Avinash1286/pendent/docs/a04/software-contract.md

# AURA A04 software and hardware contract

Status: **active engineering specification with a host-tested Opus/NAND journal/recovery path, C archive → desktop transcription → local portal path, and emulator-tested Android source storage, playback and scripted foreground recovery**. Updated 2026-09-09. The current A03 firmware and its published binaries are unchanged. This document does not establish a working A04 device, a deployed consumer mobile service, qualified battery behavior, or launch readiness.

The target remains a premium circular pendant that reliably captures, preserves, understands, retrieves and uses the context its owner chooses to record. Offline use, optional continuous sessions, real-time assistance, memory, tasks, speech, and broad AI interoperability remain in scope. They are not removed because the initial source is incomplete. “Best in the category” needs measured comparative evidence; it cannot be established by a feature list or source review.

## Evidence and implementation boundary

AURA baseline inspected: `e9e968c425c558565dc555ccd9f39d2e4c6c0769`. Omi source inspected: [`f42089f53c8010dd971b3702ece05a231c9c0c66`](https://github.com/BasedHardware/omi/tree/f42089f53c8010dd971b3702ece05a231c9c0c66). The prior [firmware/hardware review](../research/omi-review.md) and [product review](../research/omi-product-review.md) contain the specific upstream code paths and known limitations.

Three terms distinguish evidence throughout this contract:

- **Implemented** means code exists in this repository. It does not imply physical or deployed validation.
- **Host-tested** means an identified local test exercised a bounded software behavior.
- **Required** means work remains and the feature cannot be advertised as shipped.

Current implementation: [protocol_v2.py](../../companion/src/aura_companion/protocol_v2.py) now implements experimental wire revision 3, a bounded streaming archive reader, strict manifests/packets/terminal metadata, stable capture identity, replay, durable receiving and finalization. It is called by the new desktop `import-capture` CLI. It does not change A03 Bluetooth/v1 firmware. Actual C-encoded Opus fixtures pass the local archive/receipt/decode/transcription path and real local portal ingestion. Structural Opus profile validation is separate from actual decoder validation. No Omi implementation was copied into the receiver; the cited source informed the reliability contracts.

Firmware progress: [firmware/a04](../../firmware/a04/README.md) now connects a monitored PDM driver and bounded reader FIFO to one recorder/storage owner, unmodified libopus 1.6.1, the shared revision-3 archive, packed NAND journal and W25N01GV SPI adapter. [The audio contract](../../firmware/a04/AUDIO.md) defines driver-health faults, exact block/final-watermark checks, warmup, privacy ordering and DMA quarantine. Real 16 kHz mono, 32 kbps, 10/20 ms fixtures pass host and independent FFmpeg decode with exact duration.

Three separate DK targets have different evidence. The [synthetic integration
probe's current ELF report](../../firmware/a04/verification/arm-resources.json)
binds its exact memory, symbols and configuration; its RAM NAND and inactive
peripheral reservations are not a physical capture or Bluetooth workload. The
[wired bench](../../firmware/a04/bench/README.md) connects actual peripheral
drivers and UART export with Bluetooth disabled, with its own
[ARM resource report](../../firmware/a04/bench/verification/arm-resources.json).
The new [radio DK application](../../firmware/a04/radio/README.md) implements
the GATT adapter, local pairing policy and [ASC1 owner proof](session-auth-v1.md).
Its source and verification scope are independent of both earlier targets.
None has been flashed or executed on physical hardware. Final A04 pin mapping,
physical scheduling/audio/NAND/radio qualification, signed OTA and populated-block
reclamation remain required; a DK build is not the complete product memory budget.

Storage verification: **25 command/integration groups and 19 journal groups pass**, alongside the existing Python archive tests. [The command transcript](../../firmware/a04/verification/w25n-command-tests.txt) covers the actual command core, including two combined driver/journal cases; [journal roundtrip evidence](../../firmware/a04/verification/journal-roundtrip.json) binds real Opus → modeled power cut/reopen → AUR3 → durable Python/SQLite import and restart → independent FFmpeg decode. A finalized recording preserves 120847 source samples; staged/torn tails preserve 116440, and a completed page with lost acknowledgement recovers 120600. Interrupted original duration remains unknown. These are host-model results, not electrical NAND or assembled-device qualification.

Ingress verification adds **10 recorder groups, 10 audio-adapter groups and 20 monitored-driver groups**. Five real recorder exports pass SQLite restart/replay and FFmpeg decode, including a source fault combined with failed terminal storage. Deterministic adapter interleavings cover cancellation during startup, publication at the privacy boundary, FIFO overflow, final-block loss and refusal to recycle live DMA storage. [Recorder evidence](../../firmware/a04/verification/recorder-roundtrip.json), [adapter evidence](../../firmware/a04/verification/audio-host.json) and [driver evidence](../../firmware/a04/drivers/tests/verification.json) describe their separate mocked boundaries. They do not establish physical concurrency, timing or electrical privacy behavior.

The current companion suite passes **131 tests**, including 36 release/outbox tests and the earlier 95 importer/receiver cases. Real C-generated archives and an actual local Whisper result passed through the Python uploader, Next.js and local Convex. [The companion verification](../../companion/VERIFICATION.md) and [portal report](../../portal/verification/a04-provenance-local.json) identify their separate checkpoints, commands, immutable fixtures and limits. Cases exercise corrupt/conflicting data, process exit before COMMIT, replay, temporary/read-only storage rejection, interrupted publication repair and source preservation. This establishes a local software path with synthetic audio, not a physical or mobile A04 capture path. The older [47-test v2 report](protocol-v2-verification.txt) is retained as historical evidence.

The [serialized storage owner](../../firmware/a04/STORAGE.md) now integrates
[RLS1 authentication](../../firmware/a04/RELEASE-AUTH.md) and the
[control-snapshot ledger](../../firmware/a04/CONTROL-LEDGER.md). It reserves
generation-derived capture identities and persists exact release grants before
invoking a privileged erase callback. Real C audio traverses the Python durable
receiver/outbox and returns to that controller in modeled-NAND tests. Consumer
enrollment, authenticated transport completion, the physical audio-erase
capability and electrical power-loss qualification remain outstanding. Ordinary
download never grants erasure or changes ownership.

The current phone foundation is a [native Android local library](../../mobile/android/README.md)
with exercised import, private storage, platform Opus playback and explicit
context sharing. A portable [transfer command owner and Kotlin wire codec](transfer-wire-v1.md)
now add exact-record resume, immutable replies, generation-bound capture
selection and stale callback rejection above the bounded journal cursor. Twelve
C groups and **30 combined Kotlin groups / 82,213 checks** pass, including actual
C-generated reply/fragment comparisons and **six incremental-validator groups /
49,471 checks**. The complete-file and incremental paths use one canonical
validator, with **19 complete C-generated archives**, exact Python ACK3/Ogg
comparisons and independent FFmpeg sample-count checks.

Android's [durable download store](../../mobile/android/DOWNLOADS.md) now commits
exact source records and resume metadata in one SQLite transaction, replays
saved prefixes after reopening, and preserves conflicting or corrupt evidence.
Its `CaptureStore.importDownload` bridge exports the original archive and exact
physical receipt through the existing platform-decoder and private-bundle
publication path. The [foreground recovery coordinator](../../mobile/android/RECOVERY.md)
(`CaptureRecovery`) now joins catalog selection, exact resume, bounded retries,
cancellation and decoded-library publication. `AndroidGattConnection` implements
the Android transport beneath it, including subscription readiness, bounded
fragment handling and stale-callback rejection.

The current development APK passed **29 Android runtime cases / 428 assertions**
on an API 34 emulator using the actual `c2.android.opus.decoder`. These cases
exercise real SQLite rollback/replay and library publication, plus the recovery
coordinator over scripted logical replies from fixed C fixtures. They do not
establish a physical pendant-to-phone link. Separate virtual GATT runs passed four cases / 33 assertions at each of MTU 23 and 517 using a Python Bumble fixture, not Zephyr firmware or authenticated enrollment. The
Activity still exposes file import. The separate
[Zephyr radio DK adapter](../../firmware/a04/radio/README.md) is now implemented;
Android still needs its ASC1 proof exchange, trusted owner-context custody,
secure consumer enrollment and UI integration before accessing that target.
Physical phone power-loss durability and real radio behavior need separate
qualification. [Android verification](../../mobile/android/VERIFICATION.md) records
the current execution scope.

## Complete feature and evidence backlog

| Product capability | Current evidence | A04 required behavior and owner | Evidence required before launch |
|---|---|---|---|
| Immediate deliberate capture | A04 monitored ingress, bounded FIFO and recorder lifecycle implemented and host-tested; DK integration cross-built; A03 gesture remains the prior baseline | Pendant captures without a phone; tactile start/stop, unmistakable recording/saved/error indication | Actual button-to-first-usable-audio latency, startup syllable retention, walking and under-clothing recordings |
| Controlled continuous capture | Required | User-enabled session mode with explicit physical start, continuous visible indicator, clear pause/stop, storage limits and consent guidance | Measured long session with no unexplained gaps; privacy switch stops capture independently of app/MCU state |
| Offline capture | A04 packed NAND journal and W25N01GV command driver implemented; modeled program/erase cuts, full-media retention and real Opus recovery tested; Cortex-M4 cross-built | Transfer only verified committed prefixes; preserve unacknowledged recordings; recover interrupted captures and expose unassociated material | Physical NAND power cuts at every journal state and during erase; decodable audio with explicit interrupted-tail metadata; qualify capacity/reclamation policy |
| Real-time transcription and assistance | Required | Phone streams only device-committed frames; live text marked provisional; durable archive later reconciles gaps | Phone termination, BLE backpressure and network loss preserve source; latency and consistency measured on supported phones |
| Opus compression | Real libopus 1.6.1 wrapper host-tested with decodable 10/20 ms fixtures; isolated nRF52840 probe cross-built | 16 kHz mono, 32 kbps initial experiment; compare low-delay and speech-optimized modes against PCM reference before profile freeze | CPU deadline, stack high-water, heap, power, frame error, quality and transcription comparison under concurrent storage/BLE load |
| Multi-microphone audio | A04 stereo driver/adapter, first/second/mean selection, peak/clipping counters and explicit fault propagation host-tested; no physical audio qualification | Two appropriately spaced microphones; calibrated mono mix/selection; retain original capture format metadata | Channel polarity, phase, clipping, wind/clothing noise and speech intelligibility in the actual sealed case |
| Bookmarks | Revision-3 C bookmarks survive verified local import, notes and real portal ingestion; A03 v1 still cannot export marks | Pendant gesture creates a sample-offset event; phone/portal jump to corresponding transcript/audio | Capture + bookmark + reconnect + export + playback round trip on real firmware |
| Device identity | v1 filenames lack authenticated device identity; revision-3 archives and portal retain independent device/capture keys, but these are sender declarations | Stable private device identity plus persistent random capture identity; owner binding and physical re-pair/reset flow | Two devices, resets, reboots and credential rotations never merge captures; unauthorized identity claims rejected |
| Reliable reconnection | A04 bounded cursor, ordered C command owner and Kotlin reply/fragment parsers host-tested; Android recovery/GATT client and separate Zephyr radio DK adapter implemented with distinct verification boundaries | Integrate Android ASC1 proof, trusted owner-context custody, secure enrollment and consumer lifecycle/UI; qualify actual device-to-phone recovery and background behavior | iOS and Android foreground/background/process-death matrices, permissions off/on, bonds, out-of-range return |
| Transfer retention and ACK | v1 explicit CRC-verified deletion; revision-3 journal receipts, C/Python agreement, durable desktop batch import and Android SQLite download rollback/replay tested; physical OPEN remains distinct from an exported interrupted seal | End-to-end application receipt after durable publication, separate from RAM acceptance/BLE completion; authenticated acknowledged/deleted-segment reclaim | Kill receiver before/after commit, lose ACK, replay and verify exactly one source; physical MCU reclamation power-cut tests |
| Searchable notes | Next.js/Convex owner-scoped notes/search and retained original source exercised locally; newly arrived unknown-time captures remain visible | Capture time confidence, editable title, transcript, summary, tags, filters and source playback | Deployed authenticated account flow; source remains accessible through edit/search/archive/delete |
| Transcription and languages | Real C archive → desktop Whisper → local portal tested with synthetic English speech | Local/offline option plus explicit cloud choice; language detection/selection and accessible corrections | Representative accents/languages/noise, measured quality/cost/latency; disclosure when speaker attribution is uncertain |
| Speaker attribution | Required | Phone/backend diarization with user-correctable labels; never infer a person's identity from a voice without an explicit enrollment feature | Overlap, short utterances, new speakers, corrections and source alignment tests |
| Summaries and provenance | Real local C archive → Whisper → portal import now retains immutable capture/source transcript, segments and method metadata | Every derived claim/action links to source capture, transcript revision and sample/time span; retain original and corrections | Regeneration/correction invalidates stale context while retaining inspectable lineage |
| Long-term memory | Chosen notes/profile currently supply context | Explicit review/promotion, edit/retract, provenance and supersession; canonical owner-scoped source truth | No unreviewed memory promotion; revoked/deleted/superseded evidence excluded on next retrieval |
| Tasks and reminders | Draft action strings only | Proposed actions with source evidence, accept/edit/dismiss lifecycle; opt-in reminders and integrations | Retry extraction cannot duplicate accepted tasks; no external side effect before a recorded user choice |
| AI chat interoperability | Reviewed Context Packs and read-only MCP implemented; local verification exists | Searchable owner-approved context for ChatGPT, Claude, Gemini, Grok and compatible clients; clipboard/file fallback remains usable | Actual supported-client connection matrix; current consent enforced; no claim every vendor accepts the same deep link/MCP method |
| Voice interaction/playback | Required | Phone/earbud microphone and speaker provide query/response/playback initially; pendant gesture may trigger the paired client | Clearly identify audio route; disconnected earbuds/phone cannot create an apparent pendant playback failure |
| Ecosystem/SDK | Python v1 companion and revision-3 archive importer implemented; real C/Python fixtures | Documented versioned device SDK, export formats and import contracts; adapters for integrations without a second source of truth | Contract fixtures across firmware/mobile/desktop; compatibility, migration and permission tests |
| Battery and storage UX | Raw voltage/free bytes available; charging/haptics disabled in release | Calibrated state, low-space/low-battery warnings, last successful save/sync, bounded maintenance and explicit fault handling | Full charge/discharge curves, worn/runtime profile, near-full capture and restart, charger/NTC faults |
| Secure update/recovery | Required; A03 is a single application slot | Signed boot, rollback-capable update, image compatibility, physical recovery and anti-rollback policy | Wrong board/key/image rejected; power cuts throughout update recover; key management documented |
| Privacy and account lifecycle | Hardware disconnect design, encrypted BLE, scoped portal tokens implemented | Hardware privacy proof, authenticated ownership, protected recordings, credential rotation/revocation, account recovery/export/deletion | Lost device/phone, stale cache, revoked token, deletion and restoration tests; no transcript/secret diagnostic leakage |
| Comfort and launch assets | A03 models/video exist; A04 redesign in progress | All PCB, case, firmware, website, video, specs and assembly guides refer to one verified A04 configuration | Render/model/part manifests match released PCB/BOM and physically measured first article; no A03 images labelled A04 |

Speech synthesis, LLM inference, semantic search and task execution belong on the phone/backend. Audio playback belongs on the paired phone/earbuds unless a separately reviewed speaker is added. The A04 hardware contract currently contains no speaker, display, camera, cellular or standalone Wi-Fi feature. None should be implied by a render, voice-over or generic comparison with Omi. Controlled continuous capture and near-real-time transfer remain pendant firmware requirements, not phone-only substitutes.

## Omi engineering practices to adopt

1. **One capture truth and one recovery owner.** Omi's [product principles](https://github.com/BasedHardware/omi/blob/f42089f53c8010dd971b3702ece05a231c9c0c66/PRODUCT.md) prioritize reliable capture/sync/retrieval. Its [transfer coordinator](https://github.com/BasedHardware/omi/blob/f42089f53c8010dd971b3702ece05a231c9c0c66/app/lib/services/wals/recording_transfer_coordinator.dart) is a useful reference for coalesced recovery. AURA's [foreground coordinator](../../mobile/android/RECOVERY.md) now serializes recovery and distinguishes received bytes, committed source, processing and a playable library item. Its Android GATT client and durable store still need the ASC1 exchange, trusted context/enrollment and consumer UI wiring to access the implemented radio DK service. Recording → preserved on pendant → preserved on phone → processing → note ready remains the full product lifecycle; connection alone proves none of these.
2. **Contracts plus real failure harnesses.** Preserve bounded regression cases: process exit before/after commit, full storage, dropped notifications, permissions, background restrictions, stale retrieval consent, and interrupted update. Generated checks must actually exercise the shared implementation and run locally/Vercel as applicable; no GitHub Actions.
3. **Compression selected by measurement.** Omi's [dev-kit codec](https://github.com/BasedHardware/omi/blob/f42089f53c8010dd971b3702ece05a231c9c0c66/omi/firmware/devkit/src/codec.c) reserves a 32,000-byte encoder stack and codec state. Its [configuration](https://github.com/BasedHardware/omi/blob/f42089f53c8010dd971b3702ece05a231c9c0c66/omi/firmware/devkit/src/config.h) selects 160-sample, 32 kbps frames. AURA should port the approach with resource accounting; do not copy a static codec-state size without confirming the selected build's `opus_encoder_get_size()`.
4. **Source-backed, revocable memory.** Omi's memory model and access gateway inspire provenance, revisions and fresh policy checks. AURA's canonical record is the owner-scoped capture/transcript and its reviewed derivatives. Search/vector indexes are derived candidates and must be rehydrated against current ownership/consent/revision/deletion.
5. **Repair known weak paths.** Omi's reviewed consumer transport can dequeue without storing in particular connected/unsubscribed or failed-send paths, and notification completion is weaker than durable phone storage. AURA must keep local-first capture and explicit host receipts. Do not adopt automatic loss of unsynced audio, credential-bearing diagnostic logs, or delete-before-rename file publication. See the [bounded source findings](../research/omi-review.md#firmware-findings-worth-learning-from).

These are designs derived from the reviewed source. Omi's documented “locked” contracts are not by themselves proof of deployed correctness, and its consumer nRF5340 firmware is not a compatible nRF52840 binary.

## Hardware decisions required before pin/placement freeze

| Interface/resource | A04 requirement | Reason and remaining verification |
|---|---|---|
| MCU/module | Retain Raytac MDBT50Q nRF52840 family unless root hardware review changes the exact part | A03 software baseline and Omi dev-kit codec experience are relevant; actual codec + security image fit remains required |
| PDM | Shared CLK and DIN for opposite-clock-edge stereo microphones; software rail enable; independent physical rail disconnect and sensed switch position | A03 uses two PDM edges on one DIN, not two independent DIN pins. Check new microphone startup, voltage, clock/rate and physical acoustic ports |
| Audio flash | W25N01GV packed journal and caller-configured Zephyr SPI adapter implemented and host-tested; physical bus/latency qualification required | Metadata-only mount avoids a full audio-volume scan; validate actual program/erase/read timing, serialized cache access and concurrent PDM/transfer scheduling. No populated reclamation exists yet |
| Update staging | Captured U10: **MX25R3235FM1IL0, 32 Mbit / 4 MiB serial NOR**, reserved for MCUboot secondary image/metadata | Current custom NAND driver is not assumed available in the bootloader. Confirm the selected NOR's driver, voltage, JEDEC/SFDP behavior and boot-time pins on the actual board |
| Flash map | MCUboot, primary image/trailer, persistent owner/identity/settings; secondary NOR/trailer; build-time slot limits | Choose MCUboot swap/update strategy and sector compatibility explicitly. Do not publish a partition map before building the real codec/security image |
| Shared I²C | Gauge, haptic and selected charger; distinct compatible addresses/levels and pull-up budget | Check exact chosen charger interface and reset defaults; no firmware-only reliance for battery thermal protection |
| Control GPIO | Capture, physical privacy position, microphone enable, default-inactive charging and haptic enable; optional charger fault/IRQ if selected | Boot, watchdog reset, transport command or crashed phone cannot enable capture against physical privacy or unsafe charging |
| Indication | Hardware-coupled recording/privacy indication plus firmware status; tactile haptic if qualified | Visible recording indication cannot depend solely on a responsive app; haptic meaning must not imply data committed before it is |
| Service/test | Accessible SWDIO/SWCLK/RESET/GND/VTref and testable rails/storage buses | Factory identity/provisioning, signed recovery, measured power, programming and first-article fault isolation |
| RF/clock | Antenna all-layer/case/metal keepout; selected clock accuracy and calibration | Phone compatibility, BLE interval/PHY choices, body/chain effects and idle power must be measured |

The [MCUboot design](https://docs.mcuboot.com/design.html) documents distinct bootloader/primary/secondary flash areas and strategy-dependent sector/trailer requirements. This requires a real A04 flash map and power-interruption test, not just adding “OTA” to firmware configuration. Inference for AURA: a known NOR driver is a lower-integration-risk staging path than introducing the custom NAND journal driver into the bootloader. It is still unqualified until built and tested.

No pin numbers are assigned here: the fresh KiCad MCP schematic is the authority. Export its mapping into the A04 devicetree, production test plan and wiring guide, then run a cross-check against that exact schematic/BOM revision. Do not reuse A03 GPIO assignments merely because they compile.

## Experimental archive revision 3 and the real local import path

The original experimental v2 format lacked immutable Opus profile/pre-skip and complete end-trim semantics. It has been superseded by **binary wire revision 3** (`AUR3` manifest, `AFR3` packets, `ASE3` terminal metadata, `ACK3` receipts). The Python module remains named `protocol_v2.py` for development continuity, but old v2 bytes are deliberately rejected rather than reinterpreted. A03 Bluetooth/v1 bytes and firmware remain unchanged. The portal's `capture.version: 2` describes its JSON metadata contract, not this binary revision.

The authoritative field layouts and C/Python behavior are documented in [the archive specification](../../firmware/a04/ARCHIVE.md). Immutable device/capture identities, the negotiated codec profile, packet sequence and sample offsets, CRC-protected records and a SHA-256 chain lead to terminal metadata that binds the true source duration, Opus pre-skip/end-trim and finalized/interrupted status. A terminal receipt includes that metadata in its digest. Hashes and sender-declared device IDs are not physical-device authentication.

The journal uses separately named staged codec/archive initializers: callback success means bounded RAM acceptance, and a staged writer cannot issue a receipt. It replays each accepted record independently of the producer callback, then advances its committed snapshot only after completed programming, full ECC-readable exact page readback and CRC validation. Records share 2048-byte pages and never cross a page boundary. Flushes occur on capacity, first audio, terminal seal, explicit request and the serviced 400 ms deadline; the scheduler must initialize and service that monotonic clock while recording and paused. A failed or uncertain page is never reprogrammed. Program-failure status cannot be hidden by matching bytes; unresolved pages are blocked from read-based promotion for that boot.

Mount reads bounded header/checkpoint metadata: an empty 1024-block host-model mount reads **524288 bytes in 2048 metadata reads, with zero payload reads**, excluding the adapter's separate factory-marker/LUT inventory. Old captures remain unverified until a full payload scan before receipt/export. Recovery inspects later pages, continuation declarations and checkpoints after a gap; contradictory later material is corruption. Identifiable damaged continuations invalidate the capture; unidentifiable material remains quarantined and counted. An exported interrupted seal does not become a physical local terminal receipt or deletion authority. A new boot uses a fresh capture ID/block rather than restarting an Opus encoder inside an old capture.

The bounded port supports **128 captures**, never erases populated or unidentifiable source blocks, and stops recording when full while retaining verified receipts/export for synchronization. Closing a minimal capture strands 58 unused data pages in its final block; across 128 such captures those tails total **14.5 MiB**, and the catalog fills after consuming 16 MiB of blocks even if other blocks remain. There is no populated reclamation, catalog eviction, authenticated persistent host-ACK reclamation, or persistent failed-page retirement ledger. Blank candidates require complete readable-FF checks and a successful fresh erase. Failure guards are volatile; cold recovery validates old bytes but never resumes a pre-boot used block. Physical qualification, sustainable reclamation/rotation and unassociated-material recovery remain full-product work, as quantified in [the journal specification](../../firmware/a04/NAND-JOURNAL.md).

Real C-generated Opus archives now enter `aura import-capture`: the companion takes a bounded local snapshot, verifies the full archive, commits packets/terminal metadata to SQLite, exports Ogg Opus and exact-duration PCM WAV, and publishes source metadata last. A terminal-revision digest names each bundle. Interrupted recovery requires the explicit `--allow-interrupted` flag; it retains only complete verified records, marks the original total duration unknown, and labels bookmarks whose corresponding audio was lost in the encoder tail. A later completed source is preserved as a separate revision instead of overwriting that recovered prefix.

Desktop batch file import validates and commits the complete capture in one SQLite transaction, returning its receipt only after commit. This avoids the old per-packet quadratic scans for this import path. The Python live per-packet receive API still revalidates the complete prefix and is not a production-throughput claim. Durability depends on the operating system, filesystem and storage honoring flushes; desktop transaction tests do not prove physical NAND persistence, phone power loss, BLE transport or background mobile service. The separate journal/command tests establish the bounded modeled storage behavior described above.

The separate [Android download path](../../mobile/android/DOWNLOADS.md) incrementally
validates chunks of at most 256 bytes, retaining only an incomplete record of at
most 1301 bytes. Exact complete records and their receipt/offset commit together;
partial bytes stay in RAM. A storage or validation failure faults the session,
and reopening revalidates the saved rows once before resuming. A seal alone does
not complete a download: all selected bytes must be committed and the exact
selected FINISH identity must match. The completed source can then enter the
existing playback library through actual Opus decoding. The foreground coordinator
now drives this path with exact source pinning across reconnects, an explicit EOF
READ before FINISH and bounded retry/cancellation. Android emulator tests exercise
these boundaries with scripted connections. The Android GATT client and separate
radio DK adapter are implemented; the Android ASC1 exchange, trusted owner-context
custody, secure enrollment, consumer UI integration, physical durability and
background lifecycle qualification remain separate work. See the
[recovery contract](../../mobile/android/RECOVERY.md).

A committed bundle is reused by checking its preserved archive, receipt, WAV hash/dimensions and source metadata; it is not decoded again just because a newer decoder is installed. New exports record PyAV and codec-library versions. Conflicting files are preserved and rejected. Missing final metadata after interrupted publication can be reconstructed by a verified reimport. A cooperative OS lock serializes imports into one output directory. Raw audio/archive/receipt files remain local unless the owner separately copies them.

Optional local transcription preserves exact source identity, capture-time confidence, retained sample duration, bookmarks, model/method/version, transcript segments and a hash of the transcript's exact UTF-8 bytes. A differing previous note JSON is archived before the current note view is replaced. Explicit portal upload preserves these fields. The portal authenticates ownership through the ingestion credential, deduplicates that owner's device/capture identity across token rotation, and rejects conflicting immutable source replay; it does not silently merge legacy token-prefixed captures or automatically promote a later final revision over an uploaded interrupted prefix.

**A receipt is not a DELETE command.** No radio command, device deletion, automatic upload, background retry or storage reclamation is performed by file import. Authenticated pairing, confidential storage, physical PDM input and NAND qualification, persistent ACK/reclamation, device BLE integration/credits and read-while-capture scheduling, qualified hardware-to-phone recovery, source-revision promotion and signed OTA remain required. The full objective is unchanged.

## Memory, tasks and interoperability contract

The existing Convex schema stores notes with owner, title, transcript, summary, actions, tags, recorded time and context consent. A04 needs stable `captureKey`, immutable source revision, time confidence, transcript segments, model/method/version, correction history and source spans on every derived suggestion. New capture ingestion separates authentication tokens from stable owner-scoped device/capture identity. Legacy v1 token-prefixed records remain unchanged and are not automatically merged because they lack sufficient source identity. Immutable original transcript and source metadata survive edits/retries; conflicting source revisions require an explicit future review/promotion path. See [portal provenance](portal-provenance.md) for validation, compatibility and tested limits.

A retrieval request must hydrate candidates from current authoritative records and enforce owner, consent, archive/deletion and revision state before returning text. Context search includes explicit pagination/truncation information and source links; “20 recent notes” must not masquerade as complete archive retrieval. A model reads captured text as data, never as authorization to call tools or change privacy. Accepted tasks have a user decision record and source span; extraction retries do not create another accepted task. Retraction prevents future retrieval, but cannot recall a context pack already pasted into a third-party chat.

External interfaces remain layered: clipboard/Markdown/JSON export for any chat, authenticated read-only MCP where the client supports it, and explicit user-authorized adapters for richer integrations. A “connect to ChatGPT/Claude/Gemini/Grok” button needs a tested supported method and honest fallback; an unverified vendor deep link is not interoperability. Credentials stay in secure client/transport configuration, not model-visible tool arguments or diagnostics. No upstream backend or production account is required to use AURA's independent Convex service.

## Release gates and execution order

1. **Hardware contract:** exact KiCad MCP schematic/BOM/net/pin mapping, charger/dock/NTC choices, module/antenna keepout, serial NOR staging and assembly tolerances agreed by actual artifacts. Root owns these files.
2. **A04 firmware bring-up:** new board target from the schematic, rails/storage/PDM/controls, truthful status, flash partitions, safe defaults and actual ARM build. A03 artifacts retain their identity. No charging or haptic qualification flag is enabled from a software test alone.
3. **Codec, archive and storage:** shared revision-3 C/Python source, real Opus fixtures, packed NAND journal, W25N01GV command/SPI adapter and modeled recovery tests now exist and cross-build together. Remaining work includes physical timing/stack and electrical power cuts, representative listening/transcription comparisons, sustainable reclamation/capture rotation, recovery of unassociated material and concurrent PDM/capture/transfer integration.
4. **Mobile loop:** durable Android source/receipt storage, exact prefix replay and decoded-library handoff are implemented and emulator-tested. The foreground recovery coordinator, Android GATT client and separate radio DK adapter have distinct source/test evidence. Integrate Android ASC1 proof, trusted owner-context custody, secure consumer enrollment and lifecycle/UI; verify the real microphone/NAND-to-phone path, then qualify actual OS background behavior and any acknowledged outbox. Timestamped transcript and bookmark navigation remain required. A timer is not proof of background execution. [Current recovery scope](../../mobile/android/RECOVERY.md), [execution evidence](../../mobile/android/VERIFICATION.md).
5. **Portal/AI:** deployed Convex auth/recovery/deletion, immutable provenance, stable ingestion identity across token rotation, searchable current-consent context, reviewed tasks and tested client adapters. Required account/terms steps cannot be replaced by a local mock.
6. **Security and updates:** authenticated ownership, protected storage, production signing/debug policy, rollback and update fault tests; export/delete/revoke/lost-device flows.
7. **Physical qualification:** assembled A04 plus exact printed case/dock, real battery/charge thermal faults, power/audio/RF/comfort/runtime testing and documented first wear. CAD topology and zero ERC/DRC do not prove these.
8. **Launch consistency:** all downloadable fabrication/print/firmware files, website/portal/video/readme, license notices, versions and documented claims match that qualified unit. Publish all work on GitHub and deploy website services with Vercel. No GitHub Actions.

The acceptance artifact is a requirement-to-evidence matrix with links to actual outputs, exact revision/hash, fixture or physical configuration, result and remaining limits. A green host test, generated manifest or product render must never stand in for an unperformed physical, mobile, cloud or security gate. The active goal remains unfinished until the full requested end state is true and verified.
