Avinash1286/pendent/firmware/a04/W25N-ADAPTER.md

# W25N01GV command driver and Zephyr adapter

Status: **experimental A04 implementation; command-model tested and Cortex-M4 cross-built; no physical flash, SPI, timing or power-fault qualification**. The real command core is separate from the journal's sparse NAND model. A03 firmware and released images are unchanged. The final resource and source-hash reports must match the exact code revision being inspected.

The portable [driver](src/aura_w25n01gv.c) uses an injected synchronous command transport and clock. [The Zephyr wrapper](src/aura_w25n01gv_zephyr.c) supplies actual `spi_transceive_dt`/`spi_write_dt`, a monotonic clock and sleeping. A mutex covers each complete NAND read/program/erase/bad-query operation, including cache load and readback. Serializing individual SPI transfers alone would allow another caller to replace the chip's shared page cache.

The caller supplies a reviewed `spi_dt_spec` to `aura_w25n01gv_zephyr_init`; no GPIO or devicetree node is selected implicitly. Accepted operation is standard full-duplex, 8-bit MSB-first, active-low CS, mode0 or3, up to32 MHz. Hold-CS, locked-CS, LSB, slave, half-duplex and extended line modes are rejected. Actual supported board speed remains a signal-integrity measurement, not a result of this argument check. The wrapper is for a storage thread, never an ISR. Its SPI transport must have a bounded hardware timeout; the ready polling bound cannot interrupt a driver stalled inside a synchronous transfer.

## Initialization and ownership

Initialize only at cold startup after power is stable and no live operation is running: initialization issues RESET. It must not be used as a retry while another task is recording. The driver checks JEDEC identity, buffer/ECC configuration and volatile protection readback. Unexpected OTP/protection-lock state is refused; the driver never issues OTP programming or the BBM mutation command.

Before permitting any array write, initialization reads the20-entry BBM LUT and reserves both addresses of each enabled valid or invalidated link. Malformed/unsupported entries fail initialization. It checks main byte0 and spare bytes2048/2049 on both reserved marker pages of each remaining block, with ECC disabled. Read failures leave the adapter unavailable. It then restores buffer mode/internal ECC and verifies volatile unprotection. This preserves the manufacturer markers and avoids aliasing an existing remapped address. The second marker page is an additional conservative reservation.

Command selection, status bits, dummy clocks, factory markers and sequential programming follow the [Winbond Rev.R manufacturer datasheet](https://www.mouser.com/datasheet/2/949/Winbond_Electronics_09072023_W25N01GV_Rev_R_070323-3313374.pdf), especially sections7.2–7.3,8.2 and10. The implementation deliberately supports less than the chip's permitted partial-program behavior.

## Irreversible-operation boundaries

- **Read:** wait for ready, load one page, inspect its ECC status, then read the requested main-area bytes. Corrected data has a distinct result and telemetry; uncorrectable data is refused. Array addresses and columns are bounded.
- **Program:** only pages2–63 of a block successfully erased by this adapter in the current boot are eligible. Pages must increase and each attempt consumes permission. All-FF input is rejected because A04 pages contain a header and pre-existing FF cannot prove that an uncertain program occurred. The driver checks an ECC-clean FF destination, WEL, load/execute completion, P-FAIL, cleared WEL and full-page ECC/readback. A lost execute response can resolve successfully only through those checks, without a second execute. An unresolved completion returns `AURA_NAND_UNCERTAIN`; a failed or uncertain page is also blocked from read-based promotion through this instance, while its prior pages remain readable. Matching bytes with P-FAIL set never count as a successful commit.
- **Ordinary erase:** only a factory/LUT-eligible block outside the reserved CONTROL pair whose entire main area is readable, ECC-clean and FF can be erased. Any populated, corrected, unreadable or hidden later page prevents the command. E-FAIL, cleared WEL and all 64 post-erase pages are checked before program permission is granted. A lost command acknowledgement remains uncertain: pre-existing FF alone cannot prove that a fresh erase actually happened. Erase faults retire write permission for the current instance. This interface has **no populated audio-block reclamation**; it cannot be used as an implicit delete or garbage collector.

No prior-boot write permission survives initialization. A failed operation disarms writing without mislabelling the block as factory bad, allowing the journal to preserve and investigate its existing source. The journal remains responsible for capture identity, page CRC/hash validation, its committed watermark and recovery semantics. The adapter cannot itself issue an application receipt.

The per-block failure guard is **volatile**. Persistent runtime bad-block retirement and verified migration have not been implemented. A later cold-recovery session may inspect a previously failed page through full source/ECC validation; that does not restore permission to append to an old capture or prove permanent reliability of that block. This limitation must be resolved before dependable daily wear.

## Explicit CONTROL pair

The command core now exposes a separate `aura_control_io` for exactly two explicitly reserved blocks. After successful cold initialization, call `aura_w25n01gv_configure_control(device, first, second)` before the first ordinary NAND callback, then obtain `aura_w25n01gv_control_io(device)`. The Zephyr equivalents are `aura_w25n01gv_zephyr_configure_control` and `aura_w25n01gv_zephyr_control_io`; configuration and all callbacks use the same complete-operation mutex as ordinary NAND access. Neither API selects blocks, discovers a layout, provisions a ledger, nor issues an erase during configuration.

The caller must supply a trusted, fixed layout and keep the device/configuration private to its serialized storage owner. Both blocks must be distinct, in range and factory-marker/LUT eligible. The ordered pair is immutable until the next deliberate cold initialization; repeating that exact pair is a no-op. Without a configured pair, the control view reports zero blocks and its callbacks deny access. Any valid ordinary callback locks an unconfigured layout against later reservation, including read and bad-block queries, so a mounted journal cannot have its inventory silently reclassified. Reapply the trusted pair before journal mount on every cold startup.

Ordinary `aura_nand_io` reports the reserved pair as excluded and refuses its read, program and erase requests, including through handles obtained before configuration. The dedicated control view reports every other block unavailable and independently rejects reads, programs and privileged erases outside the current pair. Its `nand.erase` pointer is null. The separate `erase_control` callback may erase a populated **CONTROL** slot; it does not authorize any populated audio-block erase. The ledger is responsible for selecting the inactive slot and verifying snapshot linkage. Possessing this callback is a software privilege: there is no defense against arbitrary mutation of the private driver object or direct raw-bus access.

Control erase uses the same ready polling, write-enable check, execute/status result, cleared WEL, E-FAIL handling and full 64-page ECC-clean FF readback as ordinary erase. It skips only the ordinary precondition that all source main bytes already be FF, and only after its own pair check. A reported failure or lost erase acknowledgement never becomes success merely because the block reads FF. No failed-page guard is cleared by this path; a retired block remains unwritable until separately initiated cold recovery. A successful fresh erase permits only increasing, once-attempted pages 2–63. Both interfaces retain the same full-page program readback, P-FAIL and uncertain-page protection. Neither writes factory-marker pages, spare data, OTP or the BBM LUT. Reserved factory-good marker bytes remain FF through control erase.

The command tests combine the actual control ledger and journal with this driver: provision and cycle control snapshots through generations 1–4, recover after cold initialization and explicit reconfiguration, and verify an ordinary capture's unchanged receipt. They also reject a missing/invalid/excluded pair, late or changed configuration, wrong-target callbacks, eight erase failure modes, and a P-FAIL header whose bytes match the requested data. These are source and command-model checks, with no physical commands or flash qualification.

Ready polling has a30 ms monotonic deadline and301-poll fallback. These are software bounds around a responding transport, not measured bus or startup latency. Initialization reads only marker locations; the journal separately reads its bounded metadata inventory. Neither should be described as a full128 MiB boot scan.

## Verification and limits

[The command-level host test](tests/host_w25n01gv.c) compiles the **production command core**, without an alternate implementation, against a chip command model. Its 25 groups check transaction boundaries, headers/dummy clocks, write-enable ordering, reserved-page and address rules, and reject unexpected opcodes. Cases cover factory markers, LUT aliases and invalid entries, wrong identity/lock/configuration, cache/readback, restart/no-resume, ECC statuses, lost completion, program/erase faults, silently ignored erase, non-FF tail pages, refused WEL, busy timeout and stalled clock. Two original groups combine the actual driver and journal to check staging/receipts/cold verification and prevent a P-FAIL page with matching bytes from advancing the committed snapshot; five additional groups cover the separate CONTROL pair described above. Those integration packets are protocol fixtures; the separate real-Opus journal roundtrip establishes decode behavior. The command model implements neither physical ECC encoding nor analogue corruption probabilities.

Run the integrated A04 host build:

```powershell
./firmware/a04/scripts/build.ps1 -Mode host
```

The integrated raw result is retained in [command-test evidence](verification/w25n-command-tests.txt). The empty-chip model startup performs 12306 command transactions, receives 12383 bytes and loads 2048 marker pages; it does not scan audio. The CONTROL pair adds two block indices and lifecycle flags within existing host padding: the standalone command test still reports a 4432-byte portable context. Exact target sizes and linked wrapper coverage require the corresponding current target build report. These are measured software/model counts, not physical startup timing. The probe must not initialize a physical chip until reviewed A04 pins and hardware exist.

Remaining qualification: actual CS/DMA and shared-bus behavior, measured ready/startup/service latency, power interruption during every irreversible phase, real ECC/bad-block behavior, thread scheduling under PDM/BLE load, energy usage, and full capture→durable NAND→verified receiver recovery. No GPIO execution, physical flash test or wearable approval follows from these host checks.
