Avinash1286/pendent/film/aura-launch/frame.md

---
name: AURA — Capture the context of your life.
version: 5
format: 1920x1080
colors:
  graphite: "#101112"
  surface: "#1D1E20"
  ivory: "#F4F1EB"
  secondary: "#B7B4AF"
  apricot: "#EEB891"
typography:
  display: "Manrope"
  body: "Manrope"
  displayWeight: 500
  bodyWeight: 400
---

The A03 capsule is the center of the story: glossy black full-face record paddle, satin silver frame, and fine necklace chain. Use actual Blender geometry, broad photographic lighting, and breathing room. Start with the low-angle profile before revealing the name. Warm ivory headline text stays crisp against graphite; apricot is reserved for a recording moment and a short line. Never use multicolor gradients, fake review stars, invented benchmarks, or crowded feature cards.

The emotional arc is life in motion → what matters → thoughts and moments → personal choice → new possibilities. The exact primary line is “Capture the context of your life.” Keep manual capture and physical privacy clear. Context comes from the moments a person chooses to keep.

At 1920×1080 use 77–158 px display type, 28–43 px supporting type, and 20–23 px labels. Keep type within a 120 px safe area. Product photographs can run past the image boundary intentionally while text remains entirely legible. The closing chain fades before reaching the tagline.

Motion is slow, deliberate, and finite: 2.5–5.5% photographic reframes with continuous movement. Entrance type resolves with cubic ease-out. The final lockup is fully resolved by 39.35 seconds and holds until 44 seconds. No endless ambient loops, bounce, or gratuitous transitions.

The inside view uses actual geometry, opaque materials, an angled camera, broad reflected light, and a graphite stage. Keep the board and cell distinct. Separate five groups along the object's thickness axis, pause, then return to exact assembled positions. Use one small headline and a development qualifier; no floating labels, ghosted shells, or invented parts.

The headline tracking reveal adapts the installed Hyperframes `tracking-in` primitive. The final wordmark settlement and line drawing adapt the installed `titlecard-lockup` primitive. Composition otherwise follows the project's own visual hierarchy.
