Avinash1286/pendent/film/aura-launch/STORYBOARD.md

# AURA — Capture the context of your life.

44 seconds · 1920 × 1080 · 30 fps · original stereo score · no narration

Life keeps moving; some thoughts and moments deserve a place to stay. The film introduces AURA as a way to keep what matters, then connects personal control with the possibilities of useful context. The existing A03 product photography, quiet score, measured motion, and long final beauty hold support the more personal story.

| Time | Picture and movement | Message |
| --- | --- | --- |
| 0–5.8 | The actual A03 profile emerges gradually with a 2.5% optical reframe. The first two seconds belong to the object. | “Life moves.” at 2.1 s. |
| 5.2–11.2 | Dissolve to the complete capsule and chain. A 5.5% constant-speed withdrawal gives the object breathing room. | “Introducing AURA.” Then “Keep what matters.” A small development-concept label establishes the stage. |
| 10.6–16.4 | A precise cut reveals the full glossy recording face, followed by a 4.5% push. A short finite waveform illustrates the intended feedback. | “The thought. The moment.” Supporting copy: “Press to capture · Intended interaction.” |
| 15.8–21.6 | Actual microphone-disconnect macro. A small lateral move describes the satin frame and physical control. | “On your terms.” “Physical mic disconnect.” “You decide when to capture.” |
| 21–29.6 | The real A03 GLB opens along its thickness axis into five opaque groups: face/controls, frame, board, battery, and back. A gentle camera orbit exposes the board and cell. The separated view holds before the layers return to their exact original positions. | “Considered. Inside and out.” Small label: “Exploded design study · Reference components shown.” |
| 29–35.4 | One ivory notes surface. A morning walk becomes an idea and a next step, in an explicitly illustrative interface. | “More context. New possibilities.” “Capture offline. Organize with your phone.” |
| 34.8–44 | Dissolve to the complete object and brand. The product settles by 38.4 s; all copy resolves by 39.35 s. The finished picture holds to the last frame. | “AURA. Capture the context of your life.” Supporting copy: “Capture starts with you.” The engineering-validation qualifier remains visible. |

The seven shots combine the final A03 Blender photographs with the actual exported GLB. Hero aliases have identical source pixels; separate filenames keep Hyperframes media discovery unambiguous. One paused GSAP timeline owns the edit. The Three.js layer responds to timeline updates and Hyperframes seek events, reconstructing camera and component positions directly from the requested time. It does not use wall-clock time, free-running loops, input, or remote assets.

Assembly poses: assembled at 21.7 s; open by 23.75 s; angled interior hold until 26.15 s; reassembled by 28.1 s; hold to the transition. The same part-name rules and separation factors as the website's assembly explorer are used. The animation is an exploded design study, not a manufacturing procedure or proof of production tolerances.

The original ambient score uses locally synthesized harmonics, sparse bells, and controlled delay. Its harmonic sequence was extended to 44 seconds for the new inside view; the opening and sonic character remain. Picture and music resolve together, without narration or licensed stock footage. The film makes no numerical thickness, capacity, battery-life, reliability, stock, or shipping claims.

The primary line refers to moments the user chooses to capture. Manual capture and the physical mic disconnect remain explicit; the film does not imply always-on recording, complete life capture, or perfect memory.

The complete original A01 film is preserved in `../archive/A01`. The unreleased A02 source draft is preserved in `../archive/A02-draft`; no A02 video was rendered.

The preceding A03 film and source are preserved in Git commit `1569645a292b8bd147bb208ccc96d9fe8081adc5`. This positioning revision creates no additional media archive.
