Avinash1286/pendent/docs/research/aura-first-wearable.md

# AURA: the route from Omi's lessons to a first wearable

**The next meaningful milestone is a real spoken note recorded on hardware, recovered after a disconnect, and played back from a durable local copy.** AURA's software foundation has progressed; its custom PCB and powered enclosure are not ready to fabricate and wear.

This plan reviews [Omi at `f42089f53c8010dd971b3702ece05a231c9c0c66`](https://github.com/BasedHardware/omi/tree/f42089f53c8010dd971b3702ece05a231c9c0c66), with AURA's published `0f22273` checkpoint and subsequent storage-controller work distinguished below. It is a source/design review, with no upstream application execution, physical board fabrication or wear trial. The detailed [code review](omi-review.md), [mobile/product review](omi-product-review.md) and [hardware review](omi-hardware-review.md) retain the underlying evidence.

## What to take from Omi

| Lesson from the pinned source | AURA decision and current state |
|---|---|
| Omi prioritizes capture, preservation and retrieval, with reliability ahead of visual novelty. [Product principles](https://github.com/BasedHardware/omi/blob/f42089f53c8010dd971b3702ece05a231c9c0c66/PRODUCT.md#L8-L24), [design guidance](https://github.com/BasedHardware/omi/blob/f42089f53c8010dd971b3702ece05a231c9c0c66/.impeccable.md) | Keep one deliberate capture gesture, visible microphone state and physical privacy control. A premium finish should support a dependable daily ritual. These are A04 requirements; actual control force, indication and comfort are unmeasured. |
| The phone distinguishes download, internet wait, upload and processing, and has a coordinator for recovery. [Sync model](https://github.com/BasedHardware/omi/blob/f42089f53c8010dd971b3702ece05a231c9c0c66/app/lib/models/sync_state.dart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), [coordinator](https://github.com/BasedHardware/omi/blob/f42089f53c8010dd971b3702ece05a231c9c0c66/app/lib/services/wals/recording_transfer_coordinator.dart) | AURA now implements one foreground recovery owner, durable phone storage and an Android GATT client. Received bytes, preserved source, processing and playable audio have distinct states. The matching radio DK adapter now exists; secure enrollment, the Android ASC1 proof exchange, consumer UI integration and a real hardware-to-phone recovery trial remain. |
| The dev kit uses Opus, while consumer firmware targets a different MCU. [Dev-kit configuration](https://github.com/BasedHardware/omi/blob/f42089f53c8010dd971b3702ece05a231c9c0c66/omi/firmware/devkit/src/config.h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), [consumer target](https://github.com/BasedHardware/omi/blob/f42089f53c8010dd971b3702ece05a231c9c0c66/omi/firmware/omi/README.md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) | Retain AURA's measured-memory Opus port and nRF52840 direction. Run the complete recording workload on hardware next. Omi's nRF5340 consumer binary and XIAO dev-kit wiring are not AURA firmware or pin maps. |
| Selected consumer paths dequeue audio without successful delivery/storage; storage advancement uses notification completion. [Pusher](https://github.com/BasedHardware/omi/blob/f42089f53c8010dd971b3702ece05a231c9c0c66/omi/firmware/omi/src/lib/core/transport.c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), [notification callback](https://github.com/BasedHardware/omi/blob/f42089f53c8010dd971b3702ece05a231c9c0c66/omi/firmware/omi/src/lib/core/storage.c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), [pointer advancement](https://github.com/BasedHardware/omi/blob/f42089f53c8010dd971b3702ece05a231c9c0c66/omi/firmware/omi/src/lib/core/storage.c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) | Preserve local audio until the receiver verifies and durably commits the exact capture, followed by authorized release. These static findings identify paths to improve, not observed Omi loss rates. AURA's new release controller/outbox is development work; production audio reclamation is still absent. |
| Source-linked memories and current access checks support trustworthy context. [Memory model](https://github.com/BasedHardware/omi/blob/f42089f53c8010dd971b3702ece05a231c9c0c66/app/lib/backend/schema/memory.dart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), [access gateway](https://github.com/BasedHardware/omi/blob/f42089f53c8010dd971b3702ece05a231c9c0c66/backend/models/memory_search_gateway.py) | Keep original audio/transcript, reviewed context and revocable future access. AURA already has local transcription, retained source metadata, Context Packs and read-only MCP. Correction history, complete account lifecycle and phone integration remain work. |

For this first unit, keep Wi-Fi, extra sensors, autonomous tasks and a large memory graph outside the critical path. Reuse Omi code only where it saves integration work and passes AURA's contracts, preserving applicable [license notices](https://github.com/BasedHardware/omi/blob/f42089f53c8010dd971b3702ece05a231c9c0c66/LICENSE).

## What exists today

- **Firmware:** monitored PDM ingress, recorder, real Opus, recoverable NAND journal, command adapter and durable C/Python archive are implemented and exercised by host tests and an ARM integration build. The owner-bound storage controller and companion release outbox have real C/Python release-and-reuse tests on modeled NAND. A separate [DK bench application and UART host](../../firmware/a04/bench/README.md) now connect the actual peripheral drivers, with reviewed wiring and an ARM build; no hardware has been flashed or exercised. The modeled erase path is not a production W25N audio-erase capability, secure enrollment or complete wearable application. [Firmware evidence](../../firmware/a04/README.md), [controller source](../../firmware/a04/src/aura_storage.c), [release outbox](../../companion/RELEASE.md).
- **Electronics:** the fresh A04 schematic has 72 candidate references. The circular PCB has **zero footprints, tracks and zones**. Three net mismatches, native ERC findings, duplicate labels, stackup/rule configuration and assembly details remain unresolved. There are no A04 manufacturing Gerbers. [Native status](../../hardware/a04/README.md).
- **Mechanics:** the primary M2 study is **43 mm diameter × 12.2 mm depth**, using the actual 1.6 mm draft PCB thickness. The thinner pack is unselected. The 17 models per variant include polymer parts, separate hardware forms and gauges; they are digitally checked development specimens, not a qualified printed assembly. Steel parts require real metal and insulation. [M2 package](../../enclosure/a04/mechanism-m2/README.md), [steel drawings](../../enclosure/a04/mechanism-m2-manufacturing/README.md).
- **Product:** the existing deployed showcase and film represent A03. They do not demonstrate a working circular A04. No A04 battery, charging dock, assembled radio, physical microphone path or wear trial has been qualified.

The [native Android app](../../mobile/android/README.md) now implements Gate 2's local archive-import, audio-validation, playback and manually written context foundation. Its [durable download owner](../../mobile/android/DOWNLOADS.md) commits exact source records and resume metadata together, replays retained prefixes through the shared Kotlin validator, and hands complete sources to the real Android decoder/library. The [foreground recovery coordinator](../../mobile/android/RECOVERY.md), `CaptureRecovery`, adds serial selection/resume, bounded retries and cancellation; `AndroidGattConnection` implements the Android GATT transport beneath it.

The current smoke run passed **29 native cases / 428 assertions** on API 34 with the actual `c2.android.opus.decoder`. It exercises SQLite rollback, finalized/physical-OPEN imports and recovery over scripted logical connections using fixed C fixtures. Separate real-Android-GATT tests passed four cases / 33 assertions at each of MTU 23 and 517 against a Python Bumble fixture. Neither suite establishes physical radio transfer or executes Zephyr firmware; [Android verification](../../mobile/android/VERIFICATION.md) records the current execution scope. The consumer UI still exposes file import. The separate [authenticated radio DK application](../../firmware/a04/radio/README.md) now implements the device GATT adapter and ASC1 proof provider with host-tested boundaries. Secure enrollment, matching Android proof integration, UI/lifecycle integration and a hardware-to-phone recovery trial remain. Preserving or importing a recording does not release it from the pendant.

## Build and acceptance route

These are proposed first-unit engineering gates, not completed tests or product certification.

| Gate | Concrete next artifact | Acceptance before advancing |
|---|---|---|
| **1. Actual audio/storage bench** | [Separate nRF52840 DK application, named fixture wiring, UART host and instructions](../../firmware/a04/bench/README.md) implemented and cross-built. Actual peripheral drivers are connected; the microphone stays off until explicit START plus physical permission. Host and C orchestration regressions pass. First physical assembly/flash/execution remains undone; the earlier synthetic ARM probe is a different target. | Capture 20 spoken notes into real NAND, export, independently decode and play back every accepted note. Power-interrupt a disposable test recording and recover the verified prefix with an honest interrupted status. Record encode deadlines, FIFO loss, NAND latency, runtime stack headroom and measured current. |
| **2. One phone recovery loop** | Android storage, playback, explicit context export, foreground coordinator and GATT client now exist. Connect secure enrollment and consumer lifecycle/UI to the matching device GATT adapter, then exercise the same source contract on hardware. Keep background operation an unclaimed capability until measured. | Disconnect and kill the app around transfer/commit, then resume without losing or duplicating verified captures. No network is needed to preserve/play local audio. Releasing one authorized finalized capture preserves all others. Reject a different owner and stale release command. |
| **3. Custom board release** | Correct the fresh MCP-native schematic, freeze exact parts/pack/dock and actual stackup, then place and route. Export the matching Gerber/drill/netlist, purchased BOM, placement, stencil and assembly drawings. | Independently reviewed pin/power/thermal/RF design; complete native ERC/DRC dispositions; maximum-body/tolerance and case checks; supplier CAM/assembly approval; a documented first-article test plan. An empty-board pass or A03 fabrication ZIP cannot satisfy this gate. |
| **4. Unpowered fit and controls** | Print the process coupon, gauges and M2 development specimens; fit measured hardware, insulating interfaces and a representative inert pack. Record the assembled mass and dimensions. | Verify the complete assembly sequence, microphone openings, antenna space, service access, switch endpoints/force, thread retention and attachment. Confirm the pack bears no switch or clamping load. Revise geometry from measurements before claiming a thin final size. |
| **5. Powered first article, then personal wear** | Assemble the reviewed PCB; inspect and bring up rails/SWD/audio/storage before the matched battery/NTC/dock. Complete the actual firmware's privacy, radio and recovery integration. | Measure charging limits and faults against the exact approved component limits, enclosure temperatures, RF with the actual chain/body, acoustic quality and workload runtime. After bench/attachment/insulation acceptance, progress through a short supervised wear trial, two hours, then an eight-hour target with a stated recording workload. Record discomfort, heat, snagging and missed captures; charging during engineering evaluation stays off body. |

The bench software and fixture guide now make **Gate 1's first hardware experiment executable**. The next evidence is an actual recording, decoded playback and measured timing/power from that fixture; then connect Gate 2 to the same recording contract. Further host tests are useful when they cover a newly identified defect; they cannot supply microphone timing, real flash behavior, usable phone recovery or comfort evidence. Prepare Gate 4 in parallel and let its measurements constrain the board and enclosure together.

Omi's [XIAO assembly guide](https://github.com/BasedHardware/omi/blob/f42089f53c8010dd971b3702ece05a231c9c0c66/docs/doc/assembly/Build_the_device.mdx) is an alternative learning build if a separate Omi-compatible trial is desired. It has its own firmware, case, power wiring and phone path. It does not validate AURA's independent microphone cutoff, local journal, battery or mechanics; introducing that second port is unnecessary for the primary A04 bench milestone.

For each physical trial, retain the board/firmware/part revisions, setup photograph, workload, measurements, source audio, interruption point and pass/fail disposition in a private first-unit log. Publish sanitized reports with the eventual release; keep personal recordings and enrollment keys private.

Required KiCad corrections remain blocked by recorded tool declines without a supplied reason. The rejected operations have not been retried through another mechanism or bypassed. This must be resolved before the custom PCB fabrication gate can close; the independent firmware and unpowered fit work can continue.
