Avinash1286/pendent/film/docs/README.md

# Hyperframes documentation snapshot

The skill/reference documents in this directory were retrieved from the [official Hyperframes repository](https://github.com/heygen-com/hyperframes) to author and validate the accompanying launch film. They remain upstream work, distributed under the repository's Apache License 2.0; see `LICENSE.hyperframes.txt`.

Use current upstream documentation for future tool updates. The film itself pins Hyperframes0.8.31 in its package file and records the actual validation results in `../aura-launch/qa`.
