Avinash1286/pendent/companion/RELEASE.md

# Explicit A04 release requests and durable outbox

`aura_companion.release` implements local, explicit release issuance for one exact **FINALIZED** capture already committed to a receiver database. It produces the same 182-byte RLS1 envelope as [the portable firmware primitive](../firmware/a04/RELEASE-AUTH.md), using standard-library HMAC-SHA256 with the domain `AURA-A04-OWNER-RELEASE-v1` plus exactly one NUL byte. It does not send messages, connect to a pendant, change the CLI, provision a device, or erase anything.

## API and explicit permission

`TrustedReleaseContext(device_id, storage_incarnation, owner_id, owner_generation, key)` must be supplied by trusted enrollment. IDs are nonzero 16-byte values, generation is a nonzero uint64, and the independently generated secret is exactly 32 bytes. There are no default keys, enrollment discovery or key-file writes. The key is excluded from the context's representation and is never persisted in the outbox; Python does not provide a whole-process secret-erasure guarantee. A nonzero check is an initialization guard, not proof of entropy or secure key storage.

`ReleaseOutbox.provision(path, context, initial_sequence_floor=trusted_floor)` creates a new local outbox exclusively at a previously absent path. The initial floor is mandatory and must be verified externally; it is never guessed as zero or discovered from an archive. Provisioning is local database setup, not ownership enrollment. Existing files are never overwritten, repaired or reset. A failed initial provision may leave a file requiring explicit inspection.

`ReleaseOutbox(path, context)` opens an existing outbox, checks authenticated authority/history, and refuses a missing database or a mismatched context/key. There is no rekey API. Changing ownership requires a future coordinated transition that preserves the sequence floor; opening a database under new ownership does not reset it.

```python
from aura_companion.release import ReleaseOutbox, RELEASE_PERMISSION
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
