Avinash1286/pendent/docs/a04/preview/sheet-01.png

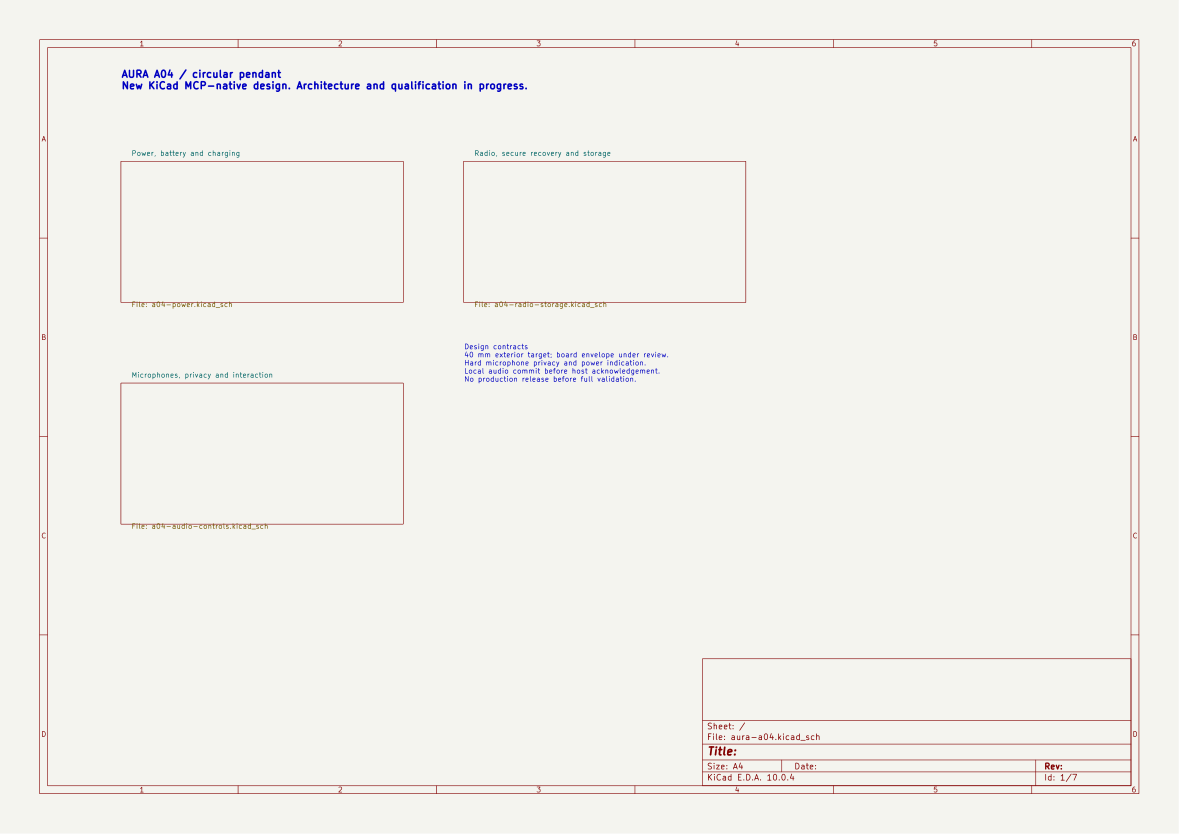
docs/a04/preview/sheet-01.png
