Avinash1286/pendent/docs/a04/preview/sheet-02.png

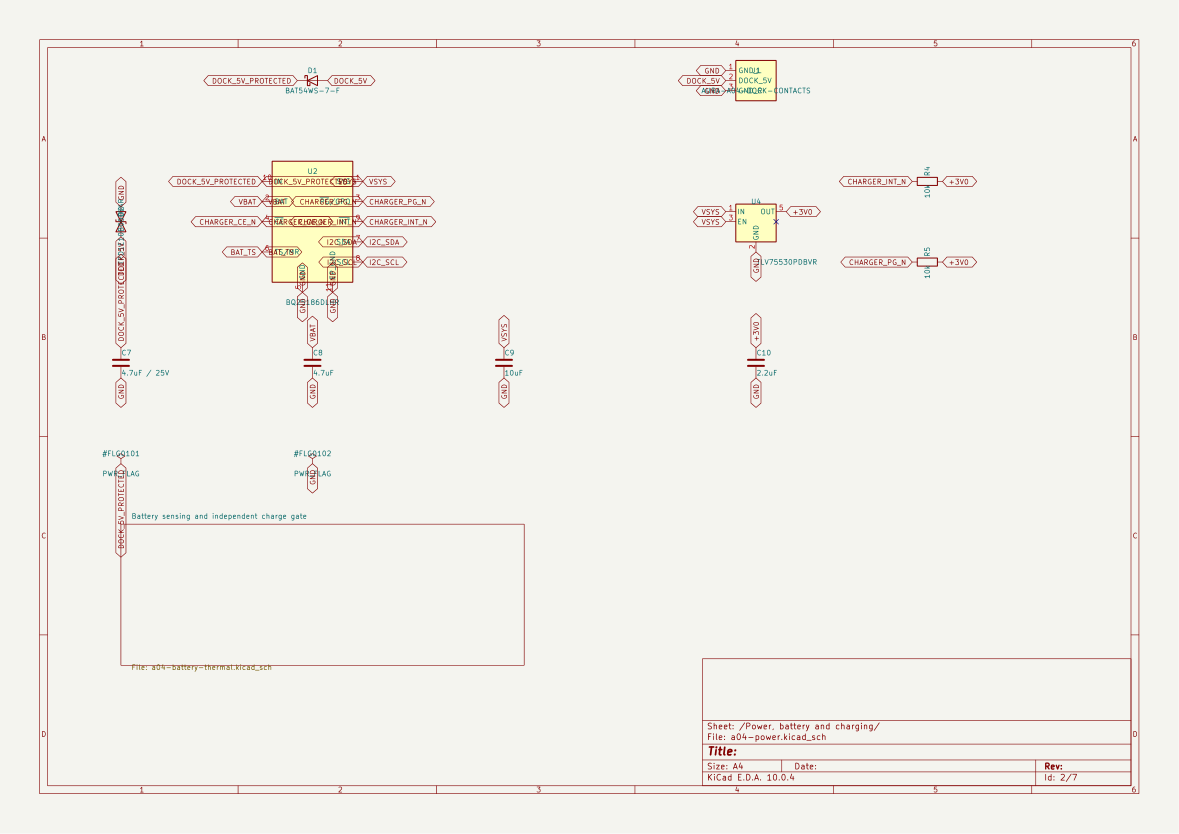
docs/a04/preview/sheet-02.png
