Avinash1286/pendent/docs/a04/preview/sheet-03.png

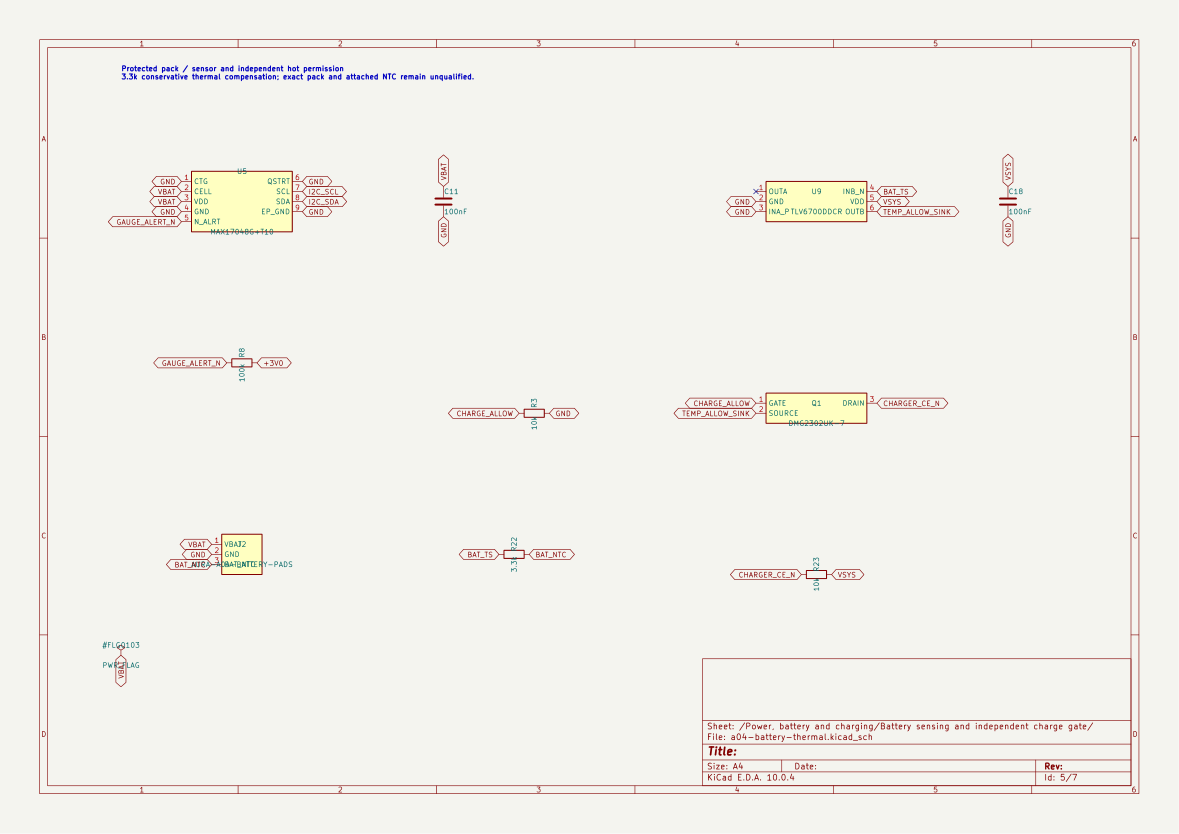
docs/a04/preview/sheet-03.png
