Avinash1286/pendent/docs/a04/preview/sheet-04.png

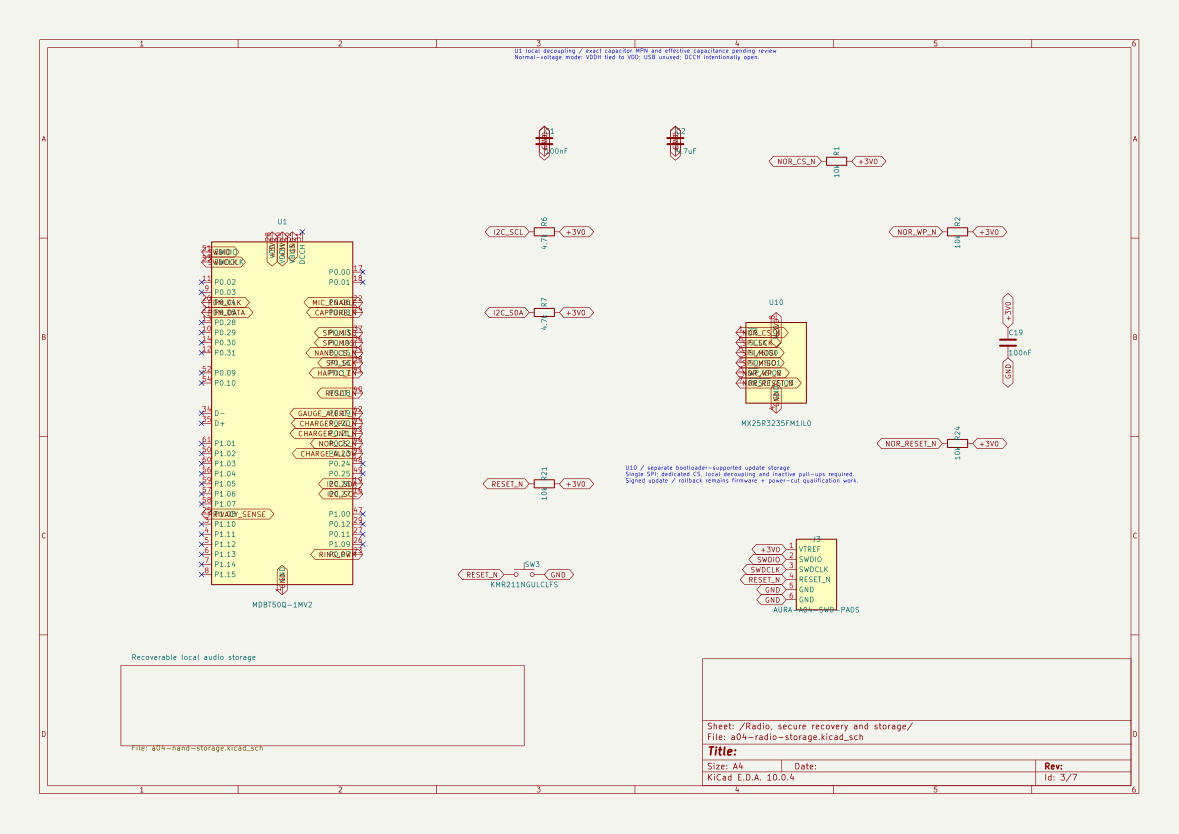
docs/a04/preview/sheet-04.png
