Avinash1286/pendent/docs/a04/preview/sheet-05.png

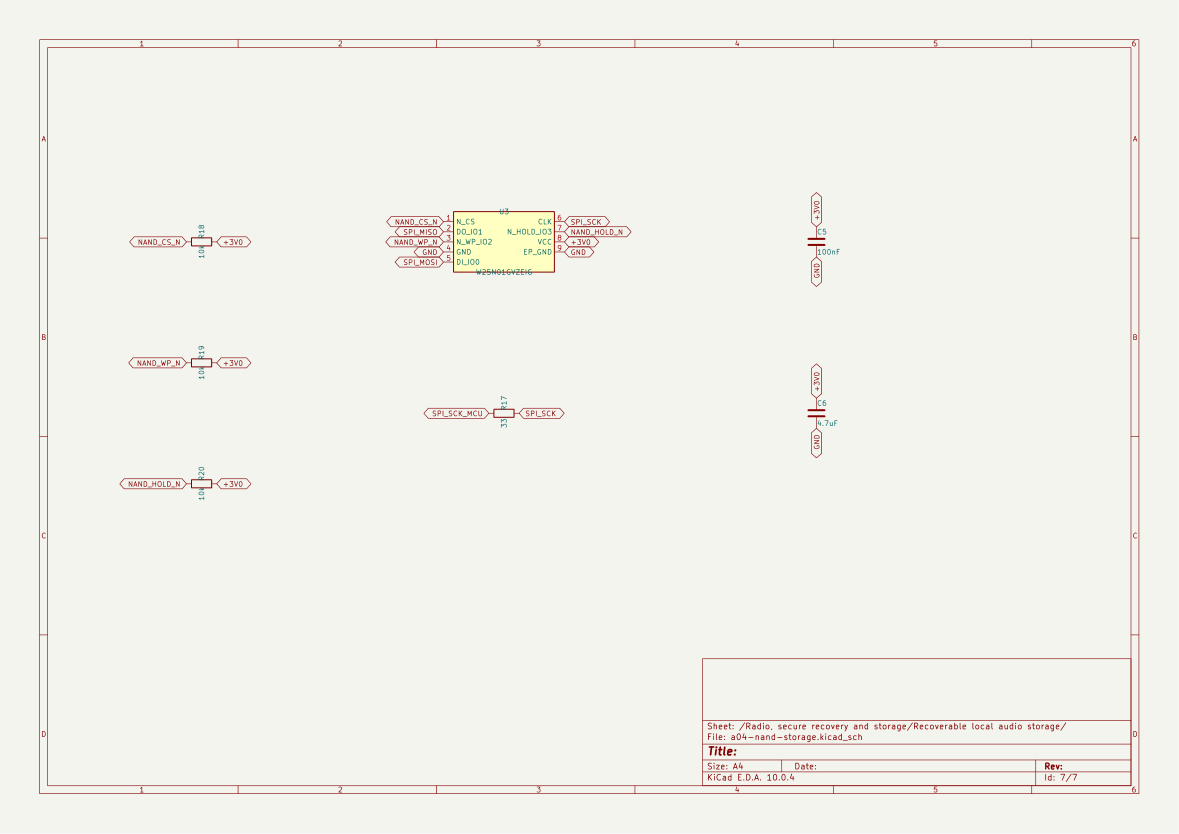
docs/a04/preview/sheet-05.png
