Avinash1286/pendent/docs/a04/preview/sheet-06.png

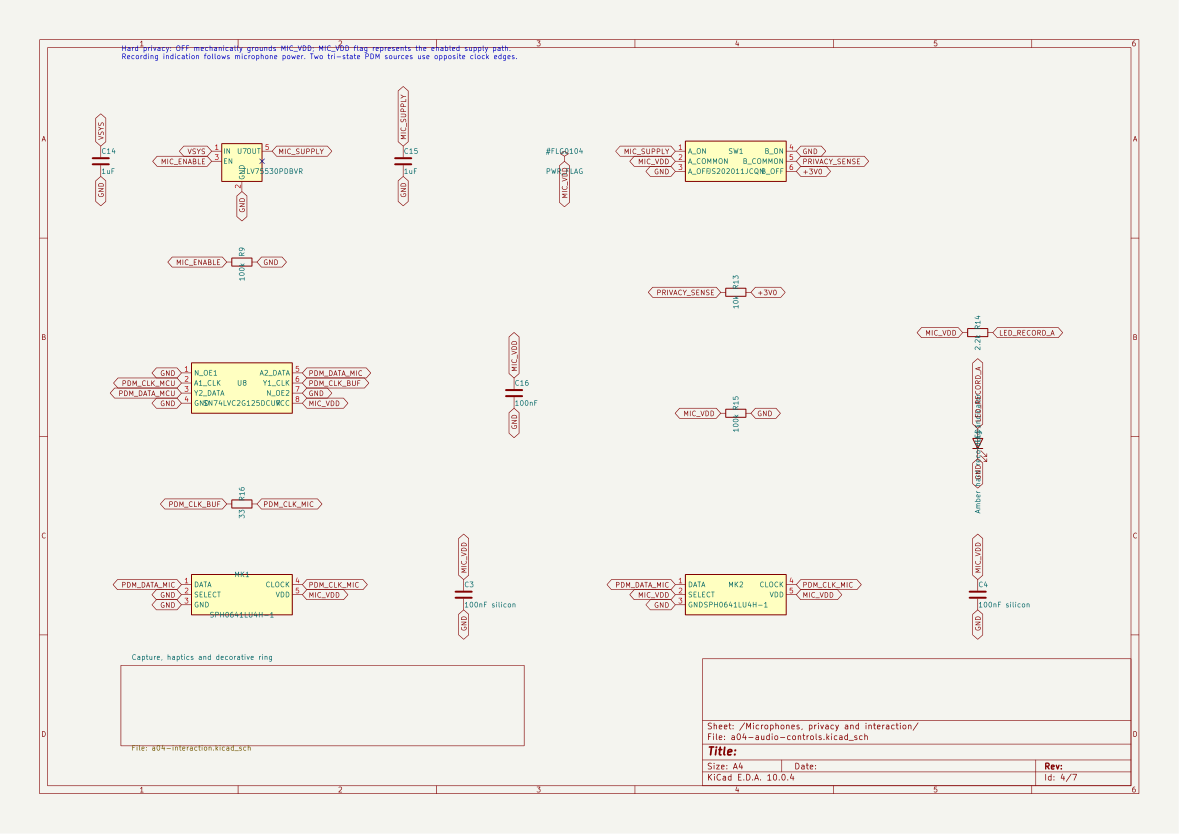
docs/a04/preview/sheet-06.png
