Avinash1286/pendent/docs/a04/preview/sheet-07.png

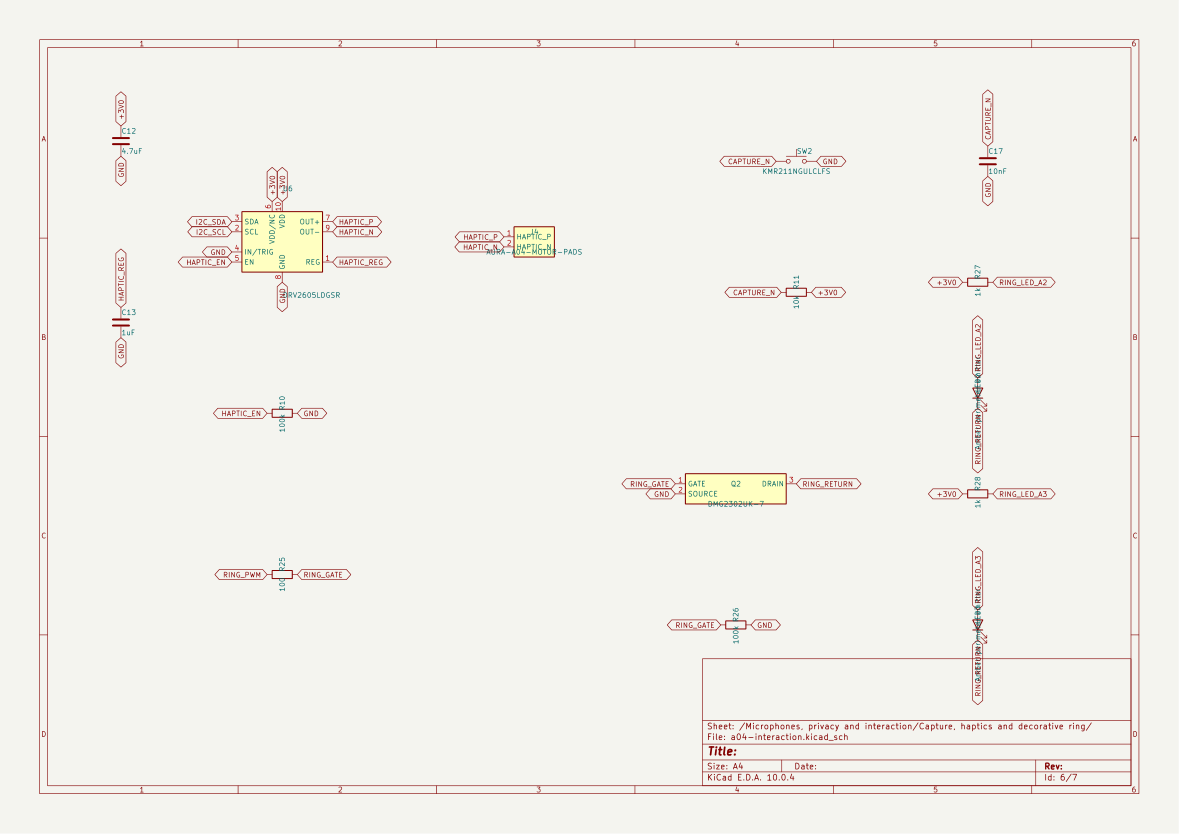
docs/a04/preview/sheet-07.png
