Avinash1286/pendent/enclosure/a04/coupon/coupon-overview.png

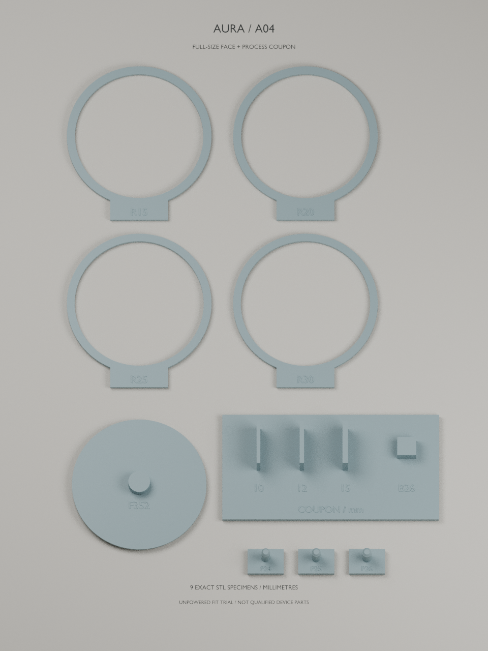
enclosure/a04/coupon/coupon-overview.png
