Avinash1286/pendent/enclosure/a04/mechanism/evidence/cus22-body-detail.png

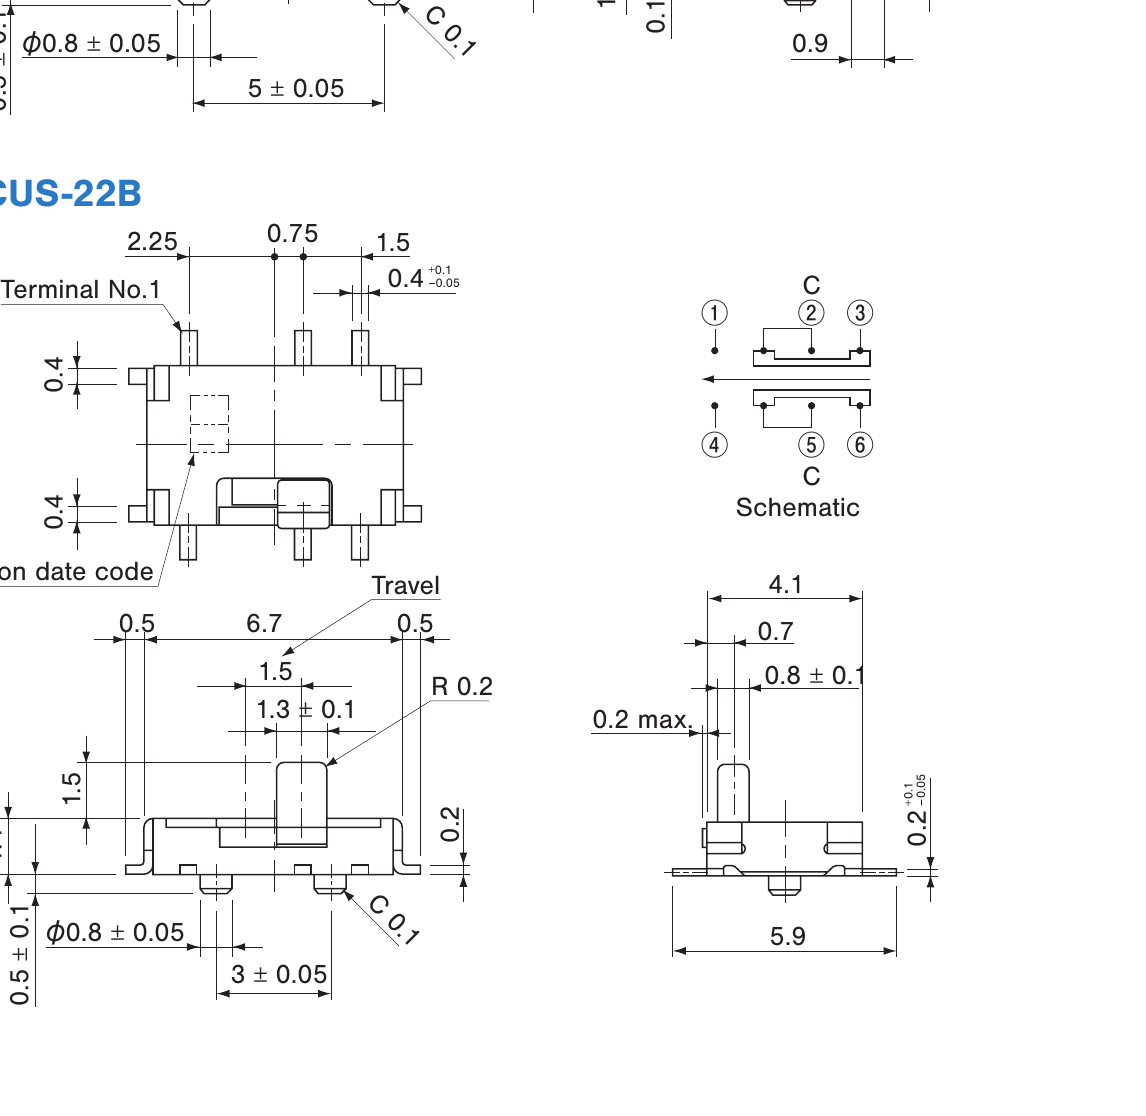
enclosure/a04/mechanism/evidence/cus22-body-detail.png
