Avinash1286/pendent/enclosure/a04/mechanism/evidence/cus22-pad-detail.png

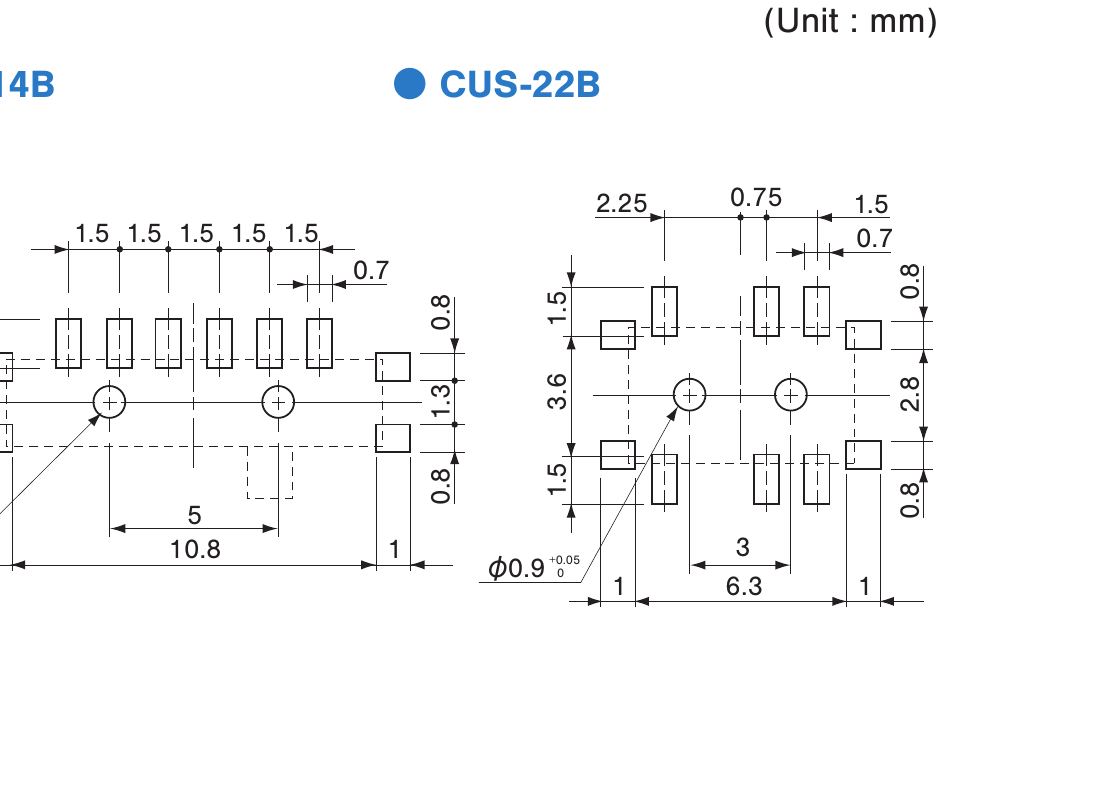
enclosure/a04/mechanism/evidence/cus22-pad-detail.png
