Avinash1286/pendent/enclosure/a04/study/aura-a04-study.png

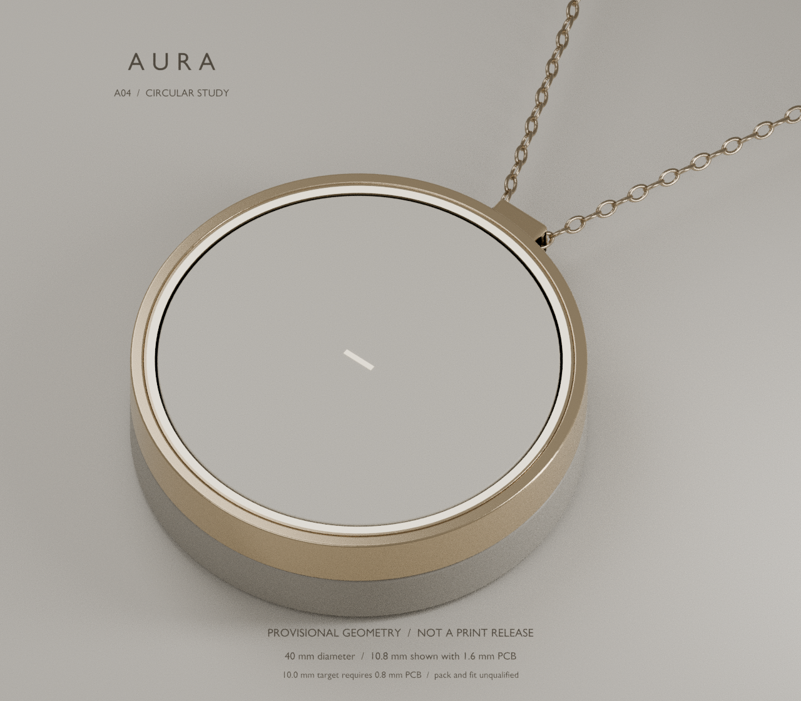
enclosure/a04/study/aura-a04-study.png
