Avinash1286/pendent/enclosure/renders/detail.png

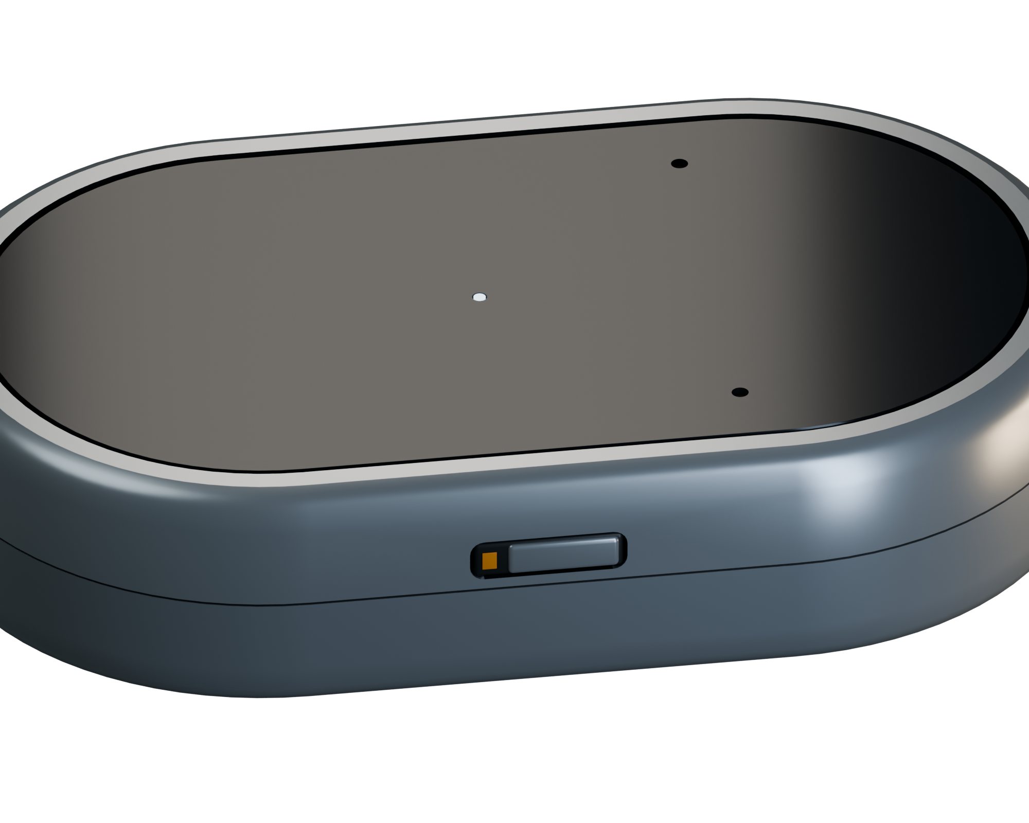
enclosure/renders/detail.png
