Avinash1286/pendent/enclosure/renders/exploded.png

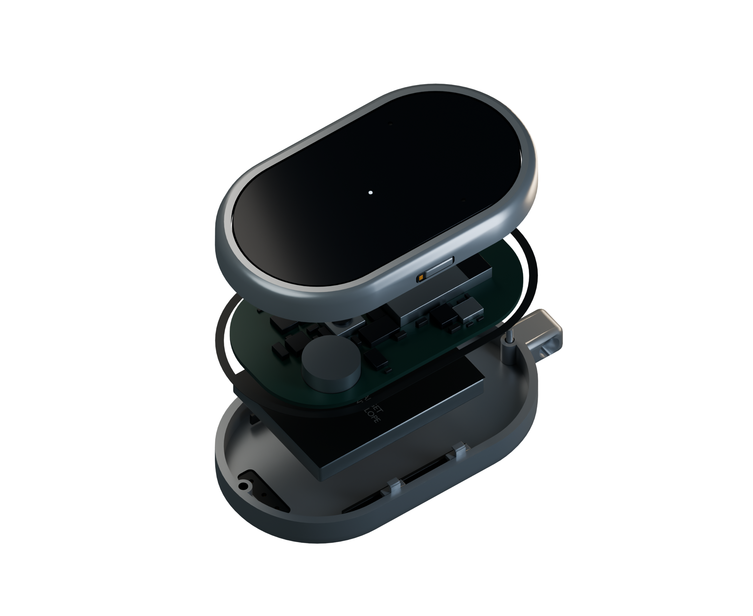
enclosure/renders/exploded.png
