Avinash1286/pendent/enclosure/renders/hero-transparent.png

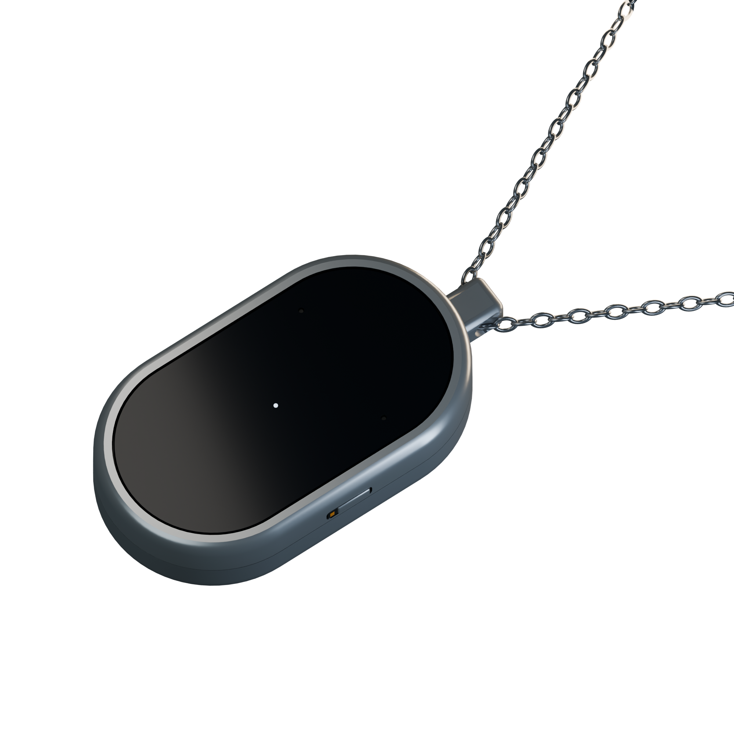
enclosure/renders/hero-transparent.png
