Avinash1286/pendent/enclosure/renders/profile-normal-preview.png

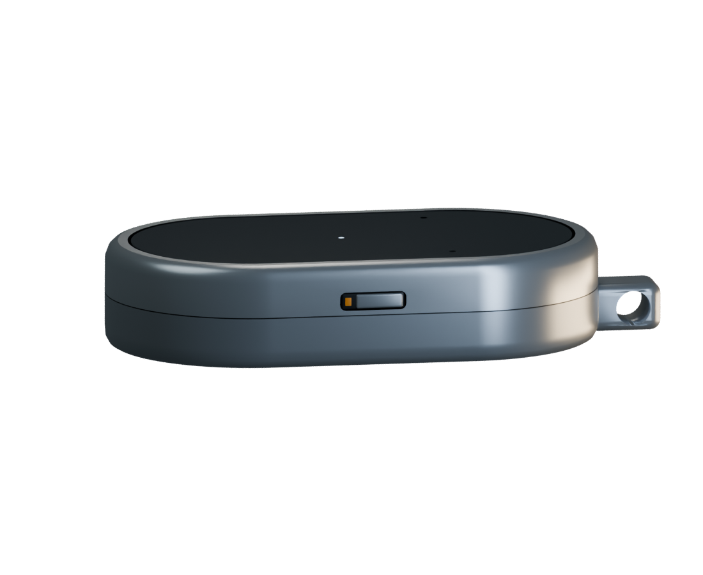
enclosure/renders/profile-normal-preview.png
