Avinash1286/pendent/enclosure/renders/rear.png

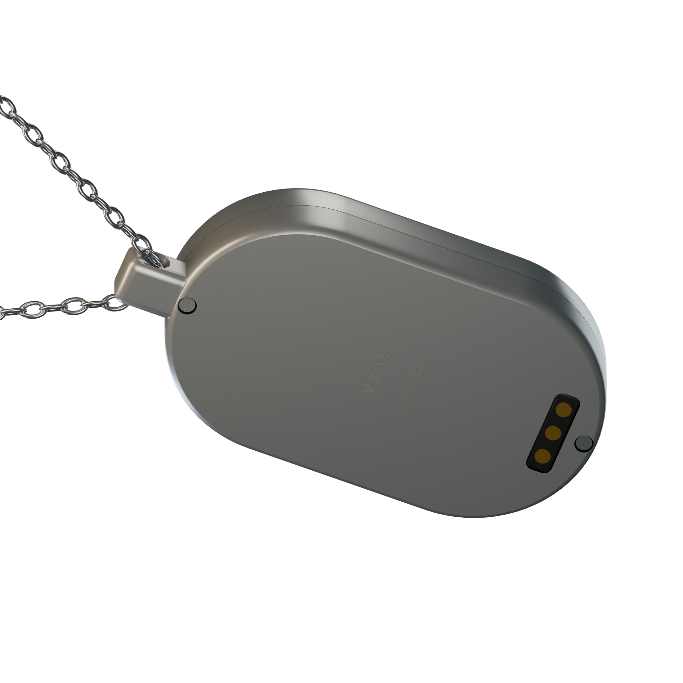
enclosure/renders/rear.png
