Avinash1286/pendent/film/aura-launch/.thumbnails/v4_v3_9c6d8b546462f6f0_44d4f0d17214cfa3_jpeg_preview_index.html_1920x1080_240x135_1788806804823_25.80.jpg

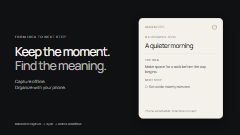
film/aura-launch/.thumbnails/v4_v3_9c6d8b546462f6f0_44d4f0d17214cfa3_jpeg_preview_index.html_1920x1080_240x135_1788806804823_25.80.jpg
