Avinash1286/pendent/film/aura-launch/renders/contact-sheet.jpg

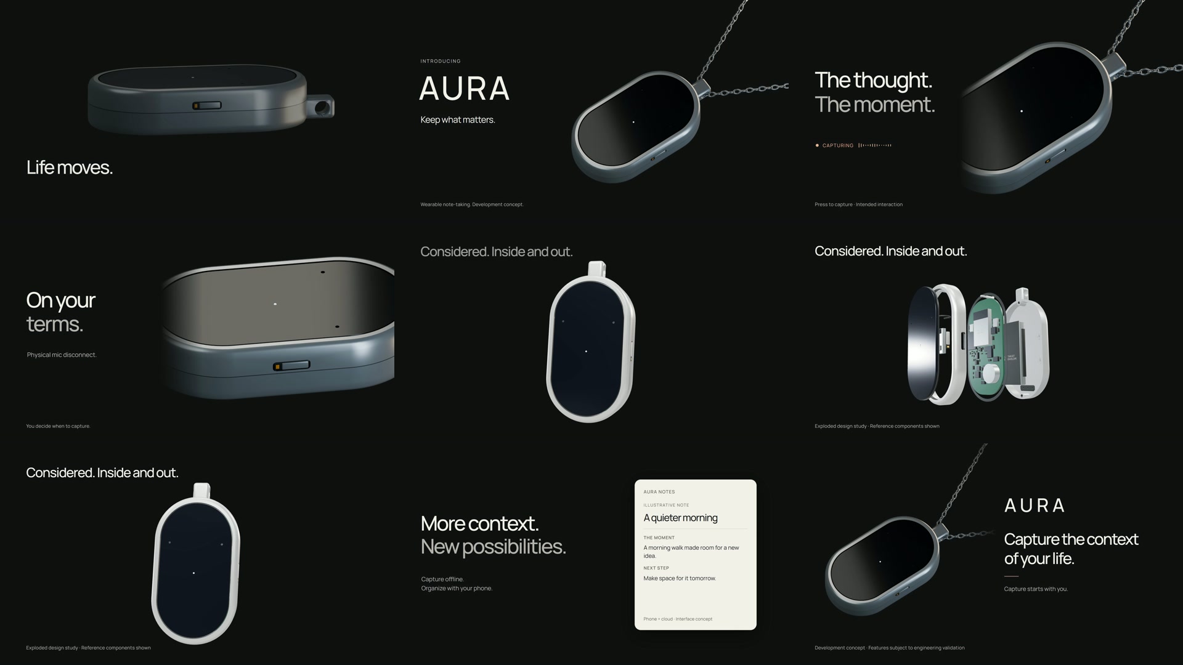
film/aura-launch/renders/contact-sheet.jpg
