Avinash1286/pendent/film/aura-launch/snapshots/frame-00-at-1.2s.png

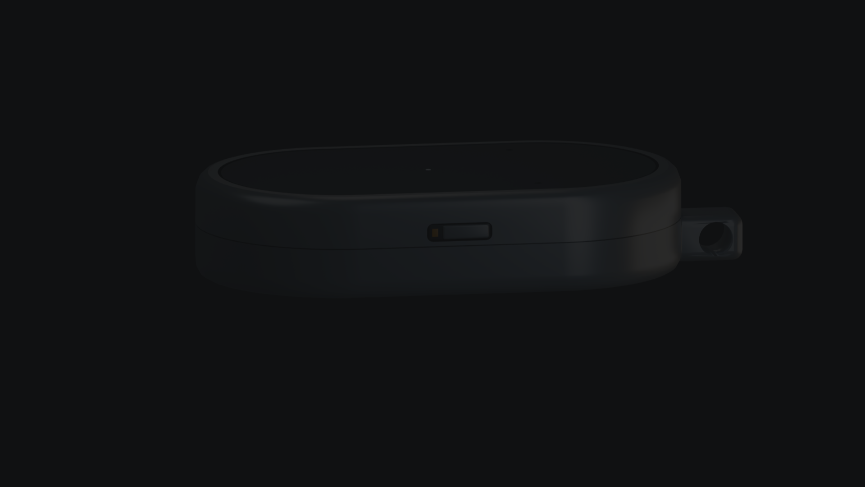
film/aura-launch/snapshots/frame-00-at-1.2s.png
