Avinash1286/pendent/film/aura-launch/snapshots/frame-01-at-11.0s.png

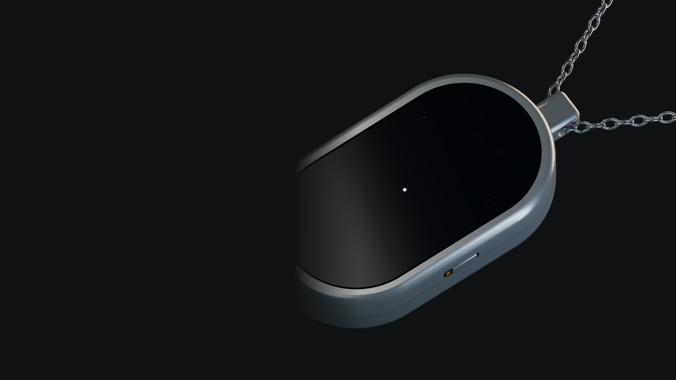
film/aura-launch/snapshots/frame-01-at-11.0s.png
