Avinash1286/pendent/film/aura-launch/snapshots/frame-02-at-20.8s.png

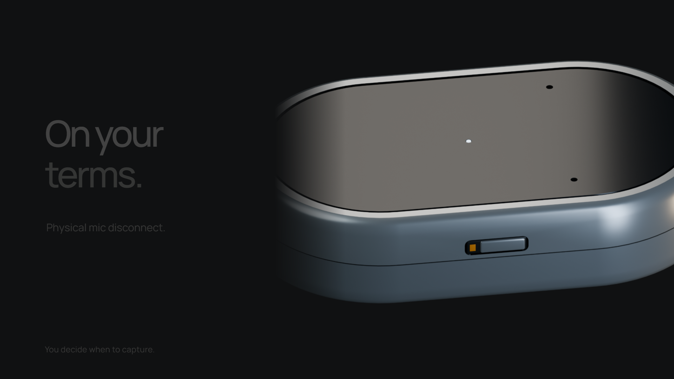
film/aura-launch/snapshots/frame-02-at-20.8s.png
