Avinash1286/pendent/film/aura-launch/snapshots/frame-03-at-30.6s.png

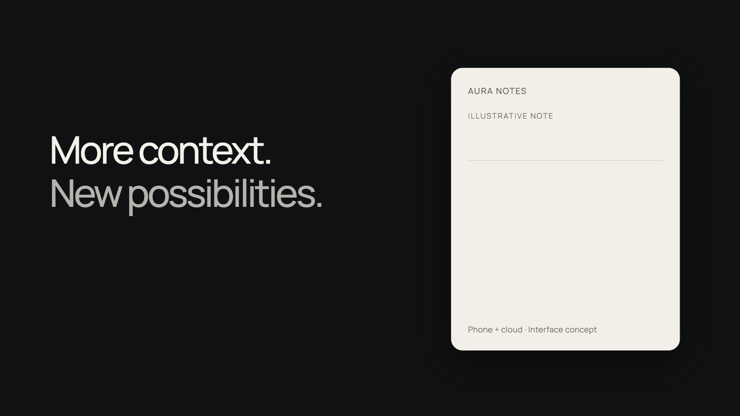
film/aura-launch/snapshots/frame-03-at-30.6s.png
