Avinash1286/pendent/hardware/a04/review/candidate-2/power/a04-power.png

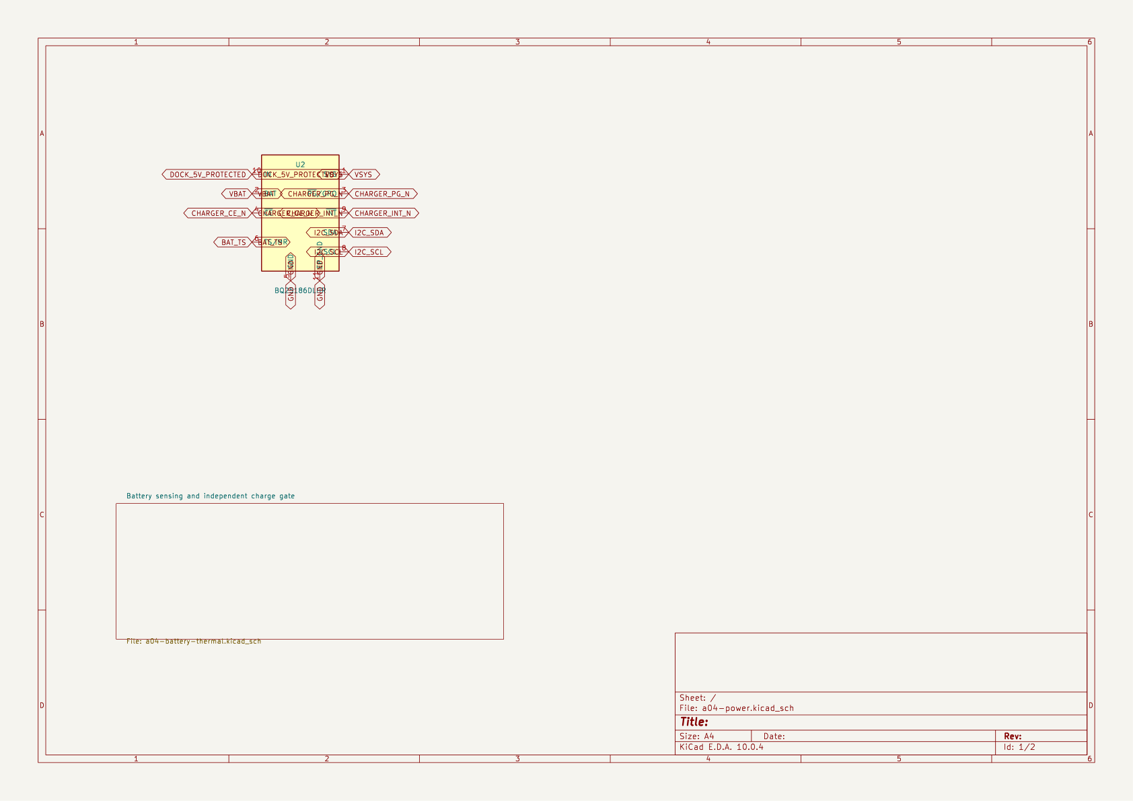
hardware/a04/review/candidate-2/power/a04-power.png
