Avinash1286/pendent/hardware/a04/review/power/a04-power.png

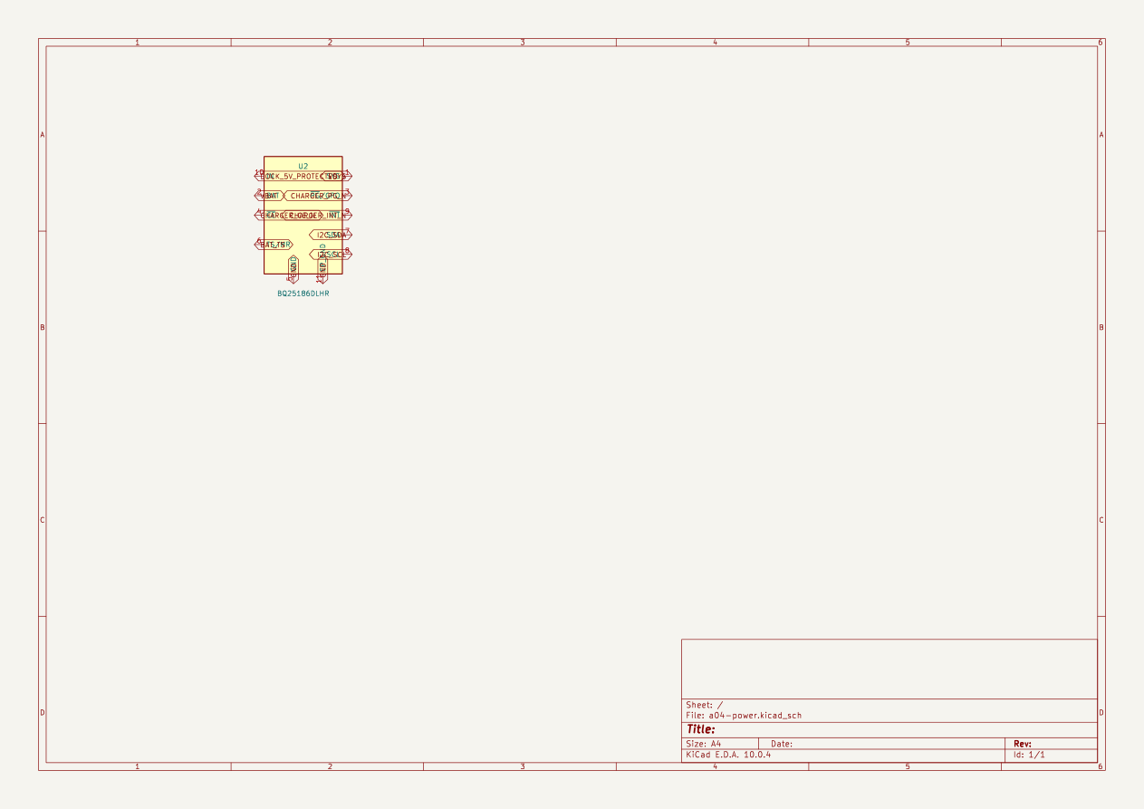
hardware/a04/review/power/a04-power.png
