Avinash1286/pendent/hardware/output/a03-audio.png

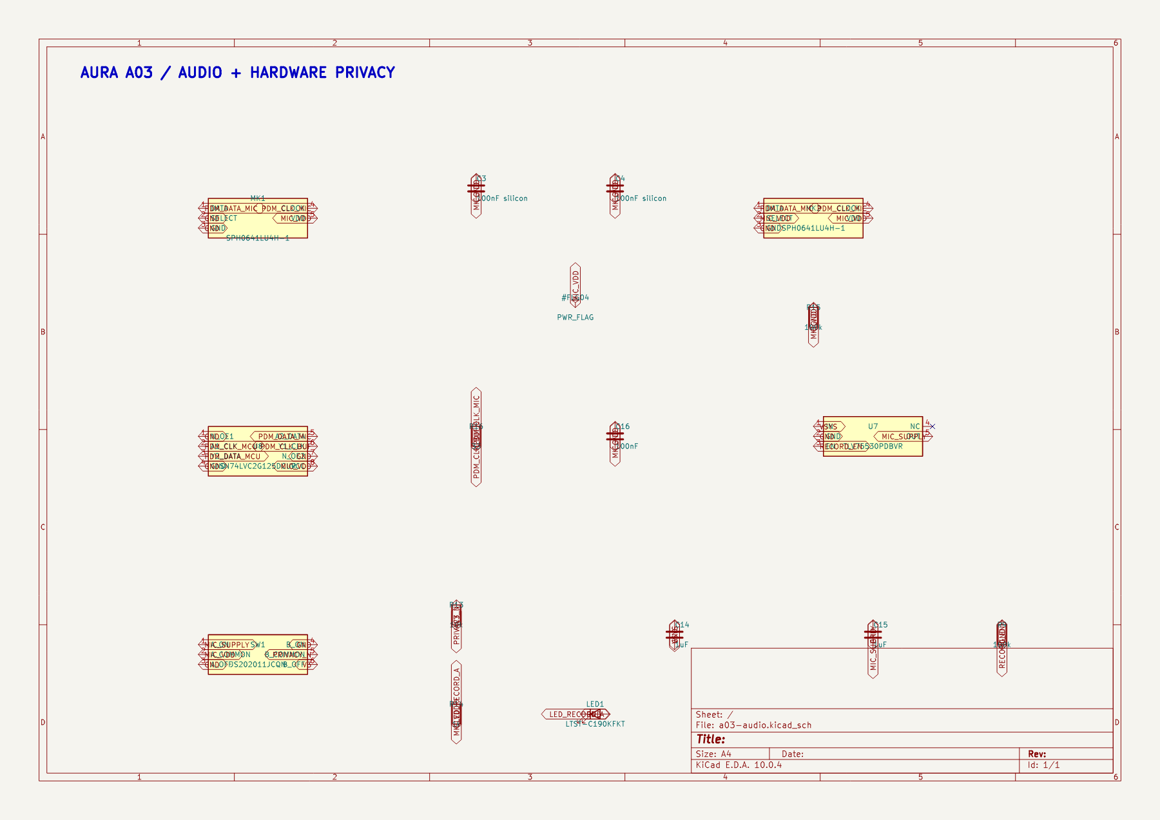
hardware/output/a03-audio.png
