Avinash1286/pendent/hardware/output/aura-a03-route-study.png

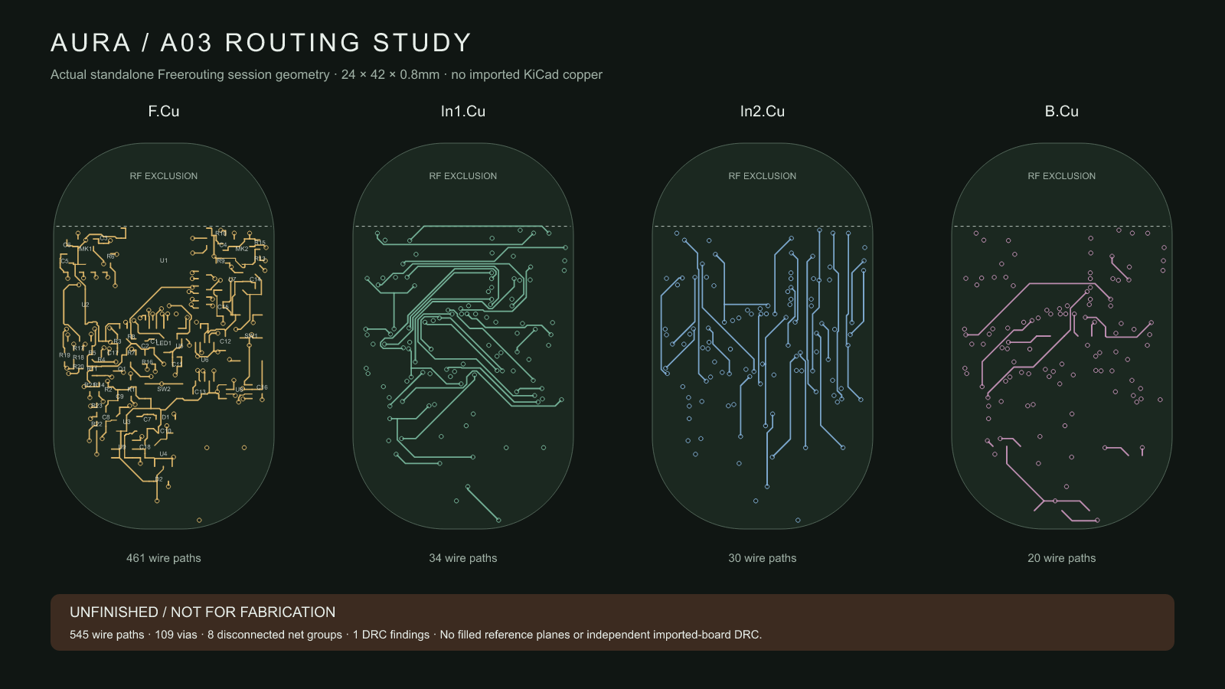
hardware/output/aura-a03-route-study.png
