Avinash1286/pendent/hardware/output/aura-placement.pcb.png

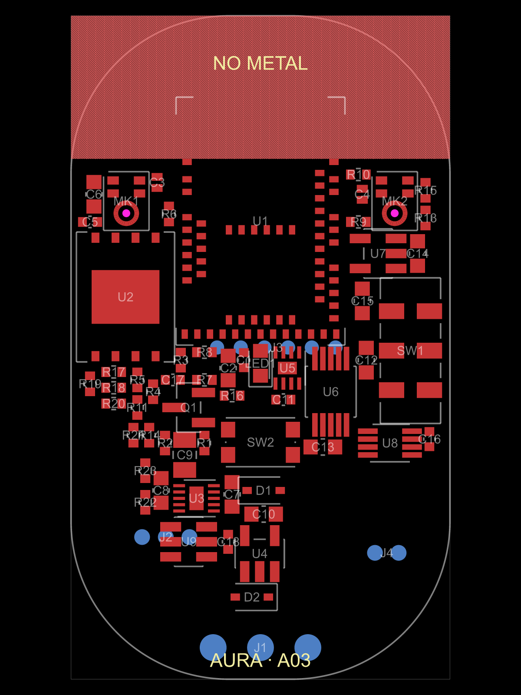
hardware/output/aura-placement.pcb.png
