Avinash1286/pendent/hardware/output/aura-schematic.png

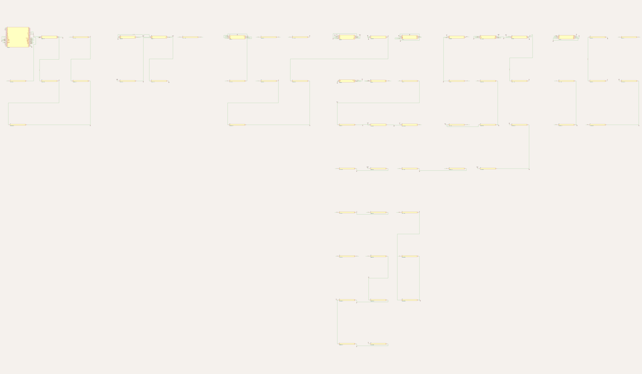
hardware/output/aura-schematic.png
