Avinash1286/pendent/hardware/output/native-sheets/aura-a03-electrical-Audio and privacy.png

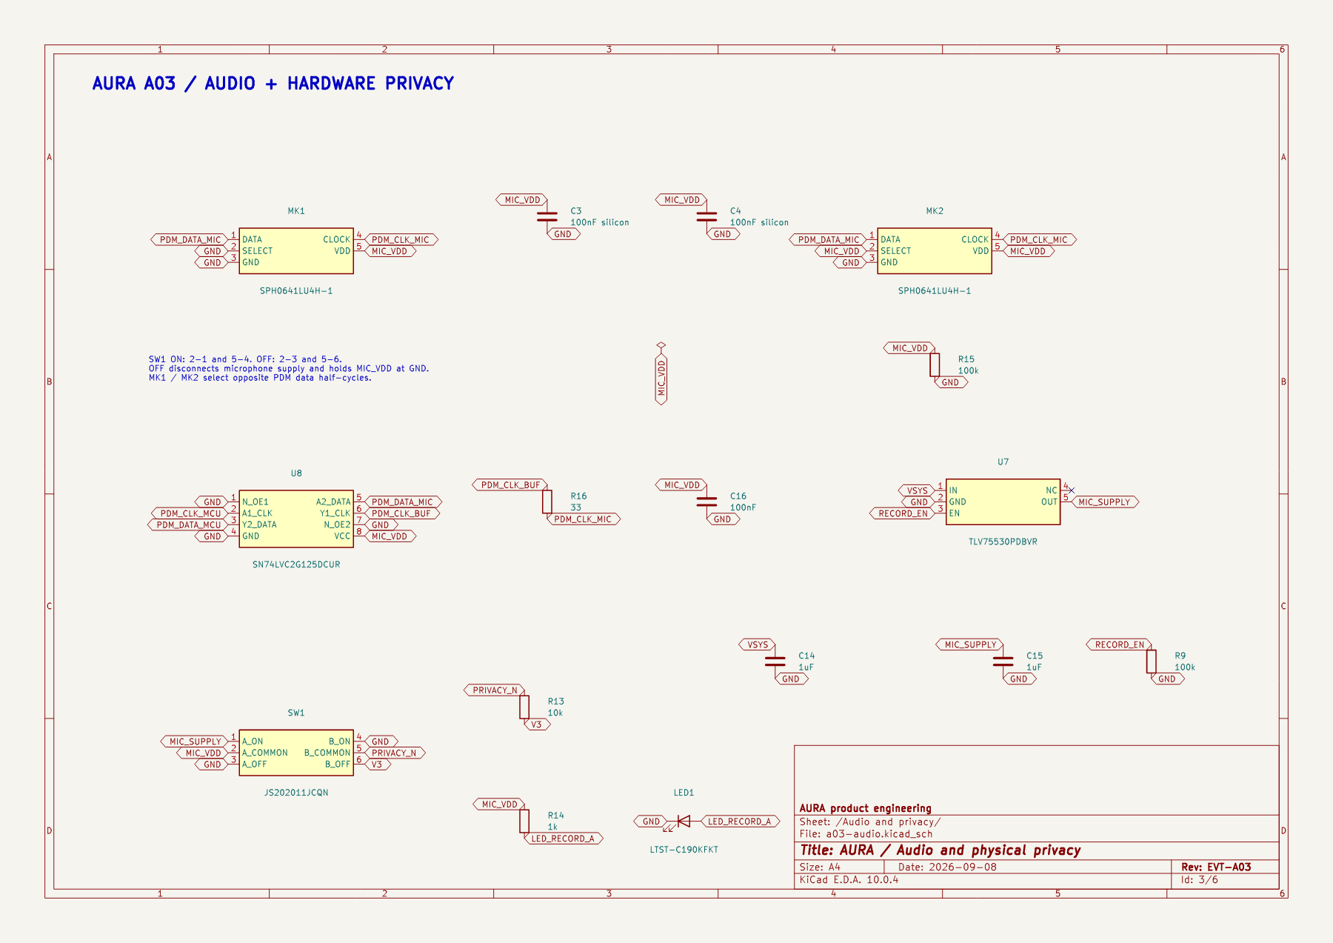
hardware/output/native-sheets/aura-a03-electrical-Audio and privacy.png
