Avinash1286/pendent/hardware/output/native-sheets/aura-a03-electrical-Charging and thermal limit.png

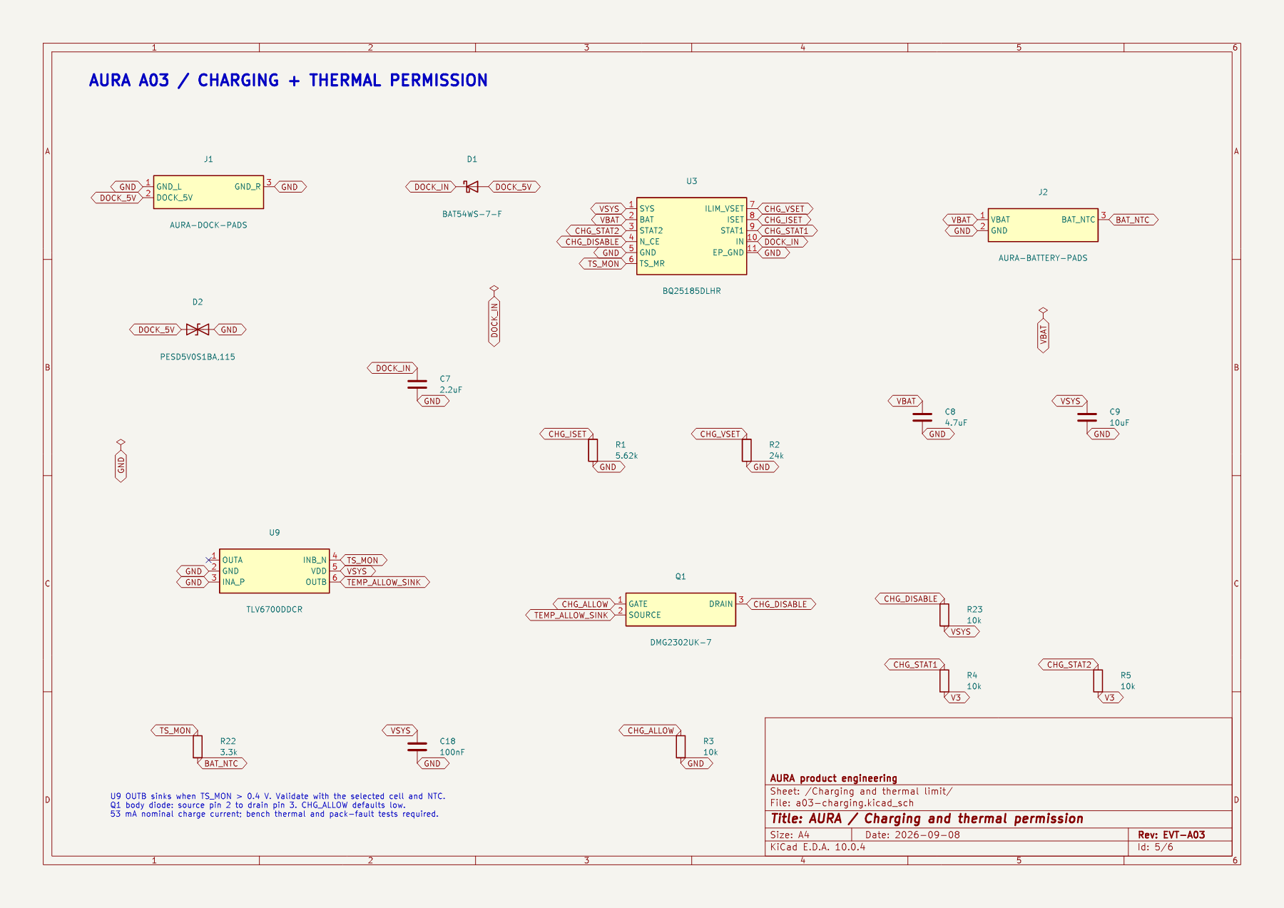
hardware/output/native-sheets/aura-a03-electrical-Charging and thermal limit.png
