Avinash1286/pendent/hardware/output/native-sheets/aura-a03-electrical-Offline storage.png

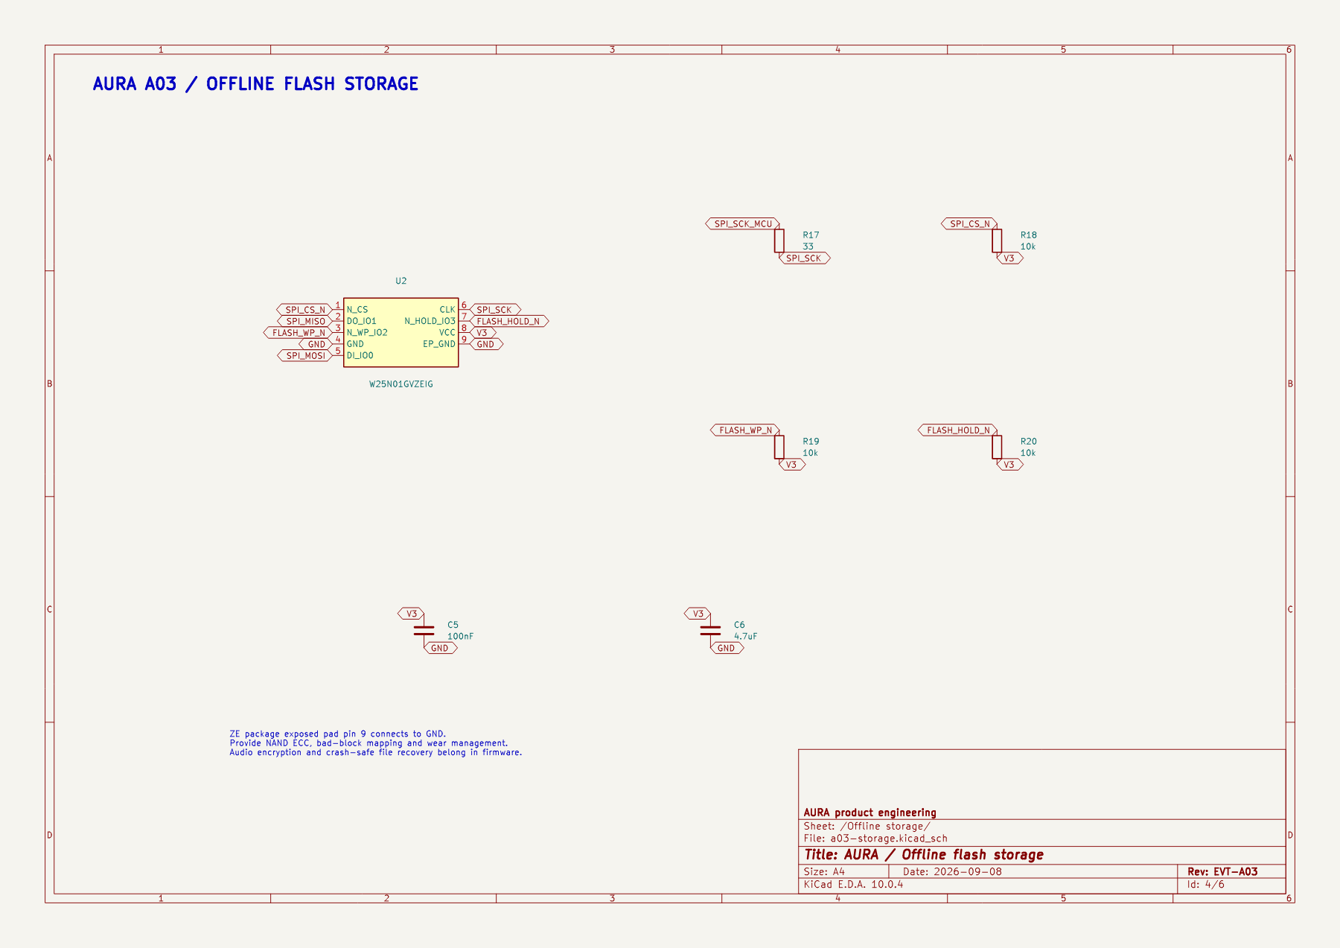
hardware/output/native-sheets/aura-a03-electrical-Offline storage.png
