Avinash1286/pendent/hardware/output/native-sheets/aura-a03-electrical-System power and controls.png

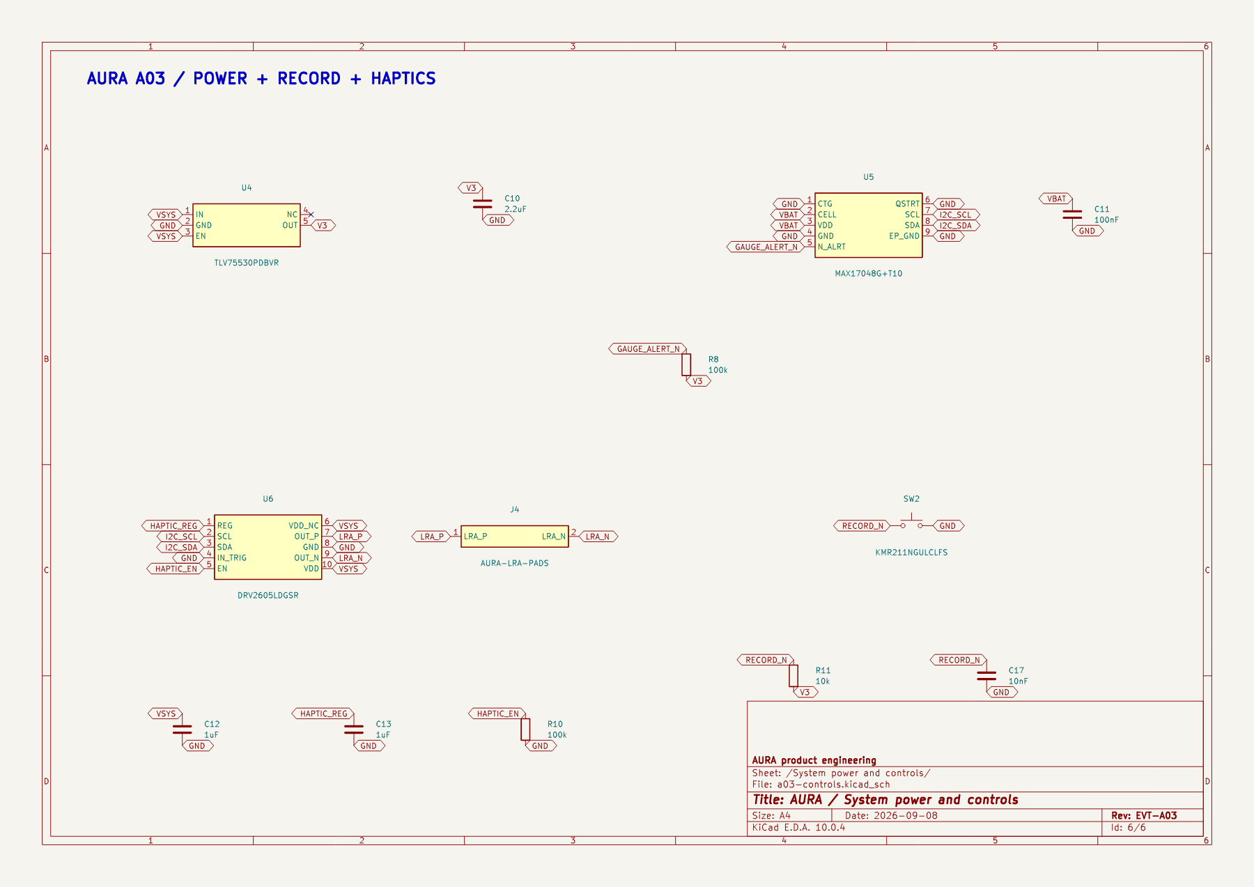
hardware/output/native-sheets/aura-a03-electrical-System power and controls.png
