Avinash1286/pendent/hardware/output/native-sheets/aura-a03-electrical.png

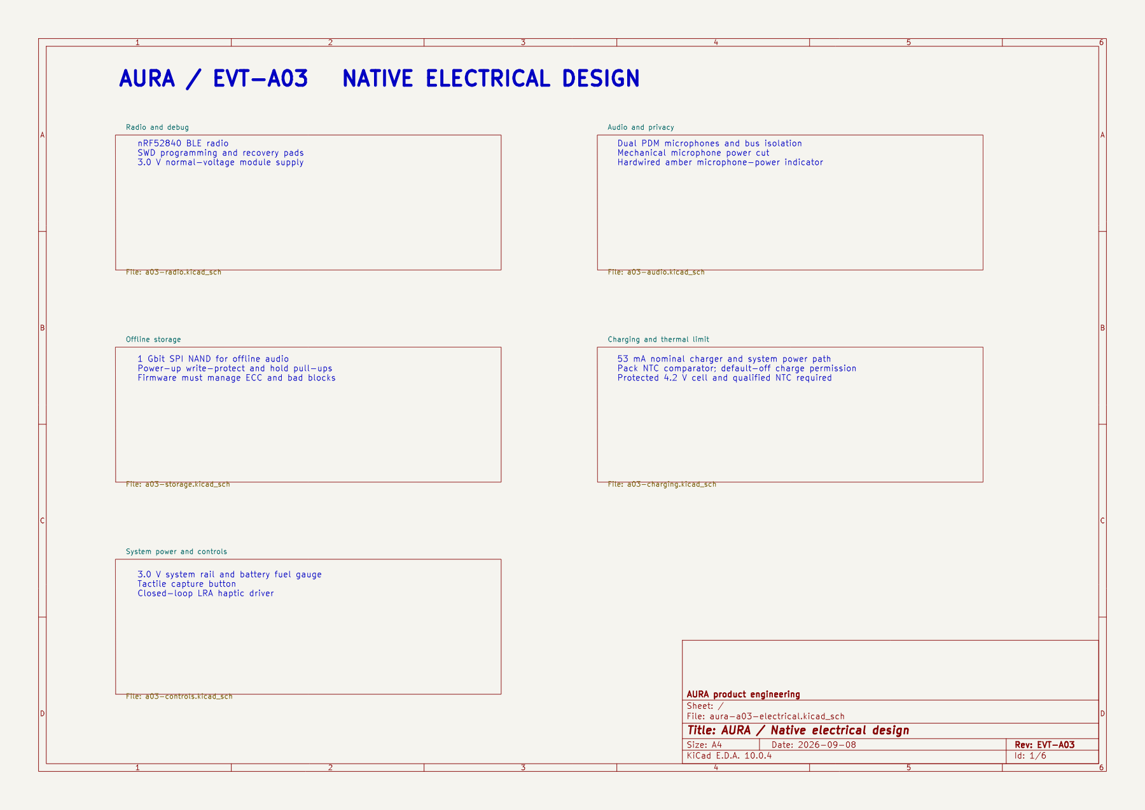
hardware/output/native-sheets/aura-a03-electrical.png
