Avinash1286/pendent/enclosure/a04/mechanism-m2/documented-pack/07_cartridge_keeper_left.stl

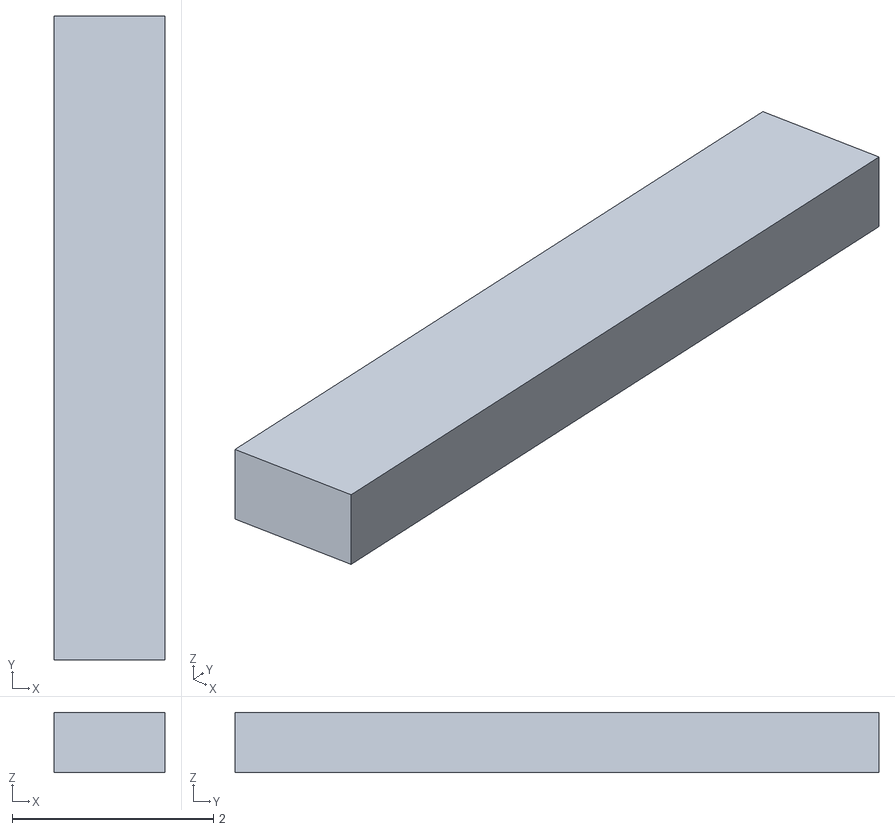
[picture p60: CAD file, 2026-09-09]
enclosure/a04/mechanism-m2/documented-pack/07_cartridge_keeper_left.stl
1.10 x 6.40 x 0.6
