Avinash1286/pendent/enclosure/a04/mechanism-m2/thin-cell/13_lower_steel_stiffener.stl

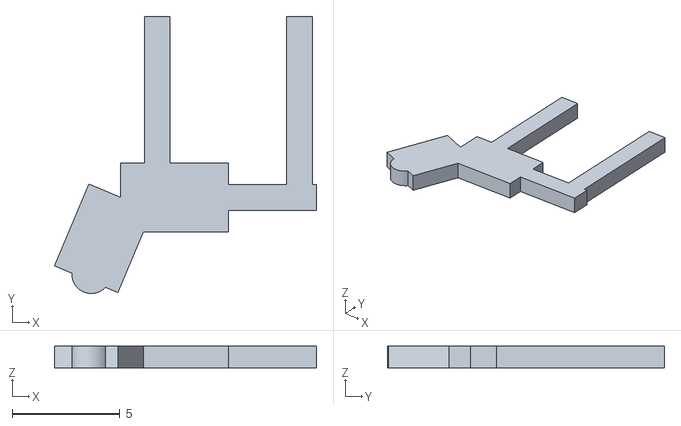
[picture p61: CAD file, 2026-09-09]
enclosure/a04/mechanism-m2/thin-cell/13_lower_steel_stiffener.stl
12.2 x 12.9 x 1.00
