Avinash1286/pendent/enclosure/a04/mechanism/documented-pack/11_right_lower_sensor_carrier.stl

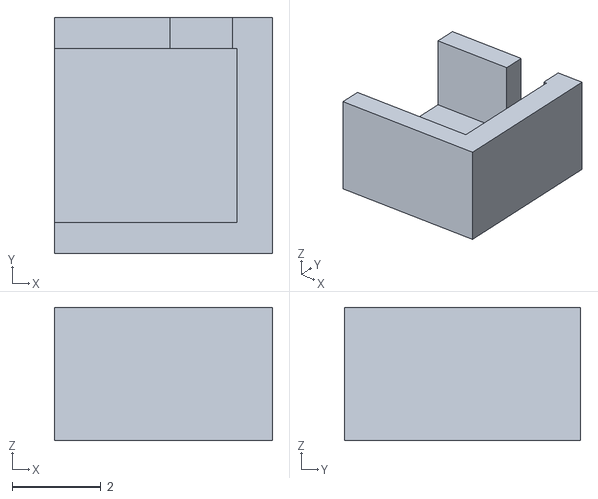
[picture p62: CAD file, 2026-09-08]
enclosure/a04/mechanism/documented-pack/11_right_lower_sensor_carrier.stl
4.90 x 5.30 x 3.00
