Avinash1286/pendent/enclosure/a04/mechanism/thin-cell/90_unpowered_notched_board_gauge.stl

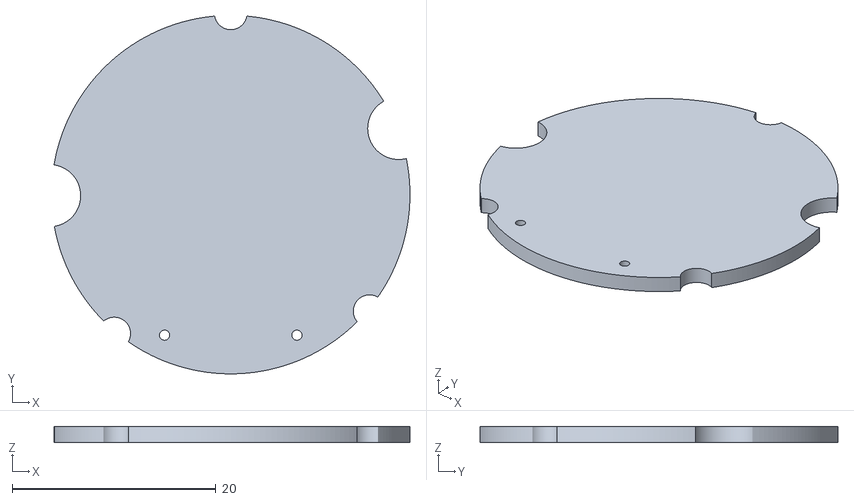
[picture p63: CAD file, 2026-09-08]
enclosure/a04/mechanism/thin-cell/90_unpowered_notched_board_gauge.stl
35.0 x 35.1 x 1.60
