Avinash1286/pendent/enclosure/aura-top-retainer.stl

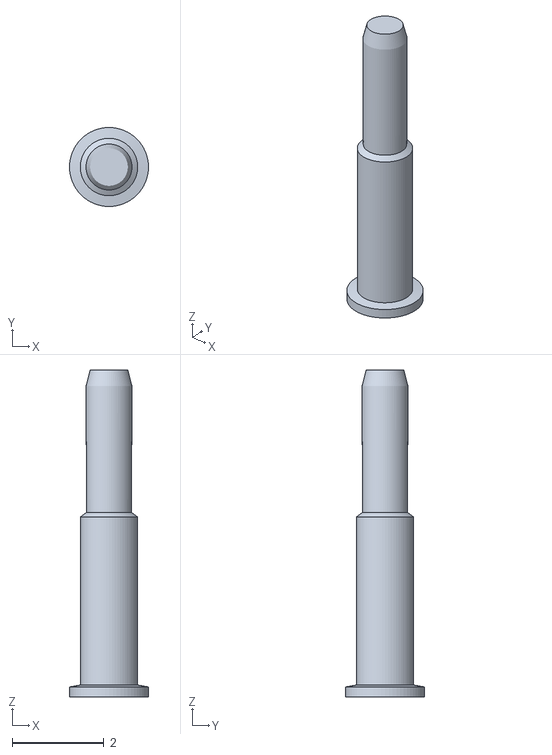
[picture p64: CAD file, 2026-09-07]
enclosure/aura-top-retainer.stl
1.72 x 1.72 x 7.12
