Avinash1286/pendent/enclosure/a04/mechanism/documented-pack/03_face_retainer.stl

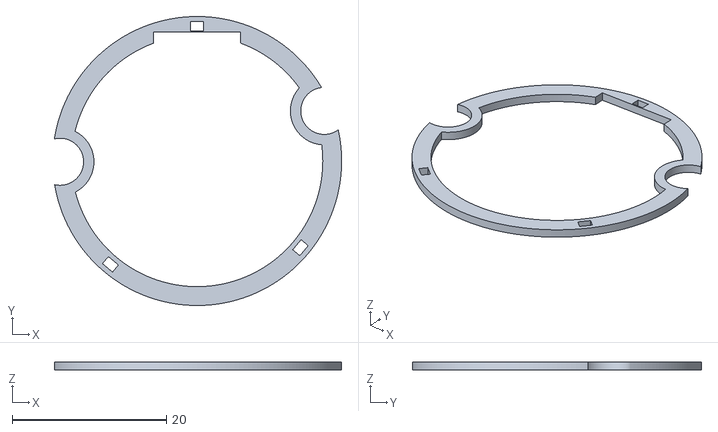
[picture p65: CAD file, 2026-09-08]
enclosure/a04/mechanism/documented-pack/03_face_retainer.stl
37.3 x 37.5 x 1.10
