Avinash1286/pendent/enclosure/aura-front-shell.stl

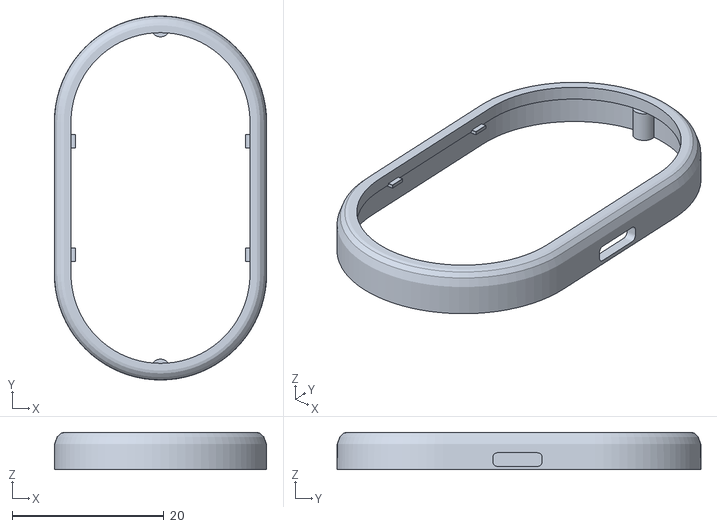
[picture p66: CAD file, 2026-09-07]
enclosure/aura-front-shell.stl
28.0 x 48.0 x 4.95
