Avinash1286/pendent/enclosure/a04/coupon/a04-wall-bail-card.stl

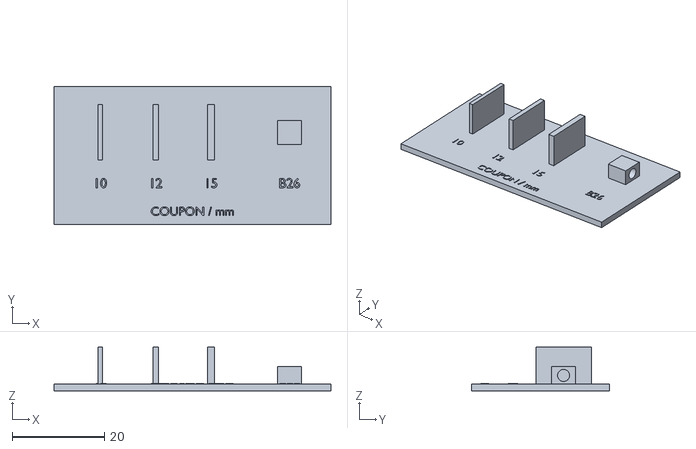
[picture p67: CAD file, 2026-09-08]
enclosure/a04/coupon/a04-wall-bail-card.stl
60.0 x 30.0 x 9.50
