Avinash1286/pendent/enclosure/a04/mechanism-m2/documented-pack/04_captive_face.stl

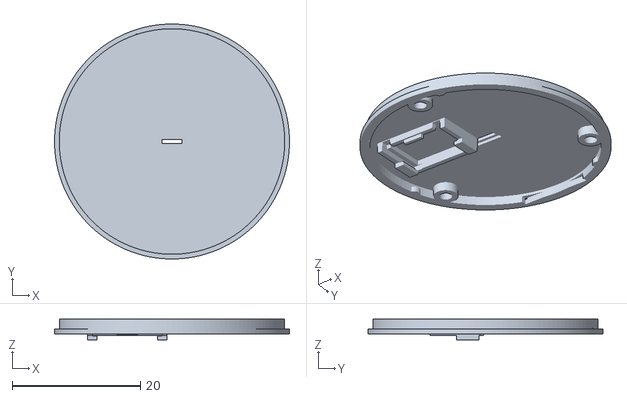
[picture p68: CAD file, 2026-09-09]
enclosure/a04/mechanism-m2/documented-pack/04_captive_face.stl
36.7 x 36.7 x 3.24
