Avinash1286/pendent/enclosure/a04/mechanism/thin-cell/91_unpowered_max_pack_gauge.stl

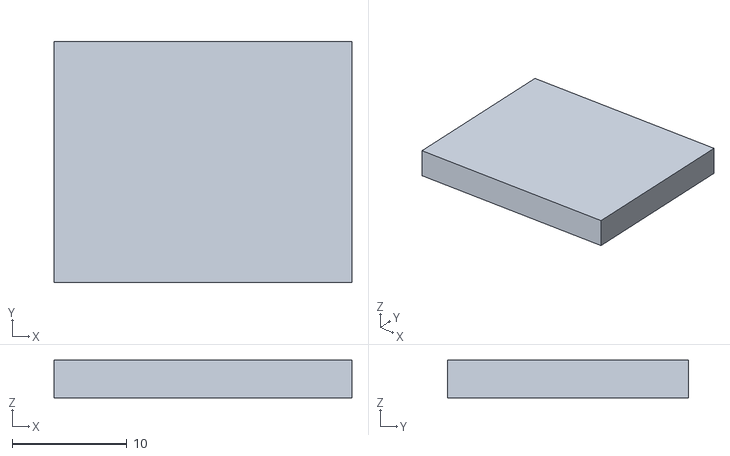
[picture p69: CAD file, 2026-09-08]
enclosure/a04/mechanism/thin-cell/91_unpowered_max_pack_gauge.stl
26.0 x 21.0 x 3.30
