Avinash1286/pendent/enclosure/aura-privacy-slider.stl

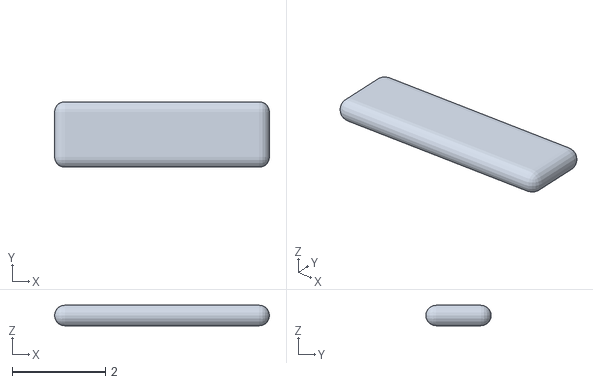
[picture p70: CAD file, 2026-09-07]
enclosure/aura-privacy-slider.stl
4.60 x 1.40 x 0.44
