Avinash1286/pendent/enclosure/a04/coupon/a04-face-gauge-35p2.stl

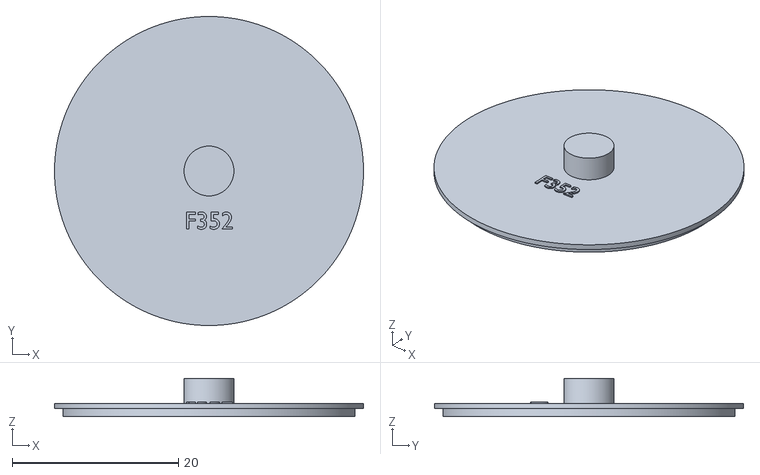
[picture p71: CAD file, 2026-09-08]
enclosure/a04/coupon/a04-face-gauge-35p2.stl
37.2 x 37.2 x 4.60
