Avinash1286/pendent/enclosure/a04/mechanism-m2/thin-cell/01_fixed_cup.stl

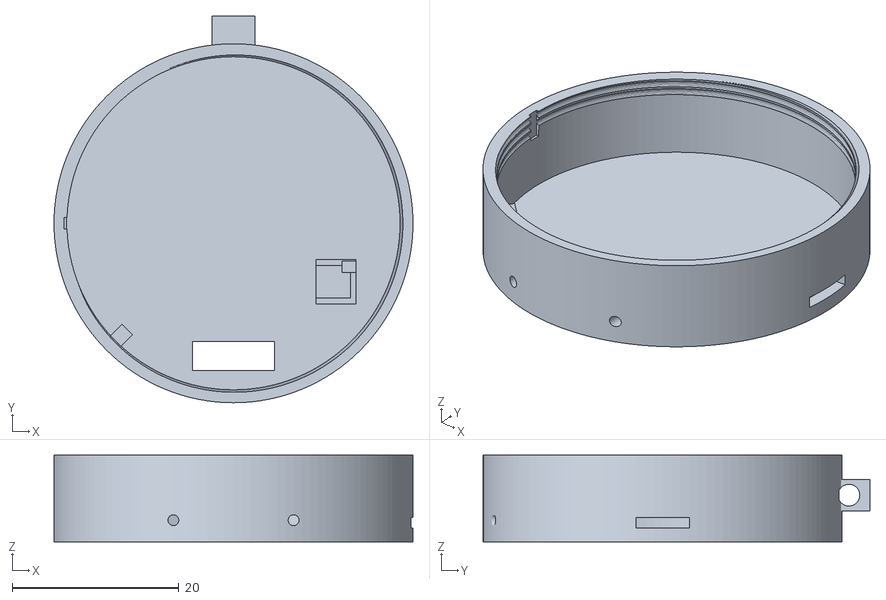
[picture p72: CAD file, 2026-09-09]
enclosure/a04/mechanism-m2/thin-cell/01_fixed_cup.stl
43.0 x 46.3 x 10.4
