Avinash1286/pendent/enclosure/a04/mechanism/documented-pack/08_cus22_privacy_fork.stl

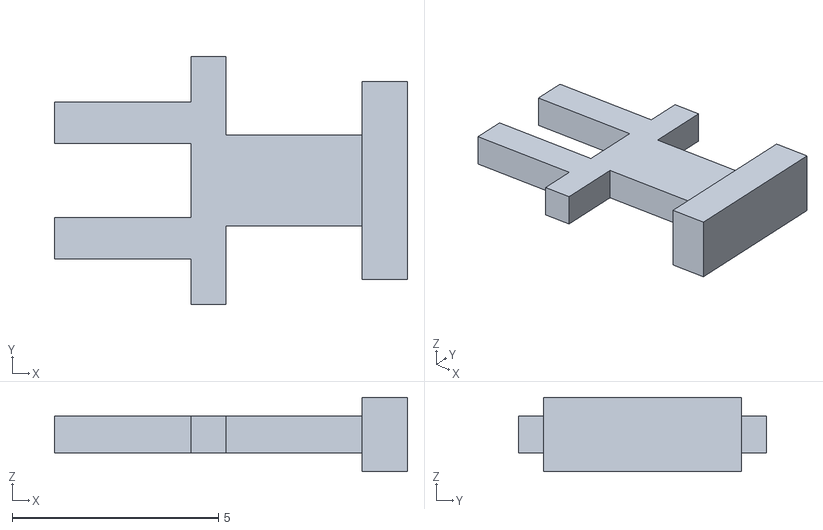
[picture p73: CAD file, 2026-09-08]
enclosure/a04/mechanism/documented-pack/08_cus22_privacy_fork.stl
8.55 x 6.00 x 1.80
