Avinash1286/pendent/enclosure/aura-record-face.stl

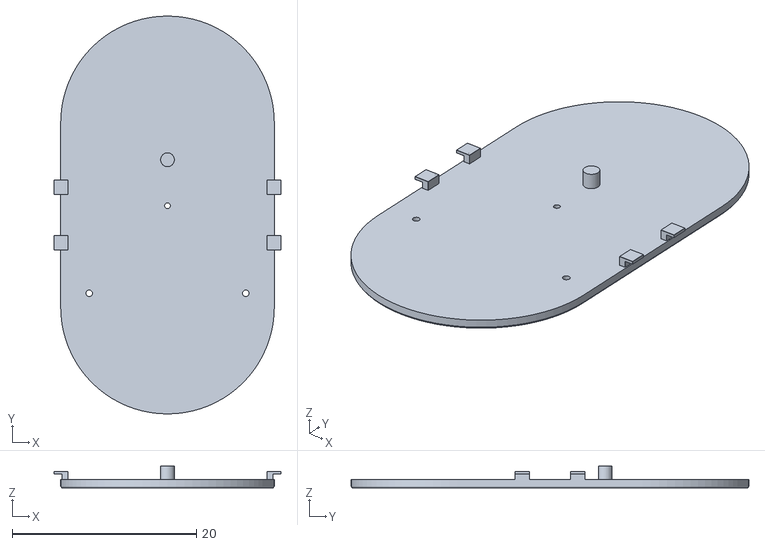
[picture p74: CAD file, 2026-09-07]
enclosure/aura-record-face.stl
24.6 x 43.2 x 2.38
