Avinash1286/pendent/enclosure/a04/coupon/a04-face-ring-r25.stl

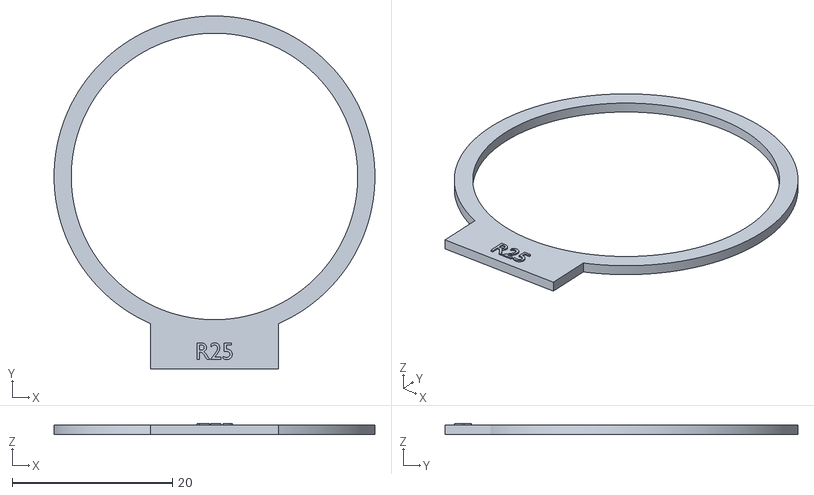
[picture p75: CAD file, 2026-09-08]
enclosure/a04/coupon/a04-face-ring-r25.stl
40.0 x 44.0 x 1.35
