Avinash1286/pendent/enclosure/a04/mechanism/documented-pack/10_dock_contact_access_carrier.stl

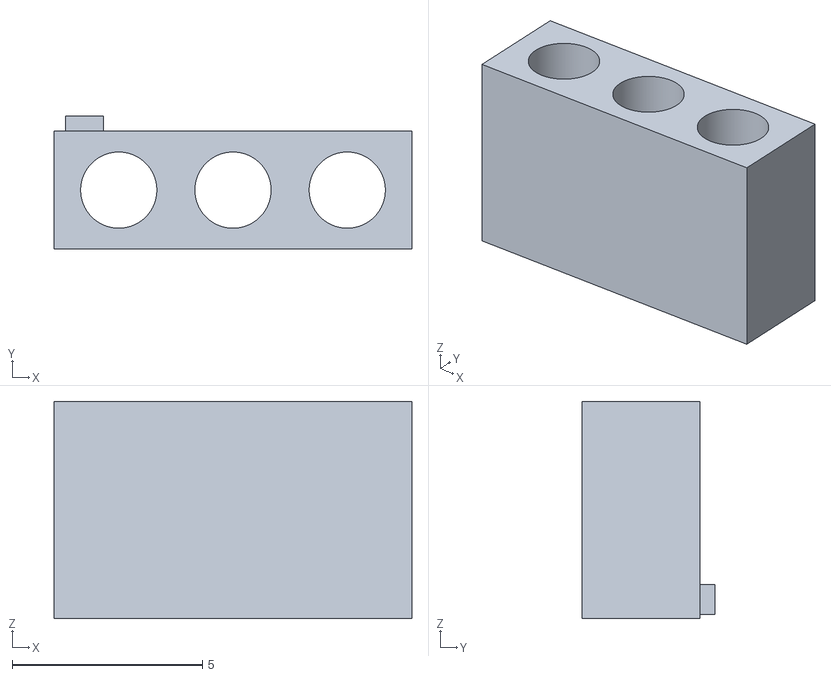
[picture p76: CAD file, 2026-09-08]
enclosure/a04/mechanism/documented-pack/10_dock_contact_access_carrier.stl
9.40 x 3.50 x 5.70
