Avinash1286/pendent/enclosure/a04/mechanism/thin-cell/09_acoustic_duct_right.stl

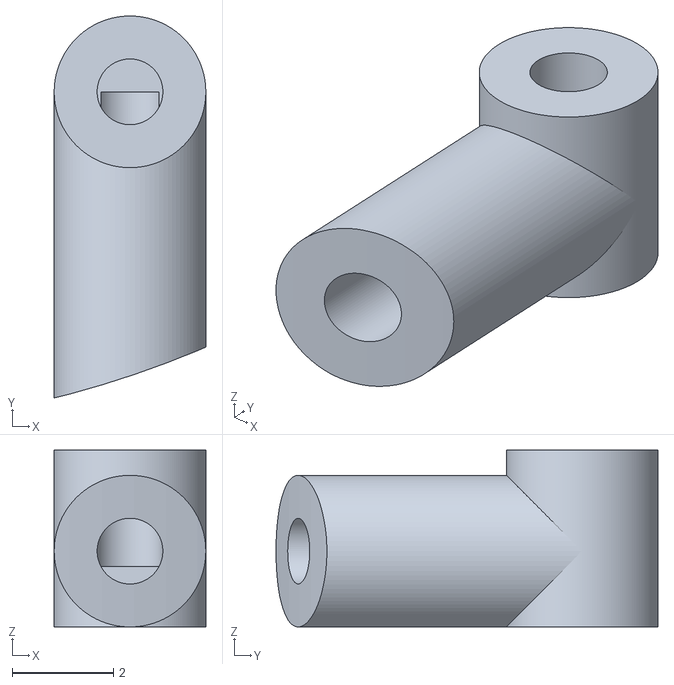
[picture p77: CAD file, 2026-09-08]
enclosure/a04/mechanism/thin-cell/09_acoustic_duct_right.stl
3.00 x 7.56 x 3.50
