Avinash1286/pendent/enclosure/aura-rear-shell.stl

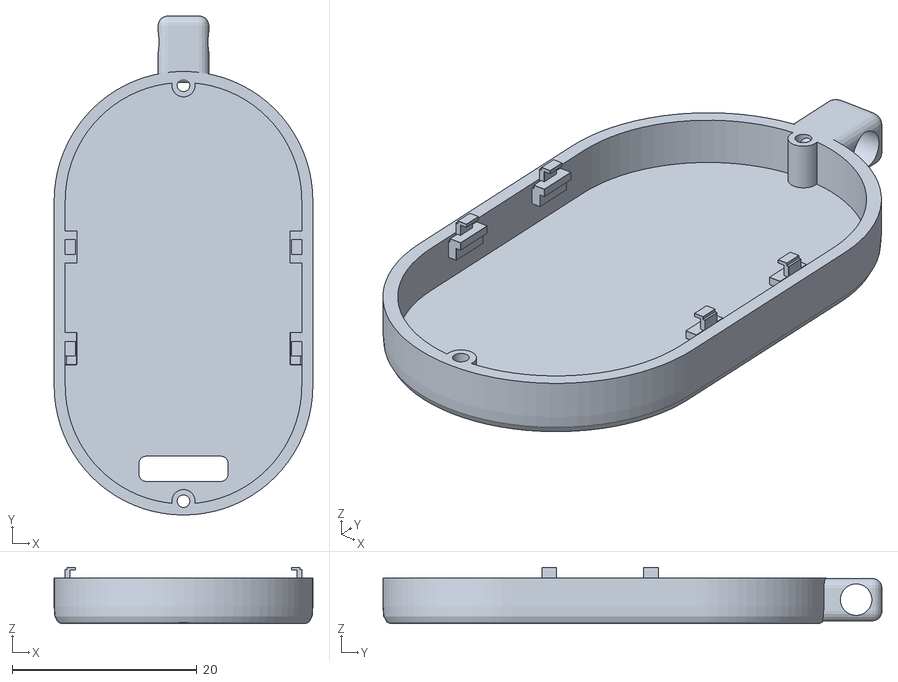
[picture p78: CAD file, 2026-09-07]
enclosure/aura-rear-shell.stl
28.0 x 54.0 x 6.10
