Avinash1286/pendent/enclosure/aura-fit-coupon.stl

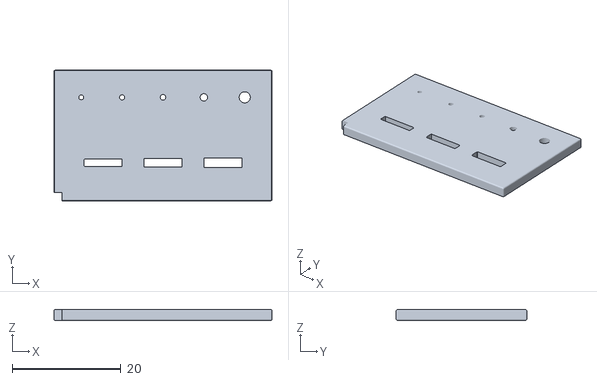
[picture p79: CAD file, 2026-09-07]
enclosure/aura-fit-coupon.stl
40.0 x 24.0 x 2.00
