Avinash1286/pendent/enclosure/a04/mechanism-m2/documented-pack/09_privacy_fork.stl

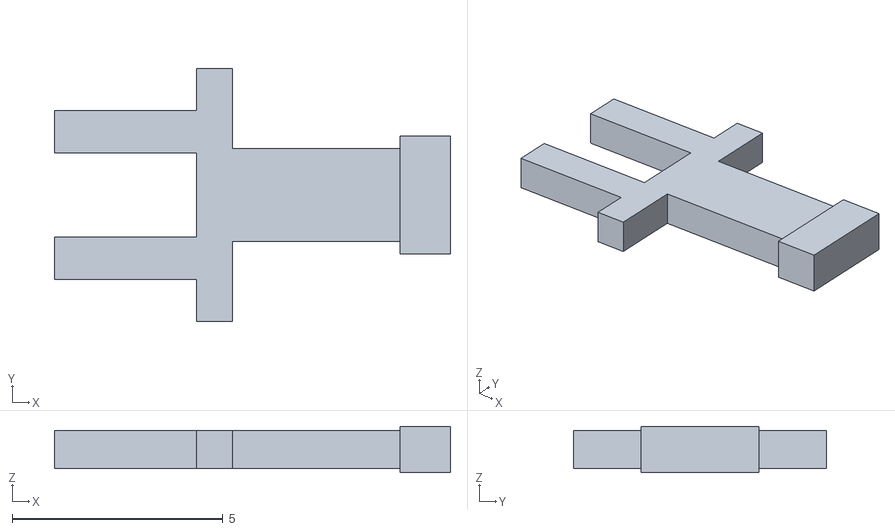
[picture p81: CAD file, 2026-09-09]
enclosure/a04/mechanism-m2/documented-pack/09_privacy_fork.stl
9.40 x 6.00 x 1.10
