Avinash1286/pendent/enclosure/a04/mechanism/documented-pack/04_fixed_diffuser_ring.stl

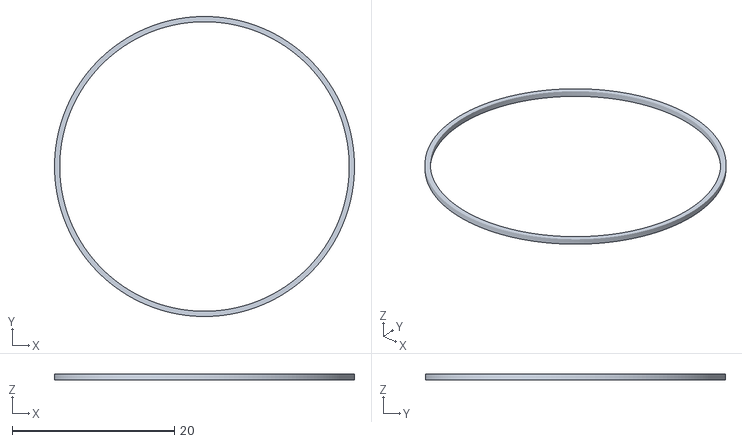
[picture p82: CAD file, 2026-09-08]
enclosure/a04/mechanism/documented-pack/04_fixed_diffuser_ring.stl
37.0 x 37.0 x 0.7
