Avinash1286/pendent/enclosure/a04/mechanism/thin-cell/02_captive_face_paddle.stl

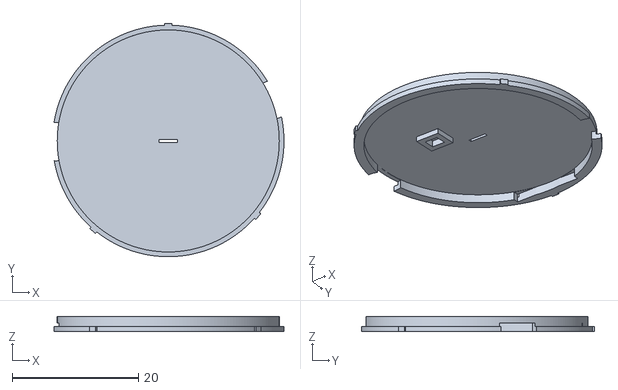
[picture p83: CAD file, 2026-09-08]
enclosure/a04/mechanism/thin-cell/02_captive_face_paddle.stl
36.5 x 37.0 x 2.35
