Avinash1286/pendent/enclosure/aura-record-button.stl

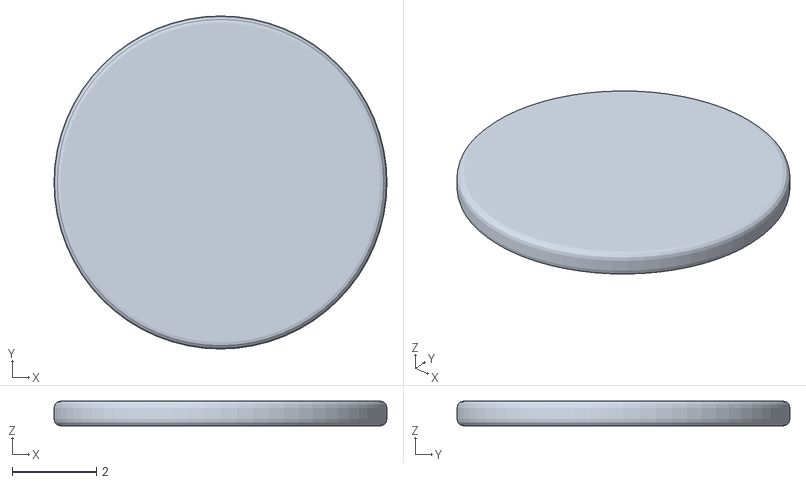
[picture p84: CAD file, 2026-09-07]
enclosure/aura-record-button.stl
7.92 x 7.92 x 0.59
