Avinash1286/pendent/enclosure/a04/mechanism-m2/thin-cell/10_privacy_keeper.stl

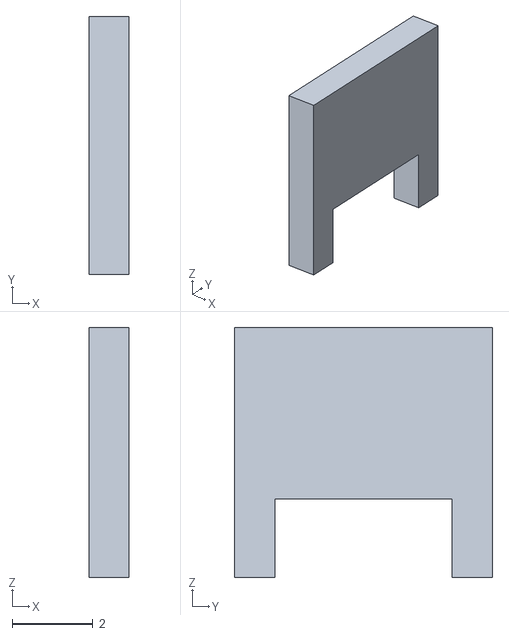
[picture p87: CAD file, 2026-09-09]
enclosure/a04/mechanism-m2/thin-cell/10_privacy_keeper.stl
1.00 x 6.40 x 6.20
