Avinash1286/pendent/enclosure/a04/mechanism/documented-pack/01_front_housing_with_bail.stl

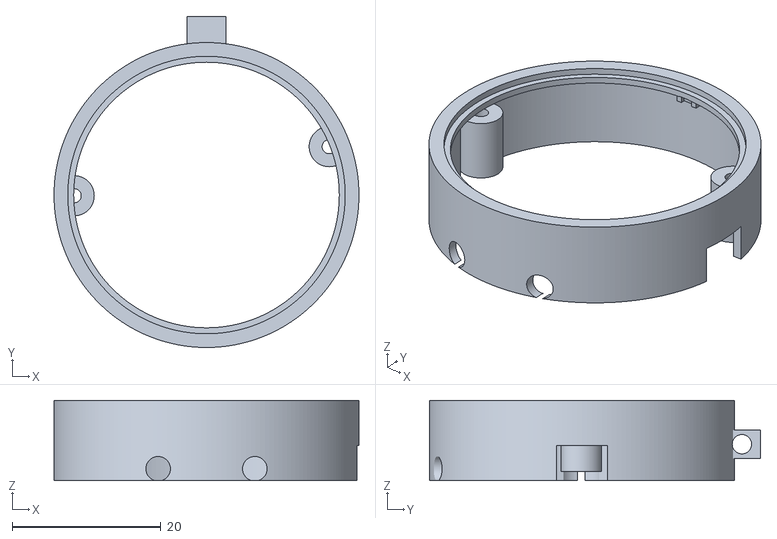
[picture p88: CAD file, 2026-09-08]
enclosure/a04/mechanism/documented-pack/01_front_housing_with_bail.stl
41.0 x 44.5 x 10.8
