Avinash1286/pendent/enclosure/a04/mechanism-m2/documented-pack/12_sensor_retainer.stl

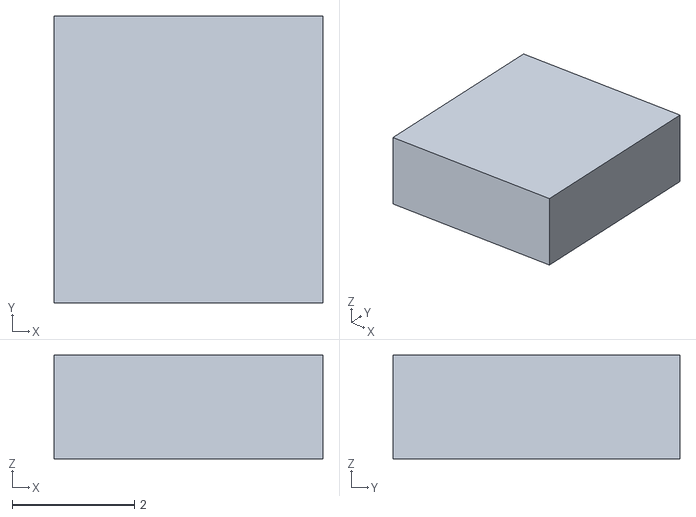
[picture p89: CAD file, 2026-09-09]
enclosure/a04/mechanism-m2/documented-pack/12_sensor_retainer.stl
4.40 x 4.70 x 1.70
