Avinash1286/pendent/enclosure/a04/mechanism/documented-pack/07_rear_cover_and_slider_keeper.stl

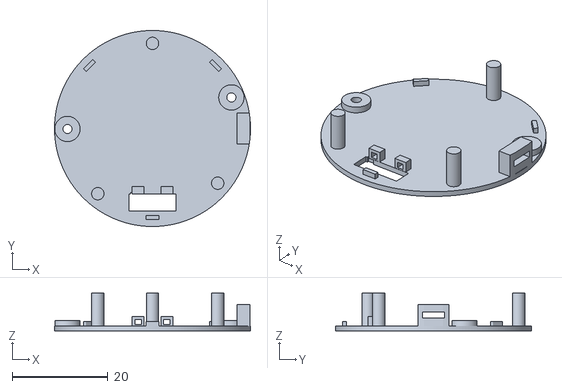
[picture p90: CAD file, 2026-09-08]
enclosure/a04/mechanism/documented-pack/07_rear_cover_and_slider_keeper.stl
41.0 x 41.0 x 7.90
