Avinash1286/pendent/enclosure/a04/mechanism-m2/documented-pack/91_unpowered_pack_gauge.stl

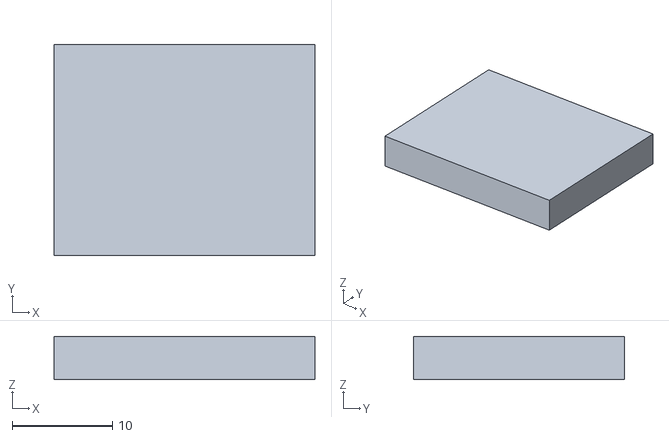
[picture p91: CAD file, 2026-09-09]
enclosure/a04/mechanism-m2/documented-pack/91_unpowered_pack_gauge.stl
26.0 x 21.0 x 4.30
