Avinash1286/pendent/enclosure/a04/mechanism-m2/thin-cell/02_threaded_bezel.stl

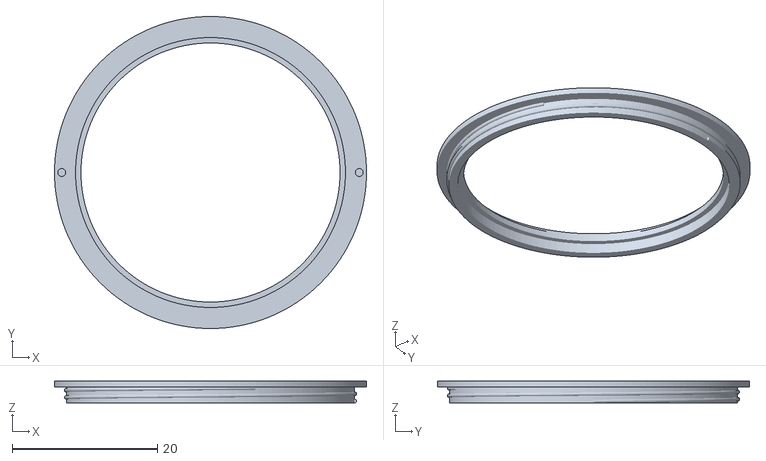
[picture p92: CAD file, 2026-09-09]
enclosure/a04/mechanism-m2/thin-cell/02_threaded_bezel.stl
43.0 x 43.0 x 3.00
