Avinash1286/pendent/enclosure/a04/mechanism/documented-pack/06_plunger_sizing_insert.stl

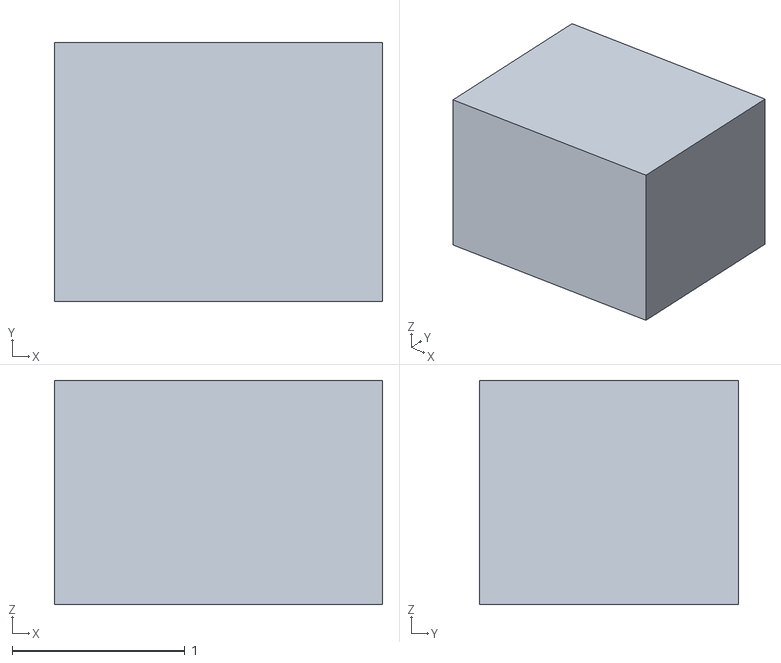
[picture p93: CAD file, 2026-09-08]
enclosure/a04/mechanism/documented-pack/06_plunger_sizing_insert.stl
1.90 x 1.50 x 1.30
