Avinash1286/pendent/enclosure/a04/mechanism-m2/documented-pack/05_flush_status_window.stl

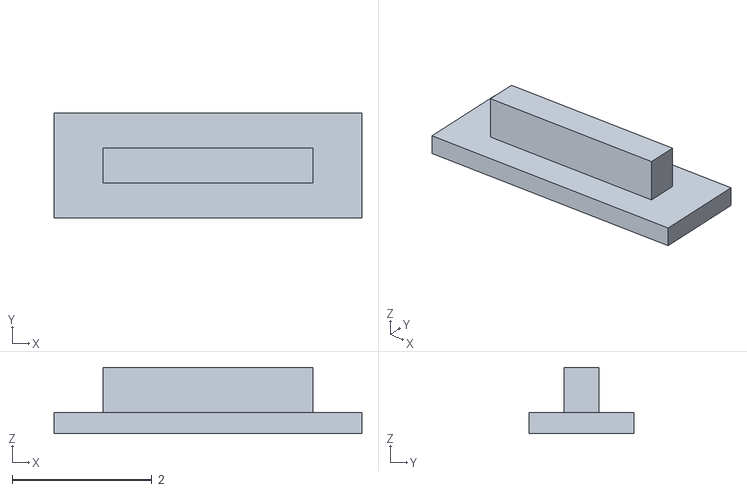
[picture p95: CAD file, 2026-09-09]
enclosure/a04/mechanism-m2/documented-pack/05_flush_status_window.stl
4.40 x 1.50 x 0.95
