Avinash1286/pendent/enclosure/a04/mechanism-m2/thin-cell/11_contact_access_carrier.stl

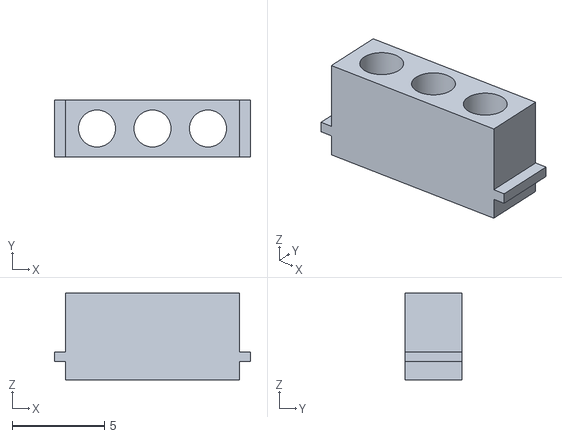
[picture p96: CAD file, 2026-09-09]
enclosure/a04/mechanism-m2/thin-cell/11_contact_access_carrier.stl
10.6 x 3.10 x 4.70
