Avinash1286/pendent/enclosure/a04/mechanism-m2/thin-cell/06_fixed_diffuser.stl

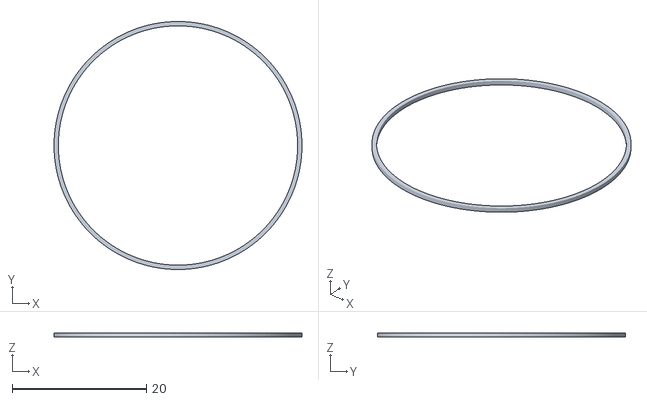
[picture p97: CAD file, 2026-09-09]
enclosure/a04/mechanism-m2/thin-cell/06_fixed_diffuser.stl
37.0 x 37.0 x 0.65
