Avinash1286/pendent/enclosure/a04/mechanism-m2/thin-cell/12_sensor_retainer.stl

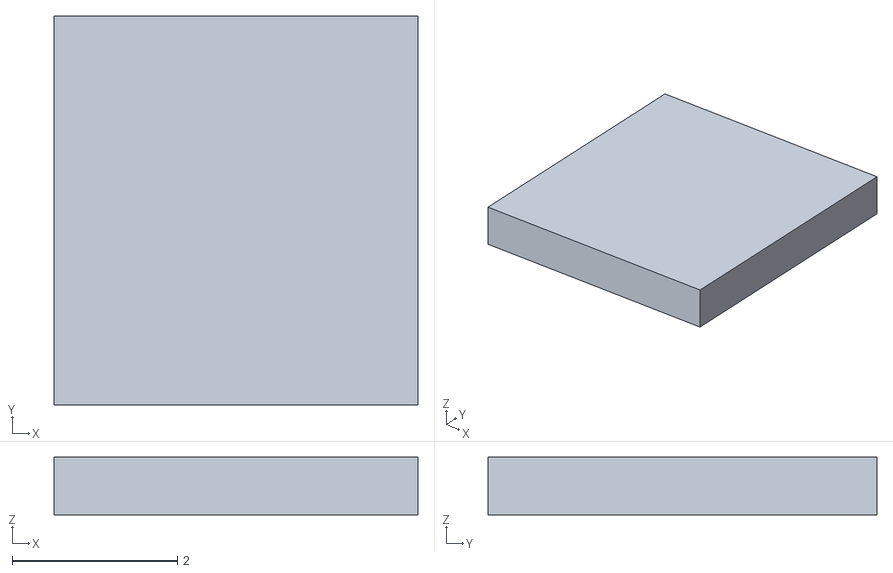
[picture p98: CAD file, 2026-09-09]
enclosure/a04/mechanism-m2/thin-cell/12_sensor_retainer.stl
4.40 x 4.70 x 0.7
