Avinash1286/pendent/firmware/a04/bench/verification/arm-build.txt

[1/7] Building C object CMakeFiles/app.dir/F_/circuit/firmware/a04/src/aura_journal.c.obj
F:/circuit/firmware/a04/src/aura_journal.c: In function 'allocation':
F:/circuit/firmware/a04/src/aura_journal.c:43:5: warning: this 'if' clause does not guard... [-Wmisleading-indentation]
   43 |     if(out)*out=id;return true;
      |     ^~
F:/circuit/firmware/a04/src/aura_journal.c:43:20: note: ...this statement, but the latter is misleadingly indented as if it were guarded by the 'if'
   43 |     if(out)*out=id;return true;
      |                    ^~~~~~
F:/circuit/firmware/a04/src/aura_journal.c: In function 'scan':
F:/circuit/firmware/a04/src/aura_journal.c:506:5: warning: this 'if' clause does not guard... [-Wmisleading-indentation]
  506 |     if(!r&&identity)*identity=walk.identity;return r;
      |     ^~
F:/circuit/firmware/a04/src/aura_journal.c:506:45: note: ...this statement, but the latter is misleadingly indented as if it were guarded by the 'if'
  506 |     if(!r&&identity)*identity=walk.identity;return r;
      |                                             ^~~~~~
[2/7] Linking C static library app\libapp.a
[3/7] Linking C executable zephyr\zephyr_pre0.elf
[4/7] Generating linker.cmd
[5/7] Generating isr_tables.c, isr_tables_vt.ld, isr_tables_swi.ld
[6/7] Building C object zephyr/CMakeFiles/zephyr_final.dir/isr_tables.c.obj
[7/7] Linking C executable zephyr\zephyr.elf
Memory region         Used Size  Region Size  %age Used
           FLASH:      257468 B         1 MB     24.55%
             RAM:      212104 B       256 KB     80.91%

        IDT_LIST:          0 GB        32 KB      0.00%

Generating files from F:/circuit/.tools/a04-bench/arm/zephyr/zephyr.elf for board: nrf52840dk
