Avinash1286/pendent/firmware/a04/radio/verification/attempts/attempt-02/arm-build.txt

[1/503] Building C object CMakeFiles/app.dir/src/aura_pairing_zephyr.c.obj
[2/503] Building C object CMakeFiles/app.dir/F_/circuit/firmware/a04/src/aura_session_auth.c.obj
[3/503] Building C object CMakeFiles/app.dir/src/main.c.obj
[4/503] Building C object CMakeFiles/app.dir/F_/circuit/firmware/a04/src/aura_opus.c.obj
[5/503] Building C object CMakeFiles/app.dir/F_/circuit/firmware/a04/src/aura_transfer.c.obj
[6/503] Building C object CMakeFiles/app.dir/F_/circuit/firmware/a04/src/aura_archive.c.obj
[7/503] Building C object CMakeFiles/app.dir/F_/circuit/firmware/a04/src/aura_recorder.c.obj
[8/503] Building C object CMakeFiles/app.dir/F_/circuit/firmware/a04/src/aura_journal.c.obj
F:/circuit/firmware/a04/src/aura_journal.c: In function 'allocation':
F:/circuit/firmware/a04/src/aura_journal.c:43:5: warning: this 'if' clause does not guard... [-Wmisleading-indentation]
   43 |     if(out)*out=id;return true;
      |     ^~
F:/circuit/firmware/a04/src/aura_journal.c:43:20: note: ...this statement, but the latter is misleadingly indented as if it were guarded by the 'if'
   43 |     if(out)*out=id;return true;
      |                    ^~~~~~
F:/circuit/firmware/a04/src/aura_journal.c: In function 'scan':
F:/circuit/firmware/a04/src/aura_journal.c:506:5: warning: this 'if' clause does not guard... [-Wmisleading-indentation]
  506 |     if(!r&&identity)*identity=walk.identity;return r;
      |     ^~
F:/circuit/firmware/a04/src/aura_journal.c:506:45: note: ...this statement, but the latter is misleadingly indented as if it were guarded by the 'if'
  506 |     if(!r&&identity)*identity=walk.identity;return r;
      |                                             ^~~~~~
[9/503] Building C object CMakeFiles/app.dir/F_/circuit/firmware/a04/src/aura_audio_zephyr.c.obj
F:/circuit/firmware/a04/src/aura_audio_zephyr.c: In function 'aura_audio_zephyr_init':
F:/circuit/firmware/a04/src/aura_audio_zephyr.c:53:13: warning: comparison is always false due to limited range of data type [-Wtype-limits]
   53 |         mix < AURA_AUDIO_FIRST || !device_is_ready(dmic) || !gpio_is_ready_dt(&mic))
      |             ^
[10/503] Building C object CMakeFiles/app.dir/F_/circuit/firmware/a04/src/aura_w25n01gv.c.obj
[11/503] Building C object CMakeFiles/app.dir/F_/circuit/firmware/a04/src/aura_w25n01gv_zephyr.c.obj
[12/503] Building C object CMakeFiles/app.dir/F_/circuit/firmware/a04/src/aura_control.c.obj
F:/circuit/firmware/a04/src/aura_control.c: In function 'scan':
F:/circuit/firmware/a04/src/aura_control.c:104:5: warning: this 'if' clause does not guard... [-Wmisleading-indentation]
  104 |     if(r)return r;if(bad)return AURA_NAND_BAD_BLOCK;
      |     ^~
F:/circuit/firmware/a04/src/aura_control.c:104:19: note: ...this statement, but the latter is misleadingly indented as if it were guarded by the 'if'
  104 |     if(r)return r;if(bad)return AURA_NAND_BAD_BLOCK;
      |                   ^~
F:/circuit/firmware/a04/src/aura_control.c: In function 'erase_inactive':
F:/circuit/firmware/a04/src/aura_control.c:209:5: warning: this 'if' clause does not guard... [-Wmisleading-indentation]
  209 |     if(r)return r;if(bad)return AURA_NAND_BAD_BLOCK;
      |     ^~
F:/circuit/firmware/a04/src/aura_control.c:209:19: note: ...this statement, but the latter is misleadingly indented as if it were guarded by the 'if'
  209 |     if(r)return r;if(bad)return AURA_NAND_BAD_BLOCK;
      |                   ^~
[13/503] Building C object CMakeFiles/app.dir/F_/circuit/firmware/a04/src/aura_release_auth.c.obj
[14/503] Building C object zephyr/CMakeFiles/zephyr.dir/lib/crc/crc32k_4_2_sw.c.obj
[15/503] Building C object zephyr/CMakeFiles/zephyr.dir/lib/crc/crc32c_sw.c.obj
[16/503] Building C object zephyr/CMakeFiles/zephyr.dir/lib/crc/crc32_sw.c.obj
[17/503] Building C object zephyr/CMakeFiles/zephyr.dir/lib/crc/crc24_sw.c.obj
[18/503] Building C object CMakeFiles/app.dir/F_/circuit/firmware/a04/src/aura_storage.c.obj
F:/circuit/firmware/a04/src/aura_storage.c: In function 'reload':
F:/circuit/firmware/a04/src/aura_storage.c:85:5: warning: this 'if' clause does not guard... [-Wmisleading-indentation]
   85 |     if(r)return fail(s,r);s->bytes=bytes;
      |     ^~
F:/circuit/firmware/a04/src/aura_storage.c:85:27: note: ...this statement, but the latter is misleadingly indented as if it were guarded by the 'if'
   85 |     if(r)return fail(s,r);s->bytes=bytes;
      |                           ^
[19/503] Building C object zephyr/CMakeFiles/zephyr.dir/lib/crc/crc16_sw.c.obj
[20/503] Building C object zephyr/CMakeFiles/zephyr.dir/lib/crc/crc8_sw.c.obj
[21/503] Building C object zephyr/CMakeFiles/zephyr.dir/lib/crc/crc7_sw.c.obj
[22/503] Building C object zephyr/CMakeFiles/zephyr.dir/lib/crc/crc4_sw.c.obj
[23/503] Building C object zephyr/CMakeFiles/zephyr.dir/lib/heap/heap.c.obj
[24/503] Building C object zephyr/CMakeFiles/zephyr.dir/lib/os/cbprintf_packaged.c.obj
[25/503] Building C object zephyr/CMakeFiles/zephyr.dir/lib/os/printk.c.obj
[26/503] Building C object zephyr/CMakeFiles/zephyr.dir/lib/os/clock.c.obj
[27/503] Building C object zephyr/CMakeFiles/zephyr.dir/lib/os/sem.c.obj
[28/503] Building C object zephyr/CMakeFiles/zephyr.dir/lib/os/thread_entry.c.obj
[29/503] Building C object zephyr/CMakeFiles/zephyr.dir/lib/os/assert.c.obj
[30/503] Building C object zephyr/CMakeFiles/zephyr.dir/lib/os/cbprintf_complete.c.obj
[31/503] Building C object zephyr/CMakeFiles/zephyr.dir/lib/utils/dec.c.obj
[32/503] Building C object zephyr/CMakeFiles/zephyr.dir/lib/utils/hex.c.obj
[33/503] Building C object zephyr/CMakeFiles/zephyr.dir/lib/utils/timeutil.c.obj
[34/503] Building C object zephyr/CMakeFiles/zephyr.dir/lib/utils/rb.c.obj
[35/503] Building C object zephyr/CMakeFiles/zephyr.dir/lib/utils/onoff.c.obj
[36/503] Building C object zephyr/CMakeFiles/zephyr.dir/lib/utils/bitarray.c.obj
[37/503] Building C object zephyr/CMakeFiles/zephyr.dir/lib/utils/ring_buffer.c.obj
[38/503] Building C object zephyr/CMakeFiles/zephyr.dir/lib/utils/notify.c.obj
[39/503] Building C object zephyr/CMakeFiles/zephyr.dir/lib/utils/last_section_id.c.obj
[40/503] Building C object zephyr/CMakeFiles/zephyr.dir/misc/generated/configs.c.obj
[41/503] Building C object zephyr/CMakeFiles/zephyr.dir/subsys/mem_mgmt/mem_attr.c.obj
[42/503] Building C object zephyr/CMakeFiles/zephyr.dir/subsys/fs/nvs/nvs.c.obj
[43/503] Building C object zephyr/CMakeFiles/zephyr.dir/subsys/storage/flash_map/flash_map.c.obj
[44/503] Building C object zephyr/CMakeFiles/zephyr.dir/subsys/storage/flash_map/flash_map_layout.c.obj
[45/503] Building C object zephyr/CMakeFiles/zephyr.dir/subsys/storage/flash_map/flash_map_default.c.obj
[46/503] Building C object zephyr/CMakeFiles/zephyr.dir/subsys/tracing/tracing_none.c.obj
[47/503] Building C object zephyr/CMakeFiles/zephyr.dir/subsys/settings/src/settings_store.c.obj
[48/503] Building C object zephyr/CMakeFiles/zephyr.dir/subsys/settings/src/settings.c.obj
[49/503] Building C object zephyr/CMakeFiles/zephyr.dir/subsys/settings/src/settings_init.c.obj
[50/503] Building C object zephyr/CMakeFiles/zephyr.dir/subsys/settings/src/settings_line.c.obj
[51/503] Building C object zephyr/CMakeFiles/zephyr.dir/subsys/settings/src/settings_nvs.c.obj
[52/503] Building C object zephyr/CMakeFiles/zephyr.dir/drivers/flash/flash_util.c.obj
[53/503] Generating linker_zephyr_pre0.cmd
[54/503] Building C object zephyr/CMakeFiles/zephyr_pre0.dir/misc/empty_file.c.obj
[55/503] Linking C static library zephyr\libzephyr.a
[56/503] Building C object zephyr/arch/common/CMakeFiles/arch__common.dir/sw_isr_common.c.obj
[57/503] Building C object zephyr/arch/common/CMakeFiles/isr_tables.dir/isr_tables.c.obj
[58/503] Linking C static library zephyr\arch\common\libisr_tables.a
[59/503] Linking C static library zephyr\arch\common\libarch__common.a
[60/503] Building C object zephyr/arch/arch/arm/core/CMakeFiles/arch__arm__core.dir/fatal.c.obj
[61/503] Building ASM object zephyr/arch/arch/arm/core/CMakeFiles/arch__arm__core.dir/nmi_on_reset.S.obj
[62/503] Building C object zephyr/arch/arch/arm/core/CMakeFiles/arch__arm__core.dir/nmi.c.obj
[63/503] Building C object zephyr/arch/arch/arm/core/CMakeFiles/arch__arm__core.dir/tls.c.obj
[64/503] Linking C static library zephyr\arch\arch\arm\core\libarch__arm__core.a
[65/503] Building C object zephyr/arch/arch/arm/core/cortex_m/CMakeFiles/arch__arm__core__cortex_m.dir/exc_exit.c.obj
[66/503] Building ASM object zephyr/arch/arch/arm/core/cortex_m/CMakeFiles/arch__arm__core__cortex_m.dir/fault_s.S.obj
[67/503] Building C object zephyr/arch/arch/arm/core/cortex_m/CMakeFiles/arch__arm__core__cortex_m.dir/fpu.c.obj
[68/503] Building C object zephyr/arch/arch/arm/core/cortex_m/CMakeFiles/arch__arm__core__cortex_m.dir/fault.c.obj
[69/503] Building ASM object zephyr/arch/arch/arm/core/cortex_m/CMakeFiles/arch__arm__core__cortex_m.dir/reset.S.obj
[70/503] Building C object zephyr/arch/arch/arm/core/cortex_m/CMakeFiles/arch__arm__core__cortex_m.dir/scb.c.obj
[71/503] Building ASM object zephyr/arch/arch/arm/core/cortex_m/CMakeFiles/arch__arm__core__cortex_m.dir/vector_table.S.obj
[72/503] Building C object zephyr/arch/arch/arm/core/cortex_m/CMakeFiles/arch__arm__core__cortex_m.dir/thread_abort.c.obj
[73/503] Building ASM object zephyr/arch/arch/arm/core/cortex_m/CMakeFiles/arch__arm__core__cortex_m.dir/swap_helper.S.obj
[74/503] Building C object zephyr/arch/arch/arm/core/cortex_m/CMakeFiles/arch__arm__core__cortex_m.dir/irq_manage.c.obj
[75/503] Building C object zephyr/arch/arch/arm/core/cortex_m/CMakeFiles/arch__arm__core__cortex_m.dir/prep_c.c.obj
[76/503] Building C object zephyr/arch/arch/arm/core/cortex_m/CMakeFiles/arch__arm__core__cortex_m.dir/thread.c.obj
[77/503] Building C object zephyr/arch/arch/arm/core/cortex_m/CMakeFiles/arch__arm__core__cortex_m.dir/cpu_idle.c.obj
[78/503] Building C object zephyr/arch/arch/arm/core/cortex_m/CMakeFiles/arch__arm__core__cortex_m.dir/irq_init.c.obj
[79/503] Building ASM object zephyr/arch/arch/arm/core/cortex_m/CMakeFiles/arch__arm__core__cortex_m.dir/__aeabi_read_tp.S.obj
[80/503] Building C object zephyr/arch/arch/arm/core/cortex_m/CMakeFiles/arch__arm__core__cortex_m.dir/isr_wrapper.c.obj
[81/503] Linking C static library zephyr\arch\arch\arm\core\cortex_m\libarch__arm__core__cortex_m.a
[82/503] Building C object zephyr/arch/arch/arm/core/mpu/CMakeFiles/arch__arm__core__mpu.dir/arm_core_mpu.c.obj
[83/503] Building C object zephyr/arch/arch/arm/core/mpu/CMakeFiles/arch__arm__core__mpu.dir/arm_mpu_regions.c.obj
[84/503] Building C object zephyr/arch/arch/arm/core/mpu/CMakeFiles/arch__arm__core__mpu.dir/arm_mpu.c.obj
[85/503] Linking C static library zephyr\arch\arch\arm\core\mpu\libarch__arm__core__mpu.a
[86/503] Building C object zephyr/lib/libc/picolibc/CMakeFiles/lib__libc__picolibc.dir/assert.c.obj
[87/503] Building C object zephyr/lib/libc/picolibc/CMakeFiles/lib__libc__picolibc.dir/cbprintf.c.obj
[88/503] Building C object zephyr/lib/libc/picolibc/CMakeFiles/lib__libc__picolibc.dir/chk_fail.c.obj
[89/503] Building C object zephyr/lib/libc/picolibc/CMakeFiles/lib__libc__picolibc.dir/errno_wrap.c.obj
[90/503] Building C object zephyr/lib/libc/picolibc/CMakeFiles/lib__libc__picolibc.dir/exit.c.obj
[91/503] Building C object zephyr/lib/libc/picolibc/CMakeFiles/lib__libc__picolibc.dir/locks.c.obj
[92/503] Building C object zephyr/lib/libc/picolibc/CMakeFiles/lib__libc__picolibc.dir/stdio.c.obj
[93/503] Building C object zephyr/lib/libc/common/CMakeFiles/lib__libc__common.dir/source/stdlib/abort.c.obj
[94/503] Linking C static library zephyr\lib\libc\picolibc\liblib__libc__picolibc.a
[95/503] Building C object zephyr/lib/libc/common/CMakeFiles/lib__libc__common.dir/source/time/time.c.obj
[96/503] Building C object zephyr/lib/libc/common/CMakeFiles/lib__libc__common.dir/source/stdlib/malloc.c.obj
[97/503] Linking C static library zephyr\lib\libc\common\liblib__libc__common.a
[98/503] Building C object zephyr/lib/net_buf/CMakeFiles/lib__net_buf.dir/buf.c.obj
[99/503] Building C object zephyr/lib/net_buf/CMakeFiles/lib__net_buf.dir/buf_simple.c.obj
[100/503] Building C object zephyr/soc/soc/nrf52840/CMakeFiles/soc__nordic.dir/validate_base_addresses.c.obj
[101/503] Linking C static library zephyr\lib\net_buf\liblib__net_buf.a
[102/503] Building C object zephyr/soc/soc/nrf52840/CMakeFiles/soc__nordic.dir/validate_binding_headers.c.obj
[103/503] Building C object zephyr/soc/soc/nrf52840/CMakeFiles/soc__nordic.dir/validate_enabled_instances.c.obj
[104/503] Building C object zephyr/soc/soc/nrf52840/CMakeFiles/soc__nordic.dir/nrf52/soc.c.obj
[105/503] Building C object zephyr/soc/soc/nrf52840/CMakeFiles/soc__nordic.dir/common/reboot.c.obj
[106/503] Linking C static library zephyr\soc\soc\nrf52840\libsoc__nordic.a
[107/503] Building C object zephyr/subsys/random/CMakeFiles/subsys__random.dir/random_entropy_device.c.obj
[108/503] Building C object zephyr/subsys/bluetooth/common/CMakeFiles/subsys__bluetooth__common.dir/addr.c.obj
[109/503] Linking C static library zephyr\subsys\random\libsubsys__random.a
[110/503] Building C object zephyr/subsys/bluetooth/common/CMakeFiles/subsys__bluetooth__common.dir/dummy.c.obj
[111/503] Building C object zephyr/subsys/bluetooth/common/CMakeFiles/subsys__bluetooth__common.dir/bt_str.c.obj
[112/503] Building C object zephyr/subsys/bluetooth/common/CMakeFiles/subsys__bluetooth__common.dir/rpa.c.obj
[113/503] Linking C static library zephyr\subsys\bluetooth\common\libsubsys__bluetooth__common.a
[114/503] Building C object zephyr/subsys/bluetooth/host/CMakeFiles/subsys__bluetooth__host.dir/settings.c.obj
[115/503] Building C object zephyr/subsys/bluetooth/host/CMakeFiles/subsys__bluetooth__host.dir/long_wq.c.obj
[116/503] Building C object zephyr/subsys/bluetooth/host/CMakeFiles/subsys__bluetooth__host.dir/uuid.c.obj
[117/503] Building C object zephyr/subsys/bluetooth/host/CMakeFiles/subsys__bluetooth__host.dir/addr.c.obj
[118/503] Building C object zephyr/subsys/bluetooth/host/CMakeFiles/subsys__bluetooth__host.dir/buf.c.obj
[119/503] Building C object zephyr/subsys/bluetooth/host/CMakeFiles/subsys__bluetooth__host.dir/data.c.obj
[120/503] Building C object zephyr/subsys/bluetooth/host/CMakeFiles/subsys__bluetooth__host.dir/hci_common.c.obj
[121/503] Building C object zephyr/subsys/bluetooth/host/CMakeFiles/subsys__bluetooth__host.dir/id.c.obj
[122/503] Building C object zephyr/subsys/bluetooth/host/CMakeFiles/subsys__bluetooth__host.dir/hci_core.c.obj
[123/503] Building C object zephyr/subsys/bluetooth/host/CMakeFiles/subsys__bluetooth__host.dir/adv.c.obj
[124/503] Building C object zephyr/subsys/bluetooth/host/CMakeFiles/subsys__bluetooth__host.dir/ecc.c.obj
[125/503] Building C object zephyr/subsys/bluetooth/host/CMakeFiles/subsys__bluetooth__host.dir/l2cap.c.obj
[126/503] Building C object zephyr/subsys/bluetooth/host/CMakeFiles/subsys__bluetooth__host.dir/conn.c.obj
[127/503] Building C object zephyr/subsys/bluetooth/host/CMakeFiles/subsys__bluetooth__host.dir/att.c.obj
[128/503] Building C object zephyr/subsys/bluetooth/host/CMakeFiles/subsys__bluetooth__host.dir/gatt.c.obj
[129/503] Building C object zephyr/subsys/bluetooth/host/CMakeFiles/subsys__bluetooth__host.dir/keys.c.obj
[130/503] Building C object zephyr/subsys/bluetooth/crypto/CMakeFiles/subsys__bluetooth__crypto.dir/bt_crypto.c.obj
[131/503] Building C object zephyr/subsys/bluetooth/host/CMakeFiles/subsys__bluetooth__host.dir/smp.c.obj
[132/503] Linking C static library zephyr\subsys\bluetooth\host\libsubsys__bluetooth__host.a
[133/503] Building C object zephyr/subsys/bluetooth/crypto/CMakeFiles/subsys__bluetooth__crypto.dir/bt_crypto_psa.c.obj
[134/503] Building C object zephyr/subsys/bluetooth/controller/CMakeFiles/subsys__bluetooth__controller.dir/util/mem.c.obj
[135/503] Linking C static library zephyr\subsys\bluetooth\crypto\libsubsys__bluetooth__crypto.a
[136/503] Building C object zephyr/subsys/bluetooth/controller/CMakeFiles/subsys__bluetooth__controller.dir/util/memq.c.obj
[137/503] Building C object zephyr/subsys/bluetooth/controller/CMakeFiles/subsys__bluetooth__controller.dir/util/mayfly.c.obj
[138/503] Building C object zephyr/subsys/bluetooth/controller/CMakeFiles/subsys__bluetooth__controller.dir/util/dbuf.c.obj
[139/503] Building C object zephyr/subsys/bluetooth/controller/CMakeFiles/subsys__bluetooth__controller.dir/util/util.c.obj
[140/503] Building C object zephyr/subsys/bluetooth/controller/CMakeFiles/subsys__bluetooth__controller.dir/ll_sw/ll_feat.c.obj
[141/503] Building C object zephyr/subsys/bluetooth/controller/CMakeFiles/subsys__bluetooth__controller.dir/ticker/ticker.c.obj
[142/503] Building C object zephyr/subsys/bluetooth/controller/CMakeFiles/subsys__bluetooth__controller.dir/ll_sw/ll_tx_pwr.c.obj
[143/503] Building C object zephyr/subsys/bluetooth/controller/CMakeFiles/subsys__bluetooth__controller.dir/ll_sw/ll_addr.c.obj
[144/503] Building C object zephyr/subsys/bluetooth/controller/CMakeFiles/subsys__bluetooth__controller.dir/ll_sw/lll_common.c.obj
[145/503] Building C object zephyr/subsys/bluetooth/controller/CMakeFiles/subsys__bluetooth__controller.dir/ll_sw/ull.c.obj
[146/503] Building C object zephyr/subsys/bluetooth/controller/CMakeFiles/subsys__bluetooth__controller.dir/hci/hci_driver.c.obj
[147/503] Building C object zephyr/subsys/bluetooth/controller/CMakeFiles/subsys__bluetooth__controller.dir/hci/hci.c.obj
[148/503] Building C object zephyr/subsys/bluetooth/controller/CMakeFiles/subsys__bluetooth__controller.dir/ll_sw/ull_adv.c.obj
[149/503] Building C object zephyr/subsys/bluetooth/controller/CMakeFiles/subsys__bluetooth__controller.dir/ll_sw/ull_llcp_enc.c.obj
[150/503] Building C object zephyr/subsys/bluetooth/controller/CMakeFiles/subsys__bluetooth__controller.dir/ll_sw/ull_conn.c.obj
[151/503] Building C object zephyr/subsys/bluetooth/controller/CMakeFiles/subsys__bluetooth__controller.dir/ll_sw/ull_llcp_phy.c.obj
[152/503] Building C object zephyr/subsys/bluetooth/controller/CMakeFiles/subsys__bluetooth__controller.dir/ll_sw/ull_tx_queue.c.obj
[153/503] Building C object zephyr/subsys/bluetooth/controller/CMakeFiles/subsys__bluetooth__controller.dir/ll_sw/ull_llcp_common.c.obj
[154/503] Building C object zephyr/subsys/bluetooth/controller/CMakeFiles/subsys__bluetooth__controller.dir/ll_sw/ull_llcp.c.obj
[155/503] Building C object zephyr/subsys/bluetooth/controller/CMakeFiles/subsys__bluetooth__controller.dir/ll_sw/ull_llcp_local.c.obj
[156/503] Building C object zephyr/subsys/bluetooth/controller/CMakeFiles/subsys__bluetooth__controller.dir/ll_sw/ull_llcp_pdu.c.obj
[157/503] Building C object zephyr/subsys/bluetooth/controller/CMakeFiles/subsys__bluetooth__controller.dir/ll_sw/ull_llcp_chmu.c.obj
[158/503] Building C object zephyr/subsys/bluetooth/controller/CMakeFiles/subsys__bluetooth__controller.dir/ll_sw/ull_llcp_conn_upd.c.obj
[159/503] Building C object zephyr/subsys/bluetooth/controller/CMakeFiles/subsys__bluetooth__controller.dir/ll_sw/ull_llcp_remote.c.obj
[160/503] Building C object zephyr/subsys/bluetooth/controller/CMakeFiles/subsys__bluetooth__controller.dir/ll_sw/ull_peripheral.c.obj
[161/503] Building C object zephyr/subsys/bluetooth/controller/CMakeFiles/subsys__bluetooth__controller.dir/ll_sw/ull_chan.c.obj
[162/503] Building C object zephyr/subsys/bluetooth/controller/CMakeFiles/subsys__bluetooth__controller.dir/ll_sw/lll_chan.c.obj
[163/503] Building C object zephyr/subsys/bluetooth/controller/CMakeFiles/subsys__bluetooth__controller.dir/crypto/crypto.c.obj
[164/503] Building C object zephyr/subsys/bluetooth/controller/CMakeFiles/subsys__bluetooth__controller.dir/ll_sw/ull_filter.c.obj
[165/503] Building C object zephyr/subsys/bluetooth/controller/CMakeFiles/subsys__bluetooth__controller.dir/flash/soc_flash_nrf_ticker.c.obj
[166/503] Linking C static library zephyr\subsys\bluetooth\controller\libsubsys__bluetooth__controller.a
[167/503] Building C object zephyr/subsys/bluetooth/controller/ll_sw/nordic/CMakeFiles/subsys__bluetooth__controller__ll_sw__nordic.dir/lll/lll.c.obj
[168/503] Building C object zephyr/subsys/bluetooth/controller/ll_sw/nordic/CMakeFiles/subsys__bluetooth__controller__ll_sw__nordic.dir/lll/lll_clock.c.obj
[169/503] Building C object zephyr/subsys/bluetooth/controller/ll_sw/nordic/CMakeFiles/subsys__bluetooth__controller__ll_sw__nordic.dir/lll/lll_adv.c.obj
[170/503] Building C object zephyr/subsys/bluetooth/controller/ll_sw/nordic/CMakeFiles/subsys__bluetooth__controller__ll_sw__nordic.dir/lll/lll_conn.c.obj
[171/503] Building C object zephyr/subsys/bluetooth/controller/ll_sw/nordic/CMakeFiles/subsys__bluetooth__controller__ll_sw__nordic.dir/lll/lll_peripheral.c.obj
[172/503] Building C object zephyr/subsys/bluetooth/controller/ll_sw/nordic/CMakeFiles/subsys__bluetooth__controller__ll_sw__nordic.dir/hci/hci_vendor.c.obj
[173/503] Building C object zephyr/subsys/bluetooth/controller/ll_sw/nordic/CMakeFiles/subsys__bluetooth__controller__ll_sw__nordic.dir/hal/nrf5/cntr.c.obj
[174/503] Building C object zephyr/subsys/bluetooth/controller/ll_sw/nordic/CMakeFiles/subsys__bluetooth__controller__ll_sw__nordic.dir/hal/nrf5/mayfly.c.obj
[175/503] Building C object zephyr/subsys/bluetooth/controller/ll_sw/nordic/CMakeFiles/subsys__bluetooth__controller__ll_sw__nordic.dir/hal/nrf5/ticker.c.obj
[176/503] Building C object zephyr/subsys/bluetooth/controller/ll_sw/nordic/CMakeFiles/subsys__bluetooth__controller__ll_sw__nordic.dir/hal/nrf5/radio/radio.c.obj
[177/503] Building C object zephyr/subsys/bluetooth/controller/ll_sw/nordic/CMakeFiles/subsys__bluetooth__controller__ll_sw__nordic.dir/hal/nrf5/ecb.c.obj
[178/503] Linking C static library zephyr\subsys\bluetooth\controller\ll_sw\nordic\libsubsys__bluetooth__controller__ll_sw__nordic.a
[179/503] Building C object zephyr/drivers/clock_control/CMakeFiles/drivers__clock_control.dir/clock_control_nrf.c.obj
[180/503] Building C object zephyr/drivers/console/CMakeFiles/drivers__console.dir/uart_console.c.obj
[181/503] Linking C static library zephyr\drivers\clock_control\libdrivers__clock_control.a
[182/503] Linking C static library zephyr\drivers\console\libdrivers__console.a
[183/503] Building C object zephyr/drivers/entropy/CMakeFiles/drivers__entropy.dir/entropy_nrf5.c.obj
[184/503] Building C object zephyr/drivers/flash/CMakeFiles/drivers__flash.dir/jesd216.c.obj
[185/503] Linking C static library zephyr\drivers\entropy\libdrivers__entropy.a
[186/503] Building C object zephyr/drivers/flash/CMakeFiles/drivers__flash.dir/flash_page_layout.c.obj
[187/503] Building C object zephyr/drivers/flash/CMakeFiles/drivers__flash.dir/soc_flash_nrf.c.obj
[188/503] Building C object zephyr/drivers/flash/CMakeFiles/drivers__flash.dir/nrf_qspi_nor.c.obj
[189/503] Linking C static library zephyr\drivers\flash\libdrivers__flash.a
[190/503] Building C object zephyr/drivers/hwinfo/CMakeFiles/drivers__hwinfo.dir/hwinfo_weak_impl.c.obj
[191/503] Building C object zephyr/drivers/gpio/CMakeFiles/drivers__gpio.dir/gpio_nrfx.c.obj
[192/503] Linking C static library zephyr\drivers\gpio\libdrivers__gpio.a
[193/503] Building C object zephyr/drivers/hwinfo/CMakeFiles/drivers__hwinfo.dir/hwinfo_nrf.c.obj
[194/503] Linking C static library zephyr\drivers\hwinfo\libdrivers__hwinfo.a
[195/503] Building C object zephyr/drivers/pinctrl/CMakeFiles/drivers__pinctrl.dir/common.c.obj
[196/503] Building C object zephyr/drivers/pinctrl/CMakeFiles/drivers__pinctrl.dir/pinctrl_nrf.c.obj
[197/503] Linking C static library zephyr\drivers\pinctrl\libdrivers__pinctrl.a
[198/503] Building C object zephyr/drivers/spi/CMakeFiles/drivers__spi.dir/spi_nrfx_spim.c.obj
[199/503] Building C object zephyr/drivers/serial/CMakeFiles/drivers__serial.dir/uart_nrfx_uarte.c.obj
[200/503] Linking C static library zephyr\drivers\serial\libdrivers__serial.a
[201/503] Building C object zephyr/drivers/timer/CMakeFiles/drivers__timer.dir/sys_clock_init.c.obj
[202/503] Building C object zephyr/drivers/spi/CMakeFiles/drivers__spi.dir/spi_nrfx_common.c.obj
[203/503] Linking C static library zephyr\drivers\spi\libdrivers__spi.a
[204/503] Building C object zephyr/drivers/timer/CMakeFiles/drivers__timer.dir/nrf_rtc_timer.c.obj
[205/503] Linking C static library zephyr\drivers\timer\libdrivers__timer.a
[206/503] Building C object modules/hal_nordic/nrfx/CMakeFiles/modules__hal_nordic__nrfx.dir/F_/circuit/.tools/zephyr/modules/hal/nordic/nrfx/mdk/system_nrf52840.c.obj
[207/503] Building C object modules/hal_nordic/nrfx/CMakeFiles/modules__hal_nordic__nrfx.dir/nrfx_glue.c.obj
[208/503] Building C object modules/hal_nordic/nrfx/CMakeFiles/modules__hal_nordic__nrfx.dir/F_/circuit/.tools/zephyr/modules/hal/nordic/nrfx/helpers/nrfx_flag32_allocator.c.obj
[209/503] Building C object modules/hal_nordic/nrfx/CMakeFiles/modules__hal_nordic__nrfx.dir/F_/circuit/.tools/zephyr/modules/hal/nordic/nrfx/helpers/nrfx_gppi_dppi.c.obj
[210/503] Building C object modules/hal_nordic/nrfx/CMakeFiles/modules__hal_nordic__nrfx.dir/F_/circuit/.tools/zephyr/modules/hal/nordic/nrfx/helpers/nrfx_ram_ctrl.c.obj
[211/503] Building C object modules/hal_nordic/nrfx/CMakeFiles/modules__hal_nordic__nrfx.dir/F_/circuit/.tools/zephyr/modules/hal/nordic/nrfx/helpers/nrfx_gppi_ppi.c.obj
[212/503] Building C object modules/hal_nordic/nrfx/CMakeFiles/modules__hal_nordic__nrfx.dir/F_/circuit/.tools/zephyr/modules/hal/nordic/nrfx/drivers/src/nrfx_clock.c.obj
[213/503] Building C object modules/hal_nordic/nrfx/CMakeFiles/modules__hal_nordic__nrfx.dir/F_/circuit/.tools/zephyr/modules/hal/nordic/nrfx/drivers/src/nrfx_nvmc.c.obj
[214/503] Building C object modules/hal_nordic/nrfx/CMakeFiles/modules__hal_nordic__nrfx.dir/F_/circuit/.tools/zephyr/modules/hal/nordic/nrfx/drivers/src/nrfx_pdm.c.obj
[215/503] Building C object modules/hal_nordic/nrfx/CMakeFiles/modules__hal_nordic__nrfx.dir/F_/circuit/.tools/zephyr/modules/hal/nordic/nrfx/drivers/src/nrfx_gpiote.c.obj
[216/503] Building C object modules/hal_nordic/nrfx/CMakeFiles/modules__hal_nordic__nrfx.dir/F_/circuit/.tools/zephyr/modules/hal/nordic/nrfx/drivers/src/nrfx_ppi.c.obj
[217/503] Building C object modules/hal_nordic/nrfx/CMakeFiles/modules__hal_nordic__nrfx.dir/F_/circuit/.tools/zephyr/modules/hal/nordic/nrfx/drivers/src/nrfx_qspi.c.obj
[218/503] Building C object modules/mbedtls/CMakeFiles/mbedTLSBase.dir/F_/circuit/.tools/zephyr/modules/crypto/mbedtls/library/aes.c.obj
[219/503] Building C object modules/mbedtls/CMakeFiles/mbedTLSBase.dir/F_/circuit/.tools/zephyr/modules/crypto/mbedtls/library/aesni.c.obj
[220/503] Building C object modules/mbedtls/CMakeFiles/mbedTLSBase.dir/F_/circuit/.tools/zephyr/modules/crypto/mbedtls/library/aria.c.obj
[221/503] Building C object modules/mbedtls/CMakeFiles/mbedTLSBase.dir/F_/circuit/.tools/zephyr/modules/crypto/mbedtls/library/asn1parse.c.obj
[222/503] Building C object modules/hal_nordic/nrfx/CMakeFiles/modules__hal_nordic__nrfx.dir/F_/circuit/.tools/zephyr/modules/hal/nordic/nrfx/drivers/src/nrfx_spim.c.obj
[223/503] Building C object modules/mbedtls/CMakeFiles/mbedTLSBase.dir/F_/circuit/.tools/zephyr/modules/crypto/mbedtls/library/asn1write.c.obj
[224/503] Linking C static library modules\hal_nordic\nrfx\libmodules__hal_nordic__nrfx.a
[225/503] Building C object modules/mbedtls/CMakeFiles/mbedTLSBase.dir/F_/circuit/.tools/zephyr/modules/crypto/mbedtls/library/base64.c.obj
[226/503] Building C object modules/mbedtls/CMakeFiles/mbedTLSBase.dir/F_/circuit/.tools/zephyr/modules/crypto/mbedtls/library/bignum_core.c.obj
[227/503] Building C object modules/mbedtls/CMakeFiles/mbedTLSBase.dir/F_/circuit/.tools/zephyr/modules/crypto/mbedtls/library/bignum_mod_raw.c.obj
[228/503] Building C object modules/mbedtls/CMakeFiles/mbedTLSBase.dir/F_/circuit/.tools/zephyr/modules/crypto/mbedtls/library/bignum_mod.c.obj
[229/503] Building C object modules/mbedtls/CMakeFiles/mbedTLSBase.dir/F_/circuit/.tools/zephyr/modules/crypto/mbedtls/library/bignum.c.obj
[230/503] Building C object modules/mbedtls/CMakeFiles/mbedTLSBase.dir/F_/circuit/.tools/zephyr/modules/crypto/mbedtls/library/camellia.c.obj
[231/503] Building C object modules/mbedtls/CMakeFiles/mbedTLSBase.dir/F_/circuit/.tools/zephyr/modules/crypto/mbedtls/library/block_cipher.c.obj
[232/503] Building C object modules/mbedtls/CMakeFiles/mbedTLSBase.dir/F_/circuit/.tools/zephyr/modules/crypto/mbedtls/library/ccm.c.obj
[233/503] Building C object modules/mbedtls/CMakeFiles/mbedTLSBase.dir/F_/circuit/.tools/zephyr/modules/crypto/mbedtls/library/chacha20.c.obj
[234/503] Building C object modules/mbedtls/CMakeFiles/mbedTLSBase.dir/F_/circuit/.tools/zephyr/modules/crypto/mbedtls/library/chachapoly.c.obj
[235/503] Building C object modules/mbedtls/CMakeFiles/mbedTLSBase.dir/F_/circuit/.tools/zephyr/modules/crypto/mbedtls/library/cipher_wrap.c.obj
[236/503] Building C object modules/mbedtls/CMakeFiles/mbedTLSBase.dir/F_/circuit/.tools/zephyr/modules/crypto/mbedtls/library/cmac.c.obj
[237/503] Building C object modules/mbedtls/CMakeFiles/mbedTLSBase.dir/F_/circuit/.tools/zephyr/modules/crypto/mbedtls/library/cipher.c.obj
[238/503] Building C object modules/mbedtls/CMakeFiles/mbedTLSBase.dir/F_/circuit/.tools/zephyr/modules/crypto/mbedtls/library/constant_time.c.obj
[239/503] Building C object modules/mbedtls/CMakeFiles/mbedTLSBase.dir/F_/circuit/.tools/zephyr/modules/crypto/mbedtls/library/debug.c.obj
[240/503] Building C object modules/mbedtls/CMakeFiles/mbedTLSBase.dir/F_/circuit/.tools/zephyr/modules/crypto/mbedtls/library/ctr_drbg.c.obj
[241/503] Building C object modules/mbedtls/CMakeFiles/mbedTLSBase.dir/F_/circuit/.tools/zephyr/modules/crypto/mbedtls/library/des.c.obj
[242/503] Building C object modules/mbedtls/CMakeFiles/mbedTLSBase.dir/F_/circuit/.tools/zephyr/modules/crypto/mbedtls/library/dhm.c.obj
[243/503] Building C object modules/mbedtls/CMakeFiles/mbedTLSBase.dir/F_/circuit/.tools/zephyr/modules/crypto/mbedtls/library/ecdh.c.obj
[244/503] Building C object modules/mbedtls/CMakeFiles/mbedTLSBase.dir/F_/circuit/.tools/zephyr/modules/crypto/mbedtls/library/ecdsa.c.obj
[245/503] Building C object modules/mbedtls/CMakeFiles/mbedTLSBase.dir/F_/circuit/.tools/zephyr/modules/crypto/mbedtls/library/ecjpake.c.obj
[246/503] Building C object modules/mbedtls/CMakeFiles/mbedTLSBase.dir/F_/circuit/.tools/zephyr/modules/crypto/mbedtls/library/ecp_curves_new.c.obj
[247/503] Building C object modules/mbedtls/CMakeFiles/mbedTLSBase.dir/F_/circuit/.tools/zephyr/modules/crypto/mbedtls/library/ecp_curves.c.obj
[248/503] Building C object modules/mbedtls/CMakeFiles/mbedTLSBase.dir/F_/circuit/.tools/zephyr/modules/crypto/mbedtls/library/ecp.c.obj
[249/503] Building C object modules/mbedtls/CMakeFiles/mbedTLSBase.dir/F_/circuit/.tools/zephyr/modules/crypto/mbedtls/library/entropy_poll.c.obj
[250/503] Building C object modules/mbedtls/CMakeFiles/mbedTLSBase.dir/F_/circuit/.tools/zephyr/modules/crypto/mbedtls/library/entropy.c.obj
[251/503] Building C object modules/mbedtls/CMakeFiles/mbedTLSBase.dir/F_/circuit/.tools/zephyr/modules/crypto/mbedtls/library/error.c.obj
[252/503] Building C object modules/mbedtls/CMakeFiles/mbedTLSBase.dir/F_/circuit/.tools/zephyr/modules/crypto/mbedtls/library/gcm.c.obj
[253/503] Building C object modules/mbedtls/CMakeFiles/mbedTLSBase.dir/F_/circuit/.tools/zephyr/modules/crypto/mbedtls/library/hkdf.c.obj
[254/503] Building C object modules/mbedtls/CMakeFiles/mbedTLSBase.dir/F_/circuit/.tools/zephyr/modules/crypto/mbedtls/library/hmac_drbg.c.obj
[255/503] Building C object modules/mbedtls/CMakeFiles/mbedTLSBase.dir/F_/circuit/.tools/zephyr/modules/crypto/mbedtls/library/lmots.c.obj
[256/503] Building C object modules/mbedtls/CMakeFiles/mbedTLSBase.dir/F_/circuit/.tools/zephyr/modules/crypto/mbedtls/library/lms.c.obj
[257/503] Building C object modules/mbedtls/CMakeFiles/mbedTLSBase.dir/F_/circuit/.tools/zephyr/modules/crypto/mbedtls/library/md.c.obj
[258/503] Building C object modules/mbedtls/CMakeFiles/mbedTLSBase.dir/F_/circuit/.tools/zephyr/modules/crypto/mbedtls/library/md5.c.obj
[259/503] Building C object modules/mbedtls/CMakeFiles/mbedTLSBase.dir/F_/circuit/.tools/zephyr/modules/crypto/mbedtls/library/mps_reader.c.obj
[260/503] Building C object modules/mbedtls/CMakeFiles/mbedTLSBase.dir/F_/circuit/.tools/zephyr/modules/crypto/mbedtls/library/memory_buffer_alloc.c.obj
[261/503] Building C object modules/mbedtls/CMakeFiles/mbedTLSBase.dir/F_/circuit/.tools/zephyr/modules/crypto/mbedtls/library/mps_trace.c.obj
[262/503] Building C object modules/mbedtls/CMakeFiles/mbedTLSBase.dir/F_/circuit/.tools/zephyr/modules/crypto/mbedtls/library/nist_kw.c.obj
[263/503] Building C object modules/mbedtls/CMakeFiles/mbedTLSBase.dir/F_/circuit/.tools/zephyr/modules/crypto/mbedtls/library/oid.c.obj
[264/503] Building C object modules/mbedtls/CMakeFiles/mbedTLSBase.dir/F_/circuit/.tools/zephyr/modules/crypto/mbedtls/library/padlock.c.obj
[265/503] Building C object modules/mbedtls/CMakeFiles/mbedTLSBase.dir/F_/circuit/.tools/zephyr/modules/crypto/mbedtls/library/platform.c.obj
[266/503] Building C object modules/mbedtls/CMakeFiles/mbedTLSBase.dir/F_/circuit/.tools/zephyr/modules/crypto/mbedtls/library/platform_util.c.obj
[267/503] Building C object modules/mbedtls/CMakeFiles/mbedTLSBase.dir/F_/circuit/.tools/zephyr/modules/crypto/mbedtls/library/poly1305.c.obj
[268/503] Building C object modules/mbedtls/CMakeFiles/mbedTLSBase.dir/F_/circuit/.tools/zephyr/modules/crypto/mbedtls/library/ripemd160.c.obj
[269/503] Building C object modules/mbedtls/CMakeFiles/mbedTLSBase.dir/F_/circuit/.tools/zephyr/modules/crypto/mbedtls/library/psa_util.c.obj
[270/503] Building C object modules/mbedtls/CMakeFiles/mbedTLSBase.dir/F_/circuit/.tools/zephyr/modules/crypto/mbedtls/library/rsa_alt_helpers.c.obj
[271/503] Building C object modules/mbedtls/CMakeFiles/mbedTLSBase.dir/F_/circuit/.tools/zephyr/modules/crypto/mbedtls/library/rsa.c.obj
[272/503] Building C object modules/mbedtls/CMakeFiles/mbedTLSBase.dir/F_/circuit/.tools/zephyr/modules/crypto/mbedtls/library/sha1.c.obj
[273/503] Building C object modules/mbedtls/CMakeFiles/mbedTLSBase.dir/F_/circuit/.tools/zephyr/modules/crypto/mbedtls/library/sha512.c.obj
[274/503] Building C object modules/mbedtls/CMakeFiles/mbedTLSBase.dir/F_/circuit/.tools/zephyr/modules/crypto/mbedtls/library/sha256.c.obj
[275/503] Building C object modules/mbedtls/CMakeFiles/mbedTLSBase.dir/F_/circuit/.tools/zephyr/modules/crypto/mbedtls/library/sha3.c.obj
[276/503] Building C object modules/mbedtls/CMakeFiles/mbedTLSBase.dir/F_/circuit/.tools/zephyr/modules/crypto/mbedtls/library/threading.c.obj
[277/503] Building C object modules/mbedtls/CMakeFiles/mbedTLSBase.dir/F_/circuit/.tools/zephyr/modules/crypto/mbedtls/library/timing.c.obj
[278/503] Building C object modules/mbedtls/CMakeFiles/mbedTLSBase.dir/F_/circuit/.tools/zephyr/modules/crypto/mbedtls/library/version_features.c.obj
[279/503] Building C object modules/mbedtls/CMakeFiles/mbedTLSBase.dir/F_/circuit/.tools/zephyr/modules/crypto/mbedtls/library/version.c.obj
[280/503] Building C object modules/mbedtls/CMakeFiles/mbedTLSBase.dir/zephyr_init.c.obj
[281/503] Building C object modules/mbedtls/CMakeFiles/mbedTLSBase.dir/zephyr_entropy.c.obj
[282/503] Building C object modules/mbedtls/CMakeFiles/mbedTLSCrypto.dir/F_/circuit/.tools/zephyr/modules/crypto/mbedtls/library/psa_crypto_aead.c.obj
[283/503] Linking C static library modules\mbedtls\libmbedTLSBase.a
[284/503] Building C object modules/mbedtls/CMakeFiles/mbedTLSCrypto.dir/F_/circuit/.tools/zephyr/modules/crypto/mbedtls/library/psa_crypto_cipher.c.obj
[285/503] Building C object modules/mbedtls/CMakeFiles/mbedTLSCrypto.dir/F_/circuit/.tools/zephyr/modules/crypto/mbedtls/library/psa_crypto_driver_wrappers_no_static.c.obj
[286/503] Building C object modules/mbedtls/CMakeFiles/mbedTLSCrypto.dir/F_/circuit/.tools/zephyr/modules/crypto/mbedtls/library/psa_crypto_ecp.c.obj
[287/503] Building C object modules/mbedtls/CMakeFiles/mbedTLSCrypto.dir/F_/circuit/.tools/zephyr/modules/crypto/mbedtls/library/psa_crypto_ffdh.c.obj
[288/503] Building C object modules/mbedtls/CMakeFiles/mbedTLSCrypto.dir/F_/circuit/.tools/zephyr/modules/crypto/mbedtls/library/psa_crypto_hash.c.obj
[289/503] Building C object modules/mbedtls/CMakeFiles/mbedTLSCrypto.dir/F_/circuit/.tools/zephyr/modules/crypto/mbedtls/library/psa_crypto_mac.c.obj
[290/503] Building C object modules/mbedtls/CMakeFiles/mbedTLSCrypto.dir/F_/circuit/.tools/zephyr/modules/crypto/mbedtls/library/psa_crypto_pake.c.obj
[291/503] Building C object modules/mbedtls/CMakeFiles/mbedTLSCrypto.dir/F_/circuit/.tools/zephyr/modules/crypto/mbedtls/library/psa_crypto_rsa.c.obj
[292/503] Building C object modules/mbedtls/CMakeFiles/mbedTLSCrypto.dir/F_/circuit/.tools/zephyr/modules/crypto/mbedtls/library/psa_crypto_se.c.obj
[293/503] Building C object modules/mbedtls/CMakeFiles/mbedTLSCrypto.dir/F_/circuit/.tools/zephyr/modules/crypto/mbedtls/library/psa_crypto_storage.c.obj
[294/503] Building C object modules/mbedtls/CMakeFiles/mbedTLSCrypto.dir/F_/circuit/.tools/zephyr/modules/crypto/mbedtls/library/psa_its_file.c.obj
[295/503] Building C object modules/mbedtls/CMakeFiles/mbedTLSCrypto.dir/F_/circuit/.tools/zephyr/modules/crypto/mbedtls/library/psa_crypto_client.c.obj
[296/503] Building C object modules/mbedtls/CMakeFiles/mbedTLSCrypto.dir/F_/circuit/.tools/zephyr/modules/crypto/mbedtls/library/psa_crypto_slot_management.c.obj
[297/503] Building C object modules/mbedtls/CMakeFiles/mbedTLSCrypto.dir/F_/circuit/.tools/zephyr/modules/crypto/mbedtls/3rdparty/p256-m/p256-m_driver_entrypoints.c.obj
[298/503] Building C object modules/mbedtls/CMakeFiles/mbedTLSCrypto.dir/F_/circuit/.tools/zephyr/modules/crypto/mbedtls/3rdparty/p256-m/p256-m/p256-m.c.obj
[299/503] Building C object modules/mbedtls/CMakeFiles/mbedTLSCrypto.dir/F_/circuit/.tools/zephyr/modules/crypto/mbedtls/library/pem.c.obj
[300/503] Building C object modules/mbedtls/CMakeFiles/mbedTLSCrypto.dir/F_/circuit/.tools/zephyr/modules/crypto/mbedtls/library/pkcs12.c.obj
[301/503] Building C object modules/mbedtls/CMakeFiles/mbedTLSCrypto.dir/F_/circuit/.tools/zephyr/modules/crypto/mbedtls/library/pkcs5.c.obj
[302/503] Building C object modules/mbedtls/CMakeFiles/mbedTLSCrypto.dir/F_/circuit/.tools/zephyr/modules/crypto/mbedtls/library/psa_crypto.c.obj
[303/503] Building C object modules/mbedtls/CMakeFiles/mbedTLSCrypto.dir/F_/circuit/.tools/zephyr/modules/crypto/mbedtls/library/pkparse.c.obj
[304/503] Building C object modules/mbedtls/CMakeFiles/mbedTLSCrypto.dir/F_/circuit/.tools/zephyr/modules/crypto/mbedtls/library/pkwrite.c.obj
[305/503] Building C object modules/mbedtls/CMakeFiles/mbedTLSCrypto.dir/F_/circuit/.tools/zephyr/modules/crypto/mbedtls/library/pk.c.obj
[306/503] Building C object modules/mbedtls/CMakeFiles/mbedTLSCrypto.dir/F_/circuit/.tools/zephyr/modules/crypto/mbedtls/library/pk_ecc.c.obj
[307/503] Building C object modules/mbedtls/CMakeFiles/mbedTLSCrypto.dir/F_/circuit/.tools/zephyr/modules/crypto/mbedtls/library/pk_wrap.c.obj
[308/503] Building C object modules/mbedtls/CMakeFiles/mbedTLSX509.dir/F_/circuit/.tools/zephyr/modules/crypto/mbedtls/library/x509.c.obj
[309/503] Linking C static library modules\mbedtls\libmbedTLSCrypto.a
[310/503] Building C object modules/mbedtls/CMakeFiles/mbedTLSX509.dir/F_/circuit/.tools/zephyr/modules/crypto/mbedtls/library/x509_create.c.obj
[311/503] Building C object modules/mbedtls/CMakeFiles/mbedTLSX509.dir/F_/circuit/.tools/zephyr/modules/crypto/mbedtls/library/x509_crl.c.obj
[312/503] Building C object modules/mbedtls/CMakeFiles/mbedTLSX509.dir/F_/circuit/.tools/zephyr/modules/crypto/mbedtls/library/x509_crt.c.obj
[313/503] Building C object modules/mbedtls/CMakeFiles/mbedTLSX509.dir/F_/circuit/.tools/zephyr/modules/crypto/mbedtls/library/x509_csr.c.obj
[314/503] Building C object modules/mbedtls/CMakeFiles/mbedTLSX509.dir/F_/circuit/.tools/zephyr/modules/crypto/mbedtls/library/x509write_crt.c.obj
[315/503] Building C object modules/mbedtls/CMakeFiles/mbedTLSX509.dir/F_/circuit/.tools/zephyr/modules/crypto/mbedtls/library/x509write_csr.c.obj
[316/503] Building C object modules/mbedtls/CMakeFiles/mbedTLSX509.dir/F_/circuit/.tools/zephyr/modules/crypto/mbedtls/library/x509write.c.obj
[317/503] Building C object modules/mbedtls/CMakeFiles/modules__mbedtls.dir/F_/circuit/.tools/zephyr/modules/crypto/mbedtls/library/net_sockets.c.obj
[318/503] Linking C static library modules\mbedtls\libmbedTLSX509.a
[319/503] Building C object modules/mbedtls/CMakeFiles/modules__mbedtls.dir/F_/circuit/.tools/zephyr/modules/crypto/mbedtls/library/ssl_cache.c.obj
[320/503] Building C object modules/mbedtls/CMakeFiles/modules__mbedtls.dir/F_/circuit/.tools/zephyr/modules/crypto/mbedtls/library/ssl_ciphersuites.c.obj
[321/503] Building C object modules/mbedtls/CMakeFiles/modules__mbedtls.dir/F_/circuit/.tools/zephyr/modules/crypto/mbedtls/library/ssl_client.c.obj
[322/503] Building C object modules/mbedtls/CMakeFiles/modules__mbedtls.dir/F_/circuit/.tools/zephyr/modules/crypto/mbedtls/library/ssl_cookie.c.obj
[323/503] Building C object modules/mbedtls/CMakeFiles/modules__mbedtls.dir/F_/circuit/.tools/zephyr/modules/crypto/mbedtls/library/ssl_msg.c.obj
[324/503] Building C object modules/mbedtls/CMakeFiles/modules__mbedtls.dir/F_/circuit/.tools/zephyr/modules/crypto/mbedtls/library/ssl_debug_helpers_generated.c.obj
[325/503] Building C object modules/mbedtls/CMakeFiles/modules__mbedtls.dir/F_/circuit/.tools/zephyr/modules/crypto/mbedtls/library/ssl_ticket.c.obj
[326/503] Building C object modules/mbedtls/CMakeFiles/modules__mbedtls.dir/F_/circuit/.tools/zephyr/modules/crypto/mbedtls/library/ssl_tls12_client.c.obj
[327/503] Building C object modules/mbedtls/CMakeFiles/modules__mbedtls.dir/F_/circuit/.tools/zephyr/modules/crypto/mbedtls/library/ssl_tls12_server.c.obj
[328/503] Building C object modules/mbedtls/CMakeFiles/modules__mbedtls.dir/F_/circuit/.tools/zephyr/modules/crypto/mbedtls/library/ssl_tls13_client.c.obj
[329/503] Building C object modules/mbedtls/CMakeFiles/modules__mbedtls.dir/F_/circuit/.tools/zephyr/modules/crypto/mbedtls/library/ssl_tls13_generic.c.obj
[330/503] Building C object modules/mbedtls/CMakeFiles/modules__mbedtls.dir/F_/circuit/.tools/zephyr/modules/crypto/mbedtls/library/ssl_tls13_keys.c.obj
[331/503] Building C object modules/mbedtls/CMakeFiles/modules__mbedtls.dir/F_/circuit/.tools/zephyr/modules/crypto/mbedtls/library/ssl_tls13_server.c.obj
[332/503] Building C object modules/mbedtls/CMakeFiles/modules__mbedtls.dir/F_/circuit/.tools/zephyr/modules/crypto/mbedtls/library/ssl_tls.c.obj
[333/503] Linking C static library modules\mbedtls\libmodules__mbedtls.a
[334/503] Building C object zephyr/kernel/CMakeFiles/kernel.dir/main_weak.c.obj
[335/503] Building C object zephyr/kernel/CMakeFiles/kernel.dir/banner.c.obj
[336/503] Building C object zephyr/kernel/CMakeFiles/kernel.dir/busy_wait.c.obj
[337/503] Building C object zephyr/kernel/CMakeFiles/kernel.dir/device.c.obj
[338/503] Building C object zephyr/kernel/CMakeFiles/kernel.dir/errno.c.obj
[339/503] Building C object zephyr/kernel/CMakeFiles/kernel.dir/fatal.c.obj
[340/503] Building C object zephyr/kernel/CMakeFiles/kernel.dir/init.c.obj
[341/503] Building C object zephyr/kernel/CMakeFiles/kernel.dir/kheap.c.obj
[342/503] Building C object zephyr/kernel/CMakeFiles/kernel.dir/mem_slab.c.obj
[343/503] Building C object zephyr/kernel/CMakeFiles/kernel.dir/float.c.obj
[344/503] Building C object zephyr/kernel/CMakeFiles/kernel.dir/version.c.obj
[345/503] Building C object zephyr/kernel/CMakeFiles/kernel.dir/idle.c.obj
[346/503] Building C object zephyr/kernel/CMakeFiles/kernel.dir/mailbox.c.obj
[347/503] Building C object zephyr/kernel/CMakeFiles/kernel.dir/msg_q.c.obj
[348/503] Building C object zephyr/kernel/CMakeFiles/kernel.dir/mutex.c.obj
[349/503] Building C object zephyr/kernel/CMakeFiles/kernel.dir/sem.c.obj
[350/503] Building C object zephyr/kernel/CMakeFiles/kernel.dir/queue.c.obj
[351/503] Building C object zephyr/kernel/CMakeFiles/kernel.dir/system_work_q.c.obj
[352/503] Building C object zephyr/kernel/CMakeFiles/kernel.dir/stack.c.obj
[353/503] Building C object zephyr/kernel/CMakeFiles/kernel.dir/condvar.c.obj
[354/503] Building C object zephyr/kernel/CMakeFiles/kernel.dir/work.c.obj
[355/503] Building C object zephyr/kernel/CMakeFiles/kernel.dir/thread.c.obj
[356/503] Building C object zephyr/kernel/CMakeFiles/kernel.dir/pipe.c.obj
[357/503] Building C object zephyr/kernel/CMakeFiles/kernel.dir/timeslicing.c.obj
[358/503] Building C object zephyr/kernel/CMakeFiles/kernel.dir/sched.c.obj
[359/503] Building C object zephyr/kernel/CMakeFiles/kernel.dir/spinlock_validate.c.obj
[360/503] Building C object zephyr/kernel/CMakeFiles/kernel.dir/xip.c.obj
[361/503] Building C object zephyr/kernel/CMakeFiles/kernel.dir/timeout.c.obj
[362/503] Building C object zephyr/kernel/CMakeFiles/kernel.dir/timer.c.obj
[363/503] Building C object zephyr/kernel/CMakeFiles/kernel.dir/mempool.c.obj
[364/503] Building C object zephyr/kernel/CMakeFiles/kernel.dir/poll.c.obj
[365/503] Building C object zephyr/kernel/CMakeFiles/kernel.dir/dynamic_disabled.c.obj
[366/503] Linking C static library zephyr\kernel\libkernel.a
[367/503] Building C object opus/CMakeFiles/opus.dir/src/extensions.c.obj
[368/503] Building C object opus/CMakeFiles/opus.dir/src/opus_multistream.c.obj
In file included from F:/circuit/firmware/a04/third_party/opus-1.6.1/src/opus_multistream.c:37:
F:/circuit/firmware/a04/third_party/opus-1.6.1/celt/float_cast.h:142:10: warning: #warning "Don't have the functions lrint() and lrintf ()." [-Wcpp]
  142 |         #warning "Don't have the functions lrint() and lrintf ()."
      |          ^~~~~~~
F:/circuit/firmware/a04/third_party/opus-1.6.1/celt/float_cast.h:143:10: warning: #warning "Replacing these functions with a standard C cast." [-Wcpp]
  143 |         #warning "Replacing these functions with a standard C cast."
      |          ^~~~~~~
[369/503] Building C object opus/CMakeFiles/opus.dir/src/opus_multistream_decoder.c.obj
In file included from F:/circuit/firmware/a04/third_party/opus-1.6.1/src/opus_multistream_decoder.c:37:
F:/circuit/firmware/a04/third_party/opus-1.6.1/celt/float_cast.h:142:10: warning: #warning "Don't have the functions lrint() and lrintf ()." [-Wcpp]
  142 |         #warning "Don't have the functions lrint() and lrintf ()."
      |          ^~~~~~~
F:/circuit/firmware/a04/third_party/opus-1.6.1/celt/float_cast.h:143:10: warning: #warning "Replacing these functions with a standard C cast." [-Wcpp]
  143 |         #warning "Replacing these functions with a standard C cast."
      |          ^~~~~~~
[370/503] Building C object opus/CMakeFiles/opus.dir/src/opus_multistream_encoder.c.obj
In file included from F:/circuit/firmware/a04/third_party/opus-1.6.1/src/opus_multistream_encoder.c:37:
F:/circuit/firmware/a04/third_party/opus-1.6.1/celt/float_cast.h:142:10: warning: #warning "Don't have the functions lrint() and lrintf ()." [-Wcpp]
  142 |         #warning "Don't have the functions lrint() and lrintf ()."
      |          ^~~~~~~
F:/circuit/firmware/a04/third_party/opus-1.6.1/celt/float_cast.h:143:10: warning: #warning "Replacing these functions with a standard C cast." [-Wcpp]
  143 |         #warning "Replacing these functions with a standard C cast."
      |          ^~~~~~~
In file included from F:/circuit/firmware/a04/third_party/opus-1.6.1/celt/arch.h:238,
                 from F:/circuit/firmware/a04/third_party/opus-1.6.1/src/opus_private.h:32,
                 from F:/circuit/firmware/a04/third_party/opus-1.6.1/src/opus_multistream_encoder.c:34:
F:/circuit/firmware/a04/third_party/opus-1.6.1/src/opus_multistream_encoder.c: In function 'logSum':
F:/circuit/firmware/a04/third_party/opus-1.6.1/celt/fixed_generic.h:98:40: warning: implicit conversion from 'float' to 'double' to match other operand of binary expression [-Wdouble-promotion]
   98 | #define GCONST2(x,bits) ((celt_glog)(.5+(x)*(((celt_glog)1)<<(bits))))
      |                                        ^
F:/circuit/firmware/a04/third_party/opus-1.6.1/celt/fixed_generic.h:101:19: note: in expansion of macro 'GCONST2'
  101 | #define GCONST(x) GCONST2((x),DB_SHIFT)
      |                   ^~~~~~~
F:/circuit/firmware/a04/third_party/opus-1.6.1/src/opus_multistream_encoder.c:199:10: note: in expansion of macro 'GCONST'
  199 |          GCONST(0.5000000f), GCONST(0.2924813f), GCONST(0.1609640f), GCONST(0.0849625f),
      |          ^~~~~~
F:/circuit/firmware/a04/third_party/opus-1.6.1/celt/fixed_generic.h:98:40: warning: implicit conversion from 'float' to 'double' to match other operand of binary expression [-Wdouble-promotion]
   98 | #define GCONST2(x,bits) ((celt_glog)(.5+(x)*(((celt_glog)1)<<(bits))))
      |                                        ^
F:/circuit/firmware/a04/third_party/opus-1.6.1/celt/fixed_generic.h:101:19: note: in expansion of macro 'GCONST2'
  101 | #define GCONST(x) GCONST2((x),DB_SHIFT)
      |                   ^~~~~~~
F:/circuit/firmware/a04/third_party/opus-1.6.1/src/opus_multistream_encoder.c:199:30: note: in expansion of macro 'GCONST'
  199 |          GCONST(0.5000000f), GCONST(0.2924813f), GCONST(0.1609640f), GCONST(0.0849625f),
      |                              ^~~~~~
F:/circuit/firmware/a04/third_party/opus-1.6.1/celt/fixed_generic.h:98:40: warning: implicit conversion from 'float' to 'double' to match other operand of binary expression [-Wdouble-promotion]
   98 | #define GCONST2(x,bits) ((celt_glog)(.5+(x)*(((celt_glog)1)<<(bits))))
      |                                        ^
F:/circuit/firmware/a04/third_party/opus-1.6.1/celt/fixed_generic.h:101:19: note: in expansion of macro 'GCONST2'
  101 | #define GCONST(x) GCONST2((x),DB_SHIFT)
      |                   ^~~~~~~
F:/circuit/firmware/a04/third_party/opus-1.6.1/src/opus_multistream_encoder.c:199:50: note: in expansion of macro 'GCONST'
  199 |          GCONST(0.5000000f), GCONST(0.2924813f), GCONST(0.1609640f), GCONST(0.0849625f),
      |                                                  ^~~~~~
F:/circuit/firmware/a04/third_party/opus-1.6.1/celt/fixed_generic.h:98:40: warning: implicit conversion from 'float' to 'double' to match other operand of binary expression [-Wdouble-promotion]
   98 | #define GCONST2(x,bits) ((celt_glog)(.5+(x)*(((celt_glog)1)<<(bits))))
      |                                        ^
F:/circuit/firmware/a04/third_party/opus-1.6.1/celt/fixed_generic.h:101:19: note: in expansion of macro 'GCONST2'
  101 | #define GCONST(x) GCONST2((x),DB_SHIFT)
      |                   ^~~~~~~
F:/circuit/firmware/a04/third_party/opus-1.6.1/src/opus_multistream_encoder.c:199:70: note: in expansion of macro 'GCONST'
  199 |          GCONST(0.5000000f), GCONST(0.2924813f), GCONST(0.1609640f), GCONST(0.0849625f),
      |                                                                      ^~~~~~
F:/circuit/firmware/a04/third_party/opus-1.6.1/celt/fixed_generic.h:98:40: warning: implicit conversion from 'float' to 'double' to match other operand of binary expression [-Wdouble-promotion]
   98 | #define GCONST2(x,bits) ((celt_glog)(.5+(x)*(((celt_glog)1)<<(bits))))
      |                                        ^
F:/circuit/firmware/a04/third_party/opus-1.6.1/celt/fixed_generic.h:101:19: note: in expansion of macro 'GCONST2'
  101 | #define GCONST(x) GCONST2((x),DB_SHIFT)
      |                   ^~~~~~~
F:/circuit/firmware/a04/third_party/opus-1.6.1/src/opus_multistream_encoder.c:200:10: note: in expansion of macro 'GCONST'
  200 |          GCONST(0.0437314f), GCONST(0.0221971f), GCONST(0.0111839f), GCONST(0.0056136f),
      |          ^~~~~~
F:/circuit/firmware/a04/third_party/opus-1.6.1/celt/fixed_generic.h:98:40: warning: implicit conversion from 'float' to 'double' to match other operand of binary expression [-Wdouble-promotion]
   98 | #define GCONST2(x,bits) ((celt_glog)(.5+(x)*(((celt_glog)1)<<(bits))))
      |                                        ^
F:/circuit/firmware/a04/third_party/opus-1.6.1/celt/fixed_generic.h:101:19: note: in expansion of macro 'GCONST2'
  101 | #define GCONST(x) GCONST2((x),DB_SHIFT)
      |                   ^~~~~~~
F:/circuit/firmware/a04/third_party/opus-1.6.1/src/opus_multistream_encoder.c:200:30: note: in expansion of macro 'GCONST'
  200 |          GCONST(0.0437314f), GCONST(0.0221971f), GCONST(0.0111839f), GCONST(0.0056136f),
      |                              ^~~~~~
F:/circuit/firmware/a04/third_party/opus-1.6.1/celt/fixed_generic.h:98:40: warning: implicit conversion from 'float' to 'double' to match other operand of binary expression [-Wdouble-promotion]
   98 | #define GCONST2(x,bits) ((celt_glog)(.5+(x)*(((celt_glog)1)<<(bits))))
      |                                        ^
F:/circuit/firmware/a04/third_party/opus-1.6.1/celt/fixed_generic.h:101:19: note: in expansion of macro 'GCONST2'
  101 | #define GCONST(x) GCONST2((x),DB_SHIFT)
      |                   ^~~~~~~
F:/circuit/firmware/a04/third_party/opus-1.6.1/src/opus_multistream_encoder.c:200:50: note: in expansion of macro 'GCONST'
  200 |          GCONST(0.0437314f), GCONST(0.0221971f), GCONST(0.0111839f), GCONST(0.0056136f),
      |                                                  ^~~~~~
F:/circuit/firmware/a04/third_party/opus-1.6.1/celt/fixed_generic.h:98:40: warning: implicit conversion from 'float' to 'double' to match other operand of binary expression [-Wdouble-promotion]
   98 | #define GCONST2(x,bits) ((celt_glog)(.5+(x)*(((celt_glog)1)<<(bits))))
      |                                        ^
F:/circuit/firmware/a04/third_party/opus-1.6.1/celt/fixed_generic.h:101:19: note: in expansion of macro 'GCONST2'
  101 | #define GCONST(x) GCONST2((x),DB_SHIFT)
      |                   ^~~~~~~
F:/circuit/firmware/a04/third_party/opus-1.6.1/src/opus_multistream_encoder.c:200:70: note: in expansion of macro 'GCONST'
  200 |          GCONST(0.0437314f), GCONST(0.0221971f), GCONST(0.0111839f), GCONST(0.0056136f),
      |                                                                      ^~~~~~
F:/circuit/firmware/a04/third_party/opus-1.6.1/celt/fixed_generic.h:98:40: warning: implicit conversion from 'float' to 'double' to match other operand of binary expression [-Wdouble-promotion]
   98 | #define GCONST2(x,bits) ((celt_glog)(.5+(x)*(((celt_glog)1)<<(bits))))
      |                                        ^
F:/circuit/firmware/a04/third_party/opus-1.6.1/celt/fixed_generic.h:101:19: note: in expansion of macro 'GCONST2'
  101 | #define GCONST(x) GCONST2((x),DB_SHIFT)
      |                   ^~~~~~~
F:/circuit/firmware/a04/third_party/opus-1.6.1/src/opus_multistream_encoder.c:201:10: note: in expansion of macro 'GCONST'
  201 |          GCONST(0.0028123f)
      |          ^~~~~~
F:/circuit/firmware/a04/third_party/opus-1.6.1/celt/fixed_generic.h:98:40: warning: implicit conversion from 'float' to 'double' to match other operand of binary expression [-Wdouble-promotion]
   98 | #define GCONST2(x,bits) ((celt_glog)(.5+(x)*(((celt_glog)1)<<(bits))))
      |                                        ^
F:/circuit/firmware/a04/third_party/opus-1.6.1/celt/fixed_generic.h:101:19: note: in expansion of macro 'GCONST2'
  101 | #define GCONST(x) GCONST2((x),DB_SHIFT)
      |                   ^~~~~~~
F:/circuit/firmware/a04/third_party/opus-1.6.1/src/opus_multistream_encoder.c:212:17: note: in expansion of macro 'GCONST'
  212 |    if (!(diff < GCONST(8.f)))  /* inverted to catch NaNs */
      |                 ^~~~~~
F:/circuit/firmware/a04/third_party/opus-1.6.1/src/opus_multistream_encoder.c: In function 'surround_analysis':
F:/circuit/firmware/a04/third_party/opus-1.6.1/celt/fixed_generic.h:98:40: warning: implicit conversion from 'float' to 'double' to match other operand of binary expression [-Wdouble-promotion]
   98 | #define GCONST2(x,bits) ((celt_glog)(.5+(x)*(((celt_glog)1)<<(bits))))
      |                                        ^
F:/circuit/firmware/a04/third_party/opus-1.6.1/celt/fixed_generic.h:101:19: note: in expansion of macro 'GCONST2'
  101 | #define GCONST(x) GCONST2((x),DB_SHIFT)
      |                   ^~~~~~~
F:/circuit/firmware/a04/third_party/opus-1.6.1/src/opus_multistream_encoder.c:267:28: note: in expansion of macro 'GCONST'
  267 |          maskLogE[c][i] = -GCONST(28.f);
      |                            ^~~~~~
F:/circuit/firmware/a04/third_party/opus-1.6.1/celt/fixed_generic.h:98:40: warning: implicit conversion from 'float' to 'double' to match other operand of binary expression [-Wdouble-promotion]
   98 | #define GCONST2(x,bits) ((celt_glog)(.5+(x)*(((celt_glog)1)<<(bits))))
      |                                        ^
F:/circuit/firmware/a04/third_party/opus-1.6.1/celt/arch.h:103:28: note: in definition of macro 'MAX32'
  103 | #define MAX32(a,b) ((a) > (b) ? (a) : (b))   /**< Maximum 32-bit value.   */
      |                            ^
F:/circuit/firmware/a04/third_party/opus-1.6.1/src/opus_multistream_encoder.c:313:29: note: in expansion of macro 'MAXG'
  313 |          bandLogE[21*c+i] = MAXG(bandLogE[21*c+i], bandLogE[21*c+i-1]-GCONST(1.f));
      |                             ^~~~
F:/circuit/firmware/a04/third_party/opus-1.6.1/celt/fixed_generic.h:101:19: note: in expansion of macro 'GCONST2'
  101 | #define GCONST(x) GCONST2((x),DB_SHIFT)
      |                   ^~~~~~~
F:/circuit/firmware/a04/third_party/opus-1.6.1/src/opus_multistream_encoder.c:313:71: note: in expansion of macro 'GCONST'
  313 |          bandLogE[21*c+i] = MAXG(bandLogE[21*c+i], bandLogE[21*c+i-1]-GCONST(1.f));
      |                                                                       ^~~~~~
F:/circuit/firmware/a04/third_party/opus-1.6.1/celt/fixed_generic.h:98:40: warning: implicit conversion from 'float' to 'double' to match other operand of binary expression [-Wdouble-promotion]
   98 | #define GCONST2(x,bits) ((celt_glog)(.5+(x)*(((celt_glog)1)<<(bits))))
      |                                        ^
F:/circuit/firmware/a04/third_party/opus-1.6.1/celt/arch.h:103:40: note: in definition of macro 'MAX32'
  103 | #define MAX32(a,b) ((a) > (b) ? (a) : (b))   /**< Maximum 32-bit value.   */
      |                                        ^
F:/circuit/firmware/a04/third_party/opus-1.6.1/src/opus_multistream_encoder.c:313:29: note: in expansion of macro 'MAXG'
  313 |          bandLogE[21*c+i] = MAXG(bandLogE[21*c+i], bandLogE[21*c+i-1]-GCONST(1.f));
      |                             ^~~~
F:/circuit/firmware/a04/third_party/opus-1.6.1/celt/fixed_generic.h:101:19: note: in expansion of macro 'GCONST2'
  101 | #define GCONST(x) GCONST2((x),DB_SHIFT)
      |                   ^~~~~~~
F:/circuit/firmware/a04/third_party/opus-1.6.1/src/opus_multistream_encoder.c:313:71: note: in expansion of macro 'GCONST'
  313 |          bandLogE[21*c+i] = MAXG(bandLogE[21*c+i], bandLogE[21*c+i-1]-GCONST(1.f));
      |                                                                       ^~~~~~
F:/circuit/firmware/a04/third_party/opus-1.6.1/celt/fixed_generic.h:98:40: warning: implicit conversion from 'float' to 'double' to match other operand of binary expression [-Wdouble-promotion]
   98 | #define GCONST2(x,bits) ((celt_glog)(.5+(x)*(((celt_glog)1)<<(bits))))
      |                                        ^
F:/circuit/firmware/a04/third_party/opus-1.6.1/celt/arch.h:103:28: note: in definition of macro 'MAX32'
  103 | #define MAX32(a,b) ((a) > (b) ? (a) : (b))   /**< Maximum 32-bit value.   */
      |                            ^
F:/circuit/firmware/a04/third_party/opus-1.6.1/src/opus_multistream_encoder.c:315:29: note: in expansion of macro 'MAXG'
  315 |          bandLogE[21*c+i] = MAXG(bandLogE[21*c+i], bandLogE[21*c+i+1]-GCONST(2.f));
      |                             ^~~~
F:/circuit/firmware/a04/third_party/opus-1.6.1/celt/fixed_generic.h:101:19: note: in expansion of macro 'GCONST2'
  101 | #define GCONST(x) GCONST2((x),DB_SHIFT)
      |                   ^~~~~~~
F:/circuit/firmware/a04/third_party/opus-1.6.1/src/opus_multistream_encoder.c:315:71: note: in expansion of macro 'GCONST'
  315 |          bandLogE[21*c+i] = MAXG(bandLogE[21*c+i], bandLogE[21*c+i+1]-GCONST(2.f));
      |                                                                       ^~~~~~
F:/circuit/firmware/a04/third_party/opus-1.6.1/celt/fixed_generic.h:98:40: warning: implicit conversion from 'float' to 'double' to match other operand of binary expression [-Wdouble-promotion]
   98 | #define GCONST2(x,bits) ((celt_glog)(.5+(x)*(((celt_glog)1)<<(bits))))
      |                                        ^
F:/circuit/firmware/a04/third_party/opus-1.6.1/celt/arch.h:103:40: note: in definition of macro 'MAX32'
  103 | #define MAX32(a,b) ((a) > (b) ? (a) : (b))   /**< Maximum 32-bit value.   */
      |                                        ^
F:/circuit/firmware/a04/third_party/opus-1.6.1/src/opus_multistream_encoder.c:315:29: note: in expansion of macro 'MAXG'
  315 |          bandLogE[21*c+i] = MAXG(bandLogE[21*c+i], bandLogE[21*c+i+1]-GCONST(2.f));
      |                             ^~~~
F:/circuit/firmware/a04/third_party/opus-1.6.1/celt/fixed_generic.h:101:19: note: in expansion of macro 'GCONST2'
  101 | #define GCONST(x) GCONST2((x),DB_SHIFT)
      |                   ^~~~~~~
F:/circuit/firmware/a04/third_party/opus-1.6.1/src/opus_multistream_encoder.c:315:71: note: in expansion of macro 'GCONST'
  315 |          bandLogE[21*c+i] = MAXG(bandLogE[21*c+i], bandLogE[21*c+i+1]-GCONST(2.f));
      |                                                                       ^~~~~~
F:/circuit/firmware/a04/third_party/opus-1.6.1/celt/fixed_generic.h:98:40: warning: implicit conversion from 'float' to 'double' to match other operand of binary expression [-Wdouble-promotion]
   98 | #define GCONST2(x,bits) ((celt_glog)(.5+(x)*(((celt_glog)1)<<(bits))))
      |                                        ^
F:/circuit/firmware/a04/third_party/opus-1.6.1/celt/fixed_generic.h:101:19: note: in expansion of macro 'GCONST2'
  101 | #define GCONST(x) GCONST2((x),DB_SHIFT)
      |                   ^~~~~~~
F:/circuit/firmware/a04/third_party/opus-1.6.1/src/opus_multistream_encoder.c:328:70: note: in expansion of macro 'GCONST'
  328 |             maskLogE[0][i] = logSum(maskLogE[0][i], bandLogE[21*c+i]-GCONST(.5f));
      |                                                                      ^~~~~~
F:/circuit/firmware/a04/third_party/opus-1.6.1/celt/fixed_generic.h:98:40: warning: implicit conversion from 'float' to 'double' to match other operand of binary expression [-Wdouble-promotion]
   98 | #define GCONST2(x,bits) ((celt_glog)(.5+(x)*(((celt_glog)1)<<(bits))))
      |                                        ^
F:/circuit/firmware/a04/third_party/opus-1.6.1/celt/fixed_generic.h:101:19: note: in expansion of macro 'GCONST2'
  101 | #define GCONST(x) GCONST2((x),DB_SHIFT)
      |                   ^~~~~~~
F:/circuit/firmware/a04/third_party/opus-1.6.1/src/opus_multistream_encoder.c:329:70: note: in expansion of macro 'GCONST'
  329 |             maskLogE[2][i] = logSum(maskLogE[2][i], bandLogE[21*c+i]-GCONST(.5f));
      |                                                                      ^~~~~~
F:/circuit/firmware/a04/third_party/opus-1.6.1/celt/fixed_generic.h:95:42: warning: implicit conversion from 'float' to 'double' to match other operand of binary expression [-Wdouble-promotion]
   95 | #define QCONST32(x,bits) ((opus_val32)(.5+(x)*(((opus_int64)1)<<(bits))))
      |                                          ^
F:/circuit/firmware/a04/third_party/opus-1.6.1/celt/fixed_generic.h:114:26: note: in definition of macro 'SHR16'
  114 | #define SHR16(a,shift) ((a) >> (shift))
      |                          ^
F:/circuit/firmware/a04/third_party/opus-1.6.1/src/opus_multistream_encoder.c:344:21: note: in expansion of macro 'HALF16'
  344 |    channel_offset = HALF16(celt_log2(QCONST32(2.f,14)/(channels-1)));
      |                     ^~~~~~
F:/circuit/firmware/a04/third_party/opus-1.6.1/src/opus_multistream_encoder.c:344:38: note: in expansion of macro 'QCONST32'
  344 |    channel_offset = HALF16(celt_log2(QCONST32(2.f,14)/(channels-1)));
      |                                      ^~~~~~~~
[371/503] Building C object opus/CMakeFiles/opus.dir/src/repacketizer.c.obj
[372/503] Building C object opus/CMakeFiles/opus.dir/src/opus_projection_decoder.c.obj
[373/503] Building C object opus/CMakeFiles/opus.dir/src/opus_projection_encoder.c.obj
[374/503] Building C object opus/CMakeFiles/opus.dir/src/analysis.c.obj
In file included from F:/circuit/firmware/a04/third_party/opus-1.6.1/src/analysis.c:47:
F:/circuit/firmware/a04/third_party/opus-1.6.1/celt/float_cast.h:142:10: warning: #warning "Don't have the functions lrint() and lrintf ()." [-Wcpp]
  142 |         #warning "Don't have the functions lrint() and lrintf ()."
      |          ^~~~~~~
F:/circuit/firmware/a04/third_party/opus-1.6.1/celt/float_cast.h:143:10: warning: #warning "Replacing these functions with a standard C cast." [-Wcpp]
  143 |         #warning "Replacing these functions with a standard C cast."
      |          ^~~~~~~
[375/503] Building C object opus/CMakeFiles/opus.dir/src/mapping_matrix.c.obj
In file included from F:/circuit/firmware/a04/third_party/opus-1.6.1/src/mapping_matrix.c:33:
F:/circuit/firmware/a04/third_party/opus-1.6.1/celt/float_cast.h:142:10: warning: #warning "Don't have the functions lrint() and lrintf ()." [-Wcpp]
  142 |         #warning "Don't have the functions lrint() and lrintf ()."
      |          ^~~~~~~
F:/circuit/firmware/a04/third_party/opus-1.6.1/celt/float_cast.h:143:10: warning: #warning "Replacing these functions with a standard C cast." [-Wcpp]
  143 |         #warning "Replacing these functions with a standard C cast."
      |          ^~~~~~~
[376/503] Building C object opus/CMakeFiles/opus.dir/src/mlp_data.c.obj
[377/503] Building C object opus/CMakeFiles/opus.dir/src/mlp.c.obj
[378/503] Building C object opus/CMakeFiles/opus.dir/silk/code_signs.c.obj
[379/503] Building C object opus/CMakeFiles/opus.dir/silk/CNG.c.obj
[380/503] Building C object opus/CMakeFiles/opus.dir/silk/init_decoder.c.obj
[381/503] Building C object opus/CMakeFiles/opus.dir/silk/decode_frame.c.obj
[382/503] Building C object opus/CMakeFiles/opus.dir/silk/decode_parameters.c.obj
[383/503] Building C object opus/CMakeFiles/opus.dir/silk/decode_core.c.obj
[384/503] Building C object opus/CMakeFiles/opus.dir/silk/decode_indices.c.obj
[385/503] Building C object opus/CMakeFiles/opus.dir/silk/decode_pulses.c.obj
[386/503] Building C object opus/CMakeFiles/opus.dir/silk/decoder_set_fs.c.obj
[387/503] Building C object opus/CMakeFiles/opus.dir/silk/dec_API.c.obj
[388/503] Building C object opus/CMakeFiles/opus.dir/silk/encode_indices.c.obj
[389/503] Building C object opus/CMakeFiles/opus.dir/silk/enc_API.c.obj
In file included from F:/circuit/firmware/a04/third_party/opus-1.6.1/silk/SigProc_FIX.h:39,
                 from F:/circuit/firmware/a04/third_party/opus-1.6.1/silk/structs.h:32,
                 from F:/circuit/firmware/a04/third_party/opus-1.6.1/silk/enc_API.c:36:
F:/circuit/firmware/a04/third_party/opus-1.6.1/silk/enc_API.c: In function 'silk_Encode':
F:/circuit/firmware/a04/third_party/opus-1.6.1/silk/SigProc_FIX.h:539:88: warning: implicit conversion from 'float' to 'double' to match other operand of binary expression [-Wdouble-promotion]
  539 | #define SILK_FIX_CONST( C, Q )              ((opus_int32)((C) * ((opus_int64)1 << (Q)) + 0.5))
      |                                                                                        ^
F:/circuit/firmware/a04/third_party/opus-1.6.1/silk/macros.h:52:44: note: in definition of macro 'silk_SMLAWB'
   52 | #define silk_SMLAWB(a32, b32, c32)       ((a32) + ((((b32) >> 16) * (opus_int32)((opus_int16)(c32))) + ((((b32) & 0x0000FFFF) * (opus_int32)((opus_int16)(c32))) >> 16)))
      |                                            ^~~
F:/circuit/firmware/a04/third_party/opus-1.6.1/silk/enc_API.c:560:61: note: in expansion of macro 'SILK_FIX_CONST'
  560 |                 speech_act_thr_for_switch_Q8 = silk_SMLAWB( SILK_FIX_CONST( SPEECH_ACTIVITY_DTX_THRES, 8 ),
      |                                                             ^~~~~~~~~~~~~~
F:/circuit/firmware/a04/third_party/opus-1.6.1/silk/SigProc_FIX.h:539:88: warning: implicit conversion from 'float' to 'double' to match other operand of binary expression [-Wdouble-promotion]
  539 | #define SILK_FIX_CONST( C, Q )              ((opus_int32)((C) * ((opus_int64)1 << (Q)) + 0.5))
      |                                                                                        ^
F:/circuit/firmware/a04/third_party/opus-1.6.1/silk/macros.h:52:55: note: in definition of macro 'silk_SMLAWB'
   52 | #define silk_SMLAWB(a32, b32, c32)       ((a32) + ((((b32) >> 16) * (opus_int32)((opus_int16)(c32))) + ((((b32) & 0x0000FFFF) * (opus_int32)((opus_int16)(c32))) >> 16)))
      |                                                       ^~~
F:/circuit/firmware/a04/third_party/opus-1.6.1/silk/enc_API.c:561:21: note: in expansion of macro 'SILK_FIX_CONST'
  561 |                     SILK_FIX_CONST( ( 1 - SPEECH_ACTIVITY_DTX_THRES ) / MAX_BANDWIDTH_SWITCH_DELAY_MS, 16 + 8 ), psEnc->timeSinceSwitchAllowed_ms );
      |                     ^~~~~~~~~~~~~~
F:/circuit/firmware/a04/third_party/opus-1.6.1/silk/SigProc_FIX.h:539:88: warning: implicit conversion from 'float' to 'double' to match other operand of binary expression [-Wdouble-promotion]
  539 | #define SILK_FIX_CONST( C, Q )              ((opus_int32)((C) * ((opus_int64)1 << (Q)) + 0.5))
      |                                                                                        ^
F:/circuit/firmware/a04/third_party/opus-1.6.1/silk/macros.h:52:108: note: in definition of macro 'silk_SMLAWB'
   52 | #define silk_SMLAWB(a32, b32, c32)       ((a32) + ((((b32) >> 16) * (opus_int32)((opus_int16)(c32))) + ((((b32) & 0x0000FFFF) * (opus_int32)((opus_int16)(c32))) >> 16)))
      |                                                                                                            ^~~
F:/circuit/firmware/a04/third_party/opus-1.6.1/silk/enc_API.c:561:21: note: in expansion of macro 'SILK_FIX_CONST'
  561 |                     SILK_FIX_CONST( ( 1 - SPEECH_ACTIVITY_DTX_THRES ) / MAX_BANDWIDTH_SWITCH_DELAY_MS, 16 + 8 ), psEnc->timeSinceSwitchAllowed_ms );
      |                     ^~~~~~~~~~~~~~
F:/circuit/firmware/a04/third_party/opus-1.6.1/silk/enc_API.c:409:13: warning: 'silk_HP_variable_cutoff' accessing 8728 bytes in a region of size 8 [-Wstringop-overflow=]
  409 |             silk_HP_variable_cutoff( psEnc->state_Fxx );
      |             ^~~~~~~~~~~~~~~~~~~~~~~~~~~~~~~~~~~~~~~~~~~
F:/circuit/firmware/a04/third_party/opus-1.6.1/silk/enc_API.c:409:13: note: referencing argument 1 of type 'silk_encoder_state_FIX[0]'
In file included from F:/circuit/firmware/a04/third_party/opus-1.6.1/silk/enc_API.c:39:
F:/circuit/firmware/a04/third_party/opus-1.6.1/silk/fixed/main_FIX.h:57:6: note: in a call to function 'silk_HP_variable_cutoff'
   57 | void silk_HP_variable_cutoff(
      |      ^~~~~~~~~~~~~~~~~~~~~~~
F:/circuit/firmware/a04/third_party/opus-1.6.1/silk/enc_API.c:409:13: warning: 'silk_HP_variable_cutoff' accessing 8728 bytes in a region of size 8 [-Wstringop-overflow=]
  409 |             silk_HP_variable_cutoff( psEnc->state_Fxx );
      |             ^~~~~~~~~~~~~~~~~~~~~~~~~~~~~~~~~~~~~~~~~~~
F:/circuit/firmware/a04/third_party/opus-1.6.1/silk/enc_API.c:409:13: note: referencing argument 1 of type 'silk_encoder_state_FIX[0]'
F:/circuit/firmware/a04/third_party/opus-1.6.1/silk/fixed/main_FIX.h:57:6: note: in a call to function 'silk_HP_variable_cutoff'
   57 | void silk_HP_variable_cutoff(
      |      ^~~~~~~~~~~~~~~~~~~~~~~
F:/circuit/firmware/a04/third_party/opus-1.6.1/silk/enc_API.c:409:13: warning: 'silk_HP_variable_cutoff' accessing 8728 bytes in a region of size 8 [-Wstringop-overflow=]
  409 |             silk_HP_variable_cutoff( psEnc->state_Fxx );
      |             ^~~~~~~~~~~~~~~~~~~~~~~~~~~~~~~~~~~~~~~~~~~
F:/circuit/firmware/a04/third_party/opus-1.6.1/silk/enc_API.c:409:13: note: referencing argument 1 of type 'silk_encoder_state_FIX[0]'
F:/circuit/firmware/a04/third_party/opus-1.6.1/silk/fixed/main_FIX.h:57:6: note: in a call to function 'silk_HP_variable_cutoff'
   57 | void silk_HP_variable_cutoff(
      |      ^~~~~~~~~~~~~~~~~~~~~~~
[390/503] Building C object opus/CMakeFiles/opus.dir/silk/encode_pulses.c.obj
[391/503] Building C object opus/CMakeFiles/opus.dir/silk/gain_quant.c.obj
[392/503] Building C object opus/CMakeFiles/opus.dir/silk/interpolate.c.obj
[393/503] Building C object opus/CMakeFiles/opus.dir/silk/LP_variable_cutoff.c.obj
[394/503] Building C object opus/CMakeFiles/opus.dir/silk/NLSF_decode.c.obj
[395/503] Building C object opus/CMakeFiles/opus.dir/silk/NSQ.c.obj
[396/503] Building C object opus/CMakeFiles/opus.dir/silk/NSQ_del_dec.c.obj
[397/503] Building C object opus/CMakeFiles/opus.dir/silk/PLC.c.obj
[398/503] Building C object opus/CMakeFiles/opus.dir/silk/shell_coder.c.obj
[399/503] Building C object opus/CMakeFiles/opus.dir/silk/tables_gain.c.obj
[400/503] Building C object opus/CMakeFiles/opus.dir/silk/tables_LTP.c.obj
[401/503] Building C object opus/CMakeFiles/opus.dir/silk/tables_NLSF_CB_NB_MB.c.obj
[402/503] Building C object opus/CMakeFiles/opus.dir/silk/tables_NLSF_CB_WB.c.obj
[403/503] Building C object opus/CMakeFiles/opus.dir/silk/tables_other.c.obj
[404/503] Building C object opus/CMakeFiles/opus.dir/silk/tables_pitch_lag.c.obj
[405/503] Building C object opus/CMakeFiles/opus.dir/silk/tables_pulses_per_block.c.obj
[406/503] Building C object opus/CMakeFiles/opus.dir/silk/control_audio_bandwidth.c.obj
[407/503] Building C object opus/CMakeFiles/opus.dir/silk/VAD.c.obj
[408/503] Building C object opus/CMakeFiles/opus.dir/silk/quant_LTP_gains.c.obj
In file included from F:/circuit/firmware/a04/third_party/opus-1.6.1/silk/main.h:31,
                 from F:/circuit/firmware/a04/third_party/opus-1.6.1/silk/quant_LTP_gains.c:32:
F:/circuit/firmware/a04/third_party/opus-1.6.1/silk/quant_LTP_gains.c: In function 'silk_quant_LTP_gains':
F:/circuit/firmware/a04/third_party/opus-1.6.1/silk/quant_LTP_gains.c:82:79: warning: implicit conversion from 'float' to 'double' to match other operand of binary expression [-Wdouble-promotion]
   82 |             max_gain_Q7 = silk_log2lin( ( SILK_FIX_CONST( MAX_SUM_LOG_GAIN_DB / 6.0, 7 ) - sum_log_gain_tmp_Q7 )
      |                                                                               ^
F:/circuit/firmware/a04/third_party/opus-1.6.1/silk/SigProc_FIX.h:539:60: note: in definition of macro 'SILK_FIX_CONST'
  539 | #define SILK_FIX_CONST( C, Q )              ((opus_int32)((C) * ((opus_int64)1 << (Q)) + 0.5))
      |                                                            ^
[409/503] Building C object opus/CMakeFiles/opus.dir/silk/VQ_WMat_EC.c.obj
[410/503] Building C object opus/CMakeFiles/opus.dir/silk/HP_variable_cutoff.c.obj
In file included from F:/circuit/firmware/a04/third_party/opus-1.6.1/silk/fixed/main_FIX.h:31,
                 from F:/circuit/firmware/a04/third_party/opus-1.6.1/silk/HP_variable_cutoff.c:32:
F:/circuit/firmware/a04/third_party/opus-1.6.1/silk/HP_variable_cutoff.c: In function 'silk_HP_variable_cutoff':
F:/circuit/firmware/a04/third_party/opus-1.6.1/silk/SigProc_FIX.h:539:88: warning: implicit conversion from 'float' to 'double' to match other operand of binary expression [-Wdouble-promotion]
  539 | #define SILK_FIX_CONST( C, Q )              ((opus_int32)((C) * ((opus_int64)1 << (Q)) + 0.5))
      |                                                                                        ^
F:/circuit/firmware/a04/third_party/opus-1.6.1/silk/SigProc_FIX.h:577:47: note: in definition of macro 'silk_LIMIT'
  577 | #define silk_LIMIT( a, limit1, limit2)      ((limit1) > (limit2) ? ((a) > (limit1) ? (limit1) : ((a) < (limit2) ? (limit2) : (a))) \
      |                                               ^~~~~~
F:/circuit/firmware/a04/third_party/opus-1.6.1/silk/HP_variable_cutoff.c:66:54: note: in expansion of macro 'SILK_FIX_CONST'
   66 |       delta_freq_Q7 = silk_LIMIT_32( delta_freq_Q7, -SILK_FIX_CONST( VARIABLE_HP_MAX_DELTA_FREQ, 7 ), SILK_FIX_CONST( VARIABLE_HP_MAX_DELTA_FREQ, 7 ) );
      |                                                      ^~~~~~~~~~~~~~
F:/circuit/firmware/a04/third_party/opus-1.6.1/silk/SigProc_FIX.h:539:88: warning: implicit conversion from 'float' to 'double' to match other operand of binary expression [-Wdouble-promotion]
  539 | #define SILK_FIX_CONST( C, Q )              ((opus_int32)((C) * ((opus_int64)1 << (Q)) + 0.5))
      |                                                                                        ^
F:/circuit/firmware/a04/third_party/opus-1.6.1/silk/SigProc_FIX.h:577:58: note: in definition of macro 'silk_LIMIT'
  577 | #define silk_LIMIT( a, limit1, limit2)      ((limit1) > (limit2) ? ((a) > (limit1) ? (limit1) : ((a) < (limit2) ? (limit2) : (a))) \
      |                                                          ^~~~~~
F:/circuit/firmware/a04/third_party/opus-1.6.1/silk/HP_variable_cutoff.c:66:103: note: in expansion of macro 'SILK_FIX_CONST'
   66 |       delta_freq_Q7 = silk_LIMIT_32( delta_freq_Q7, -SILK_FIX_CONST( VARIABLE_HP_MAX_DELTA_FREQ, 7 ), SILK_FIX_CONST( VARIABLE_HP_MAX_DELTA_FREQ, 7 ) );
      |                                                                                                       ^~~~~~~~~~~~~~
F:/circuit/firmware/a04/third_party/opus-1.6.1/silk/SigProc_FIX.h:539:88: warning: implicit conversion from 'float' to 'double' to match other operand of binary expression [-Wdouble-promotion]
  539 | #define SILK_FIX_CONST( C, Q )              ((opus_int32)((C) * ((opus_int64)1 << (Q)) + 0.5))
      |                                                                                        ^
F:/circuit/firmware/a04/third_party/opus-1.6.1/silk/SigProc_FIX.h:577:76: note: in definition of macro 'silk_LIMIT'
  577 | #define silk_LIMIT( a, limit1, limit2)      ((limit1) > (limit2) ? ((a) > (limit1) ? (limit1) : ((a) < (limit2) ? (limit2) : (a))) \
      |                                                                            ^~~~~~
F:/circuit/firmware/a04/third_party/opus-1.6.1/silk/HP_variable_cutoff.c:66:54: note: in expansion of macro 'SILK_FIX_CONST'
   66 |       delta_freq_Q7 = silk_LIMIT_32( delta_freq_Q7, -SILK_FIX_CONST( VARIABLE_HP_MAX_DELTA_FREQ, 7 ), SILK_FIX_CONST( VARIABLE_HP_MAX_DELTA_FREQ, 7 ) );
      |                                                      ^~~~~~~~~~~~~~
F:/circuit/firmware/a04/third_party/opus-1.6.1/silk/SigProc_FIX.h:539:88: warning: implicit conversion from 'float' to 'double' to match other operand of binary expression [-Wdouble-promotion]
  539 | #define SILK_FIX_CONST( C, Q )              ((opus_int32)((C) * ((opus_int64)1 << (Q)) + 0.5))
      |                                                                                        ^
F:/circuit/firmware/a04/third_party/opus-1.6.1/silk/SigProc_FIX.h:577:87: note: in definition of macro 'silk_LIMIT'
  577 | #define silk_LIMIT( a, limit1, limit2)      ((limit1) > (limit2) ? ((a) > (limit1) ? (limit1) : ((a) < (limit2) ? (limit2) : (a))) \
      |                                                                                       ^~~~~~
F:/circuit/firmware/a04/third_party/opus-1.6.1/silk/HP_variable_cutoff.c:66:54: note: in expansion of macro 'SILK_FIX_CONST'
   66 |       delta_freq_Q7 = silk_LIMIT_32( delta_freq_Q7, -SILK_FIX_CONST( VARIABLE_HP_MAX_DELTA_FREQ, 7 ), SILK_FIX_CONST( VARIABLE_HP_MAX_DELTA_FREQ, 7 ) );
      |                                                      ^~~~~~~~~~~~~~
F:/circuit/firmware/a04/third_party/opus-1.6.1/silk/SigProc_FIX.h:539:88: warning: implicit conversion from 'float' to 'double' to match other operand of binary expression [-Wdouble-promotion]
  539 | #define SILK_FIX_CONST( C, Q )              ((opus_int32)((C) * ((opus_int64)1 << (Q)) + 0.5))
      |                                                                                        ^
F:/circuit/firmware/a04/third_party/opus-1.6.1/silk/SigProc_FIX.h:577:105: note: in definition of macro 'silk_LIMIT'
  577 | #define silk_LIMIT( a, limit1, limit2)      ((limit1) > (limit2) ? ((a) > (limit1) ? (limit1) : ((a) < (limit2) ? (limit2) : (a))) \
      |                                                                                                         ^~~~~~
F:/circuit/firmware/a04/third_party/opus-1.6.1/silk/HP_variable_cutoff.c:66:103: note: in expansion of macro 'SILK_FIX_CONST'
   66 |       delta_freq_Q7 = silk_LIMIT_32( delta_freq_Q7, -SILK_FIX_CONST( VARIABLE_HP_MAX_DELTA_FREQ, 7 ), SILK_FIX_CONST( VARIABLE_HP_MAX_DELTA_FREQ, 7 ) );
      |                                                                                                       ^~~~~~~~~~~~~~
F:/circuit/firmware/a04/third_party/opus-1.6.1/silk/SigProc_FIX.h:539:88: warning: implicit conversion from 'float' to 'double' to match other operand of binary expression [-Wdouble-promotion]
  539 | #define SILK_FIX_CONST( C, Q )              ((opus_int32)((C) * ((opus_int64)1 << (Q)) + 0.5))
      |                                                                                        ^
F:/circuit/firmware/a04/third_party/opus-1.6.1/silk/SigProc_FIX.h:577:116: note: in definition of macro 'silk_LIMIT'
  577 | #define silk_LIMIT( a, limit1, limit2)      ((limit1) > (limit2) ? ((a) > (limit1) ? (limit1) : ((a) < (limit2) ? (limit2) : (a))) \
      |                                                                                                                    ^~~~~~
F:/circuit/firmware/a04/third_party/opus-1.6.1/silk/HP_variable_cutoff.c:66:103: note: in expansion of macro 'SILK_FIX_CONST'
   66 |       delta_freq_Q7 = silk_LIMIT_32( delta_freq_Q7, -SILK_FIX_CONST( VARIABLE_HP_MAX_DELTA_FREQ, 7 ), SILK_FIX_CONST( VARIABLE_HP_MAX_DELTA_FREQ, 7 ) );
      |                                                                                                       ^~~~~~~~~~~~~~
F:/circuit/firmware/a04/third_party/opus-1.6.1/silk/SigProc_FIX.h:539:88: warning: implicit conversion from 'float' to 'double' to match other operand of binary expression [-Wdouble-promotion]
  539 | #define SILK_FIX_CONST( C, Q )              ((opus_int32)((C) * ((opus_int64)1 << (Q)) + 0.5))
      |                                                                                        ^
F:/circuit/firmware/a04/third_party/opus-1.6.1/silk/SigProc_FIX.h:578:76: note: in definition of macro 'silk_LIMIT'
  578 |                                                                  : ((a) > (limit2) ? (limit2) : ((a) < (limit1) ? (limit1) : (a))))
      |                                                                            ^~~~~~
F:/circuit/firmware/a04/third_party/opus-1.6.1/silk/HP_variable_cutoff.c:66:103: note: in expansion of macro 'SILK_FIX_CONST'
   66 |       delta_freq_Q7 = silk_LIMIT_32( delta_freq_Q7, -SILK_FIX_CONST( VARIABLE_HP_MAX_DELTA_FREQ, 7 ), SILK_FIX_CONST( VARIABLE_HP_MAX_DELTA_FREQ, 7 ) );
      |                                                                                                       ^~~~~~~~~~~~~~
F:/circuit/firmware/a04/third_party/opus-1.6.1/silk/SigProc_FIX.h:539:88: warning: implicit conversion from 'float' to 'double' to match other operand of binary expression [-Wdouble-promotion]
  539 | #define SILK_FIX_CONST( C, Q )              ((opus_int32)((C) * ((opus_int64)1 << (Q)) + 0.5))
      |                                                                                        ^
F:/circuit/firmware/a04/third_party/opus-1.6.1/silk/SigProc_FIX.h:578:87: note: in definition of macro 'silk_LIMIT'
  578 |                                                                  : ((a) > (limit2) ? (limit2) : ((a) < (limit1) ? (limit1) : (a))))
      |                                                                                       ^~~~~~
F:/circuit/firmware/a04/third_party/opus-1.6.1/silk/HP_variable_cutoff.c:66:103: note: in expansion of macro 'SILK_FIX_CONST'
   66 |       delta_freq_Q7 = silk_LIMIT_32( delta_freq_Q7, -SILK_FIX_CONST( VARIABLE_HP_MAX_DELTA_FREQ, 7 ), SILK_FIX_CONST( VARIABLE_HP_MAX_DELTA_FREQ, 7 ) );
      |                                                                                                       ^~~~~~~~~~~~~~
F:/circuit/firmware/a04/third_party/opus-1.6.1/silk/SigProc_FIX.h:539:88: warning: implicit conversion from 'float' to 'double' to match other operand of binary expression [-Wdouble-promotion]
  539 | #define SILK_FIX_CONST( C, Q )              ((opus_int32)((C) * ((opus_int64)1 << (Q)) + 0.5))
      |                                                                                        ^
F:/circuit/firmware/a04/third_party/opus-1.6.1/silk/SigProc_FIX.h:578:105: note: in definition of macro 'silk_LIMIT'
  578 |                                                                  : ((a) > (limit2) ? (limit2) : ((a) < (limit1) ? (limit1) : (a))))
      |                                                                                                         ^~~~~~
F:/circuit/firmware/a04/third_party/opus-1.6.1/silk/HP_variable_cutoff.c:66:54: note: in expansion of macro 'SILK_FIX_CONST'
   66 |       delta_freq_Q7 = silk_LIMIT_32( delta_freq_Q7, -SILK_FIX_CONST( VARIABLE_HP_MAX_DELTA_FREQ, 7 ), SILK_FIX_CONST( VARIABLE_HP_MAX_DELTA_FREQ, 7 ) );
      |                                                      ^~~~~~~~~~~~~~
F:/circuit/firmware/a04/third_party/opus-1.6.1/silk/SigProc_FIX.h:539:88: warning: implicit conversion from 'float' to 'double' to match other operand of binary expression [-Wdouble-promotion]
  539 | #define SILK_FIX_CONST( C, Q )              ((opus_int32)((C) * ((opus_int64)1 << (Q)) + 0.5))
      |                                                                                        ^
F:/circuit/firmware/a04/third_party/opus-1.6.1/silk/SigProc_FIX.h:578:116: note: in definition of macro 'silk_LIMIT'
  578 |                                                                  : ((a) > (limit2) ? (limit2) : ((a) < (limit1) ? (limit1) : (a))))
      |                                                                                                                    ^~~~~~
F:/circuit/firmware/a04/third_party/opus-1.6.1/silk/HP_variable_cutoff.c:66:54: note: in expansion of macro 'SILK_FIX_CONST'
   66 |       delta_freq_Q7 = silk_LIMIT_32( delta_freq_Q7, -SILK_FIX_CONST( VARIABLE_HP_MAX_DELTA_FREQ, 7 ), SILK_FIX_CONST( VARIABLE_HP_MAX_DELTA_FREQ, 7 ) );
      |                                                      ^~~~~~~~~~~~~~
In file included from F:/circuit/firmware/a04/third_party/opus-1.6.1/silk/SigProc_FIX.h:39:
F:/circuit/firmware/a04/third_party/opus-1.6.1/silk/SigProc_FIX.h:539:88: warning: implicit conversion from 'float' to 'double' to match other operand of binary expression [-Wdouble-promotion]
  539 | #define SILK_FIX_CONST( C, Q )              ((opus_int32)((C) * ((opus_int64)1 << (Q)) + 0.5))
      |                                                                                        ^
F:/circuit/firmware/a04/third_party/opus-1.6.1/silk/macros.h:52:95: note: in definition of macro 'silk_SMLAWB'
   52 | #define silk_SMLAWB(a32, b32, c32)       ((a32) + ((((b32) >> 16) * (opus_int32)((opus_int16)(c32))) + ((((b32) & 0x0000FFFF) * (opus_int32)((opus_int16)(c32))) >> 16)))
      |                                                                                               ^~~
F:/circuit/firmware/a04/third_party/opus-1.6.1/silk/HP_variable_cutoff.c:70:72: note: in expansion of macro 'SILK_FIX_CONST'
   70 |             silk_SMULBB( psEncC1->speech_activity_Q8, delta_freq_Q7 ), SILK_FIX_CONST( VARIABLE_HP_SMTH_COEF1, 16 ) );
      |                                                                        ^~~~~~~~~~~~~~
F:/circuit/firmware/a04/third_party/opus-1.6.1/silk/SigProc_FIX.h:539:88: warning: implicit conversion from 'float' to 'double' to match other operand of binary expression [-Wdouble-promotion]
  539 | #define SILK_FIX_CONST( C, Q )              ((opus_int32)((C) * ((opus_int64)1 << (Q)) + 0.5))
      |                                                                                        ^
F:/circuit/firmware/a04/third_party/opus-1.6.1/silk/macros.h:52:155: note: in definition of macro 'silk_SMLAWB'
   52 | #define silk_SMLAWB(a32, b32, c32)       ((a32) + ((((b32) >> 16) * (opus_int32)((opus_int16)(c32))) + ((((b32) & 0x0000FFFF) * (opus_int32)((opus_int16)(c32))) >> 16)))
      |                                                                                                                                                           ^~~
F:/circuit/firmware/a04/third_party/opus-1.6.1/silk/HP_variable_cutoff.c:70:72: note: in expansion of macro 'SILK_FIX_CONST'
   70 |             silk_SMULBB( psEncC1->speech_activity_Q8, delta_freq_Q7 ), SILK_FIX_CONST( VARIABLE_HP_SMTH_COEF1, 16 ) );
      |                                                                        ^~~~~~~~~~~~~~
[411/503] Building C object opus/CMakeFiles/opus.dir/silk/NLSF_encode.c.obj
[412/503] Building C object opus/CMakeFiles/opus.dir/silk/NLSF_VQ.c.obj
[413/503] Building C object opus/CMakeFiles/opus.dir/silk/NLSF_unpack.c.obj
[414/503] Building C object opus/CMakeFiles/opus.dir/silk/process_NLSFs.c.obj
[415/503] Building C object opus/CMakeFiles/opus.dir/silk/NLSF_del_dec_quant.c.obj
[416/503] Building C object opus/CMakeFiles/opus.dir/silk/stereo_MS_to_LR.c.obj
[417/503] Building C object opus/CMakeFiles/opus.dir/silk/stereo_LR_to_MS.c.obj
[418/503] Building C object opus/CMakeFiles/opus.dir/silk/check_control_input.c.obj
[419/503] Building C object opus/CMakeFiles/opus.dir/silk/control_SNR.c.obj
[420/503] Building C object opus/CMakeFiles/opus.dir/silk/init_encoder.c.obj
[421/503] Building C object opus/CMakeFiles/opus.dir/silk/control_codec.c.obj
In file included from F:/circuit/firmware/a04/third_party/opus-1.6.1/silk/fixed/main_FIX.h:31,
                 from F:/circuit/firmware/a04/third_party/opus-1.6.1/silk/control_codec.c:32:
F:/circuit/firmware/a04/third_party/opus-1.6.1/silk/control_codec.c: In function 'silk_setup_complexity':
F:/circuit/firmware/a04/third_party/opus-1.6.1/silk/SigProc_FIX.h:539:88: warning: implicit conversion from 'float' to 'double' to match other operand of binary expression [-Wdouble-promotion]
  539 | #define SILK_FIX_CONST( C, Q )              ((opus_int32)((C) * ((opus_int64)1 << (Q)) + 0.5))
      |                                                                                        ^
F:/circuit/firmware/a04/third_party/opus-1.6.1/silk/control_codec.c:365:68: note: in expansion of macro 'SILK_FIX_CONST'
  365 |         psEncC->warping_Q16                     = psEncC->fs_kHz * SILK_FIX_CONST( WARPING_MULTIPLIER, 16 );
      |                                                                    ^~~~~~~~~~~~~~
F:/circuit/firmware/a04/third_party/opus-1.6.1/silk/SigProc_FIX.h:539:88: warning: implicit conversion from 'float' to 'double' to match other operand of binary expression [-Wdouble-promotion]
  539 | #define SILK_FIX_CONST( C, Q )              ((opus_int32)((C) * ((opus_int64)1 << (Q)) + 0.5))
      |                                                                                        ^
F:/circuit/firmware/a04/third_party/opus-1.6.1/silk/control_codec.c:375:68: note: in expansion of macro 'SILK_FIX_CONST'
  375 |         psEncC->warping_Q16                     = psEncC->fs_kHz * SILK_FIX_CONST( WARPING_MULTIPLIER, 16 );
      |                                                                    ^~~~~~~~~~~~~~
F:/circuit/firmware/a04/third_party/opus-1.6.1/silk/SigProc_FIX.h:539:88: warning: implicit conversion from 'float' to 'double' to match other operand of binary expression [-Wdouble-promotion]
  539 | #define SILK_FIX_CONST( C, Q )              ((opus_int32)((C) * ((opus_int64)1 << (Q)) + 0.5))
      |                                                                                        ^
F:/circuit/firmware/a04/third_party/opus-1.6.1/silk/control_codec.c:385:68: note: in expansion of macro 'SILK_FIX_CONST'
  385 |         psEncC->warping_Q16                     = psEncC->fs_kHz * SILK_FIX_CONST( WARPING_MULTIPLIER, 16 );
      |                                                                    ^~~~~~~~~~~~~~
[422/503] Building C object opus/CMakeFiles/opus.dir/silk/A2NLSF.c.obj
[423/503] Building C object opus/CMakeFiles/opus.dir/silk/ana_filt_bank_1.c.obj
[424/503] Building C object opus/CMakeFiles/opus.dir/silk/biquad_alt.c.obj
[425/503] Building C object opus/CMakeFiles/opus.dir/silk/bwexpander_32.c.obj
[426/503] Building C object opus/CMakeFiles/opus.dir/silk/debug.c.obj
[427/503] Building C object opus/CMakeFiles/opus.dir/silk/bwexpander.c.obj
[428/503] Building C object opus/CMakeFiles/opus.dir/silk/decode_pitch.c.obj
[429/503] Building C object opus/CMakeFiles/opus.dir/silk/inner_prod_aligned.c.obj
[430/503] Building C object opus/CMakeFiles/opus.dir/silk/lin2log.c.obj
[431/503] Building C object opus/CMakeFiles/opus.dir/silk/log2lin.c.obj
[432/503] Building C object opus/CMakeFiles/opus.dir/silk/LPC_analysis_filter.c.obj
[433/503] Building C object opus/CMakeFiles/opus.dir/silk/LPC_inv_pred_gain.c.obj
In file included from F:/circuit/firmware/a04/third_party/opus-1.6.1/silk/LPC_inv_pred_gain.c:32:
F:/circuit/firmware/a04/third_party/opus-1.6.1/silk/LPC_inv_pred_gain.c: In function 'LPC_inverse_pred_gain_QA_c':
F:/circuit/firmware/a04/third_party/opus-1.6.1/silk/SigProc_FIX.h:539:88: warning: implicit conversion from 'float' to 'double' to match other operand of binary expression [-Wdouble-promotion]
  539 | #define SILK_FIX_CONST( C, Q )              ((opus_int32)((C) * ((opus_int64)1 << (Q)) + 0.5))
      |                                                                                        ^
F:/circuit/firmware/a04/third_party/opus-1.6.1/silk/LPC_inv_pred_gain.c:70:27: note: in expansion of macro 'SILK_FIX_CONST'
   70 |         if( invGain_Q30 < SILK_FIX_CONST( 1.0f / MAX_PREDICTION_POWER_GAIN, 30 ) ) {
      |                           ^~~~~~~~~~~~~~
F:/circuit/firmware/a04/third_party/opus-1.6.1/silk/SigProc_FIX.h:539:88: warning: implicit conversion from 'float' to 'double' to match other operand of binary expression [-Wdouble-promotion]
  539 | #define SILK_FIX_CONST( C, Q )              ((opus_int32)((C) * ((opus_int64)1 << (Q)) + 0.5))
      |                                                                                        ^
F:/circuit/firmware/a04/third_party/opus-1.6.1/silk/LPC_inv_pred_gain.c:114:23: note: in expansion of macro 'SILK_FIX_CONST'
  114 |     if( invGain_Q30 < SILK_FIX_CONST( 1.0f / MAX_PREDICTION_POWER_GAIN, 30 ) ) {
      |                       ^~~~~~~~~~~~~~
[434/503] Building C object opus/CMakeFiles/opus.dir/silk/table_LSF_cos.c.obj
[435/503] Building C object opus/CMakeFiles/opus.dir/silk/NLSF2A.c.obj
[436/503] Building C object opus/CMakeFiles/opus.dir/silk/NLSF_stabilize.c.obj
[437/503] Building C object opus/CMakeFiles/opus.dir/silk/NLSF_VQ_weights_laroia.c.obj
[438/503] Building C object opus/CMakeFiles/opus.dir/silk/pitch_est_tables.c.obj
[439/503] Building C object opus/CMakeFiles/opus.dir/silk/resampler.c.obj
[440/503] Building C object opus/CMakeFiles/opus.dir/silk/resampler_down2_3.c.obj
[441/503] Building C object opus/CMakeFiles/opus.dir/silk/resampler_down2.c.obj
[442/503] Building C object opus/CMakeFiles/opus.dir/silk/resampler_private_AR2.c.obj
[443/503] Building C object opus/CMakeFiles/opus.dir/silk/resampler_private_IIR_FIR.c.obj
[444/503] Building C object opus/CMakeFiles/opus.dir/silk/resampler_private_down_FIR.c.obj
[445/503] Building C object opus/CMakeFiles/opus.dir/silk/resampler_private_up2_HQ.c.obj
[446/503] Building C object opus/CMakeFiles/opus.dir/silk/resampler_rom.c.obj
[447/503] Building C object opus/CMakeFiles/opus.dir/silk/sigm_Q15.c.obj
[448/503] Building C object opus/CMakeFiles/opus.dir/silk/sort.c.obj
[449/503] Building C object opus/CMakeFiles/opus.dir/silk/sum_sqr_shift.c.obj
[450/503] Building C object opus/CMakeFiles/opus.dir/silk/stereo_decode_pred.c.obj
[451/503] Building C object opus/CMakeFiles/opus.dir/silk/stereo_encode_pred.c.obj
[452/503] Building C object opus/CMakeFiles/opus.dir/silk/stereo_quant_pred.c.obj
[453/503] Building C object opus/CMakeFiles/opus.dir/silk/stereo_find_predictor.c.obj
[454/503] Building C object opus/CMakeFiles/opus.dir/silk/LPC_fit.c.obj
[455/503] Building C object opus/CMakeFiles/opus.dir/celt/celt.c.obj
In file included from F:/circuit/firmware/a04/third_party/opus-1.6.1/celt/celt.c:48:
F:/circuit/firmware/a04/third_party/opus-1.6.1/celt/float_cast.h:142:10: warning: #warning "Don't have the functions lrint() and lrintf ()." [-Wcpp]
  142 |         #warning "Don't have the functions lrint() and lrintf ()."
      |          ^~~~~~~
F:/circuit/firmware/a04/third_party/opus-1.6.1/celt/float_cast.h:143:10: warning: #warning "Replacing these functions with a standard C cast." [-Wcpp]
  143 |         #warning "Replacing these functions with a standard C cast."
      |          ^~~~~~~
In file included from F:/circuit/firmware/a04/third_party/opus-1.6.1/celt/arch.h:238,
                 from F:/circuit/firmware/a04/third_party/opus-1.6.1/celt/kiss_fft.h:34,
                 from F:/circuit/firmware/a04/third_party/opus-1.6.1/celt/mdct.h:46,
                 from F:/circuit/firmware/a04/third_party/opus-1.6.1/celt/celt.c:37:
F:/circuit/firmware/a04/third_party/opus-1.6.1/celt/celt.c: In function 'comb_filter':
F:/circuit/firmware/a04/third_party/opus-1.6.1/celt/fixed_generic.h:92:42: warning: implicit conversion from 'float' to 'double' to match other operand of binary expression [-Wdouble-promotion]
   92 | #define QCONST16(x,bits) ((opus_val16)(.5+(x)*(((opus_val32)1)<<(bits))))
      |                                          ^
F:/circuit/firmware/a04/third_party/opus-1.6.1/celt/celt.c:247:11: note: in expansion of macro 'QCONST16'
  247 |          {QCONST16(0.3066406250f, 15), QCONST16(0.2170410156f, 15), QCONST16(0.1296386719f, 15)},
      |           ^~~~~~~~
F:/circuit/firmware/a04/third_party/opus-1.6.1/celt/fixed_generic.h:92:42: warning: implicit conversion from 'float' to 'double' to match other operand of binary expression [-Wdouble-promotion]
   92 | #define QCONST16(x,bits) ((opus_val16)(.5+(x)*(((opus_val32)1)<<(bits))))
      |                                          ^
F:/circuit/firmware/a04/third_party/opus-1.6.1/celt/celt.c:247:40: note: in expansion of macro 'QCONST16'
  247 |          {QCONST16(0.3066406250f, 15), QCONST16(0.2170410156f, 15), QCONST16(0.1296386719f, 15)},
      |                                        ^~~~~~~~
F:/circuit/firmware/a04/third_party/opus-1.6.1/celt/fixed_generic.h:92:42: warning: implicit conversion from 'float' to 'double' to match other operand of binary expression [-Wdouble-promotion]
   92 | #define QCONST16(x,bits) ((opus_val16)(.5+(x)*(((opus_val32)1)<<(bits))))
      |                                          ^
F:/circuit/firmware/a04/third_party/opus-1.6.1/celt/celt.c:247:69: note: in expansion of macro 'QCONST16'
  247 |          {QCONST16(0.3066406250f, 15), QCONST16(0.2170410156f, 15), QCONST16(0.1296386719f, 15)},
      |                                                                     ^~~~~~~~
F:/circuit/firmware/a04/third_party/opus-1.6.1/celt/fixed_generic.h:92:42: warning: implicit conversion from 'float' to 'double' to match other operand of binary expression [-Wdouble-promotion]
   92 | #define QCONST16(x,bits) ((opus_val16)(.5+(x)*(((opus_val32)1)<<(bits))))
      |                                          ^
F:/circuit/firmware/a04/third_party/opus-1.6.1/celt/celt.c:248:11: note: in expansion of macro 'QCONST16'
  248 |          {QCONST16(0.4638671875f, 15), QCONST16(0.2680664062f, 15), QCONST16(0.f, 15)},
      |           ^~~~~~~~
F:/circuit/firmware/a04/third_party/opus-1.6.1/celt/fixed_generic.h:92:42: warning: implicit conversion from 'float' to 'double' to match other operand of binary expression [-Wdouble-promotion]
   92 | #define QCONST16(x,bits) ((opus_val16)(.5+(x)*(((opus_val32)1)<<(bits))))
      |                                          ^
F:/circuit/firmware/a04/third_party/opus-1.6.1/celt/celt.c:248:40: note: in expansion of macro 'QCONST16'
  248 |          {QCONST16(0.4638671875f, 15), QCONST16(0.2680664062f, 15), QCONST16(0.f, 15)},
      |                                        ^~~~~~~~
F:/circuit/firmware/a04/third_party/opus-1.6.1/celt/fixed_generic.h:92:42: warning: implicit conversion from 'float' to 'double' to match other operand of binary expression [-Wdouble-promotion]
   92 | #define QCONST16(x,bits) ((opus_val16)(.5+(x)*(((opus_val32)1)<<(bits))))
      |                                          ^
F:/circuit/firmware/a04/third_party/opus-1.6.1/celt/celt.c:248:69: note: in expansion of macro 'QCONST16'
  248 |          {QCONST16(0.4638671875f, 15), QCONST16(0.2680664062f, 15), QCONST16(0.f, 15)},
      |                                                                     ^~~~~~~~
F:/circuit/firmware/a04/third_party/opus-1.6.1/celt/fixed_generic.h:92:42: warning: implicit conversion from 'float' to 'double' to match other operand of binary expression [-Wdouble-promotion]
   92 | #define QCONST16(x,bits) ((opus_val16)(.5+(x)*(((opus_val32)1)<<(bits))))
      |                                          ^
F:/circuit/firmware/a04/third_party/opus-1.6.1/celt/celt.c:249:11: note: in expansion of macro 'QCONST16'
  249 |          {QCONST16(0.7998046875f, 15), QCONST16(0.1000976562f, 15), QCONST16(0.f, 15)}};
      |           ^~~~~~~~
F:/circuit/firmware/a04/third_party/opus-1.6.1/celt/fixed_generic.h:92:42: warning: implicit conversion from 'float' to 'double' to match other operand of binary expression [-Wdouble-promotion]
   92 | #define QCONST16(x,bits) ((opus_val16)(.5+(x)*(((opus_val32)1)<<(bits))))
      |                                          ^
F:/circuit/firmware/a04/third_party/opus-1.6.1/celt/celt.c:249:40: note: in expansion of macro 'QCONST16'
  249 |          {QCONST16(0.7998046875f, 15), QCONST16(0.1000976562f, 15), QCONST16(0.f, 15)}};
      |                                        ^~~~~~~~
F:/circuit/firmware/a04/third_party/opus-1.6.1/celt/fixed_generic.h:92:42: warning: implicit conversion from 'float' to 'double' to match other operand of binary expression [-Wdouble-promotion]
   92 | #define QCONST16(x,bits) ((opus_val16)(.5+(x)*(((opus_val32)1)<<(bits))))
      |                                          ^
F:/circuit/firmware/a04/third_party/opus-1.6.1/celt/celt.c:249:69: note: in expansion of macro 'QCONST16'
  249 |          {QCONST16(0.7998046875f, 15), QCONST16(0.1000976562f, 15), QCONST16(0.f, 15)}};
      |                                                                     ^~~~~~~~
[456/503] Building C object opus/CMakeFiles/opus.dir/celt/bands.c.obj
In file included from F:/circuit/firmware/a04/third_party/opus-1.6.1/celt/arch.h:238,
                 from F:/circuit/firmware/a04/third_party/opus-1.6.1/celt/bands.h:33,
                 from F:/circuit/firmware/a04/third_party/opus-1.6.1/celt/bands.c:35:
F:/circuit/firmware/a04/third_party/opus-1.6.1/celt/bands.c: In function 'anti_collapse':
F:/circuit/firmware/a04/third_party/opus-1.6.1/celt/fixed_generic.h:92:42: warning: implicit conversion from 'float' to 'double' to match other operand of binary expression [-Wdouble-promotion]
   92 | #define QCONST16(x,bits) ((opus_val16)(.5+(x)*(((opus_val32)1)<<(bits))))
      |                                          ^
F:/circuit/firmware/a04/third_party/opus-1.6.1/celt/fixed_generic.h:152:34: note: in definition of macro 'ADD32'
  152 | #define ADD32(a,b) ((opus_val32)(a)+(opus_val32)(b))
      |                                  ^
F:/circuit/firmware/a04/third_party/opus-1.6.1/celt/fixed_generic.h:132:22: note: in expansion of macro 'SHL32'
  132 | #define SHL(a,shift) SHL32(a,shift)
      |                      ^~~~~
F:/circuit/firmware/a04/third_party/opus-1.6.1/celt/fixed_generic.h:57:34: note: in expansion of macro 'SHL'
   57 | #define MULT16_32_Q15(a,b) ADD32(SHL(MULT16_16((a),SHR((b),16)),1), SHR(MULT16_16SU((a),((b)&0x0000ffff)),15))
      |                                  ^~~
F:/circuit/firmware/a04/third_party/opus-1.6.1/celt/fixed_generic.h:57:38: note: in expansion of macro 'MULT16_16'
   57 | #define MULT16_32_Q15(a,b) ADD32(SHL(MULT16_16((a),SHR((b),16)),1), SHR(MULT16_16SU((a),((b)&0x0000ffff)),15))
      |                                      ^~~~~~~~~
F:/circuit/firmware/a04/third_party/opus-1.6.1/celt/bands.c:281:16: note: in expansion of macro 'MULT16_32_Q15'
  281 |       thresh = MULT16_32_Q15(QCONST16(0.5f, 15), MIN32(32767,thresh32));
      |                ^~~~~~~~~~~~~
F:/circuit/firmware/a04/third_party/opus-1.6.1/celt/bands.c:281:30: note: in expansion of macro 'QCONST16'
  281 |       thresh = MULT16_32_Q15(QCONST16(0.5f, 15), MIN32(32767,thresh32));
      |                              ^~~~~~~~
F:/circuit/firmware/a04/third_party/opus-1.6.1/celt/fixed_generic.h:92:42: warning: implicit conversion from 'float' to 'double' to match other operand of binary expression [-Wdouble-promotion]
   92 | #define QCONST16(x,bits) ((opus_val16)(.5+(x)*(((opus_val32)1)<<(bits))))
      |                                          ^
F:/circuit/firmware/a04/third_party/opus-1.6.1/celt/fixed_generic.h:152:50: note: in definition of macro 'ADD32'
  152 | #define ADD32(a,b) ((opus_val32)(a)+(opus_val32)(b))
      |                                                  ^
F:/circuit/firmware/a04/third_party/opus-1.6.1/celt/fixed_generic.h:57:69: note: in expansion of macro 'SHR'
   57 | #define MULT16_32_Q15(a,b) ADD32(SHL(MULT16_16((a),SHR((b),16)),1), SHR(MULT16_16SU((a),((b)&0x0000ffff)),15))
      |                                                                     ^~~
F:/circuit/firmware/a04/third_party/opus-1.6.1/celt/fixed_generic.h:57:73: note: in expansion of macro 'MULT16_16SU'
   57 | #define MULT16_32_Q15(a,b) ADD32(SHL(MULT16_16((a),SHR((b),16)),1), SHR(MULT16_16SU((a),((b)&0x0000ffff)),15))
      |                                                                         ^~~~~~~~~~~
F:/circuit/firmware/a04/third_party/opus-1.6.1/celt/bands.c:281:16: note: in expansion of macro 'MULT16_32_Q15'
  281 |       thresh = MULT16_32_Q15(QCONST16(0.5f, 15), MIN32(32767,thresh32));
      |                ^~~~~~~~~~~~~
F:/circuit/firmware/a04/third_party/opus-1.6.1/celt/bands.c:281:30: note: in expansion of macro 'QCONST16'
  281 |       thresh = MULT16_32_Q15(QCONST16(0.5f, 15), MIN32(32767,thresh32));
      |                              ^~~~~~~~
F:/circuit/firmware/a04/third_party/opus-1.6.1/celt/fixed_generic.h:98:40: warning: implicit conversion from 'float' to 'double' to match other operand of binary expression [-Wdouble-promotion]
   98 | #define GCONST2(x,bits) ((celt_glog)(.5+(x)*(((celt_glog)1)<<(bits))))
      |                                        ^
F:/circuit/firmware/a04/third_party/opus-1.6.1/celt/fixed_generic.h:101:19: note: in expansion of macro 'GCONST2'
  101 | #define GCONST(x) GCONST2((x),DB_SHIFT)
      |                   ^~~~~~~
F:/circuit/firmware/a04/third_party/opus-1.6.1/celt/bands.c:313:22: note: in expansion of macro 'GCONST'
  313 |          if (Ediff < GCONST(16.f))
      |                      ^~~~~~
F:/circuit/firmware/a04/third_party/opus-1.6.1/celt/bands.c: In function 'stereo_split':
F:/circuit/firmware/a04/third_party/opus-1.6.1/celt/fixed_generic.h:95:42: warning: implicit conversion from 'float' to 'double' to match other operand of binary expression [-Wdouble-promotion]
   95 | #define QCONST32(x,bits) ((opus_val32)(.5+(x)*(((opus_int64)1)<<(bits))))
      |                                          ^
F:/circuit/firmware/a04/third_party/opus-1.6.1/celt/fixed_generic.h:152:34: note: in definition of macro 'ADD32'
  152 | #define ADD32(a,b) ((opus_val32)(a)+(opus_val32)(b))
      |                                  ^
F:/circuit/firmware/a04/third_party/opus-1.6.1/celt/fixed_generic.h:71:34: note: in expansion of macro 'ADD32'
   71 | #define MULT32_32_Q31(a,b) ADD32(ADD32(SHL(MULT16_16(SHR((a),16),SHR((b),16)),1), SHR(MULT16_16SU(SHR((a),16),((b)&0x0000ffff)),15)), SHR(MULT16_16SU(SHR((b),16),((a)&0x0000ffff)),15))
      |                                  ^~~~~
F:/circuit/firmware/a04/third_party/opus-1.6.1/celt/fixed_generic.h:132:22: note: in expansion of macro 'SHL32'
  132 | #define SHL(a,shift) SHL32(a,shift)
      |                      ^~~~~
F:/circuit/firmware/a04/third_party/opus-1.6.1/celt/fixed_generic.h:71:40: note: in expansion of macro 'SHL'
   71 | #define MULT32_32_Q31(a,b) ADD32(ADD32(SHL(MULT16_16(SHR((a),16),SHR((b),16)),1), SHR(MULT16_16SU(SHR((a),16),((b)&0x0000ffff)),15)), SHR(MULT16_16SU(SHR((b),16),((a)&0x0000ffff)),15))
      |                                        ^~~
F:/circuit/firmware/a04/third_party/opus-1.6.1/celt/fixed_generic.h:71:44: note: in expansion of macro 'MULT16_16'
   71 | #define MULT32_32_Q31(a,b) ADD32(ADD32(SHL(MULT16_16(SHR((a),16),SHR((b),16)),1), SHR(MULT16_16SU(SHR((a),16),((b)&0x0000ffff)),15)), SHR(MULT16_16SU(SHR((b),16),((a)&0x0000ffff)),15))
      |                                            ^~~~~~~~~
F:/circuit/firmware/a04/third_party/opus-1.6.1/celt/fixed_generic.h:71:54: note: in expansion of macro 'SHR'
   71 | #define MULT32_32_Q31(a,b) ADD32(ADD32(SHL(MULT16_16(SHR((a),16),SHR((b),16)),1), SHR(MULT16_16SU(SHR((a),16),((b)&0x0000ffff)),15)), SHR(MULT16_16SU(SHR((b),16),((a)&0x0000ffff)),15))
      |                                                      ^~~
F:/circuit/firmware/a04/third_party/opus-1.6.1/celt/bands.c:411:11: note: in expansion of macro 'MULT32_32_Q31'
  411 |       l = MULT32_32_Q31(QCONST32(.70710678f,31), X[j]);
      |           ^~~~~~~~~~~~~
F:/circuit/firmware/a04/third_party/opus-1.6.1/celt/bands.c:411:25: note: in expansion of macro 'QCONST32'
  411 |       l = MULT32_32_Q31(QCONST32(.70710678f,31), X[j]);
      |                         ^~~~~~~~
F:/circuit/firmware/a04/third_party/opus-1.6.1/celt/fixed_generic.h:95:42: warning: implicit conversion from 'float' to 'double' to match other operand of binary expression [-Wdouble-promotion]
   95 | #define QCONST32(x,bits) ((opus_val32)(.5+(x)*(((opus_int64)1)<<(bits))))
      |                                          ^
F:/circuit/firmware/a04/third_party/opus-1.6.1/celt/fixed_generic.h:152:34: note: in definition of macro 'ADD32'
  152 | #define ADD32(a,b) ((opus_val32)(a)+(opus_val32)(b))
      |                                  ^
F:/circuit/firmware/a04/third_party/opus-1.6.1/celt/fixed_generic.h:71:34: note: in expansion of macro 'ADD32'
   71 | #define MULT32_32_Q31(a,b) ADD32(ADD32(SHL(MULT16_16(SHR((a),16),SHR((b),16)),1), SHR(MULT16_16SU(SHR((a),16),((b)&0x0000ffff)),15)), SHR(MULT16_16SU(SHR((b),16),((a)&0x0000ffff)),15))
      |                                  ^~~~~
F:/circuit/firmware/a04/third_party/opus-1.6.1/celt/fixed_generic.h:71:83: note: in expansion of macro 'SHR'
   71 | #define MULT32_32_Q31(a,b) ADD32(ADD32(SHL(MULT16_16(SHR((a),16),SHR((b),16)),1), SHR(MULT16_16SU(SHR((a),16),((b)&0x0000ffff)),15)), SHR(MULT16_16SU(SHR((b),16),((a)&0x0000ffff)),15))
      |                                                                                   ^~~
F:/circuit/firmware/a04/third_party/opus-1.6.1/celt/fixed_generic.h:71:87: note: in expansion of macro 'MULT16_16SU'
   71 | #define MULT32_32_Q31(a,b) ADD32(ADD32(SHL(MULT16_16(SHR((a),16),SHR((b),16)),1), SHR(MULT16_16SU(SHR((a),16),((b)&0x0000ffff)),15)), SHR(MULT16_16SU(SHR((b),16),((a)&0x0000ffff)),15))
      |                                                                                       ^~~~~~~~~~~
F:/circuit/firmware/a04/third_party/opus-1.6.1/celt/fixed_generic.h:71:99: note: in expansion of macro 'SHR'
   71 | #define MULT32_32_Q31(a,b) ADD32(ADD32(SHL(MULT16_16(SHR((a),16),SHR((b),16)),1), SHR(MULT16_16SU(SHR((a),16),((b)&0x0000ffff)),15)), SHR(MULT16_16SU(SHR((b),16),((a)&0x0000ffff)),15))
      |                                                                                                   ^~~
F:/circuit/firmware/a04/third_party/opus-1.6.1/celt/bands.c:411:11: note: in expansion of macro 'MULT32_32_Q31'
  411 |       l = MULT32_32_Q31(QCONST32(.70710678f,31), X[j]);
      |           ^~~~~~~~~~~~~
F:/circuit/firmware/a04/third_party/opus-1.6.1/celt/bands.c:411:25: note: in expansion of macro 'QCONST32'
  411 |       l = MULT32_32_Q31(QCONST32(.70710678f,31), X[j]);
      |                         ^~~~~~~~
F:/circuit/firmware/a04/third_party/opus-1.6.1/celt/fixed_generic.h:95:42: warning: implicit conversion from 'float' to 'double' to match other operand of binary expression [-Wdouble-promotion]
   95 | #define QCONST32(x,bits) ((opus_val32)(.5+(x)*(((opus_int64)1)<<(bits))))
      |                                          ^
F:/circuit/firmware/a04/third_party/opus-1.6.1/celt/fixed_generic.h:152:50: note: in definition of macro 'ADD32'
  152 | #define ADD32(a,b) ((opus_val32)(a)+(opus_val32)(b))
      |                                                  ^
F:/circuit/firmware/a04/third_party/opus-1.6.1/celt/fixed_generic.h:71:135: note: in expansion of macro 'SHR'
   71 | #define MULT32_32_Q31(a,b) ADD32(ADD32(SHL(MULT16_16(SHR((a),16),SHR((b),16)),1), SHR(MULT16_16SU(SHR((a),16),((b)&0x0000ffff)),15)), SHR(MULT16_16SU(SHR((b),16),((a)&0x0000ffff)),15))
      |                                                                                                                                       ^~~
F:/circuit/firmware/a04/third_party/opus-1.6.1/celt/fixed_generic.h:71:139: note: in expansion of macro 'MULT16_16SU'
   71 | #define MULT32_32_Q31(a,b) ADD32(ADD32(SHL(MULT16_16(SHR((a),16),SHR((b),16)),1), SHR(MULT16_16SU(SHR((a),16),((b)&0x0000ffff)),15)), SHR(MULT16_16SU(SHR((b),16),((a)&0x0000ffff)),15))
      |                                                                                                                                           ^~~~~~~~~~~
F:/circuit/firmware/a04/third_party/opus-1.6.1/celt/bands.c:411:11: note: in expansion of macro 'MULT32_32_Q31'
  411 |       l = MULT32_32_Q31(QCONST32(.70710678f,31), X[j]);
      |           ^~~~~~~~~~~~~
F:/circuit/firmware/a04/third_party/opus-1.6.1/celt/bands.c:411:25: note: in expansion of macro 'QCONST32'
  411 |       l = MULT32_32_Q31(QCONST32(.70710678f,31), X[j]);
      |                         ^~~~~~~~
F:/circuit/firmware/a04/third_party/opus-1.6.1/celt/fixed_generic.h:95:42: warning: implicit conversion from 'float' to 'double' to match other operand of binary expression [-Wdouble-promotion]
   95 | #define QCONST32(x,bits) ((opus_val32)(.5+(x)*(((opus_int64)1)<<(bits))))
      |                                          ^
F:/circuit/firmware/a04/third_party/opus-1.6.1/celt/fixed_generic.h:152:34: note: in definition of macro 'ADD32'
  152 | #define ADD32(a,b) ((opus_val32)(a)+(opus_val32)(b))
      |                                  ^
F:/circuit/firmware/a04/third_party/opus-1.6.1/celt/fixed_generic.h:71:34: note: in expansion of macro 'ADD32'
   71 | #define MULT32_32_Q31(a,b) ADD32(ADD32(SHL(MULT16_16(SHR((a),16),SHR((b),16)),1), SHR(MULT16_16SU(SHR((a),16),((b)&0x0000ffff)),15)), SHR(MULT16_16SU(SHR((b),16),((a)&0x0000ffff)),15))
      |                                  ^~~~~
F:/circuit/firmware/a04/third_party/opus-1.6.1/celt/fixed_generic.h:132:22: note: in expansion of macro 'SHL32'
  132 | #define SHL(a,shift) SHL32(a,shift)
      |                      ^~~~~
F:/circuit/firmware/a04/third_party/opus-1.6.1/celt/fixed_generic.h:71:40: note: in expansion of macro 'SHL'
   71 | #define MULT32_32_Q31(a,b) ADD32(ADD32(SHL(MULT16_16(SHR((a),16),SHR((b),16)),1), SHR(MULT16_16SU(SHR((a),16),((b)&0x0000ffff)),15)), SHR(MULT16_16SU(SHR((b),16),((a)&0x0000ffff)),15))
      |                                        ^~~
F:/circuit/firmware/a04/third_party/opus-1.6.1/celt/fixed_generic.h:71:44: note: in expansion of macro 'MULT16_16'
   71 | #define MULT32_32_Q31(a,b) ADD32(ADD32(SHL(MULT16_16(SHR((a),16),SHR((b),16)),1), SHR(MULT16_16SU(SHR((a),16),((b)&0x0000ffff)),15)), SHR(MULT16_16SU(SHR((b),16),((a)&0x0000ffff)),15))
      |                                            ^~~~~~~~~
F:/circuit/firmware/a04/third_party/opus-1.6.1/celt/fixed_generic.h:71:54: note: in expansion of macro 'SHR'
   71 | #define MULT32_32_Q31(a,b) ADD32(ADD32(SHL(MULT16_16(SHR((a),16),SHR((b),16)),1), SHR(MULT16_16SU(SHR((a),16),((b)&0x0000ffff)),15)), SHR(MULT16_16SU(SHR((b),16),((a)&0x0000ffff)),15))
      |                                                      ^~~
F:/circuit/firmware/a04/third_party/opus-1.6.1/celt/bands.c:412:11: note: in expansion of macro 'MULT32_32_Q31'
  412 |       r = MULT32_32_Q31(QCONST32(.70710678f,31), Y[j]);
      |           ^~~~~~~~~~~~~
F:/circuit/firmware/a04/third_party/opus-1.6.1/celt/bands.c:412:25: note: in expansion of macro 'QCONST32'
  412 |       r = MULT32_32_Q31(QCONST32(.70710678f,31), Y[j]);
      |                         ^~~~~~~~
F:/circuit/firmware/a04/third_party/opus-1.6.1/celt/fixed_generic.h:95:42: warning: implicit conversion from 'float' to 'double' to match other operand of binary expression [-Wdouble-promotion]
   95 | #define QCONST32(x,bits) ((opus_val32)(.5+(x)*(((opus_int64)1)<<(bits))))
      |                                          ^
F:/circuit/firmware/a04/third_party/opus-1.6.1/celt/fixed_generic.h:152:34: note: in definition of macro 'ADD32'
  152 | #define ADD32(a,b) ((opus_val32)(a)+(opus_val32)(b))
      |                                  ^
F:/circuit/firmware/a04/third_party/opus-1.6.1/celt/fixed_generic.h:71:34: note: in expansion of macro 'ADD32'
   71 | #define MULT32_32_Q31(a,b) ADD32(ADD32(SHL(MULT16_16(SHR((a),16),SHR((b),16)),1), SHR(MULT16_16SU(SHR((a),16),((b)&0x0000ffff)),15)), SHR(MULT16_16SU(SHR((b),16),((a)&0x0000ffff)),15))
      |                                  ^~~~~
F:/circuit/firmware/a04/third_party/opus-1.6.1/celt/fixed_generic.h:71:83: note: in expansion of macro 'SHR'
   71 | #define MULT32_32_Q31(a,b) ADD32(ADD32(SHL(MULT16_16(SHR((a),16),SHR((b),16)),1), SHR(MULT16_16SU(SHR((a),16),((b)&0x0000ffff)),15)), SHR(MULT16_16SU(SHR((b),16),((a)&0x0000ffff)),15))
      |                                                                                   ^~~
F:/circuit/firmware/a04/third_party/opus-1.6.1/celt/fixed_generic.h:71:87: note: in expansion of macro 'MULT16_16SU'
   71 | #define MULT32_32_Q31(a,b) ADD32(ADD32(SHL(MULT16_16(SHR((a),16),SHR((b),16)),1), SHR(MULT16_16SU(SHR((a),16),((b)&0x0000ffff)),15)), SHR(MULT16_16SU(SHR((b),16),((a)&0x0000ffff)),15))
      |                                                                                       ^~~~~~~~~~~
F:/circuit/firmware/a04/third_party/opus-1.6.1/celt/fixed_generic.h:71:99: note: in expansion of macro 'SHR'
   71 | #define MULT32_32_Q31(a,b) ADD32(ADD32(SHL(MULT16_16(SHR((a),16),SHR((b),16)),1), SHR(MULT16_16SU(SHR((a),16),((b)&0x0000ffff)),15)), SHR(MULT16_16SU(SHR((b),16),((a)&0x0000ffff)),15))
      |                                                                                                   ^~~
F:/circuit/firmware/a04/third_party/opus-1.6.1/celt/bands.c:412:11: note: in expansion of macro 'MULT32_32_Q31'
  412 |       r = MULT32_32_Q31(QCONST32(.70710678f,31), Y[j]);
      |           ^~~~~~~~~~~~~
F:/circuit/firmware/a04/third_party/opus-1.6.1/celt/bands.c:412:25: note: in expansion of macro 'QCONST32'
  412 |       r = MULT32_32_Q31(QCONST32(.70710678f,31), Y[j]);
      |                         ^~~~~~~~
F:/circuit/firmware/a04/third_party/opus-1.6.1/celt/fixed_generic.h:95:42: warning: implicit conversion from 'float' to 'double' to match other operand of binary expression [-Wdouble-promotion]
   95 | #define QCONST32(x,bits) ((opus_val32)(.5+(x)*(((opus_int64)1)<<(bits))))
      |                                          ^
F:/circuit/firmware/a04/third_party/opus-1.6.1/celt/fixed_generic.h:152:50: note: in definition of macro 'ADD32'
  152 | #define ADD32(a,b) ((opus_val32)(a)+(opus_val32)(b))
      |                                                  ^
F:/circuit/firmware/a04/third_party/opus-1.6.1/celt/fixed_generic.h:71:135: note: in expansion of macro 'SHR'
   71 | #define MULT32_32_Q31(a,b) ADD32(ADD32(SHL(MULT16_16(SHR((a),16),SHR((b),16)),1), SHR(MULT16_16SU(SHR((a),16),((b)&0x0000ffff)),15)), SHR(MULT16_16SU(SHR((b),16),((a)&0x0000ffff)),15))
      |                                                                                                                                       ^~~
F:/circuit/firmware/a04/third_party/opus-1.6.1/celt/fixed_generic.h:71:139: note: in expansion of macro 'MULT16_16SU'
   71 | #define MULT32_32_Q31(a,b) ADD32(ADD32(SHL(MULT16_16(SHR((a),16),SHR((b),16)),1), SHR(MULT16_16SU(SHR((a),16),((b)&0x0000ffff)),15)), SHR(MULT16_16SU(SHR((b),16),((a)&0x0000ffff)),15))
      |                                                                                                                                           ^~~~~~~~~~~
F:/circuit/firmware/a04/third_party/opus-1.6.1/celt/bands.c:412:11: note: in expansion of macro 'MULT32_32_Q31'
  412 |       r = MULT32_32_Q31(QCONST32(.70710678f,31), Y[j]);
      |           ^~~~~~~~~~~~~
F:/circuit/firmware/a04/third_party/opus-1.6.1/celt/bands.c:412:25: note: in expansion of macro 'QCONST32'
  412 |       r = MULT32_32_Q31(QCONST32(.70710678f,31), Y[j]);
      |                         ^~~~~~~~
F:/circuit/firmware/a04/third_party/opus-1.6.1/celt/bands.c: In function 'stereo_merge':
F:/circuit/firmware/a04/third_party/opus-1.6.1/celt/fixed_generic.h:95:42: warning: implicit conversion from 'float' to 'double' to match other operand of binary expression [-Wdouble-promotion]
   95 | #define QCONST32(x,bits) ((opus_val32)(.5+(x)*(((opus_int64)1)<<(bits))))
      |                                          ^
F:/circuit/firmware/a04/third_party/opus-1.6.1/celt/bands.c:436:13: note: in expansion of macro 'QCONST32'
  436 |    if (Er < QCONST32(6e-4f, 28) || El < QCONST32(6e-4f, 28))
      |             ^~~~~~~~
F:/circuit/firmware/a04/third_party/opus-1.6.1/celt/fixed_generic.h:95:42: warning: implicit conversion from 'float' to 'double' to match other operand of binary expression [-Wdouble-promotion]
   95 | #define QCONST32(x,bits) ((opus_val32)(.5+(x)*(((opus_int64)1)<<(bits))))
      |                                          ^
F:/circuit/firmware/a04/third_party/opus-1.6.1/celt/bands.c:436:41: note: in expansion of macro 'QCONST32'
  436 |    if (Er < QCONST32(6e-4f, 28) || El < QCONST32(6e-4f, 28))
      |                                         ^~~~~~~~
F:/circuit/firmware/a04/third_party/opus-1.6.1/celt/bands.c: In function 'spreading_decision':
F:/circuit/firmware/a04/third_party/opus-1.6.1/celt/fixed_generic.h:92:42: warning: implicit conversion from 'float' to 'double' to match other operand of binary expression [-Wdouble-promotion]
   92 | #define QCONST16(x,bits) ((opus_val16)(.5+(x)*(((opus_val32)1)<<(bits))))
      |                                          ^
F:/circuit/firmware/a04/third_party/opus-1.6.1/celt/bands.c:501:23: note: in expansion of macro 'QCONST16'
  501 |             if (x2N < QCONST16(0.25f,13))
      |                       ^~~~~~~~
F:/circuit/firmware/a04/third_party/opus-1.6.1/celt/fixed_generic.h:92:42: warning: implicit conversion from 'float' to 'double' to match other operand of binary expression [-Wdouble-promotion]
   92 | #define QCONST16(x,bits) ((opus_val16)(.5+(x)*(((opus_val32)1)<<(bits))))
      |                                          ^
F:/circuit/firmware/a04/third_party/opus-1.6.1/celt/bands.c:503:23: note: in expansion of macro 'QCONST16'
  503 |             if (x2N < QCONST16(0.0625f,13))
      |                       ^~~~~~~~
F:/circuit/firmware/a04/third_party/opus-1.6.1/celt/fixed_generic.h:92:42: warning: implicit conversion from 'float' to 'double' to match other operand of binary expression [-Wdouble-promotion]
   92 | #define QCONST16(x,bits) ((opus_val16)(.5+(x)*(((opus_val32)1)<<(bits))))
      |                                          ^
F:/circuit/firmware/a04/third_party/opus-1.6.1/celt/bands.c:505:23: note: in expansion of macro 'QCONST16'
  505 |             if (x2N < QCONST16(0.015625f,13))
      |                       ^~~~~~~~
F:/circuit/firmware/a04/third_party/opus-1.6.1/celt/bands.c: In function 'haar1':
F:/circuit/firmware/a04/third_party/opus-1.6.1/celt/fixed_generic.h:95:42: warning: implicit conversion from 'float' to 'double' to match other operand of binary expression [-Wdouble-promotion]
   95 | #define QCONST32(x,bits) ((opus_val32)(.5+(x)*(((opus_int64)1)<<(bits))))
      |                                          ^
F:/circuit/firmware/a04/third_party/opus-1.6.1/celt/fixed_generic.h:152:34: note: in definition of macro 'ADD32'
  152 | #define ADD32(a,b) ((opus_val32)(a)+(opus_val32)(b))
      |                                  ^
F:/circuit/firmware/a04/third_party/opus-1.6.1/celt/fixed_generic.h:71:34: note: in expansion of macro 'ADD32'
   71 | #define MULT32_32_Q31(a,b) ADD32(ADD32(SHL(MULT16_16(SHR((a),16),SHR((b),16)),1), SHR(MULT16_16SU(SHR((a),16),((b)&0x0000ffff)),15)), SHR(MULT16_16SU(SHR((b),16),((a)&0x0000ffff)),15))
      |                                  ^~~~~
F:/circuit/firmware/a04/third_party/opus-1.6.1/celt/fixed_generic.h:132:22: note: in expansion of macro 'SHL32'
  132 | #define SHL(a,shift) SHL32(a,shift)
      |                      ^~~~~
F:/circuit/firmware/a04/third_party/opus-1.6.1/celt/fixed_generic.h:71:40: note: in expansion of macro 'SHL'
   71 | #define MULT32_32_Q31(a,b) ADD32(ADD32(SHL(MULT16_16(SHR((a),16),SHR((b),16)),1), SHR(MULT16_16SU(SHR((a),16),((b)&0x0000ffff)),15)), SHR(MULT16_16SU(SHR((b),16),((a)&0x0000ffff)),15))
      |                                        ^~~
F:/circuit/firmware/a04/third_party/opus-1.6.1/celt/fixed_generic.h:71:44: note: in expansion of macro 'MULT16_16'
   71 | #define MULT32_32_Q31(a,b) ADD32(ADD32(SHL(MULT16_16(SHR((a),16),SHR((b),16)),1), SHR(MULT16_16SU(SHR((a),16),((b)&0x0000ffff)),15)), SHR(MULT16_16SU(SHR((b),16),((a)&0x0000ffff)),15))
      |                                            ^~~~~~~~~
F:/circuit/firmware/a04/third_party/opus-1.6.1/celt/fixed_generic.h:71:54: note: in expansion of macro 'SHR'
   71 | #define MULT32_32_Q31(a,b) ADD32(ADD32(SHL(MULT16_16(SHR((a),16),SHR((b),16)),1), SHR(MULT16_16SU(SHR((a),16),((b)&0x0000ffff)),15)), SHR(MULT16_16SU(SHR((b),16),((a)&0x0000ffff)),15))
      |                                                      ^~~
F:/circuit/firmware/a04/third_party/opus-1.6.1/celt/bands.c:631:17: note: in expansion of macro 'MULT32_32_Q31'
  631 |          tmp1 = MULT32_32_Q31(QCONST32(.70710678f,31), X[stride*2*j+i]);
      |                 ^~~~~~~~~~~~~
F:/circuit/firmware/a04/third_party/opus-1.6.1/celt/bands.c:631:31: note: in expansion of macro 'QCONST32'
  631 |          tmp1 = MULT32_32_Q31(QCONST32(.70710678f,31), X[stride*2*j+i]);
      |                               ^~~~~~~~
F:/circuit/firmware/a04/third_party/opus-1.6.1/celt/fixed_generic.h:95:42: warning: implicit conversion from 'float' to 'double' to match other operand of binary expression [-Wdouble-promotion]
   95 | #define QCONST32(x,bits) ((opus_val32)(.5+(x)*(((opus_int64)1)<<(bits))))
      |                                          ^
F:/circuit/firmware/a04/third_party/opus-1.6.1/celt/fixed_generic.h:152:34: note: in definition of macro 'ADD32'
  152 | #define ADD32(a,b) ((opus_val32)(a)+(opus_val32)(b))
      |                                  ^
F:/circuit/firmware/a04/third_party/opus-1.6.1/celt/fixed_generic.h:71:34: note: in expansion of macro 'ADD32'
   71 | #define MULT32_32_Q31(a,b) ADD32(ADD32(SHL(MULT16_16(SHR((a),16),SHR((b),16)),1), SHR(MULT16_16SU(SHR((a),16),((b)&0x0000ffff)),15)), SHR(MULT16_16SU(SHR((b),16),((a)&0x0000ffff)),15))
      |                                  ^~~~~
F:/circuit/firmware/a04/third_party/opus-1.6.1/celt/fixed_generic.h:71:83: note: in expansion of macro 'SHR'
   71 | #define MULT32_32_Q31(a,b) ADD32(ADD32(SHL(MULT16_16(SHR((a),16),SHR((b),16)),1), SHR(MULT16_16SU(SHR((a),16),((b)&0x0000ffff)),15)), SHR(MULT16_16SU(SHR((b),16),((a)&0x0000ffff)),15))
      |                                                                                   ^~~
F:/circuit/firmware/a04/third_party/opus-1.6.1/celt/fixed_generic.h:71:87: note: in expansion of macro 'MULT16_16SU'
   71 | #define MULT32_32_Q31(a,b) ADD32(ADD32(SHL(MULT16_16(SHR((a),16),SHR((b),16)),1), SHR(MULT16_16SU(SHR((a),16),((b)&0x0000ffff)),15)), SHR(MULT16_16SU(SHR((b),16),((a)&0x0000ffff)),15))
      |                                                                                       ^~~~~~~~~~~
F:/circuit/firmware/a04/third_party/opus-1.6.1/celt/fixed_generic.h:71:99: note: in expansion of macro 'SHR'
   71 | #define MULT32_32_Q31(a,b) ADD32(ADD32(SHL(MULT16_16(SHR((a),16),SHR((b),16)),1), SHR(MULT16_16SU(SHR((a),16),((b)&0x0000ffff)),15)), SHR(MULT16_16SU(SHR((b),16),((a)&0x0000ffff)),15))
      |                                                                                                   ^~~
F:/circuit/firmware/a04/third_party/opus-1.6.1/celt/bands.c:631:17: note: in expansion of macro 'MULT32_32_Q31'
  631 |          tmp1 = MULT32_32_Q31(QCONST32(.70710678f,31), X[stride*2*j+i]);
      |                 ^~~~~~~~~~~~~
F:/circuit/firmware/a04/third_party/opus-1.6.1/celt/bands.c:631:31: note: in expansion of macro 'QCONST32'
  631 |          tmp1 = MULT32_32_Q31(QCONST32(.70710678f,31), X[stride*2*j+i]);
      |                               ^~~~~~~~
F:/circuit/firmware/a04/third_party/opus-1.6.1/celt/fixed_generic.h:95:42: warning: implicit conversion from 'float' to 'double' to match other operand of binary expression [-Wdouble-promotion]
   95 | #define QCONST32(x,bits) ((opus_val32)(.5+(x)*(((opus_int64)1)<<(bits))))
      |                                          ^
F:/circuit/firmware/a04/third_party/opus-1.6.1/celt/fixed_generic.h:152:50: note: in definition of macro 'ADD32'
  152 | #define ADD32(a,b) ((opus_val32)(a)+(opus_val32)(b))
      |                                                  ^
F:/circuit/firmware/a04/third_party/opus-1.6.1/celt/fixed_generic.h:71:135: note: in expansion of macro 'SHR'
   71 | #define MULT32_32_Q31(a,b) ADD32(ADD32(SHL(MULT16_16(SHR((a),16),SHR((b),16)),1), SHR(MULT16_16SU(SHR((a),16),((b)&0x0000ffff)),15)), SHR(MULT16_16SU(SHR((b),16),((a)&0x0000ffff)),15))
      |                                                                                                                                       ^~~
F:/circuit/firmware/a04/third_party/opus-1.6.1/celt/fixed_generic.h:71:139: note: in expansion of macro 'MULT16_16SU'
   71 | #define MULT32_32_Q31(a,b) ADD32(ADD32(SHL(MULT16_16(SHR((a),16),SHR((b),16)),1), SHR(MULT16_16SU(SHR((a),16),((b)&0x0000ffff)),15)), SHR(MULT16_16SU(SHR((b),16),((a)&0x0000ffff)),15))
      |                                                                                                                                           ^~~~~~~~~~~
F:/circuit/firmware/a04/third_party/opus-1.6.1/celt/bands.c:631:17: note: in expansion of macro 'MULT32_32_Q31'
  631 |          tmp1 = MULT32_32_Q31(QCONST32(.70710678f,31), X[stride*2*j+i]);
      |                 ^~~~~~~~~~~~~
F:/circuit/firmware/a04/third_party/opus-1.6.1/celt/bands.c:631:31: note: in expansion of macro 'QCONST32'
  631 |          tmp1 = MULT32_32_Q31(QCONST32(.70710678f,31), X[stride*2*j+i]);
      |                               ^~~~~~~~
F:/circuit/firmware/a04/third_party/opus-1.6.1/celt/fixed_generic.h:95:42: warning: implicit conversion from 'float' to 'double' to match other operand of binary expression [-Wdouble-promotion]
   95 | #define QCONST32(x,bits) ((opus_val32)(.5+(x)*(((opus_int64)1)<<(bits))))
      |                                          ^
F:/circuit/firmware/a04/third_party/opus-1.6.1/celt/fixed_generic.h:152:34: note: in definition of macro 'ADD32'
  152 | #define ADD32(a,b) ((opus_val32)(a)+(opus_val32)(b))
      |                                  ^
F:/circuit/firmware/a04/third_party/opus-1.6.1/celt/fixed_generic.h:71:34: note: in expansion of macro 'ADD32'
   71 | #define MULT32_32_Q31(a,b) ADD32(ADD32(SHL(MULT16_16(SHR((a),16),SHR((b),16)),1), SHR(MULT16_16SU(SHR((a),16),((b)&0x0000ffff)),15)), SHR(MULT16_16SU(SHR((b),16),((a)&0x0000ffff)),15))
      |                                  ^~~~~
F:/circuit/firmware/a04/third_party/opus-1.6.1/celt/fixed_generic.h:132:22: note: in expansion of macro 'SHL32'
  132 | #define SHL(a,shift) SHL32(a,shift)
      |                      ^~~~~
F:/circuit/firmware/a04/third_party/opus-1.6.1/celt/fixed_generic.h:71:40: note: in expansion of macro 'SHL'
   71 | #define MULT32_32_Q31(a,b) ADD32(ADD32(SHL(MULT16_16(SHR((a),16),SHR((b),16)),1), SHR(MULT16_16SU(SHR((a),16),((b)&0x0000ffff)),15)), SHR(MULT16_16SU(SHR((b),16),((a)&0x0000ffff)),15))
      |                                        ^~~
F:/circuit/firmware/a04/third_party/opus-1.6.1/celt/fixed_generic.h:71:44: note: in expansion of macro 'MULT16_16'
   71 | #define MULT32_32_Q31(a,b) ADD32(ADD32(SHL(MULT16_16(SHR((a),16),SHR((b),16)),1), SHR(MULT16_16SU(SHR((a),16),((b)&0x0000ffff)),15)), SHR(MULT16_16SU(SHR((b),16),((a)&0x0000ffff)),15))
      |                                            ^~~~~~~~~
F:/circuit/firmware/a04/third_party/opus-1.6.1/celt/fixed_generic.h:71:54: note: in expansion of macro 'SHR'
   71 | #define MULT32_32_Q31(a,b) ADD32(ADD32(SHL(MULT16_16(SHR((a),16),SHR((b),16)),1), SHR(MULT16_16SU(SHR((a),16),((b)&0x0000ffff)),15)), SHR(MULT16_16SU(SHR((b),16),((a)&0x0000ffff)),15))
      |                                                      ^~~
F:/circuit/firmware/a04/third_party/opus-1.6.1/celt/bands.c:632:17: note: in expansion of macro 'MULT32_32_Q31'
  632 |          tmp2 = MULT32_32_Q31(QCONST32(.70710678f,31), X[stride*(2*j+1)+i]);
      |                 ^~~~~~~~~~~~~
F:/circuit/firmware/a04/third_party/opus-1.6.1/celt/bands.c:632:31: note: in expansion of macro 'QCONST32'
  632 |          tmp2 = MULT32_32_Q31(QCONST32(.70710678f,31), X[stride*(2*j+1)+i]);
      |                               ^~~~~~~~
F:/circuit/firmware/a04/third_party/opus-1.6.1/celt/fixed_generic.h:95:42: warning: implicit conversion from 'float' to 'double' to match other operand of binary expression [-Wdouble-promotion]
   95 | #define QCONST32(x,bits) ((opus_val32)(.5+(x)*(((opus_int64)1)<<(bits))))
      |                                          ^
F:/circuit/firmware/a04/third_party/opus-1.6.1/celt/fixed_generic.h:152:34: note: in definition of macro 'ADD32'
  152 | #define ADD32(a,b) ((opus_val32)(a)+(opus_val32)(b))
      |                                  ^
F:/circuit/firmware/a04/third_party/opus-1.6.1/celt/fixed_generic.h:71:34: note: in expansion of macro 'ADD32'
   71 | #define MULT32_32_Q31(a,b) ADD32(ADD32(SHL(MULT16_16(SHR((a),16),SHR((b),16)),1), SHR(MULT16_16SU(SHR((a),16),((b)&0x0000ffff)),15)), SHR(MULT16_16SU(SHR((b),16),((a)&0x0000ffff)),15))
      |                                  ^~~~~
F:/circuit/firmware/a04/third_party/opus-1.6.1/celt/fixed_generic.h:71:83: note: in expansion of macro 'SHR'
   71 | #define MULT32_32_Q31(a,b) ADD32(ADD32(SHL(MULT16_16(SHR((a),16),SHR((b),16)),1), SHR(MULT16_16SU(SHR((a),16),((b)&0x0000ffff)),15)), SHR(MULT16_16SU(SHR((b),16),((a)&0x0000ffff)),15))
      |                                                                                   ^~~
F:/circuit/firmware/a04/third_party/opus-1.6.1/celt/fixed_generic.h:71:87: note: in expansion of macro 'MULT16_16SU'
   71 | #define MULT32_32_Q31(a,b) ADD32(ADD32(SHL(MULT16_16(SHR((a),16),SHR((b),16)),1), SHR(MULT16_16SU(SHR((a),16),((b)&0x0000ffff)),15)), SHR(MULT16_16SU(SHR((b),16),((a)&0x0000ffff)),15))
      |                                                                                       ^~~~~~~~~~~
F:/circuit/firmware/a04/third_party/opus-1.6.1/celt/fixed_generic.h:71:99: note: in expansion of macro 'SHR'
   71 | #define MULT32_32_Q31(a,b) ADD32(ADD32(SHL(MULT16_16(SHR((a),16),SHR((b),16)),1), SHR(MULT16_16SU(SHR((a),16),((b)&0x0000ffff)),15)), SHR(MULT16_16SU(SHR((b),16),((a)&0x0000ffff)),15))
      |                                                                                                   ^~~
F:/circuit/firmware/a04/third_party/opus-1.6.1/celt/bands.c:632:17: note: in expansion of macro 'MULT32_32_Q31'
  632 |          tmp2 = MULT32_32_Q31(QCONST32(.70710678f,31), X[stride*(2*j+1)+i]);
      |                 ^~~~~~~~~~~~~
F:/circuit/firmware/a04/third_party/opus-1.6.1/celt/bands.c:632:31: note: in expansion of macro 'QCONST32'
  632 |          tmp2 = MULT32_32_Q31(QCONST32(.70710678f,31), X[stride*(2*j+1)+i]);
      |                               ^~~~~~~~
F:/circuit/firmware/a04/third_party/opus-1.6.1/celt/fixed_generic.h:95:42: warning: implicit conversion from 'float' to 'double' to match other operand of binary expression [-Wdouble-promotion]
   95 | #define QCONST32(x,bits) ((opus_val32)(.5+(x)*(((opus_int64)1)<<(bits))))
      |                                          ^
F:/circuit/firmware/a04/third_party/opus-1.6.1/celt/fixed_generic.h:152:50: note: in definition of macro 'ADD32'
  152 | #define ADD32(a,b) ((opus_val32)(a)+(opus_val32)(b))
      |                                                  ^
F:/circuit/firmware/a04/third_party/opus-1.6.1/celt/fixed_generic.h:71:135: note: in expansion of macro 'SHR'
   71 | #define MULT32_32_Q31(a,b) ADD32(ADD32(SHL(MULT16_16(SHR((a),16),SHR((b),16)),1), SHR(MULT16_16SU(SHR((a),16),((b)&0x0000ffff)),15)), SHR(MULT16_16SU(SHR((b),16),((a)&0x0000ffff)),15))
      |                                                                                                                                       ^~~
F:/circuit/firmware/a04/third_party/opus-1.6.1/celt/fixed_generic.h:71:139: note: in expansion of macro 'MULT16_16SU'
   71 | #define MULT32_32_Q31(a,b) ADD32(ADD32(SHL(MULT16_16(SHR((a),16),SHR((b),16)),1), SHR(MULT16_16SU(SHR((a),16),((b)&0x0000ffff)),15)), SHR(MULT16_16SU(SHR((b),16),((a)&0x0000ffff)),15))
      |                                                                                                                                           ^~~~~~~~~~~
F:/circuit/firmware/a04/third_party/opus-1.6.1/celt/bands.c:632:17: note: in expansion of macro 'MULT32_32_Q31'
  632 |          tmp2 = MULT32_32_Q31(QCONST32(.70710678f,31), X[stride*(2*j+1)+i]);
      |                 ^~~~~~~~~~~~~
F:/circuit/firmware/a04/third_party/opus-1.6.1/celt/bands.c:632:31: note: in expansion of macro 'QCONST32'
  632 |          tmp2 = MULT32_32_Q31(QCONST32(.70710678f,31), X[stride*(2*j+1)+i]);
      |                               ^~~~~~~~
F:/circuit/firmware/a04/third_party/opus-1.6.1/celt/bands.c: In function 'quant_partition':
F:/circuit/firmware/a04/third_party/opus-1.6.1/celt/fixed_generic.h:92:42: warning: implicit conversion from 'float' to 'double' to match other operand of binary expression [-Wdouble-promotion]
   92 | #define QCONST16(x,bits) ((opus_val16)(.5+(x)*(((opus_val32)1)<<(bits))))
      |                                          ^
F:/circuit/firmware/a04/third_party/opus-1.6.1/celt/bands.c:1164:28: note: in expansion of macro 'QCONST16'
 1164 |                      tmp = QCONST16(1.0f/256, NORM_SHIFT-4);
      |                            ^~~~~~~~
[457/503] Building C object opus/CMakeFiles/opus.dir/celt/celt_decoder.c.obj
In file included from F:/circuit/firmware/a04/third_party/opus-1.6.1/celt/celt_decoder.c:49:
F:/circuit/firmware/a04/third_party/opus-1.6.1/celt/float_cast.h:142:10: warning: #warning "Don't have the functions lrint() and lrintf ()." [-Wcpp]
  142 |         #warning "Don't have the functions lrint() and lrintf ()."
      |          ^~~~~~~
F:/circuit/firmware/a04/third_party/opus-1.6.1/celt/float_cast.h:143:10: warning: #warning "Replacing these functions with a standard C cast." [-Wcpp]
  143 |         #warning "Replacing these functions with a standard C cast."
      |          ^~~~~~~
In file included from F:/circuit/firmware/a04/third_party/opus-1.6.1/celt/arch.h:238,
                 from F:/circuit/firmware/a04/third_party/opus-1.6.1/celt/kiss_fft.h:34,
                 from F:/circuit/firmware/a04/third_party/opus-1.6.1/celt/mdct.h:46,
                 from F:/circuit/firmware/a04/third_party/opus-1.6.1/celt/celt_decoder.c:38:
F:/circuit/firmware/a04/third_party/opus-1.6.1/celt/celt_decoder.c: In function 'celt_decode_lost':
F:/circuit/firmware/a04/third_party/opus-1.6.1/celt/fixed_generic.h:98:40: warning: implicit conversion from 'float' to 'double' to match other operand of binary expression [-Wdouble-promotion]
   98 | #define GCONST2(x,bits) ((celt_glog)(.5+(x)*(((celt_glog)1)<<(bits))))
      |                                        ^
F:/circuit/firmware/a04/third_party/opus-1.6.1/celt/fixed_generic.h:101:19: note: in expansion of macro 'GCONST2'
  101 | #define GCONST(x) GCONST2((x),DB_SHIFT)
      |                   ^~~~~~~
F:/circuit/firmware/a04/third_party/opus-1.6.1/celt/celt_decoder.c:760:34: note: in expansion of macro 'GCONST'
  760 |       decay = loss_duration==0 ? GCONST(1.5f) : GCONST(.5f);
      |                                  ^~~~~~
F:/circuit/firmware/a04/third_party/opus-1.6.1/celt/fixed_generic.h:98:40: warning: implicit conversion from 'float' to 'double' to match other operand of binary expression [-Wdouble-promotion]
   98 | #define GCONST2(x,bits) ((celt_glog)(.5+(x)*(((celt_glog)1)<<(bits))))
      |                                        ^
F:/circuit/firmware/a04/third_party/opus-1.6.1/celt/fixed_generic.h:101:19: note: in expansion of macro 'GCONST2'
  101 | #define GCONST(x) GCONST2((x),DB_SHIFT)
      |                   ^~~~~~~
F:/circuit/firmware/a04/third_party/opus-1.6.1/celt/celt_decoder.c:760:49: note: in expansion of macro 'GCONST'
  760 |       decay = loss_duration==0 ? GCONST(1.5f) : GCONST(.5f);
      |                                                 ^~~~~~
F:/circuit/firmware/a04/third_party/opus-1.6.1/celt/fixed_generic.h:92:42: warning: implicit conversion from 'float' to 'double' to match other operand of binary expression [-Wdouble-promotion]
   92 | #define QCONST16(x,bits) ((opus_val16)(.5+(x)*(((opus_val32)1)<<(bits))))
      |                                          ^
F:/circuit/firmware/a04/third_party/opus-1.6.1/celt/celt_decoder.c:827:17: note: in expansion of macro 'QCONST16'
  827 |          fade = QCONST16(.8f,15);
      |                 ^~~~~~~~
F:/circuit/firmware/a04/third_party/opus-1.6.1/celt/fixed_generic.h:92:42: warning: implicit conversion from 'float' to 'double' to match other operand of binary expression [-Wdouble-promotion]
   92 | #define QCONST16(x,bits) ((opus_val16)(.5+(x)*(((opus_val32)1)<<(bits))))
      |                                          ^
F:/circuit/firmware/a04/third_party/opus-1.6.1/celt/fixed_generic.h:131:24: note: in definition of macro 'SHR'
  131 | #define SHR(a,shift) ((a) >> (shift))
      |                        ^
F:/circuit/firmware/a04/third_party/opus-1.6.1/celt/fixed_generic.h:193:33: note: in expansion of macro 'MULT16_16'
  193 | #define MULT16_16_Q15(a,b) (SHR(MULT16_16((a),(b)),15))
      |                                 ^~~~~~~~~
F:/circuit/firmware/a04/third_party/opus-1.6.1/celt/celt_decoder.c:890:22: note: in expansion of macro 'MULT16_16_Q15'
  890 |                tmp = MULT16_16_Q15(QCONST16(.99f,15), tmp);
      |                      ^~~~~~~~~~~~~
F:/circuit/firmware/a04/third_party/opus-1.6.1/celt/celt_decoder.c:890:36: note: in expansion of macro 'QCONST16'
  890 |                tmp = MULT16_16_Q15(QCONST16(.99f,15), tmp);
      |                                    ^~~~~~~~
F:/circuit/firmware/a04/third_party/opus-1.6.1/celt/celt_decoder.c: In function 'celt_decode_with_ec_dred':
F:/circuit/firmware/a04/third_party/opus-1.6.1/celt/fixed_generic.h:92:42: warning: implicit conversion from 'float' to 'double' to match other operand of binary expression [-Wdouble-promotion]
   92 | #define QCONST16(x,bits) ((opus_val16)(.5+(x)*(((opus_val32)1)<<(bits))))
      |                                          ^
F:/circuit/firmware/a04/third_party/opus-1.6.1/celt/celt_decoder.c:1340:28: note: in expansion of macro 'QCONST16'
 1340 |          postfilter_gain = QCONST16(.09375f,15)*(qg+1);
      |                            ^~~~~~~~
F:/circuit/firmware/a04/third_party/opus-1.6.1/celt/fixed_generic.h:98:40: warning: implicit conversion from 'float' to 'double' to match other operand of binary expression [-Wdouble-promotion]
   98 | #define GCONST2(x,bits) ((celt_glog)(.5+(x)*(((celt_glog)1)<<(bits))))
      |                                        ^
F:/circuit/firmware/a04/third_party/opus-1.6.1/celt/fixed_generic.h:101:19: note: in expansion of macro 'GCONST2'
  101 | #define GCONST(x) GCONST2((x),DB_SHIFT)
      |                   ^~~~~~~
F:/circuit/firmware/a04/third_party/opus-1.6.1/celt/celt_decoder.c:1367:30: note: in expansion of macro 'GCONST'
 1367 |          if (LM==0) safety = GCONST(1.5f);
      |                              ^~~~~~
F:/circuit/firmware/a04/third_party/opus-1.6.1/celt/fixed_generic.h:98:40: warning: implicit conversion from 'float' to 'double' to match other operand of binary expression [-Wdouble-promotion]
   98 | #define GCONST2(x,bits) ((celt_glog)(.5+(x)*(((celt_glog)1)<<(bits))))
      |                                        ^
F:/circuit/firmware/a04/third_party/opus-1.6.1/celt/fixed_generic.h:101:19: note: in expansion of macro 'GCONST2'
  101 | #define GCONST(x) GCONST2((x),DB_SHIFT)
      |                   ^~~~~~~
F:/circuit/firmware/a04/third_party/opus-1.6.1/celt/celt_decoder.c:1368:35: note: in expansion of macro 'GCONST'
 1368 |          else if (LM==1) safety = GCONST(.5f);
      |                                   ^~~~~~
F:/circuit/firmware/a04/third_party/opus-1.6.1/celt/fixed_generic.h:98:40: warning: implicit conversion from 'float' to 'double' to match other operand of binary expression [-Wdouble-promotion]
   98 | #define GCONST2(x,bits) ((celt_glog)(.5+(x)*(((celt_glog)1)<<(bits))))
      |                                        ^
F:/circuit/firmware/a04/third_party/opus-1.6.1/celt/arch.h:102:28: note: in definition of macro 'MIN32'
  102 | #define MIN32(a,b) ((a) < (b) ? (a) : (b))   /**< Minimum 32-bit value.   */
      |                            ^
F:/circuit/firmware/a04/third_party/opus-1.6.1/celt/celt_decoder.c:1379:24: note: in expansion of macro 'MING'
 1379 |                slope = MING(slope, GCONST(2.f));
      |                        ^~~~
F:/circuit/firmware/a04/third_party/opus-1.6.1/celt/fixed_generic.h:101:19: note: in expansion of macro 'GCONST2'
  101 | #define GCONST(x) GCONST2((x),DB_SHIFT)
      |                   ^~~~~~~
F:/circuit/firmware/a04/third_party/opus-1.6.1/celt/celt_decoder.c:1379:36: note: in expansion of macro 'GCONST'
 1379 |                slope = MING(slope, GCONST(2.f));
      |                                    ^~~~~~
F:/circuit/firmware/a04/third_party/opus-1.6.1/celt/fixed_generic.h:98:40: warning: implicit conversion from 'float' to 'double' to match other operand of binary expression [-Wdouble-promotion]
   98 | #define GCONST2(x,bits) ((celt_glog)(.5+(x)*(((celt_glog)1)<<(bits))))
      |                                        ^
F:/circuit/firmware/a04/third_party/opus-1.6.1/celt/arch.h:102:40: note: in definition of macro 'MIN32'
  102 | #define MIN32(a,b) ((a) < (b) ? (a) : (b))   /**< Minimum 32-bit value.   */
      |                                        ^
F:/circuit/firmware/a04/third_party/opus-1.6.1/celt/celt_decoder.c:1379:24: note: in expansion of macro 'MING'
 1379 |                slope = MING(slope, GCONST(2.f));
      |                        ^~~~
F:/circuit/firmware/a04/third_party/opus-1.6.1/celt/fixed_generic.h:101:19: note: in expansion of macro 'GCONST2'
  101 | #define GCONST(x) GCONST2((x),DB_SHIFT)
      |                   ^~~~~~~
F:/circuit/firmware/a04/third_party/opus-1.6.1/celt/celt_decoder.c:1379:36: note: in expansion of macro 'GCONST'
 1379 |                slope = MING(slope, GCONST(2.f));
      |                                    ^~~~~~
F:/circuit/firmware/a04/third_party/opus-1.6.1/celt/fixed_generic.h:98:40: warning: implicit conversion from 'float' to 'double' to match other operand of binary expression [-Wdouble-promotion]
   98 | #define GCONST2(x,bits) ((celt_glog)(.5+(x)*(((celt_glog)1)<<(bits))))
      |                                        ^
F:/circuit/firmware/a04/third_party/opus-1.6.1/celt/arch.h:103:22: note: in definition of macro 'MAX32'
  103 | #define MAX32(a,b) ((a) > (b) ? (a) : (b))   /**< Maximum 32-bit value.   */
      |                      ^
F:/circuit/firmware/a04/third_party/opus-1.6.1/celt/fixed_generic.h:101:19: note: in expansion of macro 'GCONST2'
  101 | #define GCONST(x) GCONST2((x),DB_SHIFT)
      |                   ^~~~~~~
F:/circuit/firmware/a04/third_party/opus-1.6.1/celt/celt_decoder.c:1381:48: note: in expansion of macro 'GCONST'
 1381 |                oldBandE[c*nbEBands+i] = MAX32(-GCONST(20.f), E0);
      |                                                ^~~~~~
F:/circuit/firmware/a04/third_party/opus-1.6.1/celt/fixed_generic.h:98:40: warning: implicit conversion from 'float' to 'double' to match other operand of binary expression [-Wdouble-promotion]
   98 | #define GCONST2(x,bits) ((celt_glog)(.5+(x)*(((celt_glog)1)<<(bits))))
      |                                        ^
F:/circuit/firmware/a04/third_party/opus-1.6.1/celt/arch.h:103:34: note: in definition of macro 'MAX32'
  103 | #define MAX32(a,b) ((a) > (b) ? (a) : (b))   /**< Maximum 32-bit value.   */
      |                                  ^
F:/circuit/firmware/a04/third_party/opus-1.6.1/celt/fixed_generic.h:101:19: note: in expansion of macro 'GCONST2'
  101 | #define GCONST(x) GCONST2((x),DB_SHIFT)
      |                   ^~~~~~~
F:/circuit/firmware/a04/third_party/opus-1.6.1/celt/celt_decoder.c:1381:48: note: in expansion of macro 'GCONST'
 1381 |                oldBandE[c*nbEBands+i] = MAX32(-GCONST(20.f), E0);
      |                                                ^~~~~~
F:/circuit/firmware/a04/third_party/opus-1.6.1/celt/fixed_generic.h:98:40: warning: implicit conversion from 'float' to 'double' to match other operand of binary expression [-Wdouble-promotion]
   98 | #define GCONST2(x,bits) ((celt_glog)(.5+(x)*(((celt_glog)1)<<(bits))))
      |                                        ^
F:/circuit/firmware/a04/third_party/opus-1.6.1/celt/fixed_generic.h:101:19: note: in expansion of macro 'GCONST2'
  101 | #define GCONST(x) GCONST2((x),DB_SHIFT)
      |                   ^~~~~~~
F:/circuit/firmware/a04/third_party/opus-1.6.1/celt/celt_decoder.c:1529:25: note: in expansion of macro 'GCONST'
 1529 |          oldBandE[i] = -GCONST(28.f);
      |                         ^~~~~~
F:/circuit/firmware/a04/third_party/opus-1.6.1/celt/fixed_generic.h:98:40: warning: implicit conversion from 'float' to 'double' to match other operand of binary expression [-Wdouble-promotion]
   98 | #define GCONST2(x,bits) ((celt_glog)(.5+(x)*(((celt_glog)1)<<(bits))))
      |                                        ^
F:/circuit/firmware/a04/third_party/opus-1.6.1/celt/fixed_generic.h:101:19: note: in expansion of macro 'GCONST2'
  101 | #define GCONST(x) GCONST2((x),DB_SHIFT)
      |                   ^~~~~~~
F:/circuit/firmware/a04/third_party/opus-1.6.1/celt/celt_decoder.c:1576:61: note: in expansion of macro 'GCONST'
 1576 |    max_background_increase = IMIN(160, st->loss_duration+M)*GCONST(0.001f);
      |                                                             ^~~~~~
F:/circuit/firmware/a04/third_party/opus-1.6.1/celt/fixed_generic.h:98:40: warning: implicit conversion from 'float' to 'double' to match other operand of binary expression [-Wdouble-promotion]
   98 | #define GCONST2(x,bits) ((celt_glog)(.5+(x)*(((celt_glog)1)<<(bits))))
      |                                        ^
F:/circuit/firmware/a04/third_party/opus-1.6.1/celt/fixed_generic.h:101:19: note: in expansion of macro 'GCONST2'
  101 | #define GCONST(x) GCONST2((x),DB_SHIFT)
      |                   ^~~~~~~
F:/circuit/firmware/a04/third_party/opus-1.6.1/celt/celt_decoder.c:1585:56: note: in expansion of macro 'GCONST'
 1585 |          oldLogE[c*nbEBands+i]=oldLogE2[c*nbEBands+i]=-GCONST(28.f);
      |                                                        ^~~~~~
F:/circuit/firmware/a04/third_party/opus-1.6.1/celt/fixed_generic.h:98:40: warning: implicit conversion from 'float' to 'double' to match other operand of binary expression [-Wdouble-promotion]
   98 | #define GCONST2(x,bits) ((celt_glog)(.5+(x)*(((celt_glog)1)<<(bits))))
      |                                        ^
F:/circuit/firmware/a04/third_party/opus-1.6.1/celt/fixed_generic.h:101:19: note: in expansion of macro 'GCONST2'
  101 | #define GCONST(x) GCONST2((x),DB_SHIFT)
      |                   ^~~~~~~
F:/circuit/firmware/a04/third_party/opus-1.6.1/celt/celt_decoder.c:1590:56: note: in expansion of macro 'GCONST'
 1590 |          oldLogE[c*nbEBands+i]=oldLogE2[c*nbEBands+i]=-GCONST(28.f);
      |                                                        ^~~~~~
F:/circuit/firmware/a04/third_party/opus-1.6.1/celt/celt_decoder.c: In function 'opus_custom_decoder_ctl':
F:/circuit/firmware/a04/third_party/opus-1.6.1/celt/fixed_generic.h:98:40: warning: implicit conversion from 'float' to 'double' to match other operand of binary expression [-Wdouble-promotion]
   98 | #define GCONST2(x,bits) ((celt_glog)(.5+(x)*(((celt_glog)1)<<(bits))))
      |                                        ^
F:/circuit/firmware/a04/third_party/opus-1.6.1/celt/fixed_generic.h:101:19: note: in expansion of macro 'GCONST2'
  101 | #define GCONST(x) GCONST2((x),DB_SHIFT)
      |                   ^~~~~~~
F:/circuit/firmware/a04/third_party/opus-1.6.1/celt/celt_decoder.c:1806:37: note: in expansion of macro 'GCONST'
 1806 |             oldLogE[i]=oldLogE2[i]=-GCONST(28.f);
      |                                     ^~~~~~
[458/503] Building C object opus/CMakeFiles/opus.dir/celt/cwrs.c.obj
[459/503] Building C object opus/CMakeFiles/opus.dir/celt/celt_encoder.c.obj
In file included from F:/circuit/firmware/a04/third_party/opus-1.6.1/celt/celt_encoder.c:49:
F:/circuit/firmware/a04/third_party/opus-1.6.1/celt/float_cast.h:142:10: warning: #warning "Don't have the functions lrint() and lrintf ()." [-Wcpp]
  142 |         #warning "Don't have the functions lrint() and lrintf ()."
      |          ^~~~~~~
F:/circuit/firmware/a04/third_party/opus-1.6.1/celt/float_cast.h:143:10: warning: #warning "Replacing these functions with a standard C cast." [-Wcpp]
  143 |         #warning "Replacing these functions with a standard C cast."
      |          ^~~~~~~
In file included from F:/circuit/firmware/a04/third_party/opus-1.6.1/celt/arch.h:238,
                 from F:/circuit/firmware/a04/third_party/opus-1.6.1/celt/kiss_fft.h:34,
                 from F:/circuit/firmware/a04/third_party/opus-1.6.1/celt/mdct.h:46,
                 from F:/circuit/firmware/a04/third_party/opus-1.6.1/celt/celt_encoder.c:38:
F:/circuit/firmware/a04/third_party/opus-1.6.1/celt/celt_encoder.c: In function 'transient_analysis':
F:/circuit/firmware/a04/third_party/opus-1.6.1/celt/fixed_generic.h:95:42: warning: implicit conversion from 'float' to 'double' to match other operand of binary expression [-Wdouble-promotion]
   95 | #define QCONST32(x,bits) ((opus_val32)(.5+(x)*(((opus_int64)1)<<(bits))))
      |                                          ^
F:/circuit/firmware/a04/third_party/opus-1.6.1/celt/celt_encoder.c:447:22: note: in expansion of macro 'QCONST32'
  447 |    if (toneishness > QCONST32(.98f, 29) && tone_freq < QCONST16(0.026f, 13))
      |                      ^~~~~~~~
F:/circuit/firmware/a04/third_party/opus-1.6.1/celt/fixed_generic.h:92:42: warning: implicit conversion from 'float' to 'double' to match other operand of binary expression [-Wdouble-promotion]
   92 | #define QCONST16(x,bits) ((opus_val16)(.5+(x)*(((opus_val32)1)<<(bits))))
      |                                          ^
F:/circuit/firmware/a04/third_party/opus-1.6.1/celt/celt_encoder.c:447:56: note: in expansion of macro 'QCONST16'
  447 |    if (toneishness > QCONST32(.98f, 29) && tone_freq < QCONST16(0.026f, 13))
      |                                                        ^~~~~~~~
F:/circuit/firmware/a04/third_party/opus-1.6.1/celt/celt_encoder.c: In function 'patch_transient_decision':
F:/circuit/firmware/a04/third_party/opus-1.6.1/celt/fixed_generic.h:98:40: warning: implicit conversion from 'float' to 'double' to match other operand of binary expression [-Wdouble-promotion]
   98 | #define GCONST2(x,bits) ((celt_glog)(.5+(x)*(((celt_glog)1)<<(bits))))
      |                                        ^
F:/circuit/firmware/a04/third_party/opus-1.6.1/celt/arch.h:103:22: note: in definition of macro 'MAX32'
  103 | #define MAX32(a,b) ((a) > (b) ? (a) : (b))   /**< Maximum 32-bit value.   */
      |                      ^
F:/circuit/firmware/a04/third_party/opus-1.6.1/celt/celt_encoder.c:485:26: note: in expansion of macro 'MAXG'
  485 |          spread_old[i] = MAXG(spread_old[i-1]-GCONST(1.0f), oldE[i]);
      |                          ^~~~
F:/circuit/firmware/a04/third_party/opus-1.6.1/celt/fixed_generic.h:101:19: note: in expansion of macro 'GCONST2'
  101 | #define GCONST(x) GCONST2((x),DB_SHIFT)
      |                   ^~~~~~~
F:/circuit/firmware/a04/third_party/opus-1.6.1/celt/celt_encoder.c:485:47: note: in expansion of macro 'GCONST'
  485 |          spread_old[i] = MAXG(spread_old[i-1]-GCONST(1.0f), oldE[i]);
      |                                               ^~~~~~
F:/circuit/firmware/a04/third_party/opus-1.6.1/celt/fixed_generic.h:98:40: warning: implicit conversion from 'float' to 'double' to match other operand of binary expression [-Wdouble-promotion]
   98 | #define GCONST2(x,bits) ((celt_glog)(.5+(x)*(((celt_glog)1)<<(bits))))
      |                                        ^
F:/circuit/firmware/a04/third_party/opus-1.6.1/celt/arch.h:103:34: note: in definition of macro 'MAX32'
  103 | #define MAX32(a,b) ((a) > (b) ? (a) : (b))   /**< Maximum 32-bit value.   */
      |                                  ^
F:/circuit/firmware/a04/third_party/opus-1.6.1/celt/celt_encoder.c:485:26: note: in expansion of macro 'MAXG'
  485 |          spread_old[i] = MAXG(spread_old[i-1]-GCONST(1.0f), oldE[i]);
      |                          ^~~~
F:/circuit/firmware/a04/third_party/opus-1.6.1/celt/fixed_generic.h:101:19: note: in expansion of macro 'GCONST2'
  101 | #define GCONST(x) GCONST2((x),DB_SHIFT)
      |                   ^~~~~~~
F:/circuit/firmware/a04/third_party/opus-1.6.1/celt/celt_encoder.c:485:47: note: in expansion of macro 'GCONST'
  485 |          spread_old[i] = MAXG(spread_old[i-1]-GCONST(1.0f), oldE[i]);
      |                                               ^~~~~~
F:/circuit/firmware/a04/third_party/opus-1.6.1/celt/fixed_generic.h:98:40: warning: implicit conversion from 'float' to 'double' to match other operand of binary expression [-Wdouble-promotion]
   98 | #define GCONST2(x,bits) ((celt_glog)(.5+(x)*(((celt_glog)1)<<(bits))))
      |                                        ^
F:/circuit/firmware/a04/third_party/opus-1.6.1/celt/arch.h:103:22: note: in definition of macro 'MAX32'
  103 | #define MAX32(a,b) ((a) > (b) ? (a) : (b))   /**< Maximum 32-bit value.   */
      |                      ^
F:/circuit/firmware/a04/third_party/opus-1.6.1/celt/celt_encoder.c:489:26: note: in expansion of macro 'MAXG'
  489 |          spread_old[i] = MAXG(spread_old[i-1]-GCONST(1.0f),
      |                          ^~~~
F:/circuit/firmware/a04/third_party/opus-1.6.1/celt/fixed_generic.h:101:19: note: in expansion of macro 'GCONST2'
  101 | #define GCONST(x) GCONST2((x),DB_SHIFT)
      |                   ^~~~~~~
F:/circuit/firmware/a04/third_party/opus-1.6.1/celt/celt_encoder.c:489:47: note: in expansion of macro 'GCONST'
  489 |          spread_old[i] = MAXG(spread_old[i-1]-GCONST(1.0f),
      |                                               ^~~~~~
F:/circuit/firmware/a04/third_party/opus-1.6.1/celt/fixed_generic.h:98:40: warning: implicit conversion from 'float' to 'double' to match other operand of binary expression [-Wdouble-promotion]
   98 | #define GCONST2(x,bits) ((celt_glog)(.5+(x)*(((celt_glog)1)<<(bits))))
      |                                        ^
F:/circuit/firmware/a04/third_party/opus-1.6.1/celt/arch.h:103:34: note: in definition of macro 'MAX32'
  103 | #define MAX32(a,b) ((a) > (b) ? (a) : (b))   /**< Maximum 32-bit value.   */
      |                                  ^
F:/circuit/firmware/a04/third_party/opus-1.6.1/celt/celt_encoder.c:489:26: note: in expansion of macro 'MAXG'
  489 |          spread_old[i] = MAXG(spread_old[i-1]-GCONST(1.0f),
      |                          ^~~~
F:/circuit/firmware/a04/third_party/opus-1.6.1/celt/fixed_generic.h:101:19: note: in expansion of macro 'GCONST2'
  101 | #define GCONST(x) GCONST2((x),DB_SHIFT)
      |                   ^~~~~~~
F:/circuit/firmware/a04/third_party/opus-1.6.1/celt/celt_encoder.c:489:47: note: in expansion of macro 'GCONST'
  489 |          spread_old[i] = MAXG(spread_old[i-1]-GCONST(1.0f),
      |                                               ^~~~~~
F:/circuit/firmware/a04/third_party/opus-1.6.1/celt/fixed_generic.h:98:40: warning: implicit conversion from 'float' to 'double' to match other operand of binary expression [-Wdouble-promotion]
   98 | #define GCONST2(x,bits) ((celt_glog)(.5+(x)*(((celt_glog)1)<<(bits))))
      |                                        ^
F:/circuit/firmware/a04/third_party/opus-1.6.1/celt/arch.h:103:28: note: in definition of macro 'MAX32'
  103 | #define MAX32(a,b) ((a) > (b) ? (a) : (b))   /**< Maximum 32-bit value.   */
      |                            ^
F:/circuit/firmware/a04/third_party/opus-1.6.1/celt/celt_encoder.c:493:23: note: in expansion of macro 'MAXG'
  493 |       spread_old[i] = MAXG(spread_old[i], spread_old[i+1]-GCONST(1.0f));
      |                       ^~~~
F:/circuit/firmware/a04/third_party/opus-1.6.1/celt/fixed_generic.h:101:19: note: in expansion of macro 'GCONST2'
  101 | #define GCONST(x) GCONST2((x),DB_SHIFT)
      |                   ^~~~~~~
F:/circuit/firmware/a04/third_party/opus-1.6.1/celt/celt_encoder.c:493:59: note: in expansion of macro 'GCONST'
  493 |       spread_old[i] = MAXG(spread_old[i], spread_old[i+1]-GCONST(1.0f));
      |                                                           ^~~~~~
F:/circuit/firmware/a04/third_party/opus-1.6.1/celt/fixed_generic.h:98:40: warning: implicit conversion from 'float' to 'double' to match other operand of binary expression [-Wdouble-promotion]
   98 | #define GCONST2(x,bits) ((celt_glog)(.5+(x)*(((celt_glog)1)<<(bits))))
      |                                        ^
F:/circuit/firmware/a04/third_party/opus-1.6.1/celt/arch.h:103:40: note: in definition of macro 'MAX32'
  103 | #define MAX32(a,b) ((a) > (b) ? (a) : (b))   /**< Maximum 32-bit value.   */
      |                                        ^
F:/circuit/firmware/a04/third_party/opus-1.6.1/celt/celt_encoder.c:493:23: note: in expansion of macro 'MAXG'
  493 |       spread_old[i] = MAXG(spread_old[i], spread_old[i+1]-GCONST(1.0f));
      |                       ^~~~
F:/circuit/firmware/a04/third_party/opus-1.6.1/celt/fixed_generic.h:101:19: note: in expansion of macro 'GCONST2'
  101 | #define GCONST(x) GCONST2((x),DB_SHIFT)
      |                   ^~~~~~~
F:/circuit/firmware/a04/third_party/opus-1.6.1/celt/celt_encoder.c:493:59: note: in expansion of macro 'GCONST'
  493 |       spread_old[i] = MAXG(spread_old[i], spread_old[i+1]-GCONST(1.0f));
      |                                                           ^~~~~~
F:/circuit/firmware/a04/third_party/opus-1.6.1/celt/fixed_generic.h:98:40: warning: implicit conversion from 'float' to 'double' to match other operand of binary expression [-Wdouble-promotion]
   98 | #define GCONST2(x,bits) ((celt_glog)(.5+(x)*(((celt_glog)1)<<(bits))))
      |                                        ^
F:/circuit/firmware/a04/third_party/opus-1.6.1/celt/fixed_generic.h:101:19: note: in expansion of macro 'GCONST2'
  101 | #define GCONST(x) GCONST2((x),DB_SHIFT)
      |                   ^~~~~~~
F:/circuit/firmware/a04/third_party/opus-1.6.1/celt/celt_encoder.c:506:23: note: in expansion of macro 'GCONST'
  506 |    return mean_diff > GCONST(1.f);
      |                       ^~~~~~
F:/circuit/firmware/a04/third_party/opus-1.6.1/celt/celt_encoder.c: In function 'tf_analysis':
F:/circuit/firmware/a04/third_party/opus-1.6.1/celt/fixed_generic.h:92:42: warning: implicit conversion from 'float' to 'double' to match other operand of binary expression [-Wdouble-promotion]
   92 | #define QCONST16(x,bits) ((opus_val16)(.5+(x)*(((opus_val32)1)<<(bits))))
      |                                          ^
F:/circuit/firmware/a04/third_party/opus-1.6.1/celt/fixed_generic.h:131:24: note: in definition of macro 'SHR'
  131 | #define SHR(a,shift) ((a) >> (shift))
      |                        ^
F:/circuit/firmware/a04/third_party/opus-1.6.1/celt/fixed_generic.h:192:33: note: in expansion of macro 'MULT16_16'
  192 | #define MULT16_16_Q14(a,b) (SHR(MULT16_16((a),(b)),14))
      |                                 ^~~~~~~~~
F:/circuit/firmware/a04/third_party/opus-1.6.1/celt/celt_encoder.c:681:11: note: in expansion of macro 'MULT16_16_Q14'
  681 |    bias = MULT16_16_Q14(QCONST16(.04f,15), MAX16(-QCONST16(.25f,14), QCONST16(.5f,14)-tf_estimate));
      |           ^~~~~~~~~~~~~
F:/circuit/firmware/a04/third_party/opus-1.6.1/celt/celt_encoder.c:681:25: note: in expansion of macro 'QCONST16'
  681 |    bias = MULT16_16_Q14(QCONST16(.04f,15), MAX16(-QCONST16(.25f,14), QCONST16(.5f,14)-tf_estimate));
      |                         ^~~~~~~~
F:/circuit/firmware/a04/third_party/opus-1.6.1/celt/fixed_generic.h:92:42: warning: implicit conversion from 'float' to 'double' to match other operand of binary expression [-Wdouble-promotion]
   92 | #define QCONST16(x,bits) ((opus_val16)(.5+(x)*(((opus_val32)1)<<(bits))))
      |                                          ^
F:/circuit/firmware/a04/third_party/opus-1.6.1/celt/fixed_generic.h:131:24: note: in definition of macro 'SHR'
  131 | #define SHR(a,shift) ((a) >> (shift))
      |                        ^
F:/circuit/firmware/a04/third_party/opus-1.6.1/celt/fixed_generic.h:192:33: note: in expansion of macro 'MULT16_16'
  192 | #define MULT16_16_Q14(a,b) (SHR(MULT16_16((a),(b)),14))
      |                                 ^~~~~~~~~
F:/circuit/firmware/a04/third_party/opus-1.6.1/celt/celt_encoder.c:681:11: note: in expansion of macro 'MULT16_16_Q14'
  681 |    bias = MULT16_16_Q14(QCONST16(.04f,15), MAX16(-QCONST16(.25f,14), QCONST16(.5f,14)-tf_estimate));
      |           ^~~~~~~~~~~~~
F:/circuit/firmware/a04/third_party/opus-1.6.1/celt/celt_encoder.c:681:44: note: in expansion of macro 'MAX16'
  681 |    bias = MULT16_16_Q14(QCONST16(.04f,15), MAX16(-QCONST16(.25f,14), QCONST16(.5f,14)-tf_estimate));
      |                                            ^~~~~
F:/circuit/firmware/a04/third_party/opus-1.6.1/celt/celt_encoder.c:681:51: note: in expansion of macro 'QCONST16'
  681 |    bias = MULT16_16_Q14(QCONST16(.04f,15), MAX16(-QCONST16(.25f,14), QCONST16(.5f,14)-tf_estimate));
      |                                                   ^~~~~~~~
F:/circuit/firmware/a04/third_party/opus-1.6.1/celt/fixed_generic.h:92:42: warning: implicit conversion from 'float' to 'double' to match other operand of binary expression [-Wdouble-promotion]
   92 | #define QCONST16(x,bits) ((opus_val16)(.5+(x)*(((opus_val32)1)<<(bits))))
      |                                          ^
F:/circuit/firmware/a04/third_party/opus-1.6.1/celt/fixed_generic.h:131:24: note: in definition of macro 'SHR'
  131 | #define SHR(a,shift) ((a) >> (shift))
      |                        ^
F:/circuit/firmware/a04/third_party/opus-1.6.1/celt/fixed_generic.h:192:33: note: in expansion of macro 'MULT16_16'
  192 | #define MULT16_16_Q14(a,b) (SHR(MULT16_16((a),(b)),14))
      |                                 ^~~~~~~~~
F:/circuit/firmware/a04/third_party/opus-1.6.1/celt/celt_encoder.c:681:11: note: in expansion of macro 'MULT16_16_Q14'
  681 |    bias = MULT16_16_Q14(QCONST16(.04f,15), MAX16(-QCONST16(.25f,14), QCONST16(.5f,14)-tf_estimate));
      |           ^~~~~~~~~~~~~
F:/circuit/firmware/a04/third_party/opus-1.6.1/celt/celt_encoder.c:681:44: note: in expansion of macro 'MAX16'
  681 |    bias = MULT16_16_Q14(QCONST16(.04f,15), MAX16(-QCONST16(.25f,14), QCONST16(.5f,14)-tf_estimate));
      |                                            ^~~~~
F:/circuit/firmware/a04/third_party/opus-1.6.1/celt/celt_encoder.c:681:70: note: in expansion of macro 'QCONST16'
  681 |    bias = MULT16_16_Q14(QCONST16(.04f,15), MAX16(-QCONST16(.25f,14), QCONST16(.5f,14)-tf_estimate));
      |                                                                      ^~~~~~~~
F:/circuit/firmware/a04/third_party/opus-1.6.1/celt/fixed_generic.h:92:42: warning: implicit conversion from 'float' to 'double' to match other operand of binary expression [-Wdouble-promotion]
   92 | #define QCONST16(x,bits) ((opus_val16)(.5+(x)*(((opus_val32)1)<<(bits))))
      |                                          ^
F:/circuit/firmware/a04/third_party/opus-1.6.1/celt/fixed_generic.h:131:24: note: in definition of macro 'SHR'
  131 | #define SHR(a,shift) ((a) >> (shift))
      |                        ^
F:/circuit/firmware/a04/third_party/opus-1.6.1/celt/fixed_generic.h:192:33: note: in expansion of macro 'MULT16_16'
  192 | #define MULT16_16_Q14(a,b) (SHR(MULT16_16((a),(b)),14))
      |                                 ^~~~~~~~~
F:/circuit/firmware/a04/third_party/opus-1.6.1/celt/celt_encoder.c:681:11: note: in expansion of macro 'MULT16_16_Q14'
  681 |    bias = MULT16_16_Q14(QCONST16(.04f,15), MAX16(-QCONST16(.25f,14), QCONST16(.5f,14)-tf_estimate));
      |           ^~~~~~~~~~~~~
F:/circuit/firmware/a04/third_party/opus-1.6.1/celt/celt_encoder.c:681:44: note: in expansion of macro 'MAX16'
  681 |    bias = MULT16_16_Q14(QCONST16(.04f,15), MAX16(-QCONST16(.25f,14), QCONST16(.5f,14)-tf_estimate));
      |                                            ^~~~~
F:/circuit/firmware/a04/third_party/opus-1.6.1/celt/celt_encoder.c:681:51: note: in expansion of macro 'QCONST16'
  681 |    bias = MULT16_16_Q14(QCONST16(.04f,15), MAX16(-QCONST16(.25f,14), QCONST16(.5f,14)-tf_estimate));
      |                                                   ^~~~~~~~
F:/circuit/firmware/a04/third_party/opus-1.6.1/celt/fixed_generic.h:92:42: warning: implicit conversion from 'float' to 'double' to match other operand of binary expression [-Wdouble-promotion]
   92 | #define QCONST16(x,bits) ((opus_val16)(.5+(x)*(((opus_val32)1)<<(bits))))
      |                                          ^
F:/circuit/firmware/a04/third_party/opus-1.6.1/celt/fixed_generic.h:131:24: note: in definition of macro 'SHR'
  131 | #define SHR(a,shift) ((a) >> (shift))
      |                        ^
F:/circuit/firmware/a04/third_party/opus-1.6.1/celt/fixed_generic.h:192:33: note: in expansion of macro 'MULT16_16'
  192 | #define MULT16_16_Q14(a,b) (SHR(MULT16_16((a),(b)),14))
      |                                 ^~~~~~~~~
F:/circuit/firmware/a04/third_party/opus-1.6.1/celt/celt_encoder.c:681:11: note: in expansion of macro 'MULT16_16_Q14'
  681 |    bias = MULT16_16_Q14(QCONST16(.04f,15), MAX16(-QCONST16(.25f,14), QCONST16(.5f,14)-tf_estimate));
      |           ^~~~~~~~~~~~~
F:/circuit/firmware/a04/third_party/opus-1.6.1/celt/celt_encoder.c:681:44: note: in expansion of macro 'MAX16'
  681 |    bias = MULT16_16_Q14(QCONST16(.04f,15), MAX16(-QCONST16(.25f,14), QCONST16(.5f,14)-tf_estimate));
      |                                            ^~~~~
F:/circuit/firmware/a04/third_party/opus-1.6.1/celt/celt_encoder.c:681:70: note: in expansion of macro 'QCONST16'
  681 |    bias = MULT16_16_Q14(QCONST16(.04f,15), MAX16(-QCONST16(.25f,14), QCONST16(.5f,14)-tf_estimate));
      |                                                                      ^~~~~~~~
F:/circuit/firmware/a04/third_party/opus-1.6.1/celt/celt_encoder.c: In function 'alloc_trim_analysis':
F:/circuit/firmware/a04/third_party/opus-1.6.1/celt/fixed_generic.h:92:42: warning: implicit conversion from 'float' to 'double' to match other operand of binary expression [-Wdouble-promotion]
   92 | #define QCONST16(x,bits) ((opus_val16)(.5+(x)*(((opus_val32)1)<<(bits))))
      |                                          ^
F:/circuit/firmware/a04/third_party/opus-1.6.1/celt/celt_encoder.c:874:22: note: in expansion of macro 'QCONST16'
  874 |    opus_val16 trim = QCONST16(5.f, 8);
      |                      ^~~~~~~~
F:/circuit/firmware/a04/third_party/opus-1.6.1/celt/fixed_generic.h:92:42: warning: implicit conversion from 'float' to 'double' to match other operand of binary expression [-Wdouble-promotion]
   92 | #define QCONST16(x,bits) ((opus_val16)(.5+(x)*(((opus_val32)1)<<(bits))))
      |                                          ^
F:/circuit/firmware/a04/third_party/opus-1.6.1/celt/celt_encoder.c:879:14: note: in expansion of macro 'QCONST16'
  879 |       trim = QCONST16(4.f, 8);
      |              ^~~~~~~~
F:/circuit/firmware/a04/third_party/opus-1.6.1/celt/fixed_generic.h:92:42: warning: implicit conversion from 'float' to 'double' to match other operand of binary expression [-Wdouble-promotion]
   92 | #define QCONST16(x,bits) ((opus_val16)(.5+(x)*(((opus_val32)1)<<(bits))))
      |                                          ^
F:/circuit/firmware/a04/third_party/opus-1.6.1/celt/celt_encoder.c:882:14: note: in expansion of macro 'QCONST16'
  882 |       trim = QCONST16(4.f, 8) + QCONST16(1.f/16.f, 8)*frac;
      |              ^~~~~~~~
F:/circuit/firmware/a04/third_party/opus-1.6.1/celt/fixed_generic.h:92:42: warning: implicit conversion from 'float' to 'double' to match other operand of binary expression [-Wdouble-promotion]
   92 | #define QCONST16(x,bits) ((opus_val16)(.5+(x)*(((opus_val32)1)<<(bits))))
      |                                          ^
F:/circuit/firmware/a04/third_party/opus-1.6.1/celt/celt_encoder.c:882:33: note: in expansion of macro 'QCONST16'
  882 |       trim = QCONST16(4.f, 8) + QCONST16(1.f/16.f, 8)*frac;
      |                                 ^~~~~~~~
F:/circuit/firmware/a04/third_party/opus-1.6.1/celt/fixed_generic.h:92:42: warning: implicit conversion from 'float' to 'double' to match other operand of binary expression [-Wdouble-promotion]
   92 | #define QCONST16(x,bits) ((opus_val16)(.5+(x)*(((opus_val32)1)<<(bits))))
      |                                          ^
F:/circuit/firmware/a04/third_party/opus-1.6.1/celt/fixed_generic.h:131:24: note: in definition of macro 'SHR'
  131 | #define SHR(a,shift) ((a) >> (shift))
      |                        ^
F:/circuit/firmware/a04/third_party/opus-1.6.1/celt/fixed_generic.h:193:33: note: in expansion of macro 'MULT16_16'
  193 | #define MULT16_16_Q15(a,b) (SHR(MULT16_16((a),(b)),15))
      |                                 ^~~~~~~~~
F:/circuit/firmware/a04/third_party/opus-1.6.1/celt/celt_encoder.c:896:13: note: in expansion of macro 'MULT16_16_Q15'
  896 |       sum = MULT16_16_Q15(QCONST16(1.f/8, 15), sum);
      |             ^~~~~~~~~~~~~
F:/circuit/firmware/a04/third_party/opus-1.6.1/celt/celt_encoder.c:896:27: note: in expansion of macro 'QCONST16'
  896 |       sum = MULT16_16_Q15(QCONST16(1.f/8, 15), sum);
      |                           ^~~~~~~~
F:/circuit/firmware/a04/third_party/opus-1.6.1/celt/fixed_generic.h:92:42: warning: implicit conversion from 'float' to 'double' to match other operand of binary expression [-Wdouble-promotion]
   92 | #define QCONST16(x,bits) ((opus_val16)(.5+(x)*(((opus_val32)1)<<(bits))))
      |                                          ^
F:/circuit/firmware/a04/third_party/opus-1.6.1/celt/arch.h:100:22: note: in definition of macro 'MIN16'
  100 | #define MIN16(a,b) ((a) < (b) ? (a) : (b))   /**< Minimum 16-bit value.   */
      |                      ^
F:/circuit/firmware/a04/third_party/opus-1.6.1/celt/celt_encoder.c:897:19: note: in expansion of macro 'QCONST16'
  897 |       sum = MIN16(QCONST16(1.f, 10), ABS16(sum));
      |                   ^~~~~~~~
F:/circuit/firmware/a04/third_party/opus-1.6.1/celt/fixed_generic.h:92:42: warning: implicit conversion from 'float' to 'double' to match other operand of binary expression [-Wdouble-promotion]
   92 | #define QCONST16(x,bits) ((opus_val16)(.5+(x)*(((opus_val32)1)<<(bits))))
      |                                          ^
F:/circuit/firmware/a04/third_party/opus-1.6.1/celt/arch.h:100:34: note: in definition of macro 'MIN16'
  100 | #define MIN16(a,b) ((a) < (b) ? (a) : (b))   /**< Minimum 16-bit value.   */
      |                                  ^
F:/circuit/firmware/a04/third_party/opus-1.6.1/celt/celt_encoder.c:897:19: note: in expansion of macro 'QCONST16'
  897 |       sum = MIN16(QCONST16(1.f, 10), ABS16(sum));
      |                   ^~~~~~~~
F:/circuit/firmware/a04/third_party/opus-1.6.1/celt/fixed_generic.h:92:42: warning: implicit conversion from 'float' to 'double' to match other operand of binary expression [-Wdouble-promotion]
   92 | #define QCONST16(x,bits) ((opus_val16)(.5+(x)*(((opus_val32)1)<<(bits))))
      |                                          ^
F:/circuit/firmware/a04/third_party/opus-1.6.1/celt/arch.h:100:22: note: in definition of macro 'MIN16'
  100 | #define MIN16(a,b) ((a) < (b) ? (a) : (b))   /**< Minimum 16-bit value.   */
      |                      ^
F:/circuit/firmware/a04/third_party/opus-1.6.1/celt/celt_encoder.c:906:21: note: in expansion of macro 'QCONST16'
  906 |       minXC = MIN16(QCONST16(1.f, 10), ABS16(minXC));
      |                     ^~~~~~~~
F:/circuit/firmware/a04/third_party/opus-1.6.1/celt/fixed_generic.h:92:42: warning: implicit conversion from 'float' to 'double' to match other operand of binary expression [-Wdouble-promotion]
   92 | #define QCONST16(x,bits) ((opus_val16)(.5+(x)*(((opus_val32)1)<<(bits))))
      |                                          ^
F:/circuit/firmware/a04/third_party/opus-1.6.1/celt/arch.h:100:34: note: in definition of macro 'MIN16'
  100 | #define MIN16(a,b) ((a) < (b) ? (a) : (b))   /**< Minimum 16-bit value.   */
      |                                  ^
F:/circuit/firmware/a04/third_party/opus-1.6.1/celt/celt_encoder.c:906:21: note: in expansion of macro 'QCONST16'
  906 |       minXC = MIN16(QCONST16(1.f, 10), ABS16(minXC));
      |                     ^~~~~~~~
F:/circuit/firmware/a04/third_party/opus-1.6.1/celt/fixed_generic.h:95:42: warning: implicit conversion from 'float' to 'double' to match other operand of binary expression [-Wdouble-promotion]
   95 | #define QCONST32(x,bits) ((opus_val32)(.5+(x)*(((opus_int64)1)<<(bits))))
      |                                          ^
F:/circuit/firmware/a04/third_party/opus-1.6.1/celt/celt_encoder.c:909:25: note: in expansion of macro 'QCONST32'
  909 |       logXC = celt_log2(QCONST32(1.001f, 20)-MULT16_16(sum, sum));
      |                         ^~~~~~~~
F:/circuit/firmware/a04/third_party/opus-1.6.1/celt/fixed_generic.h:95:42: warning: implicit conversion from 'float' to 'double' to match other operand of binary expression [-Wdouble-promotion]
   95 | #define QCONST32(x,bits) ((opus_val32)(.5+(x)*(((opus_int64)1)<<(bits))))
      |                                          ^
F:/circuit/firmware/a04/third_party/opus-1.6.1/celt/arch.h:101:28: note: in definition of macro 'MAX16'
  101 | #define MAX16(a,b) ((a) > (b) ? (a) : (b))   /**< Maximum 16-bit value.   */
      |                            ^
F:/circuit/firmware/a04/third_party/opus-1.6.1/celt/celt_encoder.c:911:47: note: in expansion of macro 'QCONST32'
  911 |       logXC2 = MAX16(HALF16(logXC), celt_log2(QCONST32(1.001f, 20)-MULT16_16(minXC, minXC)));
      |                                               ^~~~~~~~
F:/circuit/firmware/a04/third_party/opus-1.6.1/celt/fixed_generic.h:95:42: warning: implicit conversion from 'float' to 'double' to match other operand of binary expression [-Wdouble-promotion]
   95 | #define QCONST32(x,bits) ((opus_val32)(.5+(x)*(((opus_int64)1)<<(bits))))
      |                                          ^
F:/circuit/firmware/a04/third_party/opus-1.6.1/celt/arch.h:101:40: note: in definition of macro 'MAX16'
  101 | #define MAX16(a,b) ((a) > (b) ? (a) : (b))   /**< Maximum 16-bit value.   */
      |                                        ^
F:/circuit/firmware/a04/third_party/opus-1.6.1/celt/celt_encoder.c:911:47: note: in expansion of macro 'QCONST32'
  911 |       logXC2 = MAX16(HALF16(logXC), celt_log2(QCONST32(1.001f, 20)-MULT16_16(minXC, minXC)));
      |                                               ^~~~~~~~
F:/circuit/firmware/a04/third_party/opus-1.6.1/celt/fixed_generic.h:92:42: warning: implicit conversion from 'float' to 'double' to match other operand of binary expression [-Wdouble-promotion]
   92 | #define QCONST16(x,bits) ((opus_val16)(.5+(x)*(((opus_val32)1)<<(bits))))
      |                                          ^
F:/circuit/firmware/a04/third_party/opus-1.6.1/celt/fixed_generic.h:118:26: note: in definition of macro 'SHR32'
  118 | #define SHR32(a,shift) ((a) >> (shift))
      |                          ^
F:/circuit/firmware/a04/third_party/opus-1.6.1/celt/celt_encoder.c:914:15: note: in expansion of macro 'PSHR32'
  914 |       logXC = PSHR32(logXC-QCONST16(6.f, 10),10-8);
      |               ^~~~~~
F:/circuit/firmware/a04/third_party/opus-1.6.1/celt/celt_encoder.c:914:28: note: in expansion of macro 'QCONST16'
  914 |       logXC = PSHR32(logXC-QCONST16(6.f, 10),10-8);
      |                            ^~~~~~~~
F:/circuit/firmware/a04/third_party/opus-1.6.1/celt/fixed_generic.h:92:42: warning: implicit conversion from 'float' to 'double' to match other operand of binary expression [-Wdouble-promotion]
   92 | #define QCONST16(x,bits) ((opus_val16)(.5+(x)*(((opus_val32)1)<<(bits))))
      |                                          ^
F:/circuit/firmware/a04/third_party/opus-1.6.1/celt/fixed_generic.h:118:26: note: in definition of macro 'SHR32'
  118 | #define SHR32(a,shift) ((a) >> (shift))
      |                          ^
F:/circuit/firmware/a04/third_party/opus-1.6.1/celt/celt_encoder.c:915:16: note: in expansion of macro 'PSHR32'
  915 |       logXC2 = PSHR32(logXC2-QCONST16(6.f, 10),10-8);
      |                ^~~~~~
F:/circuit/firmware/a04/third_party/opus-1.6.1/celt/celt_encoder.c:915:30: note: in expansion of macro 'QCONST16'
  915 |       logXC2 = PSHR32(logXC2-QCONST16(6.f, 10),10-8);
      |                              ^~~~~~~~
F:/circuit/firmware/a04/third_party/opus-1.6.1/celt/fixed_generic.h:92:42: warning: implicit conversion from 'float' to 'double' to match other operand of binary expression [-Wdouble-promotion]
   92 | #define QCONST16(x,bits) ((opus_val16)(.5+(x)*(((opus_val32)1)<<(bits))))
      |                                          ^
F:/circuit/firmware/a04/third_party/opus-1.6.1/celt/arch.h:101:22: note: in definition of macro 'MAX16'
  101 | #define MAX16(a,b) ((a) > (b) ? (a) : (b))   /**< Maximum 16-bit value.   */
      |                      ^
F:/circuit/firmware/a04/third_party/opus-1.6.1/celt/celt_encoder.c:918:22: note: in expansion of macro 'QCONST16'
  918 |       trim += MAX16(-QCONST16(4.f, 8), MULT16_16_Q15(QCONST16(.75f,15),logXC));
      |                      ^~~~~~~~
F:/circuit/firmware/a04/third_party/opus-1.6.1/celt/fixed_generic.h:92:42: warning: implicit conversion from 'float' to 'double' to match other operand of binary expression [-Wdouble-promotion]
   92 | #define QCONST16(x,bits) ((opus_val16)(.5+(x)*(((opus_val32)1)<<(bits))))
      |                                          ^
F:/circuit/firmware/a04/third_party/opus-1.6.1/celt/arch.h:101:28: note: in definition of macro 'MAX16'
  101 | #define MAX16(a,b) ((a) > (b) ? (a) : (b))   /**< Maximum 16-bit value.   */
      |                            ^
F:/circuit/firmware/a04/third_party/opus-1.6.1/celt/fixed_generic.h:193:29: note: in expansion of macro 'SHR'
  193 | #define MULT16_16_Q15(a,b) (SHR(MULT16_16((a),(b)),15))
      |                             ^~~
F:/circuit/firmware/a04/third_party/opus-1.6.1/celt/fixed_generic.h:193:33: note: in expansion of macro 'MULT16_16'
  193 | #define MULT16_16_Q15(a,b) (SHR(MULT16_16((a),(b)),15))
      |                                 ^~~~~~~~~
F:/circuit/firmware/a04/third_party/opus-1.6.1/celt/celt_encoder.c:918:40: note: in expansion of macro 'MULT16_16_Q15'
  918 |       trim += MAX16(-QCONST16(4.f, 8), MULT16_16_Q15(QCONST16(.75f,15),logXC));
      |                                        ^~~~~~~~~~~~~
F:/circuit/firmware/a04/third_party/opus-1.6.1/celt/celt_encoder.c:918:54: note: in expansion of macro 'QCONST16'
  918 |       trim += MAX16(-QCONST16(4.f, 8), MULT16_16_Q15(QCONST16(.75f,15),logXC));
      |                                                      ^~~~~~~~
F:/circuit/firmware/a04/third_party/opus-1.6.1/celt/fixed_generic.h:92:42: warning: implicit conversion from 'float' to 'double' to match other operand of binary expression [-Wdouble-promotion]
   92 | #define QCONST16(x,bits) ((opus_val16)(.5+(x)*(((opus_val32)1)<<(bits))))
      |                                          ^
F:/circuit/firmware/a04/third_party/opus-1.6.1/celt/arch.h:101:34: note: in definition of macro 'MAX16'
  101 | #define MAX16(a,b) ((a) > (b) ? (a) : (b))   /**< Maximum 16-bit value.   */
      |                                  ^
F:/circuit/firmware/a04/third_party/opus-1.6.1/celt/celt_encoder.c:918:22: note: in expansion of macro 'QCONST16'
  918 |       trim += MAX16(-QCONST16(4.f, 8), MULT16_16_Q15(QCONST16(.75f,15),logXC));
      |                      ^~~~~~~~
F:/circuit/firmware/a04/third_party/opus-1.6.1/celt/fixed_generic.h:92:42: warning: implicit conversion from 'float' to 'double' to match other operand of binary expression [-Wdouble-promotion]
   92 | #define QCONST16(x,bits) ((opus_val16)(.5+(x)*(((opus_val32)1)<<(bits))))
      |                                          ^
F:/circuit/firmware/a04/third_party/opus-1.6.1/celt/arch.h:101:40: note: in definition of macro 'MAX16'
  101 | #define MAX16(a,b) ((a) > (b) ? (a) : (b))   /**< Maximum 16-bit value.   */
      |                                        ^
F:/circuit/firmware/a04/third_party/opus-1.6.1/celt/fixed_generic.h:193:29: note: in expansion of macro 'SHR'
  193 | #define MULT16_16_Q15(a,b) (SHR(MULT16_16((a),(b)),15))
      |                             ^~~
F:/circuit/firmware/a04/third_party/opus-1.6.1/celt/fixed_generic.h:193:33: note: in expansion of macro 'MULT16_16'
  193 | #define MULT16_16_Q15(a,b) (SHR(MULT16_16((a),(b)),15))
      |                                 ^~~~~~~~~
F:/circuit/firmware/a04/third_party/opus-1.6.1/celt/celt_encoder.c:918:40: note: in expansion of macro 'MULT16_16_Q15'
  918 |       trim += MAX16(-QCONST16(4.f, 8), MULT16_16_Q15(QCONST16(.75f,15),logXC));
      |                                        ^~~~~~~~~~~~~
F:/circuit/firmware/a04/third_party/opus-1.6.1/celt/celt_encoder.c:918:54: note: in expansion of macro 'QCONST16'
  918 |       trim += MAX16(-QCONST16(4.f, 8), MULT16_16_Q15(QCONST16(.75f,15),logXC));
      |                                                      ^~~~~~~~
F:/circuit/firmware/a04/third_party/opus-1.6.1/celt/fixed_generic.h:92:42: warning: implicit conversion from 'float' to 'double' to match other operand of binary expression [-Wdouble-promotion]
   92 | #define QCONST16(x,bits) ((opus_val16)(.5+(x)*(((opus_val32)1)<<(bits))))
      |                                          ^
F:/circuit/firmware/a04/third_party/opus-1.6.1/celt/arch.h:100:22: note: in definition of macro 'MIN16'
  100 | #define MIN16(a,b) ((a) < (b) ? (a) : (b))   /**< Minimum 16-bit value.   */
      |                      ^
F:/circuit/firmware/a04/third_party/opus-1.6.1/celt/celt_encoder.c:919:47: note: in expansion of macro 'QCONST16'
  919 |       *stereo_saving = MIN16(*stereo_saving + QCONST16(0.25f, 8), -HALF16(logXC2));
      |                                               ^~~~~~~~
F:/circuit/firmware/a04/third_party/opus-1.6.1/celt/fixed_generic.h:92:42: warning: implicit conversion from 'float' to 'double' to match other operand of binary expression [-Wdouble-promotion]
   92 | #define QCONST16(x,bits) ((opus_val16)(.5+(x)*(((opus_val32)1)<<(bits))))
      |                                          ^
F:/circuit/firmware/a04/third_party/opus-1.6.1/celt/arch.h:100:34: note: in definition of macro 'MIN16'
  100 | #define MIN16(a,b) ((a) < (b) ? (a) : (b))   /**< Minimum 16-bit value.   */
      |                                  ^
F:/circuit/firmware/a04/third_party/opus-1.6.1/celt/celt_encoder.c:919:47: note: in expansion of macro 'QCONST16'
  919 |       *stereo_saving = MIN16(*stereo_saving + QCONST16(0.25f, 8), -HALF16(logXC2));
      |                                               ^~~~~~~~
F:/circuit/firmware/a04/third_party/opus-1.6.1/celt/fixed_generic.h:92:42: warning: implicit conversion from 'float' to 'double' to match other operand of binary expression [-Wdouble-promotion]
   92 | #define QCONST16(x,bits) ((opus_val16)(.5+(x)*(((opus_val32)1)<<(bits))))
      |                                          ^
F:/circuit/firmware/a04/third_party/opus-1.6.1/celt/arch.h:103:22: note: in definition of macro 'MAX32'
  103 | #define MAX32(a,b) ((a) > (b) ? (a) : (b))   /**< Maximum 32-bit value.   */
      |                      ^
F:/circuit/firmware/a04/third_party/opus-1.6.1/celt/celt_encoder.c:931:19: note: in expansion of macro 'QCONST16'
  931 |    trim -= MAX32(-QCONST16(2.f, 8), MIN32(QCONST16(2.f, 8), SHR32(diff+QCONST32(1.f, DB_SHIFT-5),DB_SHIFT-13)/6 ));
      |                   ^~~~~~~~
F:/circuit/firmware/a04/third_party/opus-1.6.1/celt/fixed_generic.h:92:42: warning: implicit conversion from 'float' to 'double' to match other operand of binary expression [-Wdouble-promotion]
   92 | #define QCONST16(x,bits) ((opus_val16)(.5+(x)*(((opus_val32)1)<<(bits))))
      |                                          ^
F:/circuit/firmware/a04/third_party/opus-1.6.1/celt/arch.h:103:28: note: in definition of macro 'MAX32'
  103 | #define MAX32(a,b) ((a) > (b) ? (a) : (b))   /**< Maximum 32-bit value.   */
      |                            ^
F:/circuit/firmware/a04/third_party/opus-1.6.1/celt/celt_encoder.c:931:37: note: in expansion of macro 'MIN32'
  931 |    trim -= MAX32(-QCONST16(2.f, 8), MIN32(QCONST16(2.f, 8), SHR32(diff+QCONST32(1.f, DB_SHIFT-5),DB_SHIFT-13)/6 ));
      |                                     ^~~~~
F:/circuit/firmware/a04/third_party/opus-1.6.1/celt/celt_encoder.c:931:43: note: in expansion of macro 'QCONST16'
  931 |    trim -= MAX32(-QCONST16(2.f, 8), MIN32(QCONST16(2.f, 8), SHR32(diff+QCONST32(1.f, DB_SHIFT-5),DB_SHIFT-13)/6 ));
      |                                           ^~~~~~~~
F:/circuit/firmware/a04/third_party/opus-1.6.1/celt/fixed_generic.h:95:42: warning: implicit conversion from 'float' to 'double' to match other operand of binary expression [-Wdouble-promotion]
   95 | #define QCONST32(x,bits) ((opus_val32)(.5+(x)*(((opus_int64)1)<<(bits))))
      |                                          ^
F:/circuit/firmware/a04/third_party/opus-1.6.1/celt/arch.h:103:28: note: in definition of macro 'MAX32'
  103 | #define MAX32(a,b) ((a) > (b) ? (a) : (b))   /**< Maximum 32-bit value.   */
      |                            ^
F:/circuit/firmware/a04/third_party/opus-1.6.1/celt/celt_encoder.c:931:37: note: in expansion of macro 'MIN32'
  931 |    trim -= MAX32(-QCONST16(2.f, 8), MIN32(QCONST16(2.f, 8), SHR32(diff+QCONST32(1.f, DB_SHIFT-5),DB_SHIFT-13)/6 ));
      |                                     ^~~~~
F:/circuit/firmware/a04/third_party/opus-1.6.1/celt/celt_encoder.c:931:61: note: in expansion of macro 'SHR32'
  931 |    trim -= MAX32(-QCONST16(2.f, 8), MIN32(QCONST16(2.f, 8), SHR32(diff+QCONST32(1.f, DB_SHIFT-5),DB_SHIFT-13)/6 ));
      |                                                             ^~~~~
F:/circuit/firmware/a04/third_party/opus-1.6.1/celt/celt_encoder.c:931:72: note: in expansion of macro 'QCONST32'
  931 |    trim -= MAX32(-QCONST16(2.f, 8), MIN32(QCONST16(2.f, 8), SHR32(diff+QCONST32(1.f, DB_SHIFT-5),DB_SHIFT-13)/6 ));
      |                                                                        ^~~~~~~~
F:/circuit/firmware/a04/third_party/opus-1.6.1/celt/fixed_generic.h:92:42: warning: implicit conversion from 'float' to 'double' to match other operand of binary expression [-Wdouble-promotion]
   92 | #define QCONST16(x,bits) ((opus_val16)(.5+(x)*(((opus_val32)1)<<(bits))))
      |                                          ^
F:/circuit/firmware/a04/third_party/opus-1.6.1/celt/arch.h:103:28: note: in definition of macro 'MAX32'
  103 | #define MAX32(a,b) ((a) > (b) ? (a) : (b))   /**< Maximum 32-bit value.   */
      |                            ^
F:/circuit/firmware/a04/third_party/opus-1.6.1/celt/celt_encoder.c:931:37: note: in expansion of macro 'MIN32'
  931 |    trim -= MAX32(-QCONST16(2.f, 8), MIN32(QCONST16(2.f, 8), SHR32(diff+QCONST32(1.f, DB_SHIFT-5),DB_SHIFT-13)/6 ));
      |                                     ^~~~~
F:/circuit/firmware/a04/third_party/opus-1.6.1/celt/celt_encoder.c:931:43: note: in expansion of macro 'QCONST16'
  931 |    trim -= MAX32(-QCONST16(2.f, 8), MIN32(QCONST16(2.f, 8), SHR32(diff+QCONST32(1.f, DB_SHIFT-5),DB_SHIFT-13)/6 ));
      |                                           ^~~~~~~~
F:/circuit/firmware/a04/third_party/opus-1.6.1/celt/fixed_generic.h:95:42: warning: implicit conversion from 'float' to 'double' to match other operand of binary expression [-Wdouble-promotion]
   95 | #define QCONST32(x,bits) ((opus_val32)(.5+(x)*(((opus_int64)1)<<(bits))))
      |                                          ^
F:/circuit/firmware/a04/third_party/opus-1.6.1/celt/arch.h:103:28: note: in definition of macro 'MAX32'
  103 | #define MAX32(a,b) ((a) > (b) ? (a) : (b))   /**< Maximum 32-bit value.   */
      |                            ^
F:/circuit/firmware/a04/third_party/opus-1.6.1/celt/celt_encoder.c:931:37: note: in expansion of macro 'MIN32'
  931 |    trim -= MAX32(-QCONST16(2.f, 8), MIN32(QCONST16(2.f, 8), SHR32(diff+QCONST32(1.f, DB_SHIFT-5),DB_SHIFT-13)/6 ));
      |                                     ^~~~~
F:/circuit/firmware/a04/third_party/opus-1.6.1/celt/celt_encoder.c:931:61: note: in expansion of macro 'SHR32'
  931 |    trim -= MAX32(-QCONST16(2.f, 8), MIN32(QCONST16(2.f, 8), SHR32(diff+QCONST32(1.f, DB_SHIFT-5),DB_SHIFT-13)/6 ));
      |                                                             ^~~~~
F:/circuit/firmware/a04/third_party/opus-1.6.1/celt/celt_encoder.c:931:72: note: in expansion of macro 'QCONST32'
  931 |    trim -= MAX32(-QCONST16(2.f, 8), MIN32(QCONST16(2.f, 8), SHR32(diff+QCONST32(1.f, DB_SHIFT-5),DB_SHIFT-13)/6 ));
      |                                                                        ^~~~~~~~
F:/circuit/firmware/a04/third_party/opus-1.6.1/celt/fixed_generic.h:92:42: warning: implicit conversion from 'float' to 'double' to match other operand of binary expression [-Wdouble-promotion]
   92 | #define QCONST16(x,bits) ((opus_val16)(.5+(x)*(((opus_val32)1)<<(bits))))
      |                                          ^
F:/circuit/firmware/a04/third_party/opus-1.6.1/celt/arch.h:103:34: note: in definition of macro 'MAX32'
  103 | #define MAX32(a,b) ((a) > (b) ? (a) : (b))   /**< Maximum 32-bit value.   */
      |                                  ^
F:/circuit/firmware/a04/third_party/opus-1.6.1/celt/celt_encoder.c:931:19: note: in expansion of macro 'QCONST16'
  931 |    trim -= MAX32(-QCONST16(2.f, 8), MIN32(QCONST16(2.f, 8), SHR32(diff+QCONST32(1.f, DB_SHIFT-5),DB_SHIFT-13)/6 ));
      |                   ^~~~~~~~
F:/circuit/firmware/a04/third_party/opus-1.6.1/celt/fixed_generic.h:92:42: warning: implicit conversion from 'float' to 'double' to match other operand of binary expression [-Wdouble-promotion]
   92 | #define QCONST16(x,bits) ((opus_val16)(.5+(x)*(((opus_val32)1)<<(bits))))
      |                                          ^
F:/circuit/firmware/a04/third_party/opus-1.6.1/celt/arch.h:103:40: note: in definition of macro 'MAX32'
  103 | #define MAX32(a,b) ((a) > (b) ? (a) : (b))   /**< Maximum 32-bit value.   */
      |                                        ^
F:/circuit/firmware/a04/third_party/opus-1.6.1/celt/celt_encoder.c:931:37: note: in expansion of macro 'MIN32'
  931 |    trim -= MAX32(-QCONST16(2.f, 8), MIN32(QCONST16(2.f, 8), SHR32(diff+QCONST32(1.f, DB_SHIFT-5),DB_SHIFT-13)/6 ));
      |                                     ^~~~~
F:/circuit/firmware/a04/third_party/opus-1.6.1/celt/celt_encoder.c:931:43: note: in expansion of macro 'QCONST16'
  931 |    trim -= MAX32(-QCONST16(2.f, 8), MIN32(QCONST16(2.f, 8), SHR32(diff+QCONST32(1.f, DB_SHIFT-5),DB_SHIFT-13)/6 ));
      |                                           ^~~~~~~~
F:/circuit/firmware/a04/third_party/opus-1.6.1/celt/fixed_generic.h:95:42: warning: implicit conversion from 'float' to 'double' to match other operand of binary expression [-Wdouble-promotion]
   95 | #define QCONST32(x,bits) ((opus_val32)(.5+(x)*(((opus_int64)1)<<(bits))))
      |                                          ^
F:/circuit/firmware/a04/third_party/opus-1.6.1/celt/arch.h:103:40: note: in definition of macro 'MAX32'
  103 | #define MAX32(a,b) ((a) > (b) ? (a) : (b))   /**< Maximum 32-bit value.   */
      |                                        ^
F:/circuit/firmware/a04/third_party/opus-1.6.1/celt/celt_encoder.c:931:37: note: in expansion of macro 'MIN32'
  931 |    trim -= MAX32(-QCONST16(2.f, 8), MIN32(QCONST16(2.f, 8), SHR32(diff+QCONST32(1.f, DB_SHIFT-5),DB_SHIFT-13)/6 ));
      |                                     ^~~~~
F:/circuit/firmware/a04/third_party/opus-1.6.1/celt/celt_encoder.c:931:61: note: in expansion of macro 'SHR32'
  931 |    trim -= MAX32(-QCONST16(2.f, 8), MIN32(QCONST16(2.f, 8), SHR32(diff+QCONST32(1.f, DB_SHIFT-5),DB_SHIFT-13)/6 ));
      |                                                             ^~~~~
F:/circuit/firmware/a04/third_party/opus-1.6.1/celt/celt_encoder.c:931:72: note: in expansion of macro 'QCONST32'
  931 |    trim -= MAX32(-QCONST16(2.f, 8), MIN32(QCONST16(2.f, 8), SHR32(diff+QCONST32(1.f, DB_SHIFT-5),DB_SHIFT-13)/6 ));
      |                                                                        ^~~~~~~~
F:/circuit/firmware/a04/third_party/opus-1.6.1/celt/fixed_generic.h:92:42: warning: implicit conversion from 'float' to 'double' to match other operand of binary expression [-Wdouble-promotion]
   92 | #define QCONST16(x,bits) ((opus_val16)(.5+(x)*(((opus_val32)1)<<(bits))))
      |                                          ^
F:/circuit/firmware/a04/third_party/opus-1.6.1/celt/arch.h:103:40: note: in definition of macro 'MAX32'
  103 | #define MAX32(a,b) ((a) > (b) ? (a) : (b))   /**< Maximum 32-bit value.   */
      |                                        ^
F:/circuit/firmware/a04/third_party/opus-1.6.1/celt/celt_encoder.c:931:37: note: in expansion of macro 'MIN32'
  931 |    trim -= MAX32(-QCONST16(2.f, 8), MIN32(QCONST16(2.f, 8), SHR32(diff+QCONST32(1.f, DB_SHIFT-5),DB_SHIFT-13)/6 ));
      |                                     ^~~~~
F:/circuit/firmware/a04/third_party/opus-1.6.1/celt/celt_encoder.c:931:43: note: in expansion of macro 'QCONST16'
  931 |    trim -= MAX32(-QCONST16(2.f, 8), MIN32(QCONST16(2.f, 8), SHR32(diff+QCONST32(1.f, DB_SHIFT-5),DB_SHIFT-13)/6 ));
      |                                           ^~~~~~~~
F:/circuit/firmware/a04/third_party/opus-1.6.1/celt/fixed_generic.h:95:42: warning: implicit conversion from 'float' to 'double' to match other operand of binary expression [-Wdouble-promotion]
   95 | #define QCONST32(x,bits) ((opus_val32)(.5+(x)*(((opus_int64)1)<<(bits))))
      |                                          ^
F:/circuit/firmware/a04/third_party/opus-1.6.1/celt/arch.h:103:40: note: in definition of macro 'MAX32'
  103 | #define MAX32(a,b) ((a) > (b) ? (a) : (b))   /**< Maximum 32-bit value.   */
      |                                        ^
F:/circuit/firmware/a04/third_party/opus-1.6.1/celt/celt_encoder.c:931:37: note: in expansion of macro 'MIN32'
  931 |    trim -= MAX32(-QCONST16(2.f, 8), MIN32(QCONST16(2.f, 8), SHR32(diff+QCONST32(1.f, DB_SHIFT-5),DB_SHIFT-13)/6 ));
      |                                     ^~~~~
F:/circuit/firmware/a04/third_party/opus-1.6.1/celt/celt_encoder.c:931:61: note: in expansion of macro 'SHR32'
  931 |    trim -= MAX32(-QCONST16(2.f, 8), MIN32(QCONST16(2.f, 8), SHR32(diff+QCONST32(1.f, DB_SHIFT-5),DB_SHIFT-13)/6 ));
      |                                                             ^~~~~
F:/circuit/firmware/a04/third_party/opus-1.6.1/celt/celt_encoder.c:931:72: note: in expansion of macro 'QCONST32'
  931 |    trim -= MAX32(-QCONST16(2.f, 8), MIN32(QCONST16(2.f, 8), SHR32(diff+QCONST32(1.f, DB_SHIFT-5),DB_SHIFT-13)/6 ));
      |                                                                        ^~~~~~~~
F:/circuit/firmware/a04/third_party/opus-1.6.1/celt/celt_encoder.c: In function 'stereo_analysis':
F:/circuit/firmware/a04/third_party/opus-1.6.1/celt/fixed_generic.h:92:42: warning: implicit conversion from 'float' to 'double' to match other operand of binary expression [-Wdouble-promotion]
   92 | #define QCONST16(x,bits) ((opus_val16)(.5+(x)*(((opus_val32)1)<<(bits))))
      |                                          ^
F:/circuit/firmware/a04/third_party/opus-1.6.1/celt/fixed_generic.h:152:34: note: in definition of macro 'ADD32'
  152 | #define ADD32(a,b) ((opus_val32)(a)+(opus_val32)(b))
      |                                  ^
F:/circuit/firmware/a04/third_party/opus-1.6.1/celt/fixed_generic.h:132:22: note: in expansion of macro 'SHL32'
  132 | #define SHL(a,shift) SHL32(a,shift)
      |                      ^~~~~
F:/circuit/firmware/a04/third_party/opus-1.6.1/celt/fixed_generic.h:57:34: note: in expansion of macro 'SHL'
   57 | #define MULT16_32_Q15(a,b) ADD32(SHL(MULT16_16((a),SHR((b),16)),1), SHR(MULT16_16SU((a),((b)&0x0000ffff)),15))
      |                                  ^~~
F:/circuit/firmware/a04/third_party/opus-1.6.1/celt/fixed_generic.h:57:38: note: in expansion of macro 'MULT16_16'
   57 | #define MULT16_32_Q15(a,b) ADD32(SHL(MULT16_16((a),SHR((b),16)),1), SHR(MULT16_16SU((a),((b)&0x0000ffff)),15))
      |                                      ^~~~~~~~~
F:/circuit/firmware/a04/third_party/opus-1.6.1/celt/celt_encoder.c:980:12: note: in expansion of macro 'MULT16_32_Q15'
  980 |    sumMS = MULT16_32_Q15(QCONST16(0.707107f, 15), sumMS);
      |            ^~~~~~~~~~~~~
F:/circuit/firmware/a04/third_party/opus-1.6.1/celt/celt_encoder.c:980:26: note: in expansion of macro 'QCONST16'
  980 |    sumMS = MULT16_32_Q15(QCONST16(0.707107f, 15), sumMS);
      |                          ^~~~~~~~
F:/circuit/firmware/a04/third_party/opus-1.6.1/celt/fixed_generic.h:92:42: warning: implicit conversion from 'float' to 'double' to match other operand of binary expression [-Wdouble-promotion]
   92 | #define QCONST16(x,bits) ((opus_val16)(.5+(x)*(((opus_val32)1)<<(bits))))
      |                                          ^
F:/circuit/firmware/a04/third_party/opus-1.6.1/celt/fixed_generic.h:152:50: note: in definition of macro 'ADD32'
  152 | #define ADD32(a,b) ((opus_val32)(a)+(opus_val32)(b))
      |                                                  ^
F:/circuit/firmware/a04/third_party/opus-1.6.1/celt/fixed_generic.h:57:69: note: in expansion of macro 'SHR'
   57 | #define MULT16_32_Q15(a,b) ADD32(SHL(MULT16_16((a),SHR((b),16)),1), SHR(MULT16_16SU((a),((b)&0x0000ffff)),15))
      |                                                                     ^~~
F:/circuit/firmware/a04/third_party/opus-1.6.1/celt/fixed_generic.h:57:73: note: in expansion of macro 'MULT16_16SU'
   57 | #define MULT16_32_Q15(a,b) ADD32(SHL(MULT16_16((a),SHR((b),16)),1), SHR(MULT16_16SU((a),((b)&0x0000ffff)),15))
      |                                                                         ^~~~~~~~~~~
F:/circuit/firmware/a04/third_party/opus-1.6.1/celt/celt_encoder.c:980:12: note: in expansion of macro 'MULT16_32_Q15'
  980 |    sumMS = MULT16_32_Q15(QCONST16(0.707107f, 15), sumMS);
      |            ^~~~~~~~~~~~~
F:/circuit/firmware/a04/third_party/opus-1.6.1/celt/celt_encoder.c:980:26: note: in expansion of macro 'QCONST16'
  980 |    sumMS = MULT16_32_Q15(QCONST16(0.707107f, 15), sumMS);
      |                          ^~~~~~~~
F:/circuit/firmware/a04/third_party/opus-1.6.1/celt/celt_encoder.c: In function 'dynalloc_analysis':
F:/circuit/firmware/a04/third_party/opus-1.6.1/celt/fixed_generic.h:98:40: warning: implicit conversion from 'float' to 'double' to match other operand of binary expression [-Wdouble-promotion]
   98 | #define GCONST2(x,bits) ((celt_glog)(.5+(x)*(((celt_glog)1)<<(bits))))
      |                                        ^
F:/circuit/firmware/a04/third_party/opus-1.6.1/celt/fixed_generic.h:101:19: note: in expansion of macro 'GCONST2'
  101 | #define GCONST(x) GCONST2((x),DB_SHIFT)
      |                   ^~~~~~~
F:/circuit/firmware/a04/third_party/opus-1.6.1/celt/celt_encoder.c:1068:14: note: in expansion of macro 'GCONST'
 1068 |    maxDepth=-GCONST(31.9f);
      |              ^~~~~~
F:/circuit/firmware/a04/third_party/opus-1.6.1/celt/fixed_generic.h:98:40: warning: implicit conversion from 'float' to 'double' to match other operand of binary expression [-Wdouble-promotion]
   98 | #define GCONST2(x,bits) ((celt_glog)(.5+(x)*(((celt_glog)1)<<(bits))))
      |                                        ^
F:/circuit/firmware/a04/third_party/opus-1.6.1/celt/fixed_generic.h:101:19: note: in expansion of macro 'GCONST2'
  101 | #define GCONST(x) GCONST2((x),DB_SHIFT)
      |                   ^~~~~~~
F:/circuit/firmware/a04/third_party/opus-1.6.1/celt/celt_encoder.c:1073:24: note: in expansion of macro 'GCONST'
 1073 |       noise_floor[i] = GCONST(0.0625f)*logN[i]
      |                        ^~~~~~
F:/circuit/firmware/a04/third_party/opus-1.6.1/celt/fixed_generic.h:98:40: warning: implicit conversion from 'float' to 'double' to match other operand of binary expression [-Wdouble-promotion]
   98 | #define GCONST2(x,bits) ((celt_glog)(.5+(x)*(((celt_glog)1)<<(bits))))
      |                                        ^
F:/circuit/firmware/a04/third_party/opus-1.6.1/celt/fixed_generic.h:101:19: note: in expansion of macro 'GCONST2'
  101 | #define GCONST(x) GCONST2((x),DB_SHIFT)
      |                   ^~~~~~~
F:/circuit/firmware/a04/third_party/opus-1.6.1/celt/celt_encoder.c:1074:14: note: in expansion of macro 'GCONST'
 1074 |             +GCONST(.5f)+SHL32(9-lsb_depth,DB_SHIFT)-SHL32(eMeans[i],DB_SHIFT-4)
      |              ^~~~~~
F:/circuit/firmware/a04/third_party/opus-1.6.1/celt/fixed_generic.h:98:40: warning: implicit conversion from 'float' to 'double' to match other operand of binary expression [-Wdouble-promotion]
   98 | #define GCONST2(x,bits) ((celt_glog)(.5+(x)*(((celt_glog)1)<<(bits))))
      |                                        ^
F:/circuit/firmware/a04/third_party/opus-1.6.1/celt/fixed_generic.h:101:19: note: in expansion of macro 'GCONST2'
  101 | #define GCONST(x) GCONST2((x),DB_SHIFT)
      |                   ^~~~~~~
F:/circuit/firmware/a04/third_party/opus-1.6.1/celt/celt_encoder.c:1075:14: note: in expansion of macro 'GCONST'
 1075 |             +GCONST(.0062f)*(i+5)*(i+5);
      |              ^~~~~~
F:/circuit/firmware/a04/third_party/opus-1.6.1/celt/fixed_generic.h:98:40: warning: implicit conversion from 'float' to 'double' to match other operand of binary expression [-Wdouble-promotion]
   98 | #define GCONST2(x,bits) ((celt_glog)(.5+(x)*(((celt_glog)1)<<(bits))))
      |                                        ^
F:/circuit/firmware/a04/third_party/opus-1.6.1/celt/arch.h:103:28: note: in definition of macro 'MAX32'
  103 | #define MAX32(a,b) ((a) > (b) ? (a) : (b))   /**< Maximum 32-bit value.   */
      |                            ^
F:/circuit/firmware/a04/third_party/opus-1.6.1/celt/celt_encoder.c:1098:20: note: in expansion of macro 'MAXG'
 1098 |          mask[i] = MAXG(mask[i], mask[i-1] - GCONST(2.f));
      |                    ^~~~
F:/circuit/firmware/a04/third_party/opus-1.6.1/celt/fixed_generic.h:101:19: note: in expansion of macro 'GCONST2'
  101 | #define GCONST(x) GCONST2((x),DB_SHIFT)
      |                   ^~~~~~~
F:/circuit/firmware/a04/third_party/opus-1.6.1/celt/celt_encoder.c:1098:46: note: in expansion of macro 'GCONST'
 1098 |          mask[i] = MAXG(mask[i], mask[i-1] - GCONST(2.f));
      |                                              ^~~~~~
F:/circuit/firmware/a04/third_party/opus-1.6.1/celt/fixed_generic.h:98:40: warning: implicit conversion from 'float' to 'double' to match other operand of binary expression [-Wdouble-promotion]
   98 | #define GCONST2(x,bits) ((celt_glog)(.5+(x)*(((celt_glog)1)<<(bits))))
      |                                        ^
F:/circuit/firmware/a04/third_party/opus-1.6.1/celt/arch.h:103:40: note: in definition of macro 'MAX32'
  103 | #define MAX32(a,b) ((a) > (b) ? (a) : (b))   /**< Maximum 32-bit value.   */
      |                                        ^
F:/circuit/firmware/a04/third_party/opus-1.6.1/celt/celt_encoder.c:1098:20: note: in expansion of macro 'MAXG'
 1098 |          mask[i] = MAXG(mask[i], mask[i-1] - GCONST(2.f));
      |                    ^~~~
F:/circuit/firmware/a04/third_party/opus-1.6.1/celt/fixed_generic.h:101:19: note: in expansion of macro 'GCONST2'
  101 | #define GCONST(x) GCONST2((x),DB_SHIFT)
      |                   ^~~~~~~
F:/circuit/firmware/a04/third_party/opus-1.6.1/celt/celt_encoder.c:1098:46: note: in expansion of macro 'GCONST'
 1098 |          mask[i] = MAXG(mask[i], mask[i-1] - GCONST(2.f));
      |                                              ^~~~~~
F:/circuit/firmware/a04/third_party/opus-1.6.1/celt/fixed_generic.h:98:40: warning: implicit conversion from 'float' to 'double' to match other operand of binary expression [-Wdouble-promotion]
   98 | #define GCONST2(x,bits) ((celt_glog)(.5+(x)*(((celt_glog)1)<<(bits))))
      |                                        ^
F:/circuit/firmware/a04/third_party/opus-1.6.1/celt/arch.h:103:28: note: in definition of macro 'MAX32'
  103 | #define MAX32(a,b) ((a) > (b) ? (a) : (b))   /**< Maximum 32-bit value.   */
      |                            ^
F:/circuit/firmware/a04/third_party/opus-1.6.1/celt/celt_encoder.c:1100:20: note: in expansion of macro 'MAXG'
 1100 |          mask[i] = MAXG(mask[i], mask[i+1] - GCONST(3.f));
      |                    ^~~~
F:/circuit/firmware/a04/third_party/opus-1.6.1/celt/fixed_generic.h:101:19: note: in expansion of macro 'GCONST2'
  101 | #define GCONST(x) GCONST2((x),DB_SHIFT)
      |                   ^~~~~~~
F:/circuit/firmware/a04/third_party/opus-1.6.1/celt/celt_encoder.c:1100:46: note: in expansion of macro 'GCONST'
 1100 |          mask[i] = MAXG(mask[i], mask[i+1] - GCONST(3.f));
      |                                              ^~~~~~
F:/circuit/firmware/a04/third_party/opus-1.6.1/celt/fixed_generic.h:98:40: warning: implicit conversion from 'float' to 'double' to match other operand of binary expression [-Wdouble-promotion]
   98 | #define GCONST2(x,bits) ((celt_glog)(.5+(x)*(((celt_glog)1)<<(bits))))
      |                                        ^
F:/circuit/firmware/a04/third_party/opus-1.6.1/celt/arch.h:103:40: note: in definition of macro 'MAX32'
  103 | #define MAX32(a,b) ((a) > (b) ? (a) : (b))   /**< Maximum 32-bit value.   */
      |                                        ^
F:/circuit/firmware/a04/third_party/opus-1.6.1/celt/celt_encoder.c:1100:20: note: in expansion of macro 'MAXG'
 1100 |          mask[i] = MAXG(mask[i], mask[i+1] - GCONST(3.f));
      |                    ^~~~
F:/circuit/firmware/a04/third_party/opus-1.6.1/celt/fixed_generic.h:101:19: note: in expansion of macro 'GCONST2'
  101 | #define GCONST(x) GCONST2((x),DB_SHIFT)
      |                   ^~~~~~~
F:/circuit/firmware/a04/third_party/opus-1.6.1/celt/celt_encoder.c:1100:46: note: in expansion of macro 'GCONST'
 1100 |          mask[i] = MAXG(mask[i], mask[i+1] - GCONST(3.f));
      |                                              ^~~~~~
F:/circuit/firmware/a04/third_party/opus-1.6.1/celt/fixed_generic.h:98:40: warning: implicit conversion from 'float' to 'double' to match other operand of binary expression [-Wdouble-promotion]
   98 | #define GCONST2(x,bits) ((celt_glog)(.5+(x)*(((celt_glog)1)<<(bits))))
      |                                        ^
F:/circuit/firmware/a04/third_party/opus-1.6.1/celt/arch.h:103:22: note: in definition of macro 'MAX32'
  103 | #define MAX32(a,b) ((a) > (b) ? (a) : (b))   /**< Maximum 32-bit value.   */
      |                      ^
F:/circuit/firmware/a04/third_party/opus-1.6.1/celt/celt_encoder.c:1104:33: note: in expansion of macro 'MAXG'
 1104 |          celt_glog smr = sig[i]-MAXG(MAXG(0, maxDepth-GCONST(12.f)), mask[i]);
      |                                 ^~~~
F:/circuit/firmware/a04/third_party/opus-1.6.1/celt/arch.h:110:19: note: in expansion of macro 'MAX32'
  110 | #define MAXG(a,b) MAX32(a, b)
      |                   ^~~~~
F:/circuit/firmware/a04/third_party/opus-1.6.1/celt/celt_encoder.c:1104:38: note: in expansion of macro 'MAXG'
 1104 |          celt_glog smr = sig[i]-MAXG(MAXG(0, maxDepth-GCONST(12.f)), mask[i]);
      |                                      ^~~~
F:/circuit/firmware/a04/third_party/opus-1.6.1/celt/fixed_generic.h:101:19: note: in expansion of macro 'GCONST2'
  101 | #define GCONST(x) GCONST2((x),DB_SHIFT)
      |                   ^~~~~~~
F:/circuit/firmware/a04/third_party/opus-1.6.1/celt/celt_encoder.c:1104:55: note: in expansion of macro 'GCONST'
 1104 |          celt_glog smr = sig[i]-MAXG(MAXG(0, maxDepth-GCONST(12.f)), mask[i]);
      |                                                       ^~~~~~
F:/circuit/firmware/a04/third_party/opus-1.6.1/celt/fixed_generic.h:98:40: warning: implicit conversion from 'float' to 'double' to match other operand of binary expression [-Wdouble-promotion]
   98 | #define GCONST2(x,bits) ((celt_glog)(.5+(x)*(((celt_glog)1)<<(bits))))
      |                                        ^
F:/circuit/firmware/a04/third_party/opus-1.6.1/celt/arch.h:103:22: note: in definition of macro 'MAX32'
  103 | #define MAX32(a,b) ((a) > (b) ? (a) : (b))   /**< Maximum 32-bit value.   */
      |                      ^
F:/circuit/firmware/a04/third_party/opus-1.6.1/celt/celt_encoder.c:1104:33: note: in expansion of macro 'MAXG'
 1104 |          celt_glog smr = sig[i]-MAXG(MAXG(0, maxDepth-GCONST(12.f)), mask[i]);
      |                                 ^~~~
F:/circuit/firmware/a04/third_party/opus-1.6.1/celt/arch.h:110:19: note: in expansion of macro 'MAX32'
  110 | #define MAXG(a,b) MAX32(a, b)
      |                   ^~~~~
F:/circuit/firmware/a04/third_party/opus-1.6.1/celt/celt_encoder.c:1104:38: note: in expansion of macro 'MAXG'
 1104 |          celt_glog smr = sig[i]-MAXG(MAXG(0, maxDepth-GCONST(12.f)), mask[i]);
      |                                      ^~~~
F:/circuit/firmware/a04/third_party/opus-1.6.1/celt/fixed_generic.h:101:19: note: in expansion of macro 'GCONST2'
  101 | #define GCONST(x) GCONST2((x),DB_SHIFT)
      |                   ^~~~~~~
F:/circuit/firmware/a04/third_party/opus-1.6.1/celt/celt_encoder.c:1104:55: note: in expansion of macro 'GCONST'
 1104 |          celt_glog smr = sig[i]-MAXG(MAXG(0, maxDepth-GCONST(12.f)), mask[i]);
      |                                                       ^~~~~~
F:/circuit/firmware/a04/third_party/opus-1.6.1/celt/fixed_generic.h:98:40: warning: implicit conversion from 'float' to 'double' to match other operand of binary expression [-Wdouble-promotion]
   98 | #define GCONST2(x,bits) ((celt_glog)(.5+(x)*(((celt_glog)1)<<(bits))))
      |                                        ^
F:/circuit/firmware/a04/third_party/opus-1.6.1/celt/arch.h:103:34: note: in definition of macro 'MAX32'
  103 | #define MAX32(a,b) ((a) > (b) ? (a) : (b))   /**< Maximum 32-bit value.   */
      |                                  ^
F:/circuit/firmware/a04/third_party/opus-1.6.1/celt/celt_encoder.c:1104:33: note: in expansion of macro 'MAXG'
 1104 |          celt_glog smr = sig[i]-MAXG(MAXG(0, maxDepth-GCONST(12.f)), mask[i]);
      |                                 ^~~~
F:/circuit/firmware/a04/third_party/opus-1.6.1/celt/arch.h:110:19: note: in expansion of macro 'MAX32'
  110 | #define MAXG(a,b) MAX32(a, b)
      |                   ^~~~~
F:/circuit/firmware/a04/third_party/opus-1.6.1/celt/celt_encoder.c:1104:38: note: in expansion of macro 'MAXG'
 1104 |          celt_glog smr = sig[i]-MAXG(MAXG(0, maxDepth-GCONST(12.f)), mask[i]);
      |                                      ^~~~
F:/circuit/firmware/a04/third_party/opus-1.6.1/celt/fixed_generic.h:101:19: note: in expansion of macro 'GCONST2'
  101 | #define GCONST(x) GCONST2((x),DB_SHIFT)
      |                   ^~~~~~~
F:/circuit/firmware/a04/third_party/opus-1.6.1/celt/celt_encoder.c:1104:55: note: in expansion of macro 'GCONST'
 1104 |          celt_glog smr = sig[i]-MAXG(MAXG(0, maxDepth-GCONST(12.f)), mask[i]);
      |                                                       ^~~~~~
F:/circuit/firmware/a04/third_party/opus-1.6.1/celt/fixed_generic.h:98:40: warning: implicit conversion from 'float' to 'double' to match other operand of binary expression [-Wdouble-promotion]
   98 | #define GCONST2(x,bits) ((celt_glog)(.5+(x)*(((celt_glog)1)<<(bits))))
      |                                        ^
F:/circuit/firmware/a04/third_party/opus-1.6.1/celt/arch.h:103:34: note: in definition of macro 'MAX32'
  103 | #define MAX32(a,b) ((a) > (b) ? (a) : (b))   /**< Maximum 32-bit value.   */
      |                                  ^
F:/circuit/firmware/a04/third_party/opus-1.6.1/celt/celt_encoder.c:1104:33: note: in expansion of macro 'MAXG'
 1104 |          celt_glog smr = sig[i]-MAXG(MAXG(0, maxDepth-GCONST(12.f)), mask[i]);
      |                                 ^~~~
F:/circuit/firmware/a04/third_party/opus-1.6.1/celt/arch.h:110:19: note: in expansion of macro 'MAX32'
  110 | #define MAXG(a,b) MAX32(a, b)
      |                   ^~~~~
F:/circuit/firmware/a04/third_party/opus-1.6.1/celt/celt_encoder.c:1104:38: note: in expansion of macro 'MAXG'
 1104 |          celt_glog smr = sig[i]-MAXG(MAXG(0, maxDepth-GCONST(12.f)), mask[i]);
      |                                      ^~~~
F:/circuit/firmware/a04/third_party/opus-1.6.1/celt/fixed_generic.h:101:19: note: in expansion of macro 'GCONST2'
  101 | #define GCONST(x) GCONST2((x),DB_SHIFT)
      |                   ^~~~~~~
F:/circuit/firmware/a04/third_party/opus-1.6.1/celt/celt_encoder.c:1104:55: note: in expansion of macro 'GCONST'
 1104 |          celt_glog smr = sig[i]-MAXG(MAXG(0, maxDepth-GCONST(12.f)), mask[i]);
      |                                                       ^~~~~~
F:/circuit/firmware/a04/third_party/opus-1.6.1/celt/fixed_generic.h:98:40: warning: implicit conversion from 'float' to 'double' to match other operand of binary expression [-Wdouble-promotion]
   98 | #define GCONST2(x,bits) ((celt_glog)(.5+(x)*(((celt_glog)1)<<(bits))))
      |                                        ^
F:/circuit/firmware/a04/third_party/opus-1.6.1/celt/fixed_generic.h:118:26: note: in definition of macro 'SHR32'
  118 | #define SHR32(a,shift) ((a) >> (shift))
      |                          ^
F:/circuit/firmware/a04/third_party/opus-1.6.1/celt/celt_encoder.c:1108:23: note: in expansion of macro 'PSHR32'
 1108 |          int shift = -PSHR32(MAXG(-GCONST(5.f), MING(0, smr)), DB_SHIFT);
      |                       ^~~~~~
F:/circuit/firmware/a04/third_party/opus-1.6.1/celt/arch.h:110:19: note: in expansion of macro 'MAX32'
  110 | #define MAXG(a,b) MAX32(a, b)
      |                   ^~~~~
F:/circuit/firmware/a04/third_party/opus-1.6.1/celt/celt_encoder.c:1108:30: note: in expansion of macro 'MAXG'
 1108 |          int shift = -PSHR32(MAXG(-GCONST(5.f), MING(0, smr)), DB_SHIFT);
      |                              ^~~~
F:/circuit/firmware/a04/third_party/opus-1.6.1/celt/fixed_generic.h:101:19: note: in expansion of macro 'GCONST2'
  101 | #define GCONST(x) GCONST2((x),DB_SHIFT)
      |                   ^~~~~~~
F:/circuit/firmware/a04/third_party/opus-1.6.1/celt/celt_encoder.c:1108:36: note: in expansion of macro 'GCONST'
 1108 |          int shift = -PSHR32(MAXG(-GCONST(5.f), MING(0, smr)), DB_SHIFT);
      |                                    ^~~~~~
F:/circuit/firmware/a04/third_party/opus-1.6.1/celt/fixed_generic.h:98:40: warning: implicit conversion from 'float' to 'double' to match other operand of binary expression [-Wdouble-promotion]
   98 | #define GCONST2(x,bits) ((celt_glog)(.5+(x)*(((celt_glog)1)<<(bits))))
      |                                        ^
F:/circuit/firmware/a04/third_party/opus-1.6.1/celt/fixed_generic.h:118:26: note: in definition of macro 'SHR32'
  118 | #define SHR32(a,shift) ((a) >> (shift))
      |                          ^
F:/circuit/firmware/a04/third_party/opus-1.6.1/celt/celt_encoder.c:1108:23: note: in expansion of macro 'PSHR32'
 1108 |          int shift = -PSHR32(MAXG(-GCONST(5.f), MING(0, smr)), DB_SHIFT);
      |                       ^~~~~~
F:/circuit/firmware/a04/third_party/opus-1.6.1/celt/arch.h:110:19: note: in expansion of macro 'MAX32'
  110 | #define MAXG(a,b) MAX32(a, b)
      |                   ^~~~~
F:/circuit/firmware/a04/third_party/opus-1.6.1/celt/celt_encoder.c:1108:30: note: in expansion of macro 'MAXG'
 1108 |          int shift = -PSHR32(MAXG(-GCONST(5.f), MING(0, smr)), DB_SHIFT);
      |                              ^~~~
F:/circuit/firmware/a04/third_party/opus-1.6.1/celt/fixed_generic.h:101:19: note: in expansion of macro 'GCONST2'
  101 | #define GCONST(x) GCONST2((x),DB_SHIFT)
      |                   ^~~~~~~
F:/circuit/firmware/a04/third_party/opus-1.6.1/celt/celt_encoder.c:1108:36: note: in expansion of macro 'GCONST'
 1108 |          int shift = -PSHR32(MAXG(-GCONST(5.f), MING(0, smr)), DB_SHIFT);
      |                                    ^~~~~~
F:/circuit/firmware/a04/third_party/opus-1.6.1/celt/fixed_generic.h:98:40: warning: implicit conversion from 'float' to 'double' to match other operand of binary expression [-Wdouble-promotion]
   98 | #define GCONST2(x,bits) ((celt_glog)(.5+(x)*(((celt_glog)1)<<(bits))))
      |                                        ^
F:/circuit/firmware/a04/third_party/opus-1.6.1/celt/fixed_generic.h:101:19: note: in expansion of macro 'GCONST2'
  101 | #define GCONST(x) GCONST2((x),DB_SHIFT)
      |                   ^~~~~~~
F:/circuit/firmware/a04/third_party/opus-1.6.1/celt/celt_encoder.c:1144:47: note: in expansion of macro 'GCONST'
 1144 |             if (bandLogE3[i] > bandLogE3[i-1]+GCONST(.5f))
      |                                               ^~~~~~
F:/circuit/firmware/a04/third_party/opus-1.6.1/celt/fixed_generic.h:98:40: warning: implicit conversion from 'float' to 'double' to match other operand of binary expression [-Wdouble-promotion]
   98 | #define GCONST2(x,bits) ((celt_glog)(.5+(x)*(((celt_glog)1)<<(bits))))
      |                                        ^
F:/circuit/firmware/a04/third_party/opus-1.6.1/celt/arch.h:102:22: note: in definition of macro 'MIN32'
  102 | #define MIN32(a,b) ((a) < (b) ? (a) : (b))   /**< Minimum 32-bit value.   */
      |                      ^
F:/circuit/firmware/a04/third_party/opus-1.6.1/celt/celt_encoder.c:1146:20: note: in expansion of macro 'MING'
 1146 |             f[i] = MING(f[i-1]+GCONST(1.5f), bandLogE3[i]);
      |                    ^~~~
F:/circuit/firmware/a04/third_party/opus-1.6.1/celt/fixed_generic.h:101:19: note: in expansion of macro 'GCONST2'
  101 | #define GCONST(x) GCONST2((x),DB_SHIFT)
      |                   ^~~~~~~
F:/circuit/firmware/a04/third_party/opus-1.6.1/celt/celt_encoder.c:1146:32: note: in expansion of macro 'GCONST'
 1146 |             f[i] = MING(f[i-1]+GCONST(1.5f), bandLogE3[i]);
      |                                ^~~~~~
F:/circuit/firmware/a04/third_party/opus-1.6.1/celt/fixed_generic.h:98:40: warning: implicit conversion from 'float' to 'double' to match other operand of binary expression [-Wdouble-promotion]
   98 | #define GCONST2(x,bits) ((celt_glog)(.5+(x)*(((celt_glog)1)<<(bits))))
      |                                        ^
F:/circuit/firmware/a04/third_party/opus-1.6.1/celt/arch.h:102:34: note: in definition of macro 'MIN32'
  102 | #define MIN32(a,b) ((a) < (b) ? (a) : (b))   /**< Minimum 32-bit value.   */
      |                                  ^
F:/circuit/firmware/a04/third_party/opus-1.6.1/celt/celt_encoder.c:1146:20: note: in expansion of macro 'MING'
 1146 |             f[i] = MING(f[i-1]+GCONST(1.5f), bandLogE3[i]);
      |                    ^~~~
F:/circuit/firmware/a04/third_party/opus-1.6.1/celt/fixed_generic.h:101:19: note: in expansion of macro 'GCONST2'
  101 | #define GCONST(x) GCONST2((x),DB_SHIFT)
      |                   ^~~~~~~
F:/circuit/firmware/a04/third_party/opus-1.6.1/celt/celt_encoder.c:1146:32: note: in expansion of macro 'GCONST'
 1146 |             f[i] = MING(f[i-1]+GCONST(1.5f), bandLogE3[i]);
      |                                ^~~~~~
F:/circuit/firmware/a04/third_party/opus-1.6.1/celt/fixed_generic.h:98:40: warning: implicit conversion from 'float' to 'double' to match other operand of binary expression [-Wdouble-promotion]
   98 | #define GCONST2(x,bits) ((celt_glog)(.5+(x)*(((celt_glog)1)<<(bits))))
      |                                        ^
F:/circuit/firmware/a04/third_party/opus-1.6.1/celt/arch.h:102:28: note: in definition of macro 'MIN32'
  102 | #define MIN32(a,b) ((a) < (b) ? (a) : (b))   /**< Minimum 32-bit value.   */
      |                            ^
F:/circuit/firmware/a04/third_party/opus-1.6.1/celt/celt_encoder.c:1149:20: note: in expansion of macro 'MING'
 1149 |             f[i] = MING(f[i], MING(f[i+1]+GCONST(2.f), bandLogE3[i]));
      |                    ^~~~
F:/circuit/firmware/a04/third_party/opus-1.6.1/celt/arch.h:111:19: note: in expansion of macro 'MIN32'
  111 | #define MING(a,b) MIN32(a, b)
      |                   ^~~~~
F:/circuit/firmware/a04/third_party/opus-1.6.1/celt/celt_encoder.c:1149:31: note: in expansion of macro 'MING'
 1149 |             f[i] = MING(f[i], MING(f[i+1]+GCONST(2.f), bandLogE3[i]));
      |                               ^~~~
F:/circuit/firmware/a04/third_party/opus-1.6.1/celt/fixed_generic.h:101:19: note: in expansion of macro 'GCONST2'
  101 | #define GCONST(x) GCONST2((x),DB_SHIFT)
      |                   ^~~~~~~
F:/circuit/firmware/a04/third_party/opus-1.6.1/celt/celt_encoder.c:1149:43: note: in expansion of macro 'GCONST'
 1149 |             f[i] = MING(f[i], MING(f[i+1]+GCONST(2.f), bandLogE3[i]));
      |                                           ^~~~~~
F:/circuit/firmware/a04/third_party/opus-1.6.1/celt/fixed_generic.h:98:40: warning: implicit conversion from 'float' to 'double' to match other operand of binary expression [-Wdouble-promotion]
   98 | #define GCONST2(x,bits) ((celt_glog)(.5+(x)*(((celt_glog)1)<<(bits))))
      |                                        ^
F:/circuit/firmware/a04/third_party/opus-1.6.1/celt/arch.h:102:28: note: in definition of macro 'MIN32'
  102 | #define MIN32(a,b) ((a) < (b) ? (a) : (b))   /**< Minimum 32-bit value.   */
      |                            ^
F:/circuit/firmware/a04/third_party/opus-1.6.1/celt/celt_encoder.c:1149:20: note: in expansion of macro 'MING'
 1149 |             f[i] = MING(f[i], MING(f[i+1]+GCONST(2.f), bandLogE3[i]));
      |                    ^~~~
F:/circuit/firmware/a04/third_party/opus-1.6.1/celt/arch.h:111:19: note: in expansion of macro 'MIN32'
  111 | #define MING(a,b) MIN32(a, b)
      |                   ^~~~~
F:/circuit/firmware/a04/third_party/opus-1.6.1/celt/celt_encoder.c:1149:31: note: in expansion of macro 'MING'
 1149 |             f[i] = MING(f[i], MING(f[i+1]+GCONST(2.f), bandLogE3[i]));
      |                               ^~~~
F:/circuit/firmware/a04/third_party/opus-1.6.1/celt/fixed_generic.h:101:19: note: in expansion of macro 'GCONST2'
  101 | #define GCONST(x) GCONST2((x),DB_SHIFT)
      |                   ^~~~~~~
F:/circuit/firmware/a04/third_party/opus-1.6.1/celt/celt_encoder.c:1149:43: note: in expansion of macro 'GCONST'
 1149 |             f[i] = MING(f[i], MING(f[i+1]+GCONST(2.f), bandLogE3[i]));
      |                                           ^~~~~~
F:/circuit/firmware/a04/third_party/opus-1.6.1/celt/fixed_generic.h:98:40: warning: implicit conversion from 'float' to 'double' to match other operand of binary expression [-Wdouble-promotion]
   98 | #define GCONST2(x,bits) ((celt_glog)(.5+(x)*(((celt_glog)1)<<(bits))))
      |                                        ^
F:/circuit/firmware/a04/third_party/opus-1.6.1/celt/arch.h:102:40: note: in definition of macro 'MIN32'
  102 | #define MIN32(a,b) ((a) < (b) ? (a) : (b))   /**< Minimum 32-bit value.   */
      |                                        ^
F:/circuit/firmware/a04/third_party/opus-1.6.1/celt/celt_encoder.c:1149:20: note: in expansion of macro 'MING'
 1149 |             f[i] = MING(f[i], MING(f[i+1]+GCONST(2.f), bandLogE3[i]));
      |                    ^~~~
F:/circuit/firmware/a04/third_party/opus-1.6.1/celt/arch.h:111:19: note: in expansion of macro 'MIN32'
  111 | #define MING(a,b) MIN32(a, b)
      |                   ^~~~~
F:/circuit/firmware/a04/third_party/opus-1.6.1/celt/celt_encoder.c:1149:31: note: in expansion of macro 'MING'
 1149 |             f[i] = MING(f[i], MING(f[i+1]+GCONST(2.f), bandLogE3[i]));
      |                               ^~~~
F:/circuit/firmware/a04/third_party/opus-1.6.1/celt/fixed_generic.h:101:19: note: in expansion of macro 'GCONST2'
  101 | #define GCONST(x) GCONST2((x),DB_SHIFT)
      |                   ^~~~~~~
F:/circuit/firmware/a04/third_party/opus-1.6.1/celt/celt_encoder.c:1149:43: note: in expansion of macro 'GCONST'
 1149 |             f[i] = MING(f[i], MING(f[i+1]+GCONST(2.f), bandLogE3[i]));
      |                                           ^~~~~~
F:/circuit/firmware/a04/third_party/opus-1.6.1/celt/fixed_generic.h:98:40: warning: implicit conversion from 'float' to 'double' to match other operand of binary expression [-Wdouble-promotion]
   98 | #define GCONST2(x,bits) ((celt_glog)(.5+(x)*(((celt_glog)1)<<(bits))))
      |                                        ^
F:/circuit/firmware/a04/third_party/opus-1.6.1/celt/arch.h:102:40: note: in definition of macro 'MIN32'
  102 | #define MIN32(a,b) ((a) < (b) ? (a) : (b))   /**< Minimum 32-bit value.   */
      |                                        ^
F:/circuit/firmware/a04/third_party/opus-1.6.1/celt/celt_encoder.c:1149:20: note: in expansion of macro 'MING'
 1149 |             f[i] = MING(f[i], MING(f[i+1]+GCONST(2.f), bandLogE3[i]));
      |                    ^~~~
F:/circuit/firmware/a04/third_party/opus-1.6.1/celt/arch.h:111:19: note: in expansion of macro 'MIN32'
  111 | #define MING(a,b) MIN32(a, b)
      |                   ^~~~~
F:/circuit/firmware/a04/third_party/opus-1.6.1/celt/celt_encoder.c:1149:31: note: in expansion of macro 'MING'
 1149 |             f[i] = MING(f[i], MING(f[i+1]+GCONST(2.f), bandLogE3[i]));
      |                               ^~~~
F:/circuit/firmware/a04/third_party/opus-1.6.1/celt/fixed_generic.h:101:19: note: in expansion of macro 'GCONST2'
  101 | #define GCONST(x) GCONST2((x),DB_SHIFT)
      |                   ^~~~~~~
F:/circuit/firmware/a04/third_party/opus-1.6.1/celt/celt_encoder.c:1149:43: note: in expansion of macro 'GCONST'
 1149 |             f[i] = MING(f[i], MING(f[i+1]+GCONST(2.f), bandLogE3[i]));
      |                                           ^~~~~~
F:/circuit/firmware/a04/third_party/opus-1.6.1/celt/fixed_generic.h:98:40: warning: implicit conversion from 'float' to 'double' to match other operand of binary expression [-Wdouble-promotion]
   98 | #define GCONST2(x,bits) ((celt_glog)(.5+(x)*(((celt_glog)1)<<(bits))))
      |                                        ^
F:/circuit/firmware/a04/third_party/opus-1.6.1/celt/fixed_generic.h:101:19: note: in expansion of macro 'GCONST2'
  101 | #define GCONST(x) GCONST2((x),DB_SHIFT)
      |                   ^~~~~~~
F:/circuit/firmware/a04/third_party/opus-1.6.1/celt/celt_encoder.c:1154:19: note: in expansion of macro 'GCONST'
 1154 |          offset = GCONST(1.f);
      |                   ^~~~~~
F:/circuit/firmware/a04/third_party/opus-1.6.1/celt/fixed_generic.h:98:40: warning: implicit conversion from 'float' to 'double' to match other operand of binary expression [-Wdouble-promotion]
   98 | #define GCONST2(x,bits) ((celt_glog)(.5+(x)*(((celt_glog)1)<<(bits))))
      |                                        ^
F:/circuit/firmware/a04/third_party/opus-1.6.1/celt/arch.h:103:28: note: in definition of macro 'MAX32'
  103 | #define MAX32(a,b) ((a) > (b) ? (a) : (b))   /**< Maximum 32-bit value.   */
      |                            ^
F:/circuit/firmware/a04/third_party/opus-1.6.1/celt/celt_encoder.c:1172:36: note: in expansion of macro 'MAXG'
 1172 |             follower[nbEBands+i] = MAXG(follower[nbEBands+i], follower[         i]-GCONST(4.f));
      |                                    ^~~~
F:/circuit/firmware/a04/third_party/opus-1.6.1/celt/fixed_generic.h:101:19: note: in expansion of macro 'GCONST2'
  101 | #define GCONST(x) GCONST2((x),DB_SHIFT)
      |                   ^~~~~~~
F:/circuit/firmware/a04/third_party/opus-1.6.1/celt/celt_encoder.c:1172:84: note: in expansion of macro 'GCONST'
 1172 |             follower[nbEBands+i] = MAXG(follower[nbEBands+i], follower[         i]-GCONST(4.f));
      |                                                                                    ^~~~~~
F:/circuit/firmware/a04/third_party/opus-1.6.1/celt/fixed_generic.h:98:40: warning: implicit conversion from 'float' to 'double' to match other operand of binary expression [-Wdouble-promotion]
   98 | #define GCONST2(x,bits) ((celt_glog)(.5+(x)*(((celt_glog)1)<<(bits))))
      |                                        ^
F:/circuit/firmware/a04/third_party/opus-1.6.1/celt/arch.h:103:40: note: in definition of macro 'MAX32'
  103 | #define MAX32(a,b) ((a) > (b) ? (a) : (b))   /**< Maximum 32-bit value.   */
      |                                        ^
F:/circuit/firmware/a04/third_party/opus-1.6.1/celt/celt_encoder.c:1172:36: note: in expansion of macro 'MAXG'
 1172 |             follower[nbEBands+i] = MAXG(follower[nbEBands+i], follower[         i]-GCONST(4.f));
      |                                    ^~~~
F:/circuit/firmware/a04/third_party/opus-1.6.1/celt/fixed_generic.h:101:19: note: in expansion of macro 'GCONST2'
  101 | #define GCONST(x) GCONST2((x),DB_SHIFT)
      |                   ^~~~~~~
F:/circuit/firmware/a04/third_party/opus-1.6.1/celt/celt_encoder.c:1172:84: note: in expansion of macro 'GCONST'
 1172 |             follower[nbEBands+i] = MAXG(follower[nbEBands+i], follower[         i]-GCONST(4.f));
      |                                                                                    ^~~~~~
F:/circuit/firmware/a04/third_party/opus-1.6.1/celt/fixed_generic.h:98:40: warning: implicit conversion from 'float' to 'double' to match other operand of binary expression [-Wdouble-promotion]
   98 | #define GCONST2(x,bits) ((celt_glog)(.5+(x)*(((celt_glog)1)<<(bits))))
      |                                        ^
F:/circuit/firmware/a04/third_party/opus-1.6.1/celt/arch.h:103:28: note: in definition of macro 'MAX32'
  103 | #define MAX32(a,b) ((a) > (b) ? (a) : (b))   /**< Maximum 32-bit value.   */
      |                            ^
F:/circuit/firmware/a04/third_party/opus-1.6.1/celt/celt_encoder.c:1173:36: note: in expansion of macro 'MAXG'
 1173 |             follower[         i] = MAXG(follower[         i], follower[nbEBands+i]-GCONST(4.f));
      |                                    ^~~~
F:/circuit/firmware/a04/third_party/opus-1.6.1/celt/fixed_generic.h:101:19: note: in expansion of macro 'GCONST2'
  101 | #define GCONST(x) GCONST2((x),DB_SHIFT)
      |                   ^~~~~~~
F:/circuit/firmware/a04/third_party/opus-1.6.1/celt/celt_encoder.c:1173:84: note: in expansion of macro 'GCONST'
 1173 |             follower[         i] = MAXG(follower[         i], follower[nbEBands+i]-GCONST(4.f));
      |                                                                                    ^~~~~~
F:/circuit/firmware/a04/third_party/opus-1.6.1/celt/fixed_generic.h:98:40: warning: implicit conversion from 'float' to 'double' to match other operand of binary expression [-Wdouble-promotion]
   98 | #define GCONST2(x,bits) ((celt_glog)(.5+(x)*(((celt_glog)1)<<(bits))))
      |                                        ^
F:/circuit/firmware/a04/third_party/opus-1.6.1/celt/arch.h:103:40: note: in definition of macro 'MAX32'
  103 | #define MAX32(a,b) ((a) > (b) ? (a) : (b))   /**< Maximum 32-bit value.   */
      |                                        ^
F:/circuit/firmware/a04/third_party/opus-1.6.1/celt/celt_encoder.c:1173:36: note: in expansion of macro 'MAXG'
 1173 |             follower[         i] = MAXG(follower[         i], follower[nbEBands+i]-GCONST(4.f));
      |                                    ^~~~
F:/circuit/firmware/a04/third_party/opus-1.6.1/celt/fixed_generic.h:101:19: note: in expansion of macro 'GCONST2'
  101 | #define GCONST(x) GCONST2((x),DB_SHIFT)
      |                   ^~~~~~~
F:/circuit/firmware/a04/third_party/opus-1.6.1/celt/celt_encoder.c:1173:84: note: in expansion of macro 'GCONST'
 1173 |             follower[         i] = MAXG(follower[         i], follower[nbEBands+i]-GCONST(4.f));
      |                                                                                    ^~~~~~
F:/circuit/firmware/a04/third_party/opus-1.6.1/celt/fixed_generic.h:98:40: warning: implicit conversion from 'float' to 'double' to match other operand of binary expression [-Wdouble-promotion]
   98 | #define GCONST2(x,bits) ((celt_glog)(.5+(x)*(((celt_glog)1)<<(bits))))
      |                                        ^
F:/circuit/firmware/a04/third_party/opus-1.6.1/celt/fixed_generic.h:118:26: note: in definition of macro 'SHR32'
  118 | #define SHR32(a,shift) ((a) >> (shift))
      |                          ^
F:/circuit/firmware/a04/third_party/opus-1.6.1/celt/celt_encoder.c:1187:26: note: in expansion of macro 'PSHR32'
 1187 |          importance[i] = PSHR32(13*celt_exp2_db(MING(follower[i], GCONST(4.f))), 16);
      |                          ^~~~~~
F:/circuit/firmware/a04/third_party/opus-1.6.1/celt/fixed_generic.h:123:26: note: in expansion of macro 'SHR32'
  123 | #define PSHR32(a,shift) (SHR32((a)+((EXTEND32(1)<<((shift))>>1)),shift))
      |                          ^~~~~
F:/circuit/firmware/a04/third_party/opus-1.6.1/celt/mathops.h:531:35: note: in expansion of macro 'PSHR32'
  531 | #define celt_exp2_db(x) celt_exp2(PSHR32(x, DB_SHIFT-10))
      |                                   ^~~~~~
F:/circuit/firmware/a04/third_party/opus-1.6.1/celt/celt_encoder.c:1187:36: note: in expansion of macro 'celt_exp2_db'
 1187 |          importance[i] = PSHR32(13*celt_exp2_db(MING(follower[i], GCONST(4.f))), 16);
      |                                    ^~~~~~~~~~~~
F:/circuit/firmware/a04/third_party/opus-1.6.1/celt/arch.h:111:19: note: in expansion of macro 'MIN32'
  111 | #define MING(a,b) MIN32(a, b)
      |                   ^~~~~
F:/circuit/firmware/a04/third_party/opus-1.6.1/celt/celt_encoder.c:1187:49: note: in expansion of macro 'MING'
 1187 |          importance[i] = PSHR32(13*celt_exp2_db(MING(follower[i], GCONST(4.f))), 16);
      |                                                 ^~~~
F:/circuit/firmware/a04/third_party/opus-1.6.1/celt/fixed_generic.h:101:19: note: in expansion of macro 'GCONST2'
  101 | #define GCONST(x) GCONST2((x),DB_SHIFT)
      |                   ^~~~~~~
F:/circuit/firmware/a04/third_party/opus-1.6.1/celt/celt_encoder.c:1187:67: note: in expansion of macro 'GCONST'
 1187 |          importance[i] = PSHR32(13*celt_exp2_db(MING(follower[i], GCONST(4.f))), 16);
      |                                                                   ^~~~~~
F:/circuit/firmware/a04/third_party/opus-1.6.1/celt/fixed_generic.h:98:40: warning: implicit conversion from 'float' to 'double' to match other operand of binary expression [-Wdouble-promotion]
   98 | #define GCONST2(x,bits) ((celt_glog)(.5+(x)*(((celt_glog)1)<<(bits))))
      |                                        ^
F:/circuit/firmware/a04/third_party/opus-1.6.1/celt/fixed_generic.h:118:26: note: in definition of macro 'SHR32'
  118 | #define SHR32(a,shift) ((a) >> (shift))
      |                          ^
F:/circuit/firmware/a04/third_party/opus-1.6.1/celt/celt_encoder.c:1187:26: note: in expansion of macro 'PSHR32'
 1187 |          importance[i] = PSHR32(13*celt_exp2_db(MING(follower[i], GCONST(4.f))), 16);
      |                          ^~~~~~
F:/circuit/firmware/a04/third_party/opus-1.6.1/celt/fixed_generic.h:123:26: note: in expansion of macro 'SHR32'
  123 | #define PSHR32(a,shift) (SHR32((a)+((EXTEND32(1)<<((shift))>>1)),shift))
      |                          ^~~~~
F:/circuit/firmware/a04/third_party/opus-1.6.1/celt/mathops.h:531:35: note: in expansion of macro 'PSHR32'
  531 | #define celt_exp2_db(x) celt_exp2(PSHR32(x, DB_SHIFT-10))
      |                                   ^~~~~~
F:/circuit/firmware/a04/third_party/opus-1.6.1/celt/celt_encoder.c:1187:36: note: in expansion of macro 'celt_exp2_db'
 1187 |          importance[i] = PSHR32(13*celt_exp2_db(MING(follower[i], GCONST(4.f))), 16);
      |                                    ^~~~~~~~~~~~
F:/circuit/firmware/a04/third_party/opus-1.6.1/celt/arch.h:111:19: note: in expansion of macro 'MIN32'
  111 | #define MING(a,b) MIN32(a, b)
      |                   ^~~~~
F:/circuit/firmware/a04/third_party/opus-1.6.1/celt/celt_encoder.c:1187:49: note: in expansion of macro 'MING'
 1187 |          importance[i] = PSHR32(13*celt_exp2_db(MING(follower[i], GCONST(4.f))), 16);
      |                                                 ^~~~
F:/circuit/firmware/a04/third_party/opus-1.6.1/celt/fixed_generic.h:101:19: note: in expansion of macro 'GCONST2'
  101 | #define GCONST(x) GCONST2((x),DB_SHIFT)
      |                   ^~~~~~~
F:/circuit/firmware/a04/third_party/opus-1.6.1/celt/celt_encoder.c:1187:67: note: in expansion of macro 'GCONST'
 1187 |          importance[i] = PSHR32(13*celt_exp2_db(MING(follower[i], GCONST(4.f))), 16);
      |                                                                   ^~~~~~
F:/circuit/firmware/a04/third_party/opus-1.6.1/celt/fixed_generic.h:95:42: warning: implicit conversion from 'float' to 'double' to match other operand of binary expression [-Wdouble-promotion]
   95 | #define QCONST32(x,bits) ((opus_val32)(.5+(x)*(((opus_int64)1)<<(bits))))
      |                                          ^
F:/circuit/firmware/a04/third_party/opus-1.6.1/celt/celt_encoder.c:1206:25: note: in expansion of macro 'QCONST32'
 1206 |       if (toneishness > QCONST32(.98f, 29)) {
      |                         ^~~~~~~~
F:/circuit/firmware/a04/third_party/opus-1.6.1/celt/fixed_generic.h:98:40: warning: implicit conversion from 'float' to 'double' to match other operand of binary expression [-Wdouble-promotion]
   98 | #define GCONST2(x,bits) ((celt_glog)(.5+(x)*(((celt_glog)1)<<(bits))))
      |                                        ^
F:/circuit/firmware/a04/third_party/opus-1.6.1/celt/fixed_generic.h:101:19: note: in expansion of macro 'GCONST2'
  101 | #define GCONST(x) GCONST2((x),DB_SHIFT)
      |                   ^~~~~~~
F:/circuit/firmware/a04/third_party/opus-1.6.1/celt/celt_encoder.c:1213:82: note: in expansion of macro 'GCONST'
 1213 |             if (freq_bin >= eBands[i] && freq_bin <= eBands[i+1]) follower[i] += GCONST(2.f);
      |                                                                                  ^~~~~~
F:/circuit/firmware/a04/third_party/opus-1.6.1/celt/fixed_generic.h:98:40: warning: implicit conversion from 'float' to 'double' to match other operand of binary expression [-Wdouble-promotion]
   98 | #define GCONST2(x,bits) ((celt_glog)(.5+(x)*(((celt_glog)1)<<(bits))))
      |                                        ^
F:/circuit/firmware/a04/third_party/opus-1.6.1/celt/fixed_generic.h:101:19: note: in expansion of macro 'GCONST2'
  101 | #define GCONST(x) GCONST2((x),DB_SHIFT)
      |                   ^~~~~~~
F:/circuit/firmware/a04/third_party/opus-1.6.1/celt/celt_encoder.c:1214:86: note: in expansion of macro 'GCONST'
 1214 |             if (freq_bin >= eBands[i]-1 && freq_bin <= eBands[i+1]+1) follower[i] += GCONST(1.f);
      |                                                                                      ^~~~~~
F:/circuit/firmware/a04/third_party/opus-1.6.1/celt/fixed_generic.h:98:40: warning: implicit conversion from 'float' to 'double' to match other operand of binary expression [-Wdouble-promotion]
   98 | #define GCONST2(x,bits) ((celt_glog)(.5+(x)*(((celt_glog)1)<<(bits))))
      |                                        ^
F:/circuit/firmware/a04/third_party/opus-1.6.1/celt/fixed_generic.h:101:19: note: in expansion of macro 'GCONST2'
  101 | #define GCONST(x) GCONST2((x),DB_SHIFT)
      |                   ^~~~~~~
F:/circuit/firmware/a04/third_party/opus-1.6.1/celt/celt_encoder.c:1215:86: note: in expansion of macro 'GCONST'
 1215 |             if (freq_bin >= eBands[i]-2 && freq_bin <= eBands[i+1]+2) follower[i] += GCONST(1.f);
      |                                                                                      ^~~~~~
F:/circuit/firmware/a04/third_party/opus-1.6.1/celt/fixed_generic.h:98:40: warning: implicit conversion from 'float' to 'double' to match other operand of binary expression [-Wdouble-promotion]
   98 | #define GCONST2(x,bits) ((celt_glog)(.5+(x)*(((celt_glog)1)<<(bits))))
      |                                        ^
F:/circuit/firmware/a04/third_party/opus-1.6.1/celt/fixed_generic.h:101:19: note: in expansion of macro 'GCONST2'
  101 | #define GCONST(x) GCONST2((x),DB_SHIFT)
      |                   ^~~~~~~
F:/circuit/firmware/a04/third_party/opus-1.6.1/celt/celt_encoder.c:1216:86: note: in expansion of macro 'GCONST'
 1216 |             if (freq_bin >= eBands[i]-3 && freq_bin <= eBands[i+1]+3) follower[i] += GCONST(.5f);
      |                                                                                      ^~~~~~
F:/circuit/firmware/a04/third_party/opus-1.6.1/celt/fixed_generic.h:98:40: warning: implicit conversion from 'float' to 'double' to match other operand of binary expression [-Wdouble-promotion]
   98 | #define GCONST2(x,bits) ((celt_glog)(.5+(x)*(((celt_glog)1)<<(bits))))
      |                                        ^
F:/circuit/firmware/a04/third_party/opus-1.6.1/celt/fixed_generic.h:101:19: note: in expansion of macro 'GCONST2'
  101 | #define GCONST(x) GCONST2((x),DB_SHIFT)
      |                   ^~~~~~~
F:/circuit/firmware/a04/third_party/opus-1.6.1/celt/celt_encoder.c:1219:32: note: in expansion of macro 'GCONST'
 1219 |             follower[end-1] += GCONST(2.f);
      |                                ^~~~~~
F:/circuit/firmware/a04/third_party/opus-1.6.1/celt/fixed_generic.h:98:40: warning: implicit conversion from 'float' to 'double' to match other operand of binary expression [-Wdouble-promotion]
   98 | #define GCONST2(x,bits) ((celt_glog)(.5+(x)*(((celt_glog)1)<<(bits))))
      |                                        ^
F:/circuit/firmware/a04/third_party/opus-1.6.1/celt/fixed_generic.h:101:19: note: in expansion of macro 'GCONST2'
  101 | #define GCONST(x) GCONST2((x),DB_SHIFT)
      |                   ^~~~~~~
F:/circuit/firmware/a04/third_party/opus-1.6.1/celt/celt_encoder.c:1220:32: note: in expansion of macro 'GCONST'
 1220 |             follower[end-2] += GCONST(1.f);
      |                                ^~~~~~
F:/circuit/firmware/a04/third_party/opus-1.6.1/celt/celt_encoder.c: In function 'tone_lpc':
F:/circuit/firmware/a04/third_party/opus-1.6.1/celt/fixed_generic.h:95:42: warning: implicit conversion from 'float' to 'double' to match other operand of binary expression [-Wdouble-promotion]
   95 | #define QCONST32(x,bits) ((opus_val32)(.5+(x)*(((opus_int64)1)<<(bits))))
      |                                          ^
F:/circuit/firmware/a04/third_party/opus-1.6.1/celt/celt_encoder.c:1350:30: note: in expansion of macro 'QCONST32'
 1350 |    if (num1 >= den) lpc[1] = QCONST32(1.f, 29);
      |                              ^~~~~~~~
F:/circuit/firmware/a04/third_party/opus-1.6.1/celt/fixed_generic.h:95:42: warning: implicit conversion from 'float' to 'double' to match other operand of binary expression [-Wdouble-promotion]
   95 | #define QCONST32(x,bits) ((opus_val32)(.5+(x)*(((opus_int64)1)<<(bits))))
      |                                          ^
F:/circuit/firmware/a04/third_party/opus-1.6.1/celt/celt_encoder.c:1351:37: note: in expansion of macro 'QCONST32'
 1351 |    else if (num1 <= -den) lpc[1] = -QCONST32(1.f, 29);
      |                                     ^~~~~~~~
F:/circuit/firmware/a04/third_party/opus-1.6.1/celt/fixed_generic.h:95:42: warning: implicit conversion from 'float' to 'double' to match other operand of binary expression [-Wdouble-promotion]
   95 | #define QCONST32(x,bits) ((opus_val32)(.5+(x)*(((opus_int64)1)<<(bits))))
      |                                          ^
F:/circuit/firmware/a04/third_party/opus-1.6.1/celt/celt_encoder.c:1354:38: note: in expansion of macro 'QCONST32'
 1354 |    if (HALF32(num0) >= den) lpc[0] = QCONST32(1.999999f, 29);
      |                                      ^~~~~~~~
F:/circuit/firmware/a04/third_party/opus-1.6.1/celt/fixed_generic.h:95:42: warning: implicit conversion from 'float' to 'double' to match other operand of binary expression [-Wdouble-promotion]
   95 | #define QCONST32(x,bits) ((opus_val32)(.5+(x)*(((opus_int64)1)<<(bits))))
      |                                          ^
F:/circuit/firmware/a04/third_party/opus-1.6.1/celt/celt_encoder.c:1355:45: note: in expansion of macro 'QCONST32'
 1355 |    else if (HALF32(num0) <= -den) lpc[0] = -QCONST32(1.999999f, 29);
      |                                             ^~~~~~~~
F:/circuit/firmware/a04/third_party/opus-1.6.1/celt/celt_encoder.c: In function 'tone_detect':
F:/circuit/firmware/a04/third_party/opus-1.6.1/celt/fixed_generic.h:95:42: warning: implicit conversion from 'float' to 'double' to match other operand of binary expression [-Wdouble-promotion]
   95 | #define QCONST32(x,bits) ((opus_val32)(.5+(x)*(((opus_int64)1)<<(bits))))
      |                                          ^
F:/circuit/firmware/a04/third_party/opus-1.6.1/celt/celt_encoder.c:1382:50: note: in expansion of macro 'QCONST32'
 1382 |    while (delay <= Fs/3000 && (fail || (lpc[0] > QCONST32(1.f, 29) && lpc[1] < 0))) {
      |                                                  ^~~~~~~~
F:/circuit/firmware/a04/third_party/opus-1.6.1/celt/celt_encoder.c: In function 'run_prefilter':
F:/circuit/firmware/a04/third_party/opus-1.6.1/celt/fixed_generic.h:95:42: warning: implicit conversion from 'float' to 'double' to match other operand of binary expression [-Wdouble-promotion]
   95 | #define QCONST32(x,bits) ((opus_val32)(.5+(x)*(((opus_int64)1)<<(bits))))
      |                                          ^
F:/circuit/firmware/a04/third_party/opus-1.6.1/celt/celt_encoder.c:1440:33: note: in expansion of macro 'QCONST32'
 1440 |    if (enabled && toneishness > QCONST32(.99f, 29)) {
      |                                 ^~~~~~~~
F:/circuit/firmware/a04/third_party/opus-1.6.1/celt/fixed_generic.h:92:42: warning: implicit conversion from 'float' to 'double' to match other operand of binary expression [-Wdouble-promotion]
   92 | #define QCONST16(x,bits) ((opus_val16)(.5+(x)*(((opus_val32)1)<<(bits))))
      |                                          ^
F:/circuit/firmware/a04/third_party/opus-1.6.1/celt/celt_encoder.c:1444:36: note: in expansion of macro 'QCONST16'
 1444 |       if (QEXT_SCALE(tone_freq) >= QCONST16(3.1416f, 13)) tone_freq = QCONST16(3.141593f, 13) - tone_freq;
      |                                    ^~~~~~~~
F:/circuit/firmware/a04/third_party/opus-1.6.1/celt/fixed_generic.h:92:42: warning: implicit conversion from 'float' to 'double' to match other operand of binary expression [-Wdouble-promotion]
   92 | #define QCONST16(x,bits) ((opus_val16)(.5+(x)*(((opus_val32)1)<<(bits))))
      |                                          ^
F:/circuit/firmware/a04/third_party/opus-1.6.1/celt/celt_encoder.c:1444:71: note: in expansion of macro 'QCONST16'
 1444 |       if (QEXT_SCALE(tone_freq) >= QCONST16(3.1416f, 13)) tone_freq = QCONST16(3.141593f, 13) - tone_freq;
      |                                                                       ^~~~~~~~
F:/circuit/firmware/a04/third_party/opus-1.6.1/celt/fixed_generic.h:92:42: warning: implicit conversion from 'float' to 'double' to match other operand of binary expression [-Wdouble-promotion]
   92 | #define QCONST16(x,bits) ((opus_val16)(.5+(x)*(((opus_val32)1)<<(bits))))
      |                                          ^
F:/circuit/firmware/a04/third_party/opus-1.6.1/celt/celt_encoder.c:1447:48: note: in expansion of macro 'QCONST16'
 1447 |       while (QEXT_SCALE(tone_freq) >= multiple*QCONST16(0.39f, 13)) multiple++;
      |                                                ^~~~~~~~
F:/circuit/firmware/a04/third_party/opus-1.6.1/celt/fixed_generic.h:92:42: warning: implicit conversion from 'float' to 'double' to match other operand of binary expression [-Wdouble-promotion]
   92 | #define QCONST16(x,bits) ((opus_val16)(.5+(x)*(((opus_val32)1)<<(bits))))
      |                                          ^
F:/circuit/firmware/a04/third_party/opus-1.6.1/celt/celt_encoder.c:1448:35: note: in expansion of macro 'QCONST16'
 1448 |       if (QEXT_SCALE(tone_freq) > QCONST16(0.006148f, 13)) {
      |                                   ^~~~~~~~
F:/circuit/firmware/a04/third_party/opus-1.6.1/celt/fixed_generic.h:92:42: warning: implicit conversion from 'float' to 'double' to match other operand of binary expression [-Wdouble-promotion]
   92 | #define QCONST16(x,bits) ((opus_val16)(.5+(x)*(((opus_val32)1)<<(bits))))
      |                                          ^
F:/circuit/firmware/a04/third_party/opus-1.6.1/celt/celt_encoder.c:1460:15: note: in expansion of macro 'QCONST16'
 1460 |       gain1 = QCONST16(.75f, 15);
      |               ^~~~~~~~
F:/circuit/firmware/a04/third_party/opus-1.6.1/celt/fixed_generic.h:92:42: warning: implicit conversion from 'float' to 'double' to match other operand of binary expression [-Wdouble-promotion]
   92 | #define QCONST16(x,bits) ((opus_val16)(.5+(x)*(((opus_val32)1)<<(bits))))
      |                                          ^
F:/circuit/firmware/a04/third_party/opus-1.6.1/celt/fixed_generic.h:131:24: note: in definition of macro 'SHR'
  131 | #define SHR(a,shift) ((a) >> (shift))
      |                        ^
F:/circuit/firmware/a04/third_party/opus-1.6.1/celt/fixed_generic.h:193:33: note: in expansion of macro 'MULT16_16'
  193 | #define MULT16_16_Q15(a,b) (SHR(MULT16_16((a),(b)),15))
      |                                 ^~~~~~~~~
F:/circuit/firmware/a04/third_party/opus-1.6.1/celt/celt_encoder.c:1480:15: note: in expansion of macro 'MULT16_16_Q15'
 1480 |       gain1 = MULT16_16_Q15(QCONST16(.7f,15),gain1);
      |               ^~~~~~~~~~~~~
F:/circuit/firmware/a04/third_party/opus-1.6.1/celt/celt_encoder.c:1480:29: note: in expansion of macro 'QCONST16'
 1480 |       gain1 = MULT16_16_Q15(QCONST16(.7f,15),gain1);
      |                             ^~~~~~~~
F:/circuit/firmware/a04/third_party/opus-1.6.1/celt/fixed_generic.h:92:42: warning: implicit conversion from 'float' to 'double' to match other operand of binary expression [-Wdouble-promotion]
   92 | #define QCONST16(x,bits) ((opus_val16)(.5+(x)*(((opus_val32)1)<<(bits))))
      |                                          ^
F:/circuit/firmware/a04/third_party/opus-1.6.1/celt/celt_encoder.c:1499:19: note: in expansion of macro 'QCONST16'
 1499 |    pf_threshold = QCONST16(.2f,15);
      |                   ^~~~~~~~
F:/circuit/firmware/a04/third_party/opus-1.6.1/celt/fixed_generic.h:92:42: warning: implicit conversion from 'float' to 'double' to match other operand of binary expression [-Wdouble-promotion]
   92 | #define QCONST16(x,bits) ((opus_val16)(.5+(x)*(((opus_val32)1)<<(bits))))
      |                                          ^
F:/circuit/firmware/a04/third_party/opus-1.6.1/celt/celt_encoder.c:1504:23: note: in expansion of macro 'QCONST16'
 1504 |       pf_threshold += QCONST16(.2f,15);
      |                       ^~~~~~~~
F:/circuit/firmware/a04/third_party/opus-1.6.1/celt/fixed_generic.h:92:42: warning: implicit conversion from 'float' to 'double' to match other operand of binary expression [-Wdouble-promotion]
   92 | #define QCONST16(x,bits) ((opus_val16)(.5+(x)*(((opus_val32)1)<<(bits))))
      |                                          ^
F:/circuit/firmware/a04/third_party/opus-1.6.1/celt/celt_encoder.c:1506:25: note: in expansion of macro 'QCONST16'
 1506 |       if (tf_estimate > QCONST16(.98f, 14))
      |                         ^~~~~~~~
F:/circuit/firmware/a04/third_party/opus-1.6.1/celt/fixed_generic.h:92:42: warning: implicit conversion from 'float' to 'double' to match other operand of binary expression [-Wdouble-promotion]
   92 | #define QCONST16(x,bits) ((opus_val16)(.5+(x)*(((opus_val32)1)<<(bits))))
      |                                          ^
F:/circuit/firmware/a04/third_party/opus-1.6.1/celt/celt_encoder.c:1510:23: note: in expansion of macro 'QCONST16'
 1510 |       pf_threshold += QCONST16(.1f,15);
      |                       ^~~~~~~~
F:/circuit/firmware/a04/third_party/opus-1.6.1/celt/fixed_generic.h:92:42: warning: implicit conversion from 'float' to 'double' to match other operand of binary expression [-Wdouble-promotion]
   92 | #define QCONST16(x,bits) ((opus_val16)(.5+(x)*(((opus_val32)1)<<(bits))))
      |                                          ^
F:/circuit/firmware/a04/third_party/opus-1.6.1/celt/celt_encoder.c:1512:23: note: in expansion of macro 'QCONST16'
 1512 |       pf_threshold += QCONST16(.1f,15);
      |                       ^~~~~~~~
F:/circuit/firmware/a04/third_party/opus-1.6.1/celt/fixed_generic.h:92:42: warning: implicit conversion from 'float' to 'double' to match other operand of binary expression [-Wdouble-promotion]
   92 | #define QCONST16(x,bits) ((opus_val16)(.5+(x)*(((opus_val32)1)<<(bits))))
      |                                          ^
F:/circuit/firmware/a04/third_party/opus-1.6.1/celt/celt_encoder.c:1513:29: note: in expansion of macro 'QCONST16'
 1513 |    if (st->prefilter_gain > QCONST16(.4f,15))
      |                             ^~~~~~~~
F:/circuit/firmware/a04/third_party/opus-1.6.1/celt/fixed_generic.h:92:42: warning: implicit conversion from 'float' to 'double' to match other operand of binary expression [-Wdouble-promotion]
   92 | #define QCONST16(x,bits) ((opus_val16)(.5+(x)*(((opus_val32)1)<<(bits))))
      |                                          ^
F:/circuit/firmware/a04/third_party/opus-1.6.1/celt/celt_encoder.c:1514:23: note: in expansion of macro 'QCONST16'
 1514 |       pf_threshold -= QCONST16(.1f,15);
      |                       ^~~~~~~~
F:/circuit/firmware/a04/third_party/opus-1.6.1/celt/fixed_generic.h:92:42: warning: implicit conversion from 'float' to 'double' to match other operand of binary expression [-Wdouble-promotion]
   92 | #define QCONST16(x,bits) ((opus_val16)(.5+(x)*(((opus_val32)1)<<(bits))))
      |                                          ^
F:/circuit/firmware/a04/third_party/opus-1.6.1/celt/celt_encoder.c:1515:29: note: in expansion of macro 'QCONST16'
 1515 |    if (st->prefilter_gain > QCONST16(.55f,15))
      |                             ^~~~~~~~
F:/circuit/firmware/a04/third_party/opus-1.6.1/celt/fixed_generic.h:92:42: warning: implicit conversion from 'float' to 'double' to match other operand of binary expression [-Wdouble-promotion]
   92 | #define QCONST16(x,bits) ((opus_val16)(.5+(x)*(((opus_val32)1)<<(bits))))
      |                                          ^
F:/circuit/firmware/a04/third_party/opus-1.6.1/celt/celt_encoder.c:1516:23: note: in expansion of macro 'QCONST16'
 1516 |       pf_threshold -= QCONST16(.1f,15);
      |                       ^~~~~~~~
F:/circuit/firmware/a04/third_party/opus-1.6.1/celt/fixed_generic.h:92:42: warning: implicit conversion from 'float' to 'double' to match other operand of binary expression [-Wdouble-promotion]
   92 | #define QCONST16(x,bits) ((opus_val16)(.5+(x)*(((opus_val32)1)<<(bits))))
      |                                          ^
F:/circuit/firmware/a04/third_party/opus-1.6.1/celt/arch.h:101:28: note: in definition of macro 'MAX16'
  101 | #define MAX16(a,b) ((a) > (b) ? (a) : (b))   /**< Maximum 16-bit value.   */
      |                            ^
F:/circuit/firmware/a04/third_party/opus-1.6.1/celt/celt_encoder.c:1519:39: note: in expansion of macro 'QCONST16'
 1519 |    pf_threshold = MAX16(pf_threshold, QCONST16(.2f,15));
      |                                       ^~~~~~~~
F:/circuit/firmware/a04/third_party/opus-1.6.1/celt/fixed_generic.h:92:42: warning: implicit conversion from 'float' to 'double' to match other operand of binary expression [-Wdouble-promotion]
   92 | #define QCONST16(x,bits) ((opus_val16)(.5+(x)*(((opus_val32)1)<<(bits))))
      |                                          ^
F:/circuit/firmware/a04/third_party/opus-1.6.1/celt/arch.h:101:40: note: in definition of macro 'MAX16'
  101 | #define MAX16(a,b) ((a) > (b) ? (a) : (b))   /**< Maximum 16-bit value.   */
      |                                        ^
F:/circuit/firmware/a04/third_party/opus-1.6.1/celt/celt_encoder.c:1519:39: note: in expansion of macro 'QCONST16'
 1519 |    pf_threshold = MAX16(pf_threshold, QCONST16(.2f,15));
      |                                       ^~~~~~~~
F:/circuit/firmware/a04/third_party/opus-1.6.1/celt/fixed_generic.h:92:42: warning: implicit conversion from 'float' to 'double' to match other operand of binary expression [-Wdouble-promotion]
   92 | #define QCONST16(x,bits) ((opus_val16)(.5+(x)*(((opus_val32)1)<<(bits))))
      |                                          ^
F:/circuit/firmware/a04/third_party/opus-1.6.1/celt/celt_encoder.c:1528:43: note: in expansion of macro 'QCONST16'
 1528 |       if (ABS16(gain1-st->prefilter_gain)<QCONST16(.1f,15))
      |                                           ^~~~~~~~
F:/circuit/firmware/a04/third_party/opus-1.6.1/celt/fixed_generic.h:92:42: warning: implicit conversion from 'float' to 'double' to match other operand of binary expression [-Wdouble-promotion]
   92 | #define QCONST16(x,bits) ((opus_val16)(.5+(x)*(((opus_val32)1)<<(bits))))
      |                                          ^
F:/circuit/firmware/a04/third_party/opus-1.6.1/celt/celt_encoder.c:1537:15: note: in expansion of macro 'QCONST16'
 1537 |       gain1 = QCONST16(0.09375f,15)*(qg+1);
      |               ^~~~~~~~
F:/circuit/firmware/a04/third_party/opus-1.6.1/celt/fixed_generic.h:92:42: warning: implicit conversion from 'float' to 'double' to match other operand of binary expression [-Wdouble-promotion]
   92 | #define QCONST16(x,bits) ((opus_val16)(.5+(x)*(((opus_val32)1)<<(bits))))
      |                                          ^
F:/circuit/firmware/a04/third_party/opus-1.6.1/celt/fixed_generic.h:152:34: note: in definition of macro 'ADD32'
  152 | #define ADD32(a,b) ((opus_val32)(a)+(opus_val32)(b))
      |                                  ^
F:/circuit/firmware/a04/third_party/opus-1.6.1/celt/fixed_generic.h:132:22: note: in expansion of macro 'SHL32'
  132 | #define SHL(a,shift) SHL32(a,shift)
      |                      ^~~~~
F:/circuit/firmware/a04/third_party/opus-1.6.1/celt/fixed_generic.h:57:34: note: in expansion of macro 'SHL'
   57 | #define MULT16_32_Q15(a,b) ADD32(SHL(MULT16_16((a),SHR((b),16)),1), SHR(MULT16_16SU((a),((b)&0x0000ffff)),15))
      |                                  ^~~
F:/circuit/firmware/a04/third_party/opus-1.6.1/celt/fixed_generic.h:57:38: note: in expansion of macro 'MULT16_16'
   57 | #define MULT16_32_Q15(a,b) ADD32(SHL(MULT16_16((a),SHR((b),16)),1), SHR(MULT16_16SU((a),((b)&0x0000ffff)),15))
      |                                      ^~~~~~~~~
F:/circuit/firmware/a04/third_party/opus-1.6.1/celt/celt_encoder.c:1561:19: note: in expansion of macro 'MULT16_32_Q15'
 1561 |       thresh[0] = MULT16_32_Q15(MULT16_16_Q15(QCONST16(.25f, 15), gain1), before[0]) + MULT16_32_Q15(QCONST16(.01f,15), before[1]);
      |                   ^~~~~~~~~~~~~
F:/circuit/firmware/a04/third_party/opus-1.6.1/celt/fixed_generic.h:193:29: note: in expansion of macro 'SHR'
  193 | #define MULT16_16_Q15(a,b) (SHR(MULT16_16((a),(b)),15))
      |                             ^~~
F:/circuit/firmware/a04/third_party/opus-1.6.1/celt/fixed_generic.h:193:33: note: in expansion of macro 'MULT16_16'
  193 | #define MULT16_16_Q15(a,b) (SHR(MULT16_16((a),(b)),15))
      |                                 ^~~~~~~~~
F:/circuit/firmware/a04/third_party/opus-1.6.1/celt/celt_encoder.c:1561:33: note: in expansion of macro 'MULT16_16_Q15'
 1561 |       thresh[0] = MULT16_32_Q15(MULT16_16_Q15(QCONST16(.25f, 15), gain1), before[0]) + MULT16_32_Q15(QCONST16(.01f,15), before[1]);
      |                                 ^~~~~~~~~~~~~
F:/circuit/firmware/a04/third_party/opus-1.6.1/celt/celt_encoder.c:1561:47: note: in expansion of macro 'QCONST16'
 1561 |       thresh[0] = MULT16_32_Q15(MULT16_16_Q15(QCONST16(.25f, 15), gain1), before[0]) + MULT16_32_Q15(QCONST16(.01f,15), before[1]);
      |                                               ^~~~~~~~
F:/circuit/firmware/a04/third_party/opus-1.6.1/celt/fixed_generic.h:92:42: warning: implicit conversion from 'float' to 'double' to match other operand of binary expression [-Wdouble-promotion]
   92 | #define QCONST16(x,bits) ((opus_val16)(.5+(x)*(((opus_val32)1)<<(bits))))
      |                                          ^
F:/circuit/firmware/a04/third_party/opus-1.6.1/celt/fixed_generic.h:152:50: note: in definition of macro 'ADD32'
  152 | #define ADD32(a,b) ((opus_val32)(a)+(opus_val32)(b))
      |                                                  ^
F:/circuit/firmware/a04/third_party/opus-1.6.1/celt/fixed_generic.h:57:69: note: in expansion of macro 'SHR'
   57 | #define MULT16_32_Q15(a,b) ADD32(SHL(MULT16_16((a),SHR((b),16)),1), SHR(MULT16_16SU((a),((b)&0x0000ffff)),15))
      |                                                                     ^~~
F:/circuit/firmware/a04/third_party/opus-1.6.1/celt/fixed_generic.h:57:73: note: in expansion of macro 'MULT16_16SU'
   57 | #define MULT16_32_Q15(a,b) ADD32(SHL(MULT16_16((a),SHR((b),16)),1), SHR(MULT16_16SU((a),((b)&0x0000ffff)),15))
      |                                                                         ^~~~~~~~~~~
F:/circuit/firmware/a04/third_party/opus-1.6.1/celt/celt_encoder.c:1561:19: note: in expansion of macro 'MULT16_32_Q15'
 1561 |       thresh[0] = MULT16_32_Q15(MULT16_16_Q15(QCONST16(.25f, 15), gain1), before[0]) + MULT16_32_Q15(QCONST16(.01f,15), before[1]);
      |                   ^~~~~~~~~~~~~
F:/circuit/firmware/a04/third_party/opus-1.6.1/celt/fixed_generic.h:193:29: note: in expansion of macro 'SHR'
  193 | #define MULT16_16_Q15(a,b) (SHR(MULT16_16((a),(b)),15))
      |                             ^~~
F:/circuit/firmware/a04/third_party/opus-1.6.1/celt/fixed_generic.h:193:33: note: in expansion of macro 'MULT16_16'
  193 | #define MULT16_16_Q15(a,b) (SHR(MULT16_16((a),(b)),15))
      |                                 ^~~~~~~~~
F:/circuit/firmware/a04/third_party/opus-1.6.1/celt/celt_encoder.c:1561:33: note: in expansion of macro 'MULT16_16_Q15'
 1561 |       thresh[0] = MULT16_32_Q15(MULT16_16_Q15(QCONST16(.25f, 15), gain1), before[0]) + MULT16_32_Q15(QCONST16(.01f,15), before[1]);
      |                                 ^~~~~~~~~~~~~
F:/circuit/firmware/a04/third_party/opus-1.6.1/celt/celt_encoder.c:1561:47: note: in expansion of macro 'QCONST16'
 1561 |       thresh[0] = MULT16_32_Q15(MULT16_16_Q15(QCONST16(.25f, 15), gain1), before[0]) + MULT16_32_Q15(QCONST16(.01f,15), before[1]);
      |                                               ^~~~~~~~
F:/circuit/firmware/a04/third_party/opus-1.6.1/celt/fixed_generic.h:92:42: warning: implicit conversion from 'float' to 'double' to match other operand of binary expression [-Wdouble-promotion]
   92 | #define QCONST16(x,bits) ((opus_val16)(.5+(x)*(((opus_val32)1)<<(bits))))
      |                                          ^
F:/circuit/firmware/a04/third_party/opus-1.6.1/celt/fixed_generic.h:152:34: note: in definition of macro 'ADD32'
  152 | #define ADD32(a,b) ((opus_val32)(a)+(opus_val32)(b))
      |                                  ^
F:/circuit/firmware/a04/third_party/opus-1.6.1/celt/fixed_generic.h:132:22: note: in expansion of macro 'SHL32'
  132 | #define SHL(a,shift) SHL32(a,shift)
      |                      ^~~~~
F:/circuit/firmware/a04/third_party/opus-1.6.1/celt/fixed_generic.h:57:34: note: in expansion of macro 'SHL'
   57 | #define MULT16_32_Q15(a,b) ADD32(SHL(MULT16_16((a),SHR((b),16)),1), SHR(MULT16_16SU((a),((b)&0x0000ffff)),15))
      |                                  ^~~
F:/circuit/firmware/a04/third_party/opus-1.6.1/celt/fixed_generic.h:57:38: note: in expansion of macro 'MULT16_16'
   57 | #define MULT16_32_Q15(a,b) ADD32(SHL(MULT16_16((a),SHR((b),16)),1), SHR(MULT16_16SU((a),((b)&0x0000ffff)),15))
      |                                      ^~~~~~~~~
F:/circuit/firmware/a04/third_party/opus-1.6.1/celt/celt_encoder.c:1561:88: note: in expansion of macro 'MULT16_32_Q15'
 1561 |       thresh[0] = MULT16_32_Q15(MULT16_16_Q15(QCONST16(.25f, 15), gain1), before[0]) + MULT16_32_Q15(QCONST16(.01f,15), before[1]);
      |                                                                                        ^~~~~~~~~~~~~
F:/circuit/firmware/a04/third_party/opus-1.6.1/celt/celt_encoder.c:1561:102: note: in expansion of macro 'QCONST16'
 1561 |       thresh[0] = MULT16_32_Q15(MULT16_16_Q15(QCONST16(.25f, 15), gain1), before[0]) + MULT16_32_Q15(QCONST16(.01f,15), before[1]);
      |                                                                                                      ^~~~~~~~
F:/circuit/firmware/a04/third_party/opus-1.6.1/celt/fixed_generic.h:92:42: warning: implicit conversion from 'float' to 'double' to match other operand of binary expression [-Wdouble-promotion]
   92 | #define QCONST16(x,bits) ((opus_val16)(.5+(x)*(((opus_val32)1)<<(bits))))
      |                                          ^
F:/circuit/firmware/a04/third_party/opus-1.6.1/celt/fixed_generic.h:152:50: note: in definition of macro 'ADD32'
  152 | #define ADD32(a,b) ((opus_val32)(a)+(opus_val32)(b))
      |                                                  ^
F:/circuit/firmware/a04/third_party/opus-1.6.1/celt/fixed_generic.h:57:69: note: in expansion of macro 'SHR'
   57 | #define MULT16_32_Q15(a,b) ADD32(SHL(MULT16_16((a),SHR((b),16)),1), SHR(MULT16_16SU((a),((b)&0x0000ffff)),15))
      |                                                                     ^~~
F:/circuit/firmware/a04/third_party/opus-1.6.1/celt/fixed_generic.h:57:73: note: in expansion of macro 'MULT16_16SU'
   57 | #define MULT16_32_Q15(a,b) ADD32(SHL(MULT16_16((a),SHR((b),16)),1), SHR(MULT16_16SU((a),((b)&0x0000ffff)),15))
      |                                                                         ^~~~~~~~~~~
F:/circuit/firmware/a04/third_party/opus-1.6.1/celt/celt_encoder.c:1561:88: note: in expansion of macro 'MULT16_32_Q15'
 1561 |       thresh[0] = MULT16_32_Q15(MULT16_16_Q15(QCONST16(.25f, 15), gain1), before[0]) + MULT16_32_Q15(QCONST16(.01f,15), before[1]);
      |                                                                                        ^~~~~~~~~~~~~
F:/circuit/firmware/a04/third_party/opus-1.6.1/celt/celt_encoder.c:1561:102: note: in expansion of macro 'QCONST16'
 1561 |       thresh[0] = MULT16_32_Q15(MULT16_16_Q15(QCONST16(.25f, 15), gain1), before[0]) + MULT16_32_Q15(QCONST16(.01f,15), before[1]);
      |                                                                                                      ^~~~~~~~
F:/circuit/firmware/a04/third_party/opus-1.6.1/celt/fixed_generic.h:92:42: warning: implicit conversion from 'float' to 'double' to match other operand of binary expression [-Wdouble-promotion]
   92 | #define QCONST16(x,bits) ((opus_val16)(.5+(x)*(((opus_val32)1)<<(bits))))
      |                                          ^
F:/circuit/firmware/a04/third_party/opus-1.6.1/celt/fixed_generic.h:152:34: note: in definition of macro 'ADD32'
  152 | #define ADD32(a,b) ((opus_val32)(a)+(opus_val32)(b))
      |                                  ^
F:/circuit/firmware/a04/third_party/opus-1.6.1/celt/fixed_generic.h:132:22: note: in expansion of macro 'SHL32'
  132 | #define SHL(a,shift) SHL32(a,shift)
      |                      ^~~~~
F:/circuit/firmware/a04/third_party/opus-1.6.1/celt/fixed_generic.h:57:34: note: in expansion of macro 'SHL'
   57 | #define MULT16_32_Q15(a,b) ADD32(SHL(MULT16_16((a),SHR((b),16)),1), SHR(MULT16_16SU((a),((b)&0x0000ffff)),15))
      |                                  ^~~
F:/circuit/firmware/a04/third_party/opus-1.6.1/celt/fixed_generic.h:57:38: note: in expansion of macro 'MULT16_16'
   57 | #define MULT16_32_Q15(a,b) ADD32(SHL(MULT16_16((a),SHR((b),16)),1), SHR(MULT16_16SU((a),((b)&0x0000ffff)),15))
      |                                      ^~~~~~~~~
F:/circuit/firmware/a04/third_party/opus-1.6.1/celt/celt_encoder.c:1562:19: note: in expansion of macro 'MULT16_32_Q15'
 1562 |       thresh[1] = MULT16_32_Q15(MULT16_16_Q15(QCONST16(.25f, 15), gain1), before[1]) + MULT16_32_Q15(QCONST16(.01f,15), before[0]);
      |                   ^~~~~~~~~~~~~
F:/circuit/firmware/a04/third_party/opus-1.6.1/celt/fixed_generic.h:193:29: note: in expansion of macro 'SHR'
  193 | #define MULT16_16_Q15(a,b) (SHR(MULT16_16((a),(b)),15))
      |                             ^~~
F:/circuit/firmware/a04/third_party/opus-1.6.1/celt/fixed_generic.h:193:33: note: in expansion of macro 'MULT16_16'
  193 | #define MULT16_16_Q15(a,b) (SHR(MULT16_16((a),(b)),15))
      |                                 ^~~~~~~~~
F:/circuit/firmware/a04/third_party/opus-1.6.1/celt/celt_encoder.c:1562:33: note: in expansion of macro 'MULT16_16_Q15'
 1562 |       thresh[1] = MULT16_32_Q15(MULT16_16_Q15(QCONST16(.25f, 15), gain1), before[1]) + MULT16_32_Q15(QCONST16(.01f,15), before[0]);
      |                                 ^~~~~~~~~~~~~
F:/circuit/firmware/a04/third_party/opus-1.6.1/celt/celt_encoder.c:1562:47: note: in expansion of macro 'QCONST16'
 1562 |       thresh[1] = MULT16_32_Q15(MULT16_16_Q15(QCONST16(.25f, 15), gain1), before[1]) + MULT16_32_Q15(QCONST16(.01f,15), before[0]);
      |                                               ^~~~~~~~
F:/circuit/firmware/a04/third_party/opus-1.6.1/celt/fixed_generic.h:92:42: warning: implicit conversion from 'float' to 'double' to match other operand of binary expression [-Wdouble-promotion]
   92 | #define QCONST16(x,bits) ((opus_val16)(.5+(x)*(((opus_val32)1)<<(bits))))
      |                                          ^
F:/circuit/firmware/a04/third_party/opus-1.6.1/celt/fixed_generic.h:152:50: note: in definition of macro 'ADD32'
  152 | #define ADD32(a,b) ((opus_val32)(a)+(opus_val32)(b))
      |                                                  ^
F:/circuit/firmware/a04/third_party/opus-1.6.1/celt/fixed_generic.h:57:69: note: in expansion of macro 'SHR'
   57 | #define MULT16_32_Q15(a,b) ADD32(SHL(MULT16_16((a),SHR((b),16)),1), SHR(MULT16_16SU((a),((b)&0x0000ffff)),15))
      |                                                                     ^~~
F:/circuit/firmware/a04/third_party/opus-1.6.1/celt/fixed_generic.h:57:73: note: in expansion of macro 'MULT16_16SU'
   57 | #define MULT16_32_Q15(a,b) ADD32(SHL(MULT16_16((a),SHR((b),16)),1), SHR(MULT16_16SU((a),((b)&0x0000ffff)),15))
      |                                                                         ^~~~~~~~~~~
F:/circuit/firmware/a04/third_party/opus-1.6.1/celt/celt_encoder.c:1562:19: note: in expansion of macro 'MULT16_32_Q15'
 1562 |       thresh[1] = MULT16_32_Q15(MULT16_16_Q15(QCONST16(.25f, 15), gain1), before[1]) + MULT16_32_Q15(QCONST16(.01f,15), before[0]);
      |                   ^~~~~~~~~~~~~
F:/circuit/firmware/a04/third_party/opus-1.6.1/celt/fixed_generic.h:193:29: note: in expansion of macro 'SHR'
  193 | #define MULT16_16_Q15(a,b) (SHR(MULT16_16((a),(b)),15))
      |                             ^~~
F:/circuit/firmware/a04/third_party/opus-1.6.1/celt/fixed_generic.h:193:33: note: in expansion of macro 'MULT16_16'
  193 | #define MULT16_16_Q15(a,b) (SHR(MULT16_16((a),(b)),15))
      |                                 ^~~~~~~~~
F:/circuit/firmware/a04/third_party/opus-1.6.1/celt/celt_encoder.c:1562:33: note: in expansion of macro 'MULT16_16_Q15'
 1562 |       thresh[1] = MULT16_32_Q15(MULT16_16_Q15(QCONST16(.25f, 15), gain1), before[1]) + MULT16_32_Q15(QCONST16(.01f,15), before[0]);
      |                                 ^~~~~~~~~~~~~
F:/circuit/firmware/a04/third_party/opus-1.6.1/celt/celt_encoder.c:1562:47: note: in expansion of macro 'QCONST16'
 1562 |       thresh[1] = MULT16_32_Q15(MULT16_16_Q15(QCONST16(.25f, 15), gain1), before[1]) + MULT16_32_Q15(QCONST16(.01f,15), before[0]);
      |                                               ^~~~~~~~
F:/circuit/firmware/a04/third_party/opus-1.6.1/celt/fixed_generic.h:92:42: warning: implicit conversion from 'float' to 'double' to match other operand of binary expression [-Wdouble-promotion]
   92 | #define QCONST16(x,bits) ((opus_val16)(.5+(x)*(((opus_val32)1)<<(bits))))
      |                                          ^
F:/circuit/firmware/a04/third_party/opus-1.6.1/celt/fixed_generic.h:152:34: note: in definition of macro 'ADD32'
  152 | #define ADD32(a,b) ((opus_val32)(a)+(opus_val32)(b))
      |                                  ^
F:/circuit/firmware/a04/third_party/opus-1.6.1/celt/fixed_generic.h:132:22: note: in expansion of macro 'SHL32'
  132 | #define SHL(a,shift) SHL32(a,shift)
      |                      ^~~~~
F:/circuit/firmware/a04/third_party/opus-1.6.1/celt/fixed_generic.h:57:34: note: in expansion of macro 'SHL'
   57 | #define MULT16_32_Q15(a,b) ADD32(SHL(MULT16_16((a),SHR((b),16)),1), SHR(MULT16_16SU((a),((b)&0x0000ffff)),15))
      |                                  ^~~
F:/circuit/firmware/a04/third_party/opus-1.6.1/celt/fixed_generic.h:57:38: note: in expansion of macro 'MULT16_16'
   57 | #define MULT16_32_Q15(a,b) ADD32(SHL(MULT16_16((a),SHR((b),16)),1), SHR(MULT16_16SU((a),((b)&0x0000ffff)),15))
      |                                      ^~~~~~~~~
F:/circuit/firmware/a04/third_party/opus-1.6.1/celt/celt_encoder.c:1562:88: note: in expansion of macro 'MULT16_32_Q15'
 1562 |       thresh[1] = MULT16_32_Q15(MULT16_16_Q15(QCONST16(.25f, 15), gain1), before[1]) + MULT16_32_Q15(QCONST16(.01f,15), before[0]);
      |                                                                                        ^~~~~~~~~~~~~
F:/circuit/firmware/a04/third_party/opus-1.6.1/celt/celt_encoder.c:1562:102: note: in expansion of macro 'QCONST16'
 1562 |       thresh[1] = MULT16_32_Q15(MULT16_16_Q15(QCONST16(.25f, 15), gain1), before[1]) + MULT16_32_Q15(QCONST16(.01f,15), before[0]);
      |                                                                                                      ^~~~~~~~
F:/circuit/firmware/a04/third_party/opus-1.6.1/celt/fixed_generic.h:92:42: warning: implicit conversion from 'float' to 'double' to match other operand of binary expression [-Wdouble-promotion]
   92 | #define QCONST16(x,bits) ((opus_val16)(.5+(x)*(((opus_val32)1)<<(bits))))
      |                                          ^
F:/circuit/firmware/a04/third_party/opus-1.6.1/celt/fixed_generic.h:152:50: note: in definition of macro 'ADD32'
  152 | #define ADD32(a,b) ((opus_val32)(a)+(opus_val32)(b))
      |                                                  ^
F:/circuit/firmware/a04/third_party/opus-1.6.1/celt/fixed_generic.h:57:69: note: in expansion of macro 'SHR'
   57 | #define MULT16_32_Q15(a,b) ADD32(SHL(MULT16_16((a),SHR((b),16)),1), SHR(MULT16_16SU((a),((b)&0x0000ffff)),15))
      |                                                                     ^~~
F:/circuit/firmware/a04/third_party/opus-1.6.1/celt/fixed_generic.h:57:73: note: in expansion of macro 'MULT16_16SU'
   57 | #define MULT16_32_Q15(a,b) ADD32(SHL(MULT16_16((a),SHR((b),16)),1), SHR(MULT16_16SU((a),((b)&0x0000ffff)),15))
      |                                                                         ^~~~~~~~~~~
F:/circuit/firmware/a04/third_party/opus-1.6.1/celt/celt_encoder.c:1562:88: note: in expansion of macro 'MULT16_32_Q15'
 1562 |       thresh[1] = MULT16_32_Q15(MULT16_16_Q15(QCONST16(.25f, 15), gain1), before[1]) + MULT16_32_Q15(QCONST16(.01f,15), before[0]);
      |                                                                                        ^~~~~~~~~~~~~
F:/circuit/firmware/a04/third_party/opus-1.6.1/celt/celt_encoder.c:1562:102: note: in expansion of macro 'QCONST16'
 1562 |       thresh[1] = MULT16_32_Q15(MULT16_16_Q15(QCONST16(.25f, 15), gain1), before[1]) + MULT16_32_Q15(QCONST16(.01f,15), before[0]);
      |                                                                                                      ^~~~~~~~
F:/circuit/firmware/a04/third_party/opus-1.6.1/celt/celt_encoder.c: In function 'compute_vbr':
F:/circuit/firmware/a04/third_party/opus-1.6.1/celt/fixed_generic.h:92:42: warning: implicit conversion from 'float' to 'double' to match other operand of binary expression [-Wdouble-promotion]
   92 | #define QCONST16(x,bits) ((opus_val16)(.5+(x)*(((opus_val32)1)<<(bits))))
      |                                          ^
F:/circuit/firmware/a04/third_party/opus-1.6.1/celt/fixed_generic.h:200:51: note: in definition of macro 'DIV32_16'
  200 | #define DIV32_16(a,b) ((opus_val16)(((opus_val32)(a))/((opus_val16)(b))))
      |                                                   ^
F:/circuit/firmware/a04/third_party/opus-1.6.1/celt/celt_encoder.c:1643:27: note: in expansion of macro 'MULT16_16'
 1643 |       max_frac = DIV32_16(MULT16_16(QCONST16(0.8f, 15), coded_stereo_dof), coded_bins);
      |                           ^~~~~~~~~
F:/circuit/firmware/a04/third_party/opus-1.6.1/celt/celt_encoder.c:1643:37: note: in expansion of macro 'QCONST16'
 1643 |       max_frac = DIV32_16(MULT16_16(QCONST16(0.8f, 15), coded_stereo_dof), coded_bins);
      |                                     ^~~~~~~~
F:/circuit/firmware/a04/third_party/opus-1.6.1/celt/fixed_generic.h:92:42: warning: implicit conversion from 'float' to 'double' to match other operand of binary expression [-Wdouble-promotion]
   92 | #define QCONST16(x,bits) ((opus_val16)(.5+(x)*(((opus_val32)1)<<(bits))))
      |                                          ^
F:/circuit/firmware/a04/third_party/opus-1.6.1/celt/arch.h:100:28: note: in definition of macro 'MIN16'
  100 | #define MIN16(a,b) ((a) < (b) ? (a) : (b))   /**< Minimum 16-bit value.   */
      |                            ^
F:/circuit/firmware/a04/third_party/opus-1.6.1/celt/celt_encoder.c:1644:44: note: in expansion of macro 'QCONST16'
 1644 |       stereo_saving = MIN16(stereo_saving, QCONST16(1.f, 8));
      |                                            ^~~~~~~~
F:/circuit/firmware/a04/third_party/opus-1.6.1/celt/fixed_generic.h:92:42: warning: implicit conversion from 'float' to 'double' to match other operand of binary expression [-Wdouble-promotion]
   92 | #define QCONST16(x,bits) ((opus_val16)(.5+(x)*(((opus_val32)1)<<(bits))))
      |                                          ^
F:/circuit/firmware/a04/third_party/opus-1.6.1/celt/arch.h:100:40: note: in definition of macro 'MIN16'
  100 | #define MIN16(a,b) ((a) < (b) ? (a) : (b))   /**< Minimum 16-bit value.   */
      |                                        ^
F:/circuit/firmware/a04/third_party/opus-1.6.1/celt/celt_encoder.c:1644:44: note: in expansion of macro 'QCONST16'
 1644 |       stereo_saving = MIN16(stereo_saving, QCONST16(1.f, 8));
      |                                            ^~~~~~~~
F:/circuit/firmware/a04/third_party/opus-1.6.1/celt/fixed_generic.h:92:42: warning: implicit conversion from 'float' to 'double' to match other operand of binary expression [-Wdouble-promotion]
   92 | #define QCONST16(x,bits) ((opus_val16)(.5+(x)*(((opus_val32)1)<<(bits))))
      |                                          ^
F:/circuit/firmware/a04/third_party/opus-1.6.1/celt/arch.h:102:28: note: in definition of macro 'MIN32'
  102 | #define MIN32(a,b) ((a) < (b) ? (a) : (b))   /**< Minimum 32-bit value.   */
      |                            ^
F:/circuit/firmware/a04/third_party/opus-1.6.1/celt/celt_encoder.c:1647:23: note: in expansion of macro 'SHR32'
 1647 |                       SHR32(MULT16_16(stereo_saving-QCONST16(0.1f,8),(coded_stereo_dof<<BITRES)),8));
      |                       ^~~~~
F:/circuit/firmware/a04/third_party/opus-1.6.1/celt/celt_encoder.c:1647:29: note: in expansion of macro 'MULT16_16'
 1647 |                       SHR32(MULT16_16(stereo_saving-QCONST16(0.1f,8),(coded_stereo_dof<<BITRES)),8));
      |                             ^~~~~~~~~
F:/circuit/firmware/a04/third_party/opus-1.6.1/celt/celt_encoder.c:1647:53: note: in expansion of macro 'QCONST16'
 1647 |                       SHR32(MULT16_16(stereo_saving-QCONST16(0.1f,8),(coded_stereo_dof<<BITRES)),8));
      |                                                     ^~~~~~~~
F:/circuit/firmware/a04/third_party/opus-1.6.1/celt/fixed_generic.h:92:42: warning: implicit conversion from 'float' to 'double' to match other operand of binary expression [-Wdouble-promotion]
   92 | #define QCONST16(x,bits) ((opus_val16)(.5+(x)*(((opus_val32)1)<<(bits))))
      |                                          ^
F:/circuit/firmware/a04/third_party/opus-1.6.1/celt/arch.h:102:40: note: in definition of macro 'MIN32'
  102 | #define MIN32(a,b) ((a) < (b) ? (a) : (b))   /**< Minimum 32-bit value.   */
      |                                        ^
F:/circuit/firmware/a04/third_party/opus-1.6.1/celt/celt_encoder.c:1647:23: note: in expansion of macro 'SHR32'
 1647 |                       SHR32(MULT16_16(stereo_saving-QCONST16(0.1f,8),(coded_stereo_dof<<BITRES)),8));
      |                       ^~~~~
F:/circuit/firmware/a04/third_party/opus-1.6.1/celt/celt_encoder.c:1647:29: note: in expansion of macro 'MULT16_16'
 1647 |                       SHR32(MULT16_16(stereo_saving-QCONST16(0.1f,8),(coded_stereo_dof<<BITRES)),8));
      |                             ^~~~~~~~~
F:/circuit/firmware/a04/third_party/opus-1.6.1/celt/celt_encoder.c:1647:53: note: in expansion of macro 'QCONST16'
 1647 |                       SHR32(MULT16_16(stereo_saving-QCONST16(0.1f,8),(coded_stereo_dof<<BITRES)),8));
      |                                                     ^~~~~~~~
F:/circuit/firmware/a04/third_party/opus-1.6.1/celt/fixed_generic.h:92:42: warning: implicit conversion from 'float' to 'double' to match other operand of binary expression [-Wdouble-promotion]
   92 | #define QCONST16(x,bits) ((opus_val16)(.5+(x)*(((opus_val32)1)<<(bits))))
      |                                          ^
F:/circuit/firmware/a04/third_party/opus-1.6.1/celt/celt_encoder.c:1652:21: note: in expansion of macro 'QCONST16'
 1652 |    tf_calibration = QCONST16(0.044f,14);
      |                     ^~~~~~~~
F:/circuit/firmware/a04/third_party/opus-1.6.1/celt/fixed_generic.h:92:42: warning: implicit conversion from 'float' to 'double' to match other operand of binary expression [-Wdouble-promotion]
   92 | #define QCONST16(x,bits) ((opus_val16)(.5+(x)*(((opus_val32)1)<<(bits))))
      |                                          ^
F:/circuit/firmware/a04/third_party/opus-1.6.1/celt/fixed_generic.h:152:34: note: in definition of macro 'ADD32'
  152 | #define ADD32(a,b) ((opus_val32)(a)+(opus_val32)(b))
      |                                  ^
F:/circuit/firmware/a04/third_party/opus-1.6.1/celt/fixed_generic.h:132:22: note: in expansion of macro 'SHL32'
  132 | #define SHL(a,shift) SHL32(a,shift)
      |                      ^~~~~
F:/circuit/firmware/a04/third_party/opus-1.6.1/celt/fixed_generic.h:57:34: note: in expansion of macro 'SHL'
   57 | #define MULT16_32_Q15(a,b) ADD32(SHL(MULT16_16((a),SHR((b),16)),1), SHR(MULT16_16SU((a),((b)&0x0000ffff)),15))
      |                                  ^~~
F:/circuit/firmware/a04/third_party/opus-1.6.1/celt/fixed_generic.h:57:38: note: in expansion of macro 'MULT16_16'
   57 | #define MULT16_32_Q15(a,b) ADD32(SHL(MULT16_16((a),SHR((b),16)),1), SHR(MULT16_16SU((a),((b)&0x0000ffff)),15))
      |                                      ^~~~~~~~~
F:/circuit/firmware/a04/third_party/opus-1.6.1/celt/celt_encoder.c:1700:42: note: in expansion of macro 'MULT16_32_Q15'
 1700 |       target = base_target + (opus_int32)MULT16_32_Q15(QCONST16(0.67f, 15), target-base_target);
      |                                          ^~~~~~~~~~~~~
F:/circuit/firmware/a04/third_party/opus-1.6.1/celt/celt_encoder.c:1700:56: note: in expansion of macro 'QCONST16'
 1700 |       target = base_target + (opus_int32)MULT16_32_Q15(QCONST16(0.67f, 15), target-base_target);
      |                                                        ^~~~~~~~
F:/circuit/firmware/a04/third_party/opus-1.6.1/celt/fixed_generic.h:92:42: warning: implicit conversion from 'float' to 'double' to match other operand of binary expression [-Wdouble-promotion]
   92 | #define QCONST16(x,bits) ((opus_val16)(.5+(x)*(((opus_val32)1)<<(bits))))
      |                                          ^
F:/circuit/firmware/a04/third_party/opus-1.6.1/celt/fixed_generic.h:152:50: note: in definition of macro 'ADD32'
  152 | #define ADD32(a,b) ((opus_val32)(a)+(opus_val32)(b))
      |                                                  ^
F:/circuit/firmware/a04/third_party/opus-1.6.1/celt/fixed_generic.h:57:69: note: in expansion of macro 'SHR'
   57 | #define MULT16_32_Q15(a,b) ADD32(SHL(MULT16_16((a),SHR((b),16)),1), SHR(MULT16_16SU((a),((b)&0x0000ffff)),15))
      |                                                                     ^~~
F:/circuit/firmware/a04/third_party/opus-1.6.1/celt/fixed_generic.h:57:73: note: in expansion of macro 'MULT16_16SU'
   57 | #define MULT16_32_Q15(a,b) ADD32(SHL(MULT16_16((a),SHR((b),16)),1), SHR(MULT16_16SU((a),((b)&0x0000ffff)),15))
      |                                                                         ^~~~~~~~~~~
F:/circuit/firmware/a04/third_party/opus-1.6.1/celt/celt_encoder.c:1700:42: note: in expansion of macro 'MULT16_32_Q15'
 1700 |       target = base_target + (opus_int32)MULT16_32_Q15(QCONST16(0.67f, 15), target-base_target);
      |                                          ^~~~~~~~~~~~~
F:/circuit/firmware/a04/third_party/opus-1.6.1/celt/celt_encoder.c:1700:56: note: in expansion of macro 'QCONST16'
 1700 |       target = base_target + (opus_int32)MULT16_32_Q15(QCONST16(0.67f, 15), target-base_target);
      |                                                        ^~~~~~~~
F:/circuit/firmware/a04/third_party/opus-1.6.1/celt/fixed_generic.h:92:42: warning: implicit conversion from 'float' to 'double' to match other operand of binary expression [-Wdouble-promotion]
   92 | #define QCONST16(x,bits) ((opus_val16)(.5+(x)*(((opus_val32)1)<<(bits))))
      |                                          ^
F:/circuit/firmware/a04/third_party/opus-1.6.1/celt/celt_encoder.c:1703:44: note: in expansion of macro 'QCONST16'
 1703 |    if (!has_surround_mask && tf_estimate < QCONST16(.2f, 14))
      |                                            ^~~~~~~~
F:/circuit/firmware/a04/third_party/opus-1.6.1/celt/fixed_generic.h:92:42: warning: implicit conversion from 'float' to 'double' to match other operand of binary expression [-Wdouble-promotion]
   92 | #define QCONST16(x,bits) ((opus_val16)(.5+(x)*(((opus_val32)1)<<(bits))))
      |                                          ^
F:/circuit/firmware/a04/third_party/opus-1.6.1/celt/fixed_generic.h:131:24: note: in definition of macro 'SHR'
  131 | #define SHR(a,shift) ((a) >> (shift))
      |                        ^
F:/circuit/firmware/a04/third_party/opus-1.6.1/celt/fixed_generic.h:193:33: note: in expansion of macro 'MULT16_16'
  193 | #define MULT16_16_Q15(a,b) (SHR(MULT16_16((a),(b)),15))
      |                                 ^~~~~~~~~
F:/circuit/firmware/a04/third_party/opus-1.6.1/celt/celt_encoder.c:1707:16: note: in expansion of macro 'MULT16_16_Q15'
 1707 |       amount = MULT16_16_Q15(QCONST16(.0000031f, 30), IMAX(0, IMIN(32000, 96000-bitrate)));
      |                ^~~~~~~~~~~~~
F:/circuit/firmware/a04/third_party/opus-1.6.1/celt/celt_encoder.c:1707:30: note: in expansion of macro 'QCONST16'
 1707 |       amount = MULT16_16_Q15(QCONST16(.0000031f, 30), IMAX(0, IMIN(32000, 96000-bitrate)));
      |                              ^~~~~~~~
F:/circuit/firmware/a04/third_party/opus-1.6.1/celt/celt_encoder.c: In function 'celt_encode_with_ec':
F:/circuit/firmware/a04/third_party/opus-1.6.1/celt/fixed_generic.h:95:42: warning: implicit conversion from 'float' to 'double' to match other operand of binary expression [-Wdouble-promotion]
   95 | #define QCONST32(x,bits) ((opus_val32)(.5+(x)*(((opus_int64)1)<<(bits))))
      |                                          ^
F:/circuit/firmware/a04/third_party/opus-1.6.1/celt/arch.h:102:28: note: in definition of macro 'MIN32'
  102 | #define MIN32(a,b) ((a) < (b) ? (a) : (b))   /**< Minimum 32-bit value.   */
      |                            ^
F:/circuit/firmware/a04/third_party/opus-1.6.1/celt/celt_encoder.c:2033:37: note: in expansion of macro 'QCONST32'
 2033 |    toneishness = MIN32(toneishness, QCONST32(1.f, 29)-SHL32(tf_estimate, 15));
      |                                     ^~~~~~~~
F:/circuit/firmware/a04/third_party/opus-1.6.1/celt/fixed_generic.h:95:42: warning: implicit conversion from 'float' to 'double' to match other operand of binary expression [-Wdouble-promotion]
   95 | #define QCONST32(x,bits) ((opus_val32)(.5+(x)*(((opus_int64)1)<<(bits))))
      |                                          ^
F:/circuit/firmware/a04/third_party/opus-1.6.1/celt/arch.h:102:40: note: in definition of macro 'MIN32'
  102 | #define MIN32(a,b) ((a) < (b) ? (a) : (b))   /**< Minimum 32-bit value.   */
      |                                        ^
F:/circuit/firmware/a04/third_party/opus-1.6.1/celt/celt_encoder.c:2033:37: note: in expansion of macro 'QCONST32'
 2033 |    toneishness = MIN32(toneishness, QCONST32(1.f, 29)-SHL32(tf_estimate, 15));
      |                                     ^~~~~~~~
F:/circuit/firmware/a04/third_party/opus-1.6.1/celt/fixed_generic.h:92:42: warning: implicit conversion from 'float' to 'double' to match other operand of binary expression [-Wdouble-promotion]
   92 | #define QCONST16(x,bits) ((opus_val16)(.5+(x)*(((opus_val32)1)<<(bits))))
      |                                          ^
F:/circuit/firmware/a04/third_party/opus-1.6.1/celt/celt_encoder.c:2042:20: note: in expansion of macro 'QCONST16'
 2042 |       if ((gain1 > QCONST16(.4f,15) || st->prefilter_gain > QCONST16(.4f,15)) && (!st->analysis.valid || st->analysis.tonality > .3)
      |                    ^~~~~~~~
F:/circuit/firmware/a04/third_party/opus-1.6.1/celt/fixed_generic.h:92:42: warning: implicit conversion from 'float' to 'double' to match other operand of binary expression [-Wdouble-promotion]
   92 | #define QCONST16(x,bits) ((opus_val16)(.5+(x)*(((opus_val32)1)<<(bits))))
      |                                          ^
F:/circuit/firmware/a04/third_party/opus-1.6.1/celt/celt_encoder.c:2042:61: note: in expansion of macro 'QCONST16'
 2042 |       if ((gain1 > QCONST16(.4f,15) || st->prefilter_gain > QCONST16(.4f,15)) && (!st->analysis.valid || st->analysis.tonality > .3)
      |                                                             ^~~~~~~~
F:/circuit/firmware/a04/third_party/opus-1.6.1/celt/celt_encoder.c:2042:128: warning: implicit conversion from 'float' to 'double' to match other operand of binary expression [-Wdouble-promotion]
 2042 |       if ((gain1 > QCONST16(.4f,15) || st->prefilter_gain > QCONST16(.4f,15)) && (!st->analysis.valid || st->analysis.tonality > .3)
      |                                                                                                                                ^
F:/circuit/firmware/a04/third_party/opus-1.6.1/celt/fixed_generic.h:92:42: warning: implicit conversion from 'float' to 'double' to match other operand of binary expression [-Wdouble-promotion]
   92 | #define QCONST16(x,bits) ((opus_val16)(.5+(x)*(((opus_val32)1)<<(bits))))
      |                                          ^
F:/circuit/firmware/a04/third_party/opus-1.6.1/celt/arch.h:104:27: note: in definition of macro 'IMIN'
  104 | #define IMIN(a,b) ((a) < (b) ? (a) : (b))   /**< Minimum int value.   */
      |                           ^
F:/circuit/firmware/a04/third_party/opus-1.6.1/celt/fixed_generic.h:57:28: note: in expansion of macro 'ADD32'
   57 | #define MULT16_32_Q15(a,b) ADD32(SHL(MULT16_16((a),SHR((b),16)),1), SHR(MULT16_16SU((a),((b)&0x0000ffff)),15))
      |                            ^~~~~
F:/circuit/firmware/a04/third_party/opus-1.6.1/celt/fixed_generic.h:132:22: note: in expansion of macro 'SHL32'
  132 | #define SHL(a,shift) SHL32(a,shift)
      |                      ^~~~~
F:/circuit/firmware/a04/third_party/opus-1.6.1/celt/fixed_generic.h:57:34: note: in expansion of macro 'SHL'
   57 | #define MULT16_32_Q15(a,b) ADD32(SHL(MULT16_16((a),SHR((b),16)),1), SHR(MULT16_16SU((a),((b)&0x0000ffff)),15))
      |                                  ^~~
F:/circuit/firmware/a04/third_party/opus-1.6.1/celt/fixed_generic.h:57:38: note: in expansion of macro 'MULT16_16'
   57 | #define MULT16_32_Q15(a,b) ADD32(SHL(MULT16_16((a),SHR((b),16)),1), SHR(MULT16_16SU((a),((b)&0x0000ffff)),15))
      |                                      ^~~~~~~~~
F:/circuit/firmware/a04/third_party/opus-1.6.1/celt/celt_encoder.c:2102:36: note: in expansion of macro 'MULT16_32_Q15'
 2102 |          bandE[i] = IMIN(bandE[i], MULT16_32_Q15(QCONST16(1e-4f,15),bandE[0]));
      |                                    ^~~~~~~~~~~~~
F:/circuit/firmware/a04/third_party/opus-1.6.1/celt/celt_encoder.c:2102:50: note: in expansion of macro 'QCONST16'
 2102 |          bandE[i] = IMIN(bandE[i], MULT16_32_Q15(QCONST16(1e-4f,15),bandE[0]));
      |                                                  ^~~~~~~~
F:/circuit/firmware/a04/third_party/opus-1.6.1/celt/fixed_generic.h:92:42: warning: implicit conversion from 'float' to 'double' to match other operand of binary expression [-Wdouble-promotion]
   92 | #define QCONST16(x,bits) ((opus_val16)(.5+(x)*(((opus_val32)1)<<(bits))))
      |                                          ^
F:/circuit/firmware/a04/third_party/opus-1.6.1/celt/arch.h:104:27: note: in definition of macro 'IMIN'
  104 | #define IMIN(a,b) ((a) < (b) ? (a) : (b))   /**< Minimum int value.   */
      |                           ^
F:/circuit/firmware/a04/third_party/opus-1.6.1/celt/fixed_generic.h:57:28: note: in expansion of macro 'ADD32'
   57 | #define MULT16_32_Q15(a,b) ADD32(SHL(MULT16_16((a),SHR((b),16)),1), SHR(MULT16_16SU((a),((b)&0x0000ffff)),15))
      |                            ^~~~~
F:/circuit/firmware/a04/third_party/opus-1.6.1/celt/fixed_generic.h:57:69: note: in expansion of macro 'SHR'
   57 | #define MULT16_32_Q15(a,b) ADD32(SHL(MULT16_16((a),SHR((b),16)),1), SHR(MULT16_16SU((a),((b)&0x0000ffff)),15))
      |                                                                     ^~~
F:/circuit/firmware/a04/third_party/opus-1.6.1/celt/fixed_generic.h:57:73: note: in expansion of macro 'MULT16_16SU'
   57 | #define MULT16_32_Q15(a,b) ADD32(SHL(MULT16_16((a),SHR((b),16)),1), SHR(MULT16_16SU((a),((b)&0x0000ffff)),15))
      |                                                                         ^~~~~~~~~~~
F:/circuit/firmware/a04/third_party/opus-1.6.1/celt/celt_encoder.c:2102:36: note: in expansion of macro 'MULT16_32_Q15'
 2102 |          bandE[i] = IMIN(bandE[i], MULT16_32_Q15(QCONST16(1e-4f,15),bandE[0]));
      |                                    ^~~~~~~~~~~~~
F:/circuit/firmware/a04/third_party/opus-1.6.1/celt/celt_encoder.c:2102:50: note: in expansion of macro 'QCONST16'
 2102 |          bandE[i] = IMIN(bandE[i], MULT16_32_Q15(QCONST16(1e-4f,15),bandE[0]));
      |                                                  ^~~~~~~~
F:/circuit/firmware/a04/third_party/opus-1.6.1/celt/fixed_generic.h:92:42: warning: implicit conversion from 'float' to 'double' to match other operand of binary expression [-Wdouble-promotion]
   92 | #define QCONST16(x,bits) ((opus_val16)(.5+(x)*(((opus_val32)1)<<(bits))))
      |                                          ^
F:/circuit/firmware/a04/third_party/opus-1.6.1/celt/arch.h:104:39: note: in definition of macro 'IMIN'
  104 | #define IMIN(a,b) ((a) < (b) ? (a) : (b))   /**< Minimum int value.   */
      |                                       ^
F:/circuit/firmware/a04/third_party/opus-1.6.1/celt/fixed_generic.h:57:28: note: in expansion of macro 'ADD32'
   57 | #define MULT16_32_Q15(a,b) ADD32(SHL(MULT16_16((a),SHR((b),16)),1), SHR(MULT16_16SU((a),((b)&0x0000ffff)),15))
      |                            ^~~~~
F:/circuit/firmware/a04/third_party/opus-1.6.1/celt/fixed_generic.h:132:22: note: in expansion of macro 'SHL32'
  132 | #define SHL(a,shift) SHL32(a,shift)
      |                      ^~~~~
F:/circuit/firmware/a04/third_party/opus-1.6.1/celt/fixed_generic.h:57:34: note: in expansion of macro 'SHL'
   57 | #define MULT16_32_Q15(a,b) ADD32(SHL(MULT16_16((a),SHR((b),16)),1), SHR(MULT16_16SU((a),((b)&0x0000ffff)),15))
      |                                  ^~~
F:/circuit/firmware/a04/third_party/opus-1.6.1/celt/fixed_generic.h:57:38: note: in expansion of macro 'MULT16_16'
   57 | #define MULT16_32_Q15(a,b) ADD32(SHL(MULT16_16((a),SHR((b),16)),1), SHR(MULT16_16SU((a),((b)&0x0000ffff)),15))
      |                                      ^~~~~~~~~
F:/circuit/firmware/a04/third_party/opus-1.6.1/celt/celt_encoder.c:2102:36: note: in expansion of macro 'MULT16_32_Q15'
 2102 |          bandE[i] = IMIN(bandE[i], MULT16_32_Q15(QCONST16(1e-4f,15),bandE[0]));
      |                                    ^~~~~~~~~~~~~
F:/circuit/firmware/a04/third_party/opus-1.6.1/celt/celt_encoder.c:2102:50: note: in expansion of macro 'QCONST16'
 2102 |          bandE[i] = IMIN(bandE[i], MULT16_32_Q15(QCONST16(1e-4f,15),bandE[0]));
      |                                                  ^~~~~~~~
F:/circuit/firmware/a04/third_party/opus-1.6.1/celt/fixed_generic.h:92:42: warning: implicit conversion from 'float' to 'double' to match other operand of binary expression [-Wdouble-promotion]
   92 | #define QCONST16(x,bits) ((opus_val16)(.5+(x)*(((opus_val32)1)<<(bits))))
      |                                          ^
F:/circuit/firmware/a04/third_party/opus-1.6.1/celt/arch.h:104:39: note: in definition of macro 'IMIN'
  104 | #define IMIN(a,b) ((a) < (b) ? (a) : (b))   /**< Minimum int value.   */
      |                                       ^
F:/circuit/firmware/a04/third_party/opus-1.6.1/celt/fixed_generic.h:57:28: note: in expansion of macro 'ADD32'
   57 | #define MULT16_32_Q15(a,b) ADD32(SHL(MULT16_16((a),SHR((b),16)),1), SHR(MULT16_16SU((a),((b)&0x0000ffff)),15))
      |                            ^~~~~
F:/circuit/firmware/a04/third_party/opus-1.6.1/celt/fixed_generic.h:57:69: note: in expansion of macro 'SHR'
   57 | #define MULT16_32_Q15(a,b) ADD32(SHL(MULT16_16((a),SHR((b),16)),1), SHR(MULT16_16SU((a),((b)&0x0000ffff)),15))
      |                                                                     ^~~
F:/circuit/firmware/a04/third_party/opus-1.6.1/celt/fixed_generic.h:57:73: note: in expansion of macro 'MULT16_16SU'
   57 | #define MULT16_32_Q15(a,b) ADD32(SHL(MULT16_16((a),SHR((b),16)),1), SHR(MULT16_16SU((a),((b)&0x0000ffff)),15))
      |                                                                         ^~~~~~~~~~~
F:/circuit/firmware/a04/third_party/opus-1.6.1/celt/celt_encoder.c:2102:36: note: in expansion of macro 'MULT16_32_Q15'
 2102 |          bandE[i] = IMIN(bandE[i], MULT16_32_Q15(QCONST16(1e-4f,15),bandE[0]));
      |                                    ^~~~~~~~~~~~~
F:/circuit/firmware/a04/third_party/opus-1.6.1/celt/celt_encoder.c:2102:50: note: in expansion of macro 'QCONST16'
 2102 |          bandE[i] = IMIN(bandE[i], MULT16_32_Q15(QCONST16(1e-4f,15),bandE[0]));
      |                                                  ^~~~~~~~
F:/circuit/firmware/a04/third_party/opus-1.6.1/celt/fixed_generic.h:98:40: warning: implicit conversion from 'float' to 'double' to match other operand of binary expression [-Wdouble-promotion]
   98 | #define GCONST2(x,bits) ((celt_glog)(.5+(x)*(((celt_glog)1)<<(bits))))
      |                                        ^
F:/circuit/firmware/a04/third_party/opus-1.6.1/celt/arch.h:103:22: note: in definition of macro 'MAX32'
  103 | #define MAX32(a,b) ((a) > (b) ? (a) : (b))   /**< Maximum 32-bit value.   */
      |                      ^
F:/circuit/firmware/a04/third_party/opus-1.6.1/celt/celt_encoder.c:2126:20: note: in expansion of macro 'MAXG'
 2126 |             mask = MAXG(MING(st->energy_mask[nbEBands*c+i],
      |                    ^~~~
F:/circuit/firmware/a04/third_party/opus-1.6.1/celt/arch.h:111:19: note: in expansion of macro 'MIN32'
  111 | #define MING(a,b) MIN32(a, b)
      |                   ^~~~~
F:/circuit/firmware/a04/third_party/opus-1.6.1/celt/celt_encoder.c:2126:25: note: in expansion of macro 'MING'
 2126 |             mask = MAXG(MING(st->energy_mask[nbEBands*c+i],
      |                         ^~~~
F:/circuit/firmware/a04/third_party/opus-1.6.1/celt/fixed_generic.h:101:19: note: in expansion of macro 'GCONST2'
  101 | #define GCONST(x) GCONST2((x),DB_SHIFT)
      |                   ^~~~~~~
F:/circuit/firmware/a04/third_party/opus-1.6.1/celt/celt_encoder.c:2127:20: note: in expansion of macro 'GCONST'
 2127 |                    GCONST(.25f)), -GCONST(2.0f));
      |                    ^~~~~~
F:/circuit/firmware/a04/third_party/opus-1.6.1/celt/fixed_generic.h:98:40: warning: implicit conversion from 'float' to 'double' to match other operand of binary expression [-Wdouble-promotion]
   98 | #define GCONST2(x,bits) ((celt_glog)(.5+(x)*(((celt_glog)1)<<(bits))))
      |                                        ^
F:/circuit/firmware/a04/third_party/opus-1.6.1/celt/arch.h:103:22: note: in definition of macro 'MAX32'
  103 | #define MAX32(a,b) ((a) > (b) ? (a) : (b))   /**< Maximum 32-bit value.   */
      |                      ^
F:/circuit/firmware/a04/third_party/opus-1.6.1/celt/celt_encoder.c:2126:20: note: in expansion of macro 'MAXG'
 2126 |             mask = MAXG(MING(st->energy_mask[nbEBands*c+i],
      |                    ^~~~
F:/circuit/firmware/a04/third_party/opus-1.6.1/celt/arch.h:111:19: note: in expansion of macro 'MIN32'
  111 | #define MING(a,b) MIN32(a, b)
      |                   ^~~~~
F:/circuit/firmware/a04/third_party/opus-1.6.1/celt/celt_encoder.c:2126:25: note: in expansion of macro 'MING'
 2126 |             mask = MAXG(MING(st->energy_mask[nbEBands*c+i],
      |                         ^~~~
F:/circuit/firmware/a04/third_party/opus-1.6.1/celt/fixed_generic.h:101:19: note: in expansion of macro 'GCONST2'
  101 | #define GCONST(x) GCONST2((x),DB_SHIFT)
      |                   ^~~~~~~
F:/circuit/firmware/a04/third_party/opus-1.6.1/celt/celt_encoder.c:2127:20: note: in expansion of macro 'GCONST'
 2127 |                    GCONST(.25f)), -GCONST(2.0f));
      |                    ^~~~~~
F:/circuit/firmware/a04/third_party/opus-1.6.1/celt/fixed_generic.h:98:40: warning: implicit conversion from 'float' to 'double' to match other operand of binary expression [-Wdouble-promotion]
   98 | #define GCONST2(x,bits) ((celt_glog)(.5+(x)*(((celt_glog)1)<<(bits))))
      |                                        ^
F:/circuit/firmware/a04/third_party/opus-1.6.1/celt/arch.h:103:28: note: in definition of macro 'MAX32'
  103 | #define MAX32(a,b) ((a) > (b) ? (a) : (b))   /**< Maximum 32-bit value.   */
      |                            ^
F:/circuit/firmware/a04/third_party/opus-1.6.1/celt/celt_encoder.c:2126:20: note: in expansion of macro 'MAXG'
 2126 |             mask = MAXG(MING(st->energy_mask[nbEBands*c+i],
      |                    ^~~~
F:/circuit/firmware/a04/third_party/opus-1.6.1/celt/fixed_generic.h:101:19: note: in expansion of macro 'GCONST2'
  101 | #define GCONST(x) GCONST2((x),DB_SHIFT)
      |                   ^~~~~~~
F:/circuit/firmware/a04/third_party/opus-1.6.1/celt/celt_encoder.c:2127:36: note: in expansion of macro 'GCONST'
 2127 |                    GCONST(.25f)), -GCONST(2.0f));
      |                                    ^~~~~~
F:/circuit/firmware/a04/third_party/opus-1.6.1/celt/fixed_generic.h:98:40: warning: implicit conversion from 'float' to 'double' to match other operand of binary expression [-Wdouble-promotion]
   98 | #define GCONST2(x,bits) ((celt_glog)(.5+(x)*(((celt_glog)1)<<(bits))))
      |                                        ^
F:/circuit/firmware/a04/third_party/opus-1.6.1/celt/arch.h:103:34: note: in definition of macro 'MAX32'
  103 | #define MAX32(a,b) ((a) > (b) ? (a) : (b))   /**< Maximum 32-bit value.   */
      |                                  ^
F:/circuit/firmware/a04/third_party/opus-1.6.1/celt/celt_encoder.c:2126:20: note: in expansion of macro 'MAXG'
 2126 |             mask = MAXG(MING(st->energy_mask[nbEBands*c+i],
      |                    ^~~~
F:/circuit/firmware/a04/third_party/opus-1.6.1/celt/arch.h:111:19: note: in expansion of macro 'MIN32'
  111 | #define MING(a,b) MIN32(a, b)
      |                   ^~~~~
F:/circuit/firmware/a04/third_party/opus-1.6.1/celt/celt_encoder.c:2126:25: note: in expansion of macro 'MING'
 2126 |             mask = MAXG(MING(st->energy_mask[nbEBands*c+i],
      |                         ^~~~
F:/circuit/firmware/a04/third_party/opus-1.6.1/celt/fixed_generic.h:101:19: note: in expansion of macro 'GCONST2'
  101 | #define GCONST(x) GCONST2((x),DB_SHIFT)
      |                   ^~~~~~~
F:/circuit/firmware/a04/third_party/opus-1.6.1/celt/celt_encoder.c:2127:20: note: in expansion of macro 'GCONST'
 2127 |                    GCONST(.25f)), -GCONST(2.0f));
      |                    ^~~~~~
F:/circuit/firmware/a04/third_party/opus-1.6.1/celt/fixed_generic.h:98:40: warning: implicit conversion from 'float' to 'double' to match other operand of binary expression [-Wdouble-promotion]
   98 | #define GCONST2(x,bits) ((celt_glog)(.5+(x)*(((celt_glog)1)<<(bits))))
      |                                        ^
F:/circuit/firmware/a04/third_party/opus-1.6.1/celt/arch.h:103:34: note: in definition of macro 'MAX32'
  103 | #define MAX32(a,b) ((a) > (b) ? (a) : (b))   /**< Maximum 32-bit value.   */
      |                                  ^
F:/circuit/firmware/a04/third_party/opus-1.6.1/celt/celt_encoder.c:2126:20: note: in expansion of macro 'MAXG'
 2126 |             mask = MAXG(MING(st->energy_mask[nbEBands*c+i],
      |                    ^~~~
F:/circuit/firmware/a04/third_party/opus-1.6.1/celt/arch.h:111:19: note: in expansion of macro 'MIN32'
  111 | #define MING(a,b) MIN32(a, b)
      |                   ^~~~~
F:/circuit/firmware/a04/third_party/opus-1.6.1/celt/celt_encoder.c:2126:25: note: in expansion of macro 'MING'
 2126 |             mask = MAXG(MING(st->energy_mask[nbEBands*c+i],
      |                         ^~~~
F:/circuit/firmware/a04/third_party/opus-1.6.1/celt/fixed_generic.h:101:19: note: in expansion of macro 'GCONST2'
  101 | #define GCONST(x) GCONST2((x),DB_SHIFT)
      |                   ^~~~~~~
F:/circuit/firmware/a04/third_party/opus-1.6.1/celt/celt_encoder.c:2127:20: note: in expansion of macro 'GCONST'
 2127 |                    GCONST(.25f)), -GCONST(2.0f));
      |                    ^~~~~~
F:/circuit/firmware/a04/third_party/opus-1.6.1/celt/fixed_generic.h:98:40: warning: implicit conversion from 'float' to 'double' to match other operand of binary expression [-Wdouble-promotion]
   98 | #define GCONST2(x,bits) ((celt_glog)(.5+(x)*(((celt_glog)1)<<(bits))))
      |                                        ^
F:/circuit/firmware/a04/third_party/opus-1.6.1/celt/arch.h:103:40: note: in definition of macro 'MAX32'
  103 | #define MAX32(a,b) ((a) > (b) ? (a) : (b))   /**< Maximum 32-bit value.   */
      |                                        ^
F:/circuit/firmware/a04/third_party/opus-1.6.1/celt/celt_encoder.c:2126:20: note: in expansion of macro 'MAXG'
 2126 |             mask = MAXG(MING(st->energy_mask[nbEBands*c+i],
      |                    ^~~~
F:/circuit/firmware/a04/third_party/opus-1.6.1/celt/fixed_generic.h:101:19: note: in expansion of macro 'GCONST2'
  101 | #define GCONST(x) GCONST2((x),DB_SHIFT)
      |                   ^~~~~~~
F:/circuit/firmware/a04/third_party/opus-1.6.1/celt/celt_encoder.c:2127:36: note: in expansion of macro 'GCONST'
 2127 |                    GCONST(.25f)), -GCONST(2.0f));
      |                                    ^~~~~~
F:/circuit/firmware/a04/third_party/opus-1.6.1/celt/fixed_generic.h:98:40: warning: implicit conversion from 'float' to 'double' to match other operand of binary expression [-Wdouble-promotion]
   98 | #define GCONST2(x,bits) ((celt_glog)(.5+(x)*(((celt_glog)1)<<(bits))))
      |                                        ^
F:/circuit/firmware/a04/third_party/opus-1.6.1/celt/fixed_generic.h:101:19: note: in expansion of macro 'GCONST2'
  101 | #define GCONST(x) GCONST2((x),DB_SHIFT)
      |                   ^~~~~~~
F:/circuit/firmware/a04/third_party/opus-1.6.1/celt/celt_encoder.c:2138:19: note: in expansion of macro 'GCONST'
 2138 |       mask_avg += GCONST(.2f);
      |                   ^~~~~~
F:/circuit/firmware/a04/third_party/opus-1.6.1/celt/fixed_generic.h:98:40: warning: implicit conversion from 'float' to 'double' to match other operand of binary expression [-Wdouble-promotion]
   98 | #define GCONST2(x,bits) ((celt_glog)(.5+(x)*(((celt_glog)1)<<(bits))))
      |                                        ^
F:/circuit/firmware/a04/third_party/opus-1.6.1/celt/arch.h:103:22: note: in definition of macro 'MAX32'
  103 | #define MAX32(a,b) ((a) > (b) ? (a) : (b))   /**< Maximum 32-bit value.   */
      |                      ^
F:/circuit/firmware/a04/third_party/opus-1.6.1/celt/celt_encoder.c:2142:20: note: in expansion of macro 'MIN32'
 2142 |       diff = MAX32(MIN32(diff, GCONST(.031f)), -GCONST(.031f));
      |                    ^~~~~
F:/circuit/firmware/a04/third_party/opus-1.6.1/celt/fixed_generic.h:101:19: note: in expansion of macro 'GCONST2'
  101 | #define GCONST(x) GCONST2((x),DB_SHIFT)
      |                   ^~~~~~~
F:/circuit/firmware/a04/third_party/opus-1.6.1/celt/celt_encoder.c:2142:32: note: in expansion of macro 'GCONST'
 2142 |       diff = MAX32(MIN32(diff, GCONST(.031f)), -GCONST(.031f));
      |                                ^~~~~~
F:/circuit/firmware/a04/third_party/opus-1.6.1/celt/fixed_generic.h:98:40: warning: implicit conversion from 'float' to 'double' to match other operand of binary expression [-Wdouble-promotion]
   98 | #define GCONST2(x,bits) ((celt_glog)(.5+(x)*(((celt_glog)1)<<(bits))))
      |                                        ^
F:/circuit/firmware/a04/third_party/opus-1.6.1/celt/arch.h:103:22: note: in definition of macro 'MAX32'
  103 | #define MAX32(a,b) ((a) > (b) ? (a) : (b))   /**< Maximum 32-bit value.   */
      |                      ^
F:/circuit/firmware/a04/third_party/opus-1.6.1/celt/celt_encoder.c:2142:20: note: in expansion of macro 'MIN32'
 2142 |       diff = MAX32(MIN32(diff, GCONST(.031f)), -GCONST(.031f));
      |                    ^~~~~
F:/circuit/firmware/a04/third_party/opus-1.6.1/celt/fixed_generic.h:101:19: note: in expansion of macro 'GCONST2'
  101 | #define GCONST(x) GCONST2((x),DB_SHIFT)
      |                   ^~~~~~~
F:/circuit/firmware/a04/third_party/opus-1.6.1/celt/celt_encoder.c:2142:32: note: in expansion of macro 'GCONST'
 2142 |       diff = MAX32(MIN32(diff, GCONST(.031f)), -GCONST(.031f));
      |                                ^~~~~~
F:/circuit/firmware/a04/third_party/opus-1.6.1/celt/fixed_generic.h:98:40: warning: implicit conversion from 'float' to 'double' to match other operand of binary expression [-Wdouble-promotion]
   98 | #define GCONST2(x,bits) ((celt_glog)(.5+(x)*(((celt_glog)1)<<(bits))))
      |                                        ^
F:/circuit/firmware/a04/third_party/opus-1.6.1/celt/arch.h:103:28: note: in definition of macro 'MAX32'
  103 | #define MAX32(a,b) ((a) > (b) ? (a) : (b))   /**< Maximum 32-bit value.   */
      |                            ^
F:/circuit/firmware/a04/third_party/opus-1.6.1/celt/fixed_generic.h:101:19: note: in expansion of macro 'GCONST2'
  101 | #define GCONST(x) GCONST2((x),DB_SHIFT)
      |                   ^~~~~~~
F:/circuit/firmware/a04/third_party/opus-1.6.1/celt/celt_encoder.c:2142:49: note: in expansion of macro 'GCONST'
 2142 |       diff = MAX32(MIN32(diff, GCONST(.031f)), -GCONST(.031f));
      |                                                 ^~~~~~
F:/circuit/firmware/a04/third_party/opus-1.6.1/celt/fixed_generic.h:98:40: warning: implicit conversion from 'float' to 'double' to match other operand of binary expression [-Wdouble-promotion]
   98 | #define GCONST2(x,bits) ((celt_glog)(.5+(x)*(((celt_glog)1)<<(bits))))
      |                                        ^
F:/circuit/firmware/a04/third_party/opus-1.6.1/celt/arch.h:103:34: note: in definition of macro 'MAX32'
  103 | #define MAX32(a,b) ((a) > (b) ? (a) : (b))   /**< Maximum 32-bit value.   */
      |                                  ^
F:/circuit/firmware/a04/third_party/opus-1.6.1/celt/celt_encoder.c:2142:20: note: in expansion of macro 'MIN32'
 2142 |       diff = MAX32(MIN32(diff, GCONST(.031f)), -GCONST(.031f));
      |                    ^~~~~
F:/circuit/firmware/a04/third_party/opus-1.6.1/celt/fixed_generic.h:101:19: note: in expansion of macro 'GCONST2'
  101 | #define GCONST(x) GCONST2((x),DB_SHIFT)
      |                   ^~~~~~~
F:/circuit/firmware/a04/third_party/opus-1.6.1/celt/celt_encoder.c:2142:32: note: in expansion of macro 'GCONST'
 2142 |       diff = MAX32(MIN32(diff, GCONST(.031f)), -GCONST(.031f));
      |                                ^~~~~~
F:/circuit/firmware/a04/third_party/opus-1.6.1/celt/fixed_generic.h:98:40: warning: implicit conversion from 'float' to 'double' to match other operand of binary expression [-Wdouble-promotion]
   98 | #define GCONST2(x,bits) ((celt_glog)(.5+(x)*(((celt_glog)1)<<(bits))))
      |                                        ^
F:/circuit/firmware/a04/third_party/opus-1.6.1/celt/arch.h:103:34: note: in definition of macro 'MAX32'
  103 | #define MAX32(a,b) ((a) > (b) ? (a) : (b))   /**< Maximum 32-bit value.   */
      |                                  ^
F:/circuit/firmware/a04/third_party/opus-1.6.1/celt/celt_encoder.c:2142:20: note: in expansion of macro 'MIN32'
 2142 |       diff = MAX32(MIN32(diff, GCONST(.031f)), -GCONST(.031f));
      |                    ^~~~~
F:/circuit/firmware/a04/third_party/opus-1.6.1/celt/fixed_generic.h:101:19: note: in expansion of macro 'GCONST2'
  101 | #define GCONST(x) GCONST2((x),DB_SHIFT)
      |                   ^~~~~~~
F:/circuit/firmware/a04/third_party/opus-1.6.1/celt/celt_encoder.c:2142:32: note: in expansion of macro 'GCONST'
 2142 |       diff = MAX32(MIN32(diff, GCONST(.031f)), -GCONST(.031f));
      |                                ^~~~~~
F:/circuit/firmware/a04/third_party/opus-1.6.1/celt/fixed_generic.h:98:40: warning: implicit conversion from 'float' to 'double' to match other operand of binary expression [-Wdouble-promotion]
   98 | #define GCONST2(x,bits) ((celt_glog)(.5+(x)*(((celt_glog)1)<<(bits))))
      |                                        ^
F:/circuit/firmware/a04/third_party/opus-1.6.1/celt/arch.h:103:40: note: in definition of macro 'MAX32'
  103 | #define MAX32(a,b) ((a) > (b) ? (a) : (b))   /**< Maximum 32-bit value.   */
      |                                        ^
F:/circuit/firmware/a04/third_party/opus-1.6.1/celt/fixed_generic.h:101:19: note: in expansion of macro 'GCONST2'
  101 | #define GCONST(x) GCONST2((x),DB_SHIFT)
      |                   ^~~~~~~
F:/circuit/firmware/a04/third_party/opus-1.6.1/celt/celt_encoder.c:2142:49: note: in expansion of macro 'GCONST'
 2142 |       diff = MAX32(MIN32(diff, GCONST(.031f)), -GCONST(.031f));
      |                                                 ^~~~~~
F:/circuit/firmware/a04/third_party/opus-1.6.1/celt/fixed_generic.h:98:40: warning: implicit conversion from 'float' to 'double' to match other operand of binary expression [-Wdouble-promotion]
   98 | #define GCONST2(x,bits) ((celt_glog)(.5+(x)*(((celt_glog)1)<<(bits))))
      |                                        ^
F:/circuit/firmware/a04/third_party/opus-1.6.1/celt/arch.h:102:28: note: in definition of macro 'MIN32'
  102 | #define MIN32(a,b) ((a) < (b) ? (a) : (b))   /**< Minimum 32-bit value.   */
      |                            ^
F:/circuit/firmware/a04/third_party/opus-1.6.1/celt/celt_encoder.c:2155:19: note: in expansion of macro 'MING'
 2155 |          unmask = MING(unmask, GCONST(.0f));
      |                   ^~~~
F:/circuit/firmware/a04/third_party/opus-1.6.1/celt/fixed_generic.h:101:19: note: in expansion of macro 'GCONST2'
  101 | #define GCONST(x) GCONST2((x),DB_SHIFT)
      |                   ^~~~~~~
F:/circuit/firmware/a04/third_party/opus-1.6.1/celt/celt_encoder.c:2155:32: note: in expansion of macro 'GCONST'
 2155 |          unmask = MING(unmask, GCONST(.0f));
      |                                ^~~~~~
F:/circuit/firmware/a04/third_party/opus-1.6.1/celt/fixed_generic.h:98:40: warning: implicit conversion from 'float' to 'double' to match other operand of binary expression [-Wdouble-promotion]
   98 | #define GCONST2(x,bits) ((celt_glog)(.5+(x)*(((celt_glog)1)<<(bits))))
      |                                        ^
F:/circuit/firmware/a04/third_party/opus-1.6.1/celt/arch.h:102:40: note: in definition of macro 'MIN32'
  102 | #define MIN32(a,b) ((a) < (b) ? (a) : (b))   /**< Minimum 32-bit value.   */
      |                                        ^
F:/circuit/firmware/a04/third_party/opus-1.6.1/celt/celt_encoder.c:2155:19: note: in expansion of macro 'MING'
 2155 |          unmask = MING(unmask, GCONST(.0f));
      |                   ^~~~
F:/circuit/firmware/a04/third_party/opus-1.6.1/celt/fixed_generic.h:101:19: note: in expansion of macro 'GCONST2'
  101 | #define GCONST(x) GCONST2((x),DB_SHIFT)
      |                   ^~~~~~~
F:/circuit/firmware/a04/third_party/opus-1.6.1/celt/celt_encoder.c:2155:32: note: in expansion of macro 'GCONST'
 2155 |          unmask = MING(unmask, GCONST(.0f));
      |                                ^~~~~~
F:/circuit/firmware/a04/third_party/opus-1.6.1/celt/fixed_generic.h:98:40: warning: implicit conversion from 'float' to 'double' to match other operand of binary expression [-Wdouble-promotion]
   98 | #define GCONST2(x,bits) ((celt_glog)(.5+(x)*(((celt_glog)1)<<(bits))))
      |                                        ^
F:/circuit/firmware/a04/third_party/opus-1.6.1/celt/fixed_generic.h:101:19: note: in expansion of macro 'GCONST2'
  101 | #define GCONST(x) GCONST2((x),DB_SHIFT)
      |                   ^~~~~~~
F:/circuit/firmware/a04/third_party/opus-1.6.1/celt/celt_encoder.c:2157:23: note: in expansion of macro 'GCONST'
 2157 |          if (unmask > GCONST(.25f))
      |                       ^~~~~~
F:/circuit/firmware/a04/third_party/opus-1.6.1/celt/fixed_generic.h:98:40: warning: implicit conversion from 'float' to 'double' to match other operand of binary expression [-Wdouble-promotion]
   98 | #define GCONST2(x,bits) ((celt_glog)(.5+(x)*(((celt_glog)1)<<(bits))))
      |                                        ^
F:/circuit/firmware/a04/third_party/opus-1.6.1/celt/fixed_generic.h:101:19: note: in expansion of macro 'GCONST2'
  101 | #define GCONST(x) GCONST2((x),DB_SHIFT)
      |                   ^~~~~~~
F:/circuit/firmware/a04/third_party/opus-1.6.1/celt/celt_encoder.c:2159:45: note: in expansion of macro 'GCONST'
 2159 |             surround_dynalloc[i] = unmask - GCONST(.25f);
      |                                             ^~~~~~
F:/circuit/firmware/a04/third_party/opus-1.6.1/celt/fixed_generic.h:98:40: warning: implicit conversion from 'float' to 'double' to match other operand of binary expression [-Wdouble-promotion]
   98 | #define GCONST2(x,bits) ((celt_glog)(.5+(x)*(((celt_glog)1)<<(bits))))
      |                                        ^
F:/circuit/firmware/a04/third_party/opus-1.6.1/celt/fixed_generic.h:101:19: note: in expansion of macro 'GCONST2'
  101 | #define GCONST(x) GCONST2((x),DB_SHIFT)
      |                   ^~~~~~~
F:/circuit/firmware/a04/third_party/opus-1.6.1/celt/celt_encoder.c:2167:22: note: in expansion of macro 'GCONST'
 2167 |          mask_avg += GCONST(.25f);
      |                      ^~~~~~
F:/circuit/firmware/a04/third_party/opus-1.6.1/celt/fixed_generic.h:98:40: warning: implicit conversion from 'float' to 'double' to match other operand of binary expression [-Wdouble-promotion]
   98 | #define GCONST2(x,bits) ((celt_glog)(.5+(x)*(((celt_glog)1)<<(bits))))
      |                                        ^
F:/circuit/firmware/a04/third_party/opus-1.6.1/celt/arch.h:103:28: note: in definition of macro 'MAX32'
  103 | #define MAX32(a,b) ((a) > (b) ? (a) : (b))   /**< Maximum 32-bit value.   */
      |                            ^
F:/circuit/firmware/a04/third_party/opus-1.6.1/celt/celt_encoder.c:2177:39: note: in expansion of macro 'MAXG'
 2177 |                surround_dynalloc[i] = MAXG(0, surround_dynalloc[i]-GCONST(.25f));
      |                                       ^~~~
F:/circuit/firmware/a04/third_party/opus-1.6.1/celt/fixed_generic.h:101:19: note: in expansion of macro 'GCONST2'
  101 | #define GCONST(x) GCONST2((x),DB_SHIFT)
      |                   ^~~~~~~
F:/circuit/firmware/a04/third_party/opus-1.6.1/celt/celt_encoder.c:2177:68: note: in expansion of macro 'GCONST'
 2177 |                surround_dynalloc[i] = MAXG(0, surround_dynalloc[i]-GCONST(.25f));
      |                                                                    ^~~~~~
F:/circuit/firmware/a04/third_party/opus-1.6.1/celt/fixed_generic.h:98:40: warning: implicit conversion from 'float' to 'double' to match other operand of binary expression [-Wdouble-promotion]
   98 | #define GCONST2(x,bits) ((celt_glog)(.5+(x)*(((celt_glog)1)<<(bits))))
      |                                        ^
F:/circuit/firmware/a04/third_party/opus-1.6.1/celt/arch.h:103:40: note: in definition of macro 'MAX32'
  103 | #define MAX32(a,b) ((a) > (b) ? (a) : (b))   /**< Maximum 32-bit value.   */
      |                                        ^
F:/circuit/firmware/a04/third_party/opus-1.6.1/celt/celt_encoder.c:2177:39: note: in expansion of macro 'MAXG'
 2177 |                surround_dynalloc[i] = MAXG(0, surround_dynalloc[i]-GCONST(.25f));
      |                                       ^~~~
F:/circuit/firmware/a04/third_party/opus-1.6.1/celt/fixed_generic.h:101:19: note: in expansion of macro 'GCONST2'
  101 | #define GCONST(x) GCONST2((x),DB_SHIFT)
      |                   ^~~~~~~
F:/circuit/firmware/a04/third_party/opus-1.6.1/celt/celt_encoder.c:2177:68: note: in expansion of macro 'GCONST'
 2177 |                surround_dynalloc[i] = MAXG(0, surround_dynalloc[i]-GCONST(.25f));
      |                                                                    ^~~~~~
F:/circuit/firmware/a04/third_party/opus-1.6.1/celt/fixed_generic.h:98:40: warning: implicit conversion from 'float' to 'double' to match other operand of binary expression [-Wdouble-promotion]
   98 | #define GCONST2(x,bits) ((celt_glog)(.5+(x)*(((celt_glog)1)<<(bits))))
      |                                        ^
F:/circuit/firmware/a04/third_party/opus-1.6.1/celt/fixed_generic.h:101:19: note: in expansion of macro 'GCONST2'
  101 | #define GCONST(x) GCONST2((x),DB_SHIFT)
      |                   ^~~~~~~
F:/circuit/firmware/a04/third_party/opus-1.6.1/celt/celt_encoder.c:2180:19: note: in expansion of macro 'GCONST'
 2180 |       mask_avg += GCONST(.2f);
      |                   ^~~~~~
F:/circuit/firmware/a04/third_party/opus-1.6.1/celt/fixed_generic.h:95:42: warning: implicit conversion from 'float' to 'double' to match other operand of binary expression [-Wdouble-promotion]
   95 | #define QCONST32(x,bits) ((opus_val32)(.5+(x)*(((opus_int64)1)<<(bits))))
      |                                          ^
F:/circuit/firmware/a04/third_party/opus-1.6.1/celt/celt_encoder.c:2189:25: note: in expansion of macro 'QCONST32'
 2189 |       celt_glog follow=-QCONST32(10.0f, DB_SHIFT-5);
      |                         ^~~~~~~~
F:/circuit/firmware/a04/third_party/opus-1.6.1/celt/fixed_generic.h:95:42: warning: implicit conversion from 'float' to 'double' to match other operand of binary expression [-Wdouble-promotion]
   95 | #define QCONST32(x,bits) ((opus_val32)(.5+(x)*(((opus_int64)1)<<(bits))))
      |                                          ^
F:/circuit/firmware/a04/third_party/opus-1.6.1/celt/arch.h:103:22: note: in definition of macro 'MAX32'
  103 | #define MAX32(a,b) ((a) > (b) ? (a) : (b))   /**< Maximum 32-bit value.   */
      |                      ^
F:/circuit/firmware/a04/third_party/opus-1.6.1/celt/celt_encoder.c:2194:19: note: in expansion of macro 'MAXG'
 2194 |          follow = MAXG(follow-QCONST32(1.0f, DB_SHIFT-5), SHR32(bandLogE[i],5)-offset);
      |                   ^~~~
F:/circuit/firmware/a04/third_party/opus-1.6.1/celt/celt_encoder.c:2194:31: note: in expansion of macro 'QCONST32'
 2194 |          follow = MAXG(follow-QCONST32(1.0f, DB_SHIFT-5), SHR32(bandLogE[i],5)-offset);
      |                               ^~~~~~~~
F:/circuit/firmware/a04/third_party/opus-1.6.1/celt/fixed_generic.h:95:42: warning: implicit conversion from 'float' to 'double' to match other operand of binary expression [-Wdouble-promotion]
   95 | #define QCONST32(x,bits) ((opus_val32)(.5+(x)*(((opus_int64)1)<<(bits))))
      |                                          ^
F:/circuit/firmware/a04/third_party/opus-1.6.1/celt/arch.h:103:34: note: in definition of macro 'MAX32'
  103 | #define MAX32(a,b) ((a) > (b) ? (a) : (b))   /**< Maximum 32-bit value.   */
      |                                  ^
F:/circuit/firmware/a04/third_party/opus-1.6.1/celt/celt_encoder.c:2194:19: note: in expansion of macro 'MAXG'
 2194 |          follow = MAXG(follow-QCONST32(1.0f, DB_SHIFT-5), SHR32(bandLogE[i],5)-offset);
      |                   ^~~~
F:/circuit/firmware/a04/third_party/opus-1.6.1/celt/celt_encoder.c:2194:31: note: in expansion of macro 'QCONST32'
 2194 |          follow = MAXG(follow-QCONST32(1.0f, DB_SHIFT-5), SHR32(bandLogE[i],5)-offset);
      |                               ^~~~~~~~
F:/circuit/firmware/a04/third_party/opus-1.6.1/celt/fixed_generic.h:98:40: warning: implicit conversion from 'float' to 'double' to match other operand of binary expression [-Wdouble-promotion]
   98 | #define GCONST2(x,bits) ((celt_glog)(.5+(x)*(((celt_glog)1)<<(bits))))
      |                                        ^
F:/circuit/firmware/a04/third_party/opus-1.6.1/celt/arch.h:102:22: note: in definition of macro 'MIN32'
  102 | #define MIN32(a,b) ((a) < (b) ? (a) : (b))   /**< Minimum 32-bit value.   */
      |                      ^
F:/circuit/firmware/a04/third_party/opus-1.6.1/celt/celt_encoder.c:2201:22: note: in expansion of macro 'MING'
 2201 |       temporal_vbr = MING(GCONST(3.f), MAXG(-GCONST(1.5f), temporal_vbr));
      |                      ^~~~
F:/circuit/firmware/a04/third_party/opus-1.6.1/celt/fixed_generic.h:101:19: note: in expansion of macro 'GCONST2'
  101 | #define GCONST(x) GCONST2((x),DB_SHIFT)
      |                   ^~~~~~~
F:/circuit/firmware/a04/third_party/opus-1.6.1/celt/celt_encoder.c:2201:27: note: in expansion of macro 'GCONST'
 2201 |       temporal_vbr = MING(GCONST(3.f), MAXG(-GCONST(1.5f), temporal_vbr));
      |                           ^~~~~~
F:/circuit/firmware/a04/third_party/opus-1.6.1/celt/fixed_generic.h:98:40: warning: implicit conversion from 'float' to 'double' to match other operand of binary expression [-Wdouble-promotion]
   98 | #define GCONST2(x,bits) ((celt_glog)(.5+(x)*(((celt_glog)1)<<(bits))))
      |                                        ^
F:/circuit/firmware/a04/third_party/opus-1.6.1/celt/arch.h:102:28: note: in definition of macro 'MIN32'
  102 | #define MIN32(a,b) ((a) < (b) ? (a) : (b))   /**< Minimum 32-bit value.   */
      |                            ^
F:/circuit/firmware/a04/third_party/opus-1.6.1/celt/celt_encoder.c:2201:22: note: in expansion of macro 'MING'
 2201 |       temporal_vbr = MING(GCONST(3.f), MAXG(-GCONST(1.5f), temporal_vbr));
      |                      ^~~~
F:/circuit/firmware/a04/third_party/opus-1.6.1/celt/arch.h:110:19: note: in expansion of macro 'MAX32'
  110 | #define MAXG(a,b) MAX32(a, b)
      |                   ^~~~~
F:/circuit/firmware/a04/third_party/opus-1.6.1/celt/celt_encoder.c:2201:40: note: in expansion of macro 'MAXG'
 2201 |       temporal_vbr = MING(GCONST(3.f), MAXG(-GCONST(1.5f), temporal_vbr));
      |                                        ^~~~
F:/circuit/firmware/a04/third_party/opus-1.6.1/celt/fixed_generic.h:101:19: note: in expansion of macro 'GCONST2'
  101 | #define GCONST(x) GCONST2((x),DB_SHIFT)
      |                   ^~~~~~~
F:/circuit/firmware/a04/third_party/opus-1.6.1/celt/celt_encoder.c:2201:46: note: in expansion of macro 'GCONST'
 2201 |       temporal_vbr = MING(GCONST(3.f), MAXG(-GCONST(1.5f), temporal_vbr));
      |                                              ^~~~~~
F:/circuit/firmware/a04/third_party/opus-1.6.1/celt/fixed_generic.h:98:40: warning: implicit conversion from 'float' to 'double' to match other operand of binary expression [-Wdouble-promotion]
   98 | #define GCONST2(x,bits) ((celt_glog)(.5+(x)*(((celt_glog)1)<<(bits))))
      |                                        ^
F:/circuit/firmware/a04/third_party/opus-1.6.1/celt/arch.h:102:28: note: in definition of macro 'MIN32'
  102 | #define MIN32(a,b) ((a) < (b) ? (a) : (b))   /**< Minimum 32-bit value.   */
      |                            ^
F:/circuit/firmware/a04/third_party/opus-1.6.1/celt/celt_encoder.c:2201:22: note: in expansion of macro 'MING'
 2201 |       temporal_vbr = MING(GCONST(3.f), MAXG(-GCONST(1.5f), temporal_vbr));
      |                      ^~~~
F:/circuit/firmware/a04/third_party/opus-1.6.1/celt/arch.h:110:19: note: in expansion of macro 'MAX32'
  110 | #define MAXG(a,b) MAX32(a, b)
      |                   ^~~~~
F:/circuit/firmware/a04/third_party/opus-1.6.1/celt/celt_encoder.c:2201:40: note: in expansion of macro 'MAXG'
 2201 |       temporal_vbr = MING(GCONST(3.f), MAXG(-GCONST(1.5f), temporal_vbr));
      |                                        ^~~~
F:/circuit/firmware/a04/third_party/opus-1.6.1/celt/fixed_generic.h:101:19: note: in expansion of macro 'GCONST2'
  101 | #define GCONST(x) GCONST2((x),DB_SHIFT)
      |                   ^~~~~~~
F:/circuit/firmware/a04/third_party/opus-1.6.1/celt/celt_encoder.c:2201:46: note: in expansion of macro 'GCONST'
 2201 |       temporal_vbr = MING(GCONST(3.f), MAXG(-GCONST(1.5f), temporal_vbr));
      |                                              ^~~~~~
F:/circuit/firmware/a04/third_party/opus-1.6.1/celt/fixed_generic.h:98:40: warning: implicit conversion from 'float' to 'double' to match other operand of binary expression [-Wdouble-promotion]
   98 | #define GCONST2(x,bits) ((celt_glog)(.5+(x)*(((celt_glog)1)<<(bits))))
      |                                        ^
F:/circuit/firmware/a04/third_party/opus-1.6.1/celt/arch.h:102:34: note: in definition of macro 'MIN32'
  102 | #define MIN32(a,b) ((a) < (b) ? (a) : (b))   /**< Minimum 32-bit value.   */
      |                                  ^
F:/circuit/firmware/a04/third_party/opus-1.6.1/celt/celt_encoder.c:2201:22: note: in expansion of macro 'MING'
 2201 |       temporal_vbr = MING(GCONST(3.f), MAXG(-GCONST(1.5f), temporal_vbr));
      |                      ^~~~
F:/circuit/firmware/a04/third_party/opus-1.6.1/celt/fixed_generic.h:101:19: note: in expansion of macro 'GCONST2'
  101 | #define GCONST(x) GCONST2((x),DB_SHIFT)
      |                   ^~~~~~~
F:/circuit/firmware/a04/third_party/opus-1.6.1/celt/celt_encoder.c:2201:27: note: in expansion of macro 'GCONST'
 2201 |       temporal_vbr = MING(GCONST(3.f), MAXG(-GCONST(1.5f), temporal_vbr));
      |                           ^~~~~~
F:/circuit/firmware/a04/third_party/opus-1.6.1/celt/fixed_generic.h:98:40: warning: implicit conversion from 'float' to 'double' to match other operand of binary expression [-Wdouble-promotion]
   98 | #define GCONST2(x,bits) ((celt_glog)(.5+(x)*(((celt_glog)1)<<(bits))))
      |                                        ^
F:/circuit/firmware/a04/third_party/opus-1.6.1/celt/arch.h:102:40: note: in definition of macro 'MIN32'
  102 | #define MIN32(a,b) ((a) < (b) ? (a) : (b))   /**< Minimum 32-bit value.   */
      |                                        ^
F:/circuit/firmware/a04/third_party/opus-1.6.1/celt/celt_encoder.c:2201:22: note: in expansion of macro 'MING'
 2201 |       temporal_vbr = MING(GCONST(3.f), MAXG(-GCONST(1.5f), temporal_vbr));
      |                      ^~~~
F:/circuit/firmware/a04/third_party/opus-1.6.1/celt/arch.h:110:19: note: in expansion of macro 'MAX32'
  110 | #define MAXG(a,b) MAX32(a, b)
      |                   ^~~~~
F:/circuit/firmware/a04/third_party/opus-1.6.1/celt/celt_encoder.c:2201:40: note: in expansion of macro 'MAXG'
 2201 |       temporal_vbr = MING(GCONST(3.f), MAXG(-GCONST(1.5f), temporal_vbr));
      |                                        ^~~~
F:/circuit/firmware/a04/third_party/opus-1.6.1/celt/fixed_generic.h:101:19: note: in expansion of macro 'GCONST2'
  101 | #define GCONST(x) GCONST2((x),DB_SHIFT)
      |                   ^~~~~~~
F:/circuit/firmware/a04/third_party/opus-1.6.1/celt/celt_encoder.c:2201:46: note: in expansion of macro 'GCONST'
 2201 |       temporal_vbr = MING(GCONST(3.f), MAXG(-GCONST(1.5f), temporal_vbr));
      |                                              ^~~~~~
F:/circuit/firmware/a04/third_party/opus-1.6.1/celt/fixed_generic.h:98:40: warning: implicit conversion from 'float' to 'double' to match other operand of binary expression [-Wdouble-promotion]
   98 | #define GCONST2(x,bits) ((celt_glog)(.5+(x)*(((celt_glog)1)<<(bits))))
      |                                        ^
F:/circuit/firmware/a04/third_party/opus-1.6.1/celt/arch.h:102:40: note: in definition of macro 'MIN32'
  102 | #define MIN32(a,b) ((a) < (b) ? (a) : (b))   /**< Minimum 32-bit value.   */
      |                                        ^
F:/circuit/firmware/a04/third_party/opus-1.6.1/celt/celt_encoder.c:2201:22: note: in expansion of macro 'MING'
 2201 |       temporal_vbr = MING(GCONST(3.f), MAXG(-GCONST(1.5f), temporal_vbr));
      |                      ^~~~
F:/circuit/firmware/a04/third_party/opus-1.6.1/celt/arch.h:110:19: note: in expansion of macro 'MAX32'
  110 | #define MAXG(a,b) MAX32(a, b)
      |                   ^~~~~
F:/circuit/firmware/a04/third_party/opus-1.6.1/celt/celt_encoder.c:2201:40: note: in expansion of macro 'MAXG'
 2201 |       temporal_vbr = MING(GCONST(3.f), MAXG(-GCONST(1.5f), temporal_vbr));
      |                                        ^~~~
F:/circuit/firmware/a04/third_party/opus-1.6.1/celt/fixed_generic.h:101:19: note: in expansion of macro 'GCONST2'
  101 | #define GCONST(x) GCONST2((x),DB_SHIFT)
      |                   ^~~~~~~
F:/circuit/firmware/a04/third_party/opus-1.6.1/celt/celt_encoder.c:2201:46: note: in expansion of macro 'GCONST'
 2201 |       temporal_vbr = MING(GCONST(3.f), MAXG(-GCONST(1.5f), temporal_vbr));
      |                                              ^~~~~~
F:/circuit/firmware/a04/third_party/opus-1.6.1/celt/fixed_generic.h:92:42: warning: implicit conversion from 'float' to 'double' to match other operand of binary expression [-Wdouble-promotion]
   92 | #define QCONST16(x,bits) ((opus_val16)(.5+(x)*(((opus_val32)1)<<(bits))))
      |                                          ^
F:/circuit/firmware/a04/third_party/opus-1.6.1/celt/fixed_generic.h:152:34: note: in definition of macro 'ADD32'
  152 | #define ADD32(a,b) ((opus_val32)(a)+(opus_val32)(b))
      |                                  ^
F:/circuit/firmware/a04/third_party/opus-1.6.1/celt/fixed_generic.h:132:22: note: in expansion of macro 'SHL32'
  132 | #define SHL(a,shift) SHL32(a,shift)
      |                      ^~~~~
F:/circuit/firmware/a04/third_party/opus-1.6.1/celt/fixed_generic.h:57:34: note: in expansion of macro 'SHL'
   57 | #define MULT16_32_Q15(a,b) ADD32(SHL(MULT16_16((a),SHR((b),16)),1), SHR(MULT16_16SU((a),((b)&0x0000ffff)),15))
      |                                  ^~~
F:/circuit/firmware/a04/third_party/opus-1.6.1/celt/fixed_generic.h:57:38: note: in expansion of macro 'MULT16_16'
   57 | #define MULT16_32_Q15(a,b) ADD32(SHL(MULT16_16((a),SHR((b),16)),1), SHR(MULT16_16SU((a),((b)&0x0000ffff)),15))
      |                                      ^~~~~~~~~
F:/circuit/firmware/a04/third_party/opus-1.6.1/celt/celt_encoder.c:2202:23: note: in expansion of macro 'MULT16_32_Q15'
 2202 |       st->spec_avg += MULT16_32_Q15(QCONST16(.02f, 15), temporal_vbr);
      |                       ^~~~~~~~~~~~~
F:/circuit/firmware/a04/third_party/opus-1.6.1/celt/celt_encoder.c:2202:37: note: in expansion of macro 'QCONST16'
 2202 |       st->spec_avg += MULT16_32_Q15(QCONST16(.02f, 15), temporal_vbr);
      |                                     ^~~~~~~~
F:/circuit/firmware/a04/third_party/opus-1.6.1/celt/fixed_generic.h:92:42: warning: implicit conversion from 'float' to 'double' to match other operand of binary expression [-Wdouble-promotion]
   92 | #define QCONST16(x,bits) ((opus_val16)(.5+(x)*(((opus_val32)1)<<(bits))))
      |                                          ^
F:/circuit/firmware/a04/third_party/opus-1.6.1/celt/fixed_generic.h:152:50: note: in definition of macro 'ADD32'
  152 | #define ADD32(a,b) ((opus_val32)(a)+(opus_val32)(b))
      |                                                  ^
F:/circuit/firmware/a04/third_party/opus-1.6.1/celt/fixed_generic.h:57:69: note: in expansion of macro 'SHR'
   57 | #define MULT16_32_Q15(a,b) ADD32(SHL(MULT16_16((a),SHR((b),16)),1), SHR(MULT16_16SU((a),((b)&0x0000ffff)),15))
      |                                                                     ^~~
F:/circuit/firmware/a04/third_party/opus-1.6.1/celt/fixed_generic.h:57:73: note: in expansion of macro 'MULT16_16SU'
   57 | #define MULT16_32_Q15(a,b) ADD32(SHL(MULT16_16((a),SHR((b),16)),1), SHR(MULT16_16SU((a),((b)&0x0000ffff)),15))
      |                                                                         ^~~~~~~~~~~
F:/circuit/firmware/a04/third_party/opus-1.6.1/celt/celt_encoder.c:2202:23: note: in expansion of macro 'MULT16_32_Q15'
 2202 |       st->spec_avg += MULT16_32_Q15(QCONST16(.02f, 15), temporal_vbr);
      |                       ^~~~~~~~~~~~~
F:/circuit/firmware/a04/third_party/opus-1.6.1/celt/celt_encoder.c:2202:37: note: in expansion of macro 'QCONST16'
 2202 |       st->spec_avg += MULT16_32_Q15(QCONST16(.02f, 15), temporal_vbr);
      |                                     ^~~~~~~~
F:/circuit/firmware/a04/third_party/opus-1.6.1/celt/fixed_generic.h:92:42: warning: implicit conversion from 'float' to 'double' to match other operand of binary expression [-Wdouble-promotion]
   92 | #define QCONST16(x,bits) ((opus_val16)(.5+(x)*(((opus_val32)1)<<(bits))))
      |                                          ^
F:/circuit/firmware/a04/third_party/opus-1.6.1/celt/celt_encoder.c:2230:24: note: in expansion of macro 'QCONST16'
 2230 |          tf_estimate = QCONST16(.2f,14);
      |                        ^~~~~~~~
F:/circuit/firmware/a04/third_party/opus-1.6.1/celt/fixed_generic.h:95:42: warning: implicit conversion from 'float' to 'double' to match other operand of binary expression [-Wdouble-promotion]
   95 | #define QCONST32(x,bits) ((opus_val32)(.5+(x)*(((opus_int64)1)<<(bits))))
      |                                          ^
F:/circuit/firmware/a04/third_party/opus-1.6.1/celt/celt_encoder.c:2242:107: note: in expansion of macro 'QCONST32'
 2242 |    enable_tf_analysis = effectiveBytes>=15*C && !hybrid && st->complexity>=2 && !st->lfe && toneishness < QCONST32(.98f, 29);
      |                                                                                                           ^~~~~~~~
F:/circuit/firmware/a04/third_party/opus-1.6.1/celt/fixed_generic.h:98:40: warning: implicit conversion from 'float' to 'double' to match other operand of binary expression [-Wdouble-promotion]
   98 | #define GCONST2(x,bits) ((celt_glog)(.5+(x)*(((celt_glog)1)<<(bits))))
      |                                        ^
F:/circuit/firmware/a04/third_party/opus-1.6.1/celt/fixed_generic.h:101:19: note: in expansion of macro 'GCONST2'
  101 | #define GCONST(x) GCONST2((x),DB_SHIFT)
      |                   ^~~~~~~
F:/circuit/firmware/a04/third_party/opus-1.6.1/celt/celt_encoder.c:2289:77: note: in expansion of macro 'GCONST'
 2289 |          if (ABS32(SUB32(bandLogE[i+c*nbEBands], oldBandE[i+c*nbEBands])) < GCONST(2.f))
      |                                                                             ^~~~~~
F:/circuit/firmware/a04/third_party/opus-1.6.1/celt/fixed_generic.h:92:42: warning: implicit conversion from 'float' to 'double' to match other operand of binary expression [-Wdouble-promotion]
   92 | #define QCONST16(x,bits) ((opus_val16)(.5+(x)*(((opus_val32)1)<<(bits))))
      |                                          ^
F:/circuit/firmware/a04/third_party/opus-1.6.1/celt/fixed_generic.h:152:34: note: in definition of macro 'ADD32'
  152 | #define ADD32(a,b) ((opus_val32)(a)+(opus_val32)(b))
      |                                  ^
F:/circuit/firmware/a04/third_party/opus-1.6.1/celt/fixed_generic.h:132:22: note: in expansion of macro 'SHL32'
  132 | #define SHL(a,shift) SHL32(a,shift)
      |                      ^~~~~
F:/circuit/firmware/a04/third_party/opus-1.6.1/celt/fixed_generic.h:57:34: note: in expansion of macro 'SHL'
   57 | #define MULT16_32_Q15(a,b) ADD32(SHL(MULT16_16((a),SHR((b),16)),1), SHR(MULT16_16SU((a),((b)&0x0000ffff)),15))
      |                                  ^~~
F:/circuit/firmware/a04/third_party/opus-1.6.1/celt/fixed_generic.h:57:38: note: in expansion of macro 'MULT16_16'
   57 | #define MULT16_32_Q15(a,b) ADD32(SHL(MULT16_16((a),SHR((b),16)),1), SHR(MULT16_16SU((a),((b)&0x0000ffff)),15))
      |                                      ^~~~~~~~~
F:/circuit/firmware/a04/third_party/opus-1.6.1/celt/celt_encoder.c:2291:39: note: in expansion of macro 'MULT16_32_Q15'
 2291 |             bandLogE[i+c*nbEBands] -= MULT16_32_Q15(QCONST16(0.25f, 15), energyError[i+c*nbEBands]);
      |                                       ^~~~~~~~~~~~~
F:/circuit/firmware/a04/third_party/opus-1.6.1/celt/celt_encoder.c:2291:53: note: in expansion of macro 'QCONST16'
 2291 |             bandLogE[i+c*nbEBands] -= MULT16_32_Q15(QCONST16(0.25f, 15), energyError[i+c*nbEBands]);
      |                                                     ^~~~~~~~
F:/circuit/firmware/a04/third_party/opus-1.6.1/celt/fixed_generic.h:92:42: warning: implicit conversion from 'float' to 'double' to match other operand of binary expression [-Wdouble-promotion]
   92 | #define QCONST16(x,bits) ((opus_val16)(.5+(x)*(((opus_val32)1)<<(bits))))
      |                                          ^
F:/circuit/firmware/a04/third_party/opus-1.6.1/celt/fixed_generic.h:152:50: note: in definition of macro 'ADD32'
  152 | #define ADD32(a,b) ((opus_val32)(a)+(opus_val32)(b))
      |                                                  ^
F:/circuit/firmware/a04/third_party/opus-1.6.1/celt/fixed_generic.h:57:69: note: in expansion of macro 'SHR'
   57 | #define MULT16_32_Q15(a,b) ADD32(SHL(MULT16_16((a),SHR((b),16)),1), SHR(MULT16_16SU((a),((b)&0x0000ffff)),15))
      |                                                                     ^~~
F:/circuit/firmware/a04/third_party/opus-1.6.1/celt/fixed_generic.h:57:73: note: in expansion of macro 'MULT16_16SU'
   57 | #define MULT16_32_Q15(a,b) ADD32(SHL(MULT16_16((a),SHR((b),16)),1), SHR(MULT16_16SU((a),((b)&0x0000ffff)),15))
      |                                                                         ^~~~~~~~~~~
F:/circuit/firmware/a04/third_party/opus-1.6.1/celt/celt_encoder.c:2291:39: note: in expansion of macro 'MULT16_32_Q15'
 2291 |             bandLogE[i+c*nbEBands] -= MULT16_32_Q15(QCONST16(0.25f, 15), energyError[i+c*nbEBands]);
      |                                       ^~~~~~~~~~~~~
F:/circuit/firmware/a04/third_party/opus-1.6.1/celt/celt_encoder.c:2291:53: note: in expansion of macro 'QCONST16'
 2291 |             bandLogE[i+c*nbEBands] -= MULT16_32_Q15(QCONST16(0.25f, 15), energyError[i+c*nbEBands]);
      |                                                     ^~~~~~~~
F:/circuit/firmware/a04/third_party/opus-1.6.1/celt/fixed_generic.h:92:42: warning: implicit conversion from 'float' to 'double' to match other operand of binary expression [-Wdouble-promotion]
   92 | #define QCONST16(x,bits) ((opus_val16)(.5+(x)*(((opus_val32)1)<<(bits))))
      |                                          ^
F:/circuit/firmware/a04/third_party/opus-1.6.1/celt/fixed_generic.h:131:24: note: in definition of macro 'SHR'
  131 | #define SHR(a,shift) ((a) >> (shift))
      |                        ^
F:/circuit/firmware/a04/third_party/opus-1.6.1/celt/fixed_generic.h:192:33: note: in expansion of macro 'MULT16_16'
  192 | #define MULT16_16_Q14(a,b) (SHR(MULT16_16((a),(b)),14))
      |                                 ^~~~~~~~~
F:/circuit/firmware/a04/third_party/opus-1.6.1/celt/celt_encoder.c:2470:31: note: in expansion of macro 'MULT16_16_Q14'
 2470 |         target += (opus_int32)MULT16_16_Q14(tf_estimate-QCONST16(.25f,14), (50<<BITRES));
      |                               ^~~~~~~~~~~~~
F:/circuit/firmware/a04/third_party/opus-1.6.1/celt/celt_encoder.c:2470:57: note: in expansion of macro 'QCONST16'
 2470 |         target += (opus_int32)MULT16_16_Q14(tf_estimate-QCONST16(.25f,14), (50<<BITRES));
      |                                                         ^~~~~~~~
F:/circuit/firmware/a04/third_party/opus-1.6.1/celt/fixed_generic.h:92:42: warning: implicit conversion from 'float' to 'double' to match other operand of binary expression [-Wdouble-promotion]
   92 | #define QCONST16(x,bits) ((opus_val16)(.5+(x)*(((opus_val32)1)<<(bits))))
      |                                          ^
F:/circuit/firmware/a04/third_party/opus-1.6.1/celt/celt_encoder.c:2473:27: note: in expansion of macro 'QCONST16'
 2473 |         if (tf_estimate > QCONST16(.7f,14))
      |                           ^~~~~~~~
F:/circuit/firmware/a04/third_party/opus-1.6.1/celt/fixed_generic.h:92:42: warning: implicit conversion from 'float' to 'double' to match other operand of binary expression [-Wdouble-promotion]
   92 | #define QCONST16(x,bits) ((opus_val16)(.5+(x)*(((opus_val32)1)<<(bits))))
      |                                          ^
F:/circuit/firmware/a04/third_party/opus-1.6.1/celt/celt_encoder.c:2506:17: note: in expansion of macro 'QCONST16'
 2506 |         alpha = QCONST16(.001f,15);
      |                 ^~~~~~~~
F:/circuit/firmware/a04/third_party/opus-1.6.1/celt/fixed_generic.h:98:40: warning: implicit conversion from 'float' to 'double' to match other operand of binary expression [-Wdouble-promotion]
   98 | #define GCONST2(x,bits) ((celt_glog)(.5+(x)*(((celt_glog)1)<<(bits))))
      |                                        ^
F:/circuit/firmware/a04/third_party/opus-1.6.1/celt/arch.h:103:22: note: in definition of macro 'MAX32'
  103 | #define MAX32(a,b) ((a) > (b) ? (a) : (b))   /**< Maximum 32-bit value.   */
      |                      ^
F:/circuit/firmware/a04/third_party/opus-1.6.1/celt/celt_encoder.c:2711:38: note: in expansion of macro 'MAXG'
 2711 |          energyError[i+c*nbEBands] = MAXG(-GCONST(0.5f), MING(GCONST(0.5f), error[i+c*nbEBands]));
      |                                      ^~~~
F:/circuit/firmware/a04/third_party/opus-1.6.1/celt/fixed_generic.h:101:19: note: in expansion of macro 'GCONST2'
  101 | #define GCONST(x) GCONST2((x),DB_SHIFT)
      |                   ^~~~~~~
F:/circuit/firmware/a04/third_party/opus-1.6.1/celt/celt_encoder.c:2711:44: note: in expansion of macro 'GCONST'
 2711 |          energyError[i+c*nbEBands] = MAXG(-GCONST(0.5f), MING(GCONST(0.5f), error[i+c*nbEBands]));
      |                                            ^~~~~~
F:/circuit/firmware/a04/third_party/opus-1.6.1/celt/fixed_generic.h:98:40: warning: implicit conversion from 'float' to 'double' to match other operand of binary expression [-Wdouble-promotion]
   98 | #define GCONST2(x,bits) ((celt_glog)(.5+(x)*(((celt_glog)1)<<(bits))))
      |                                        ^
F:/circuit/firmware/a04/third_party/opus-1.6.1/celt/arch.h:103:28: note: in definition of macro 'MAX32'
  103 | #define MAX32(a,b) ((a) > (b) ? (a) : (b))   /**< Maximum 32-bit value.   */
      |                            ^
F:/circuit/firmware/a04/third_party/opus-1.6.1/celt/celt_encoder.c:2711:38: note: in expansion of macro 'MAXG'
 2711 |          energyError[i+c*nbEBands] = MAXG(-GCONST(0.5f), MING(GCONST(0.5f), error[i+c*nbEBands]));
      |                                      ^~~~
F:/circuit/firmware/a04/third_party/opus-1.6.1/celt/arch.h:111:19: note: in expansion of macro 'MIN32'
  111 | #define MING(a,b) MIN32(a, b)
      |                   ^~~~~
F:/circuit/firmware/a04/third_party/opus-1.6.1/celt/celt_encoder.c:2711:58: note: in expansion of macro 'MING'
 2711 |          energyError[i+c*nbEBands] = MAXG(-GCONST(0.5f), MING(GCONST(0.5f), error[i+c*nbEBands]));
      |                                                          ^~~~
F:/circuit/firmware/a04/third_party/opus-1.6.1/celt/fixed_generic.h:101:19: note: in expansion of macro 'GCONST2'
  101 | #define GCONST(x) GCONST2((x),DB_SHIFT)
      |                   ^~~~~~~
F:/circuit/firmware/a04/third_party/opus-1.6.1/celt/celt_encoder.c:2711:63: note: in expansion of macro 'GCONST'
 2711 |          energyError[i+c*nbEBands] = MAXG(-GCONST(0.5f), MING(GCONST(0.5f), error[i+c*nbEBands]));
      |                                                               ^~~~~~
F:/circuit/firmware/a04/third_party/opus-1.6.1/celt/fixed_generic.h:98:40: warning: implicit conversion from 'float' to 'double' to match other operand of binary expression [-Wdouble-promotion]
   98 | #define GCONST2(x,bits) ((celt_glog)(.5+(x)*(((celt_glog)1)<<(bits))))
      |                                        ^
F:/circuit/firmware/a04/third_party/opus-1.6.1/celt/arch.h:103:28: note: in definition of macro 'MAX32'
  103 | #define MAX32(a,b) ((a) > (b) ? (a) : (b))   /**< Maximum 32-bit value.   */
      |                            ^
F:/circuit/firmware/a04/third_party/opus-1.6.1/celt/celt_encoder.c:2711:38: note: in expansion of macro 'MAXG'
 2711 |          energyError[i+c*nbEBands] = MAXG(-GCONST(0.5f), MING(GCONST(0.5f), error[i+c*nbEBands]));
      |                                      ^~~~
F:/circuit/firmware/a04/third_party/opus-1.6.1/celt/arch.h:111:19: note: in expansion of macro 'MIN32'
  111 | #define MING(a,b) MIN32(a, b)
      |                   ^~~~~
F:/circuit/firmware/a04/third_party/opus-1.6.1/celt/celt_encoder.c:2711:58: note: in expansion of macro 'MING'
 2711 |          energyError[i+c*nbEBands] = MAXG(-GCONST(0.5f), MING(GCONST(0.5f), error[i+c*nbEBands]));
      |                                                          ^~~~
F:/circuit/firmware/a04/third_party/opus-1.6.1/celt/fixed_generic.h:101:19: note: in expansion of macro 'GCONST2'
  101 | #define GCONST(x) GCONST2((x),DB_SHIFT)
      |                   ^~~~~~~
F:/circuit/firmware/a04/third_party/opus-1.6.1/celt/celt_encoder.c:2711:63: note: in expansion of macro 'GCONST'
 2711 |          energyError[i+c*nbEBands] = MAXG(-GCONST(0.5f), MING(GCONST(0.5f), error[i+c*nbEBands]));
      |                                                               ^~~~~~
F:/circuit/firmware/a04/third_party/opus-1.6.1/celt/fixed_generic.h:98:40: warning: implicit conversion from 'float' to 'double' to match other operand of binary expression [-Wdouble-promotion]
   98 | #define GCONST2(x,bits) ((celt_glog)(.5+(x)*(((celt_glog)1)<<(bits))))
      |                                        ^
F:/circuit/firmware/a04/third_party/opus-1.6.1/celt/arch.h:103:34: note: in definition of macro 'MAX32'
  103 | #define MAX32(a,b) ((a) > (b) ? (a) : (b))   /**< Maximum 32-bit value.   */
      |                                  ^
F:/circuit/firmware/a04/third_party/opus-1.6.1/celt/celt_encoder.c:2711:38: note: in expansion of macro 'MAXG'
 2711 |          energyError[i+c*nbEBands] = MAXG(-GCONST(0.5f), MING(GCONST(0.5f), error[i+c*nbEBands]));
      |                                      ^~~~
F:/circuit/firmware/a04/third_party/opus-1.6.1/celt/fixed_generic.h:101:19: note: in expansion of macro 'GCONST2'
  101 | #define GCONST(x) GCONST2((x),DB_SHIFT)
      |                   ^~~~~~~
F:/circuit/firmware/a04/third_party/opus-1.6.1/celt/celt_encoder.c:2711:44: note: in expansion of macro 'GCONST'
 2711 |          energyError[i+c*nbEBands] = MAXG(-GCONST(0.5f), MING(GCONST(0.5f), error[i+c*nbEBands]));
      |                                            ^~~~~~
F:/circuit/firmware/a04/third_party/opus-1.6.1/celt/fixed_generic.h:98:40: warning: implicit conversion from 'float' to 'double' to match other operand of binary expression [-Wdouble-promotion]
   98 | #define GCONST2(x,bits) ((celt_glog)(.5+(x)*(((celt_glog)1)<<(bits))))
      |                                        ^
F:/circuit/firmware/a04/third_party/opus-1.6.1/celt/arch.h:103:40: note: in definition of macro 'MAX32'
  103 | #define MAX32(a,b) ((a) > (b) ? (a) : (b))   /**< Maximum 32-bit value.   */
      |                                        ^
F:/circuit/firmware/a04/third_party/opus-1.6.1/celt/celt_encoder.c:2711:38: note: in expansion of macro 'MAXG'
 2711 |          energyError[i+c*nbEBands] = MAXG(-GCONST(0.5f), MING(GCONST(0.5f), error[i+c*nbEBands]));
      |                                      ^~~~
F:/circuit/firmware/a04/third_party/opus-1.6.1/celt/arch.h:111:19: note: in expansion of macro 'MIN32'
  111 | #define MING(a,b) MIN32(a, b)
      |                   ^~~~~
F:/circuit/firmware/a04/third_party/opus-1.6.1/celt/celt_encoder.c:2711:58: note: in expansion of macro 'MING'
 2711 |          energyError[i+c*nbEBands] = MAXG(-GCONST(0.5f), MING(GCONST(0.5f), error[i+c*nbEBands]));
      |                                                          ^~~~
F:/circuit/firmware/a04/third_party/opus-1.6.1/celt/fixed_generic.h:101:19: note: in expansion of macro 'GCONST2'
  101 | #define GCONST(x) GCONST2((x),DB_SHIFT)
      |                   ^~~~~~~
F:/circuit/firmware/a04/third_party/opus-1.6.1/celt/celt_encoder.c:2711:63: note: in expansion of macro 'GCONST'
 2711 |          energyError[i+c*nbEBands] = MAXG(-GCONST(0.5f), MING(GCONST(0.5f), error[i+c*nbEBands]));
      |                                                               ^~~~~~
F:/circuit/firmware/a04/third_party/opus-1.6.1/celt/fixed_generic.h:98:40: warning: implicit conversion from 'float' to 'double' to match other operand of binary expression [-Wdouble-promotion]
   98 | #define GCONST2(x,bits) ((celt_glog)(.5+(x)*(((celt_glog)1)<<(bits))))
      |                                        ^
F:/circuit/firmware/a04/third_party/opus-1.6.1/celt/arch.h:103:40: note: in definition of macro 'MAX32'
  103 | #define MAX32(a,b) ((a) > (b) ? (a) : (b))   /**< Maximum 32-bit value.   */
      |                                        ^
F:/circuit/firmware/a04/third_party/opus-1.6.1/celt/celt_encoder.c:2711:38: note: in expansion of macro 'MAXG'
 2711 |          energyError[i+c*nbEBands] = MAXG(-GCONST(0.5f), MING(GCONST(0.5f), error[i+c*nbEBands]));
      |                                      ^~~~
F:/circuit/firmware/a04/third_party/opus-1.6.1/celt/arch.h:111:19: note: in expansion of macro 'MIN32'
  111 | #define MING(a,b) MIN32(a, b)
      |                   ^~~~~
F:/circuit/firmware/a04/third_party/opus-1.6.1/celt/celt_encoder.c:2711:58: note: in expansion of macro 'MING'
 2711 |          energyError[i+c*nbEBands] = MAXG(-GCONST(0.5f), MING(GCONST(0.5f), error[i+c*nbEBands]));
      |                                                          ^~~~
F:/circuit/firmware/a04/third_party/opus-1.6.1/celt/fixed_generic.h:101:19: note: in expansion of macro 'GCONST2'
  101 | #define GCONST(x) GCONST2((x),DB_SHIFT)
      |                   ^~~~~~~
F:/circuit/firmware/a04/third_party/opus-1.6.1/celt/celt_encoder.c:2711:63: note: in expansion of macro 'GCONST'
 2711 |          energyError[i+c*nbEBands] = MAXG(-GCONST(0.5f), MING(GCONST(0.5f), error[i+c*nbEBands]));
      |                                                               ^~~~~~
F:/circuit/firmware/a04/third_party/opus-1.6.1/celt/fixed_generic.h:98:40: warning: implicit conversion from 'float' to 'double' to match other operand of binary expression [-Wdouble-promotion]
   98 | #define GCONST2(x,bits) ((celt_glog)(.5+(x)*(((celt_glog)1)<<(bits))))
      |                                        ^
F:/circuit/firmware/a04/third_party/opus-1.6.1/celt/fixed_generic.h:101:19: note: in expansion of macro 'GCONST2'
  101 | #define GCONST(x) GCONST2((x),DB_SHIFT)
      |                   ^~~~~~~
F:/circuit/firmware/a04/third_party/opus-1.6.1/celt/celt_encoder.c:2721:25: note: in expansion of macro 'GCONST'
 2721 |          oldBandE[i] = -GCONST(28.f);
      |                         ^~~~~~
F:/circuit/firmware/a04/third_party/opus-1.6.1/celt/fixed_generic.h:98:40: warning: implicit conversion from 'float' to 'double' to match other operand of binary expression [-Wdouble-promotion]
   98 | #define GCONST2(x,bits) ((celt_glog)(.5+(x)*(((celt_glog)1)<<(bits))))
      |                                        ^
F:/circuit/firmware/a04/third_party/opus-1.6.1/celt/fixed_generic.h:101:19: note: in expansion of macro 'GCONST2'
  101 | #define GCONST(x) GCONST2((x),DB_SHIFT)
      |                   ^~~~~~~
F:/circuit/firmware/a04/third_party/opus-1.6.1/celt/celt_encoder.c:2796:56: note: in expansion of macro 'GCONST'
 2796 |          oldLogE[c*nbEBands+i]=oldLogE2[c*nbEBands+i]=-GCONST(28.f);
      |                                                        ^~~~~~
F:/circuit/firmware/a04/third_party/opus-1.6.1/celt/fixed_generic.h:98:40: warning: implicit conversion from 'float' to 'double' to match other operand of binary expression [-Wdouble-promotion]
   98 | #define GCONST2(x,bits) ((celt_glog)(.5+(x)*(((celt_glog)1)<<(bits))))
      |                                        ^
F:/circuit/firmware/a04/third_party/opus-1.6.1/celt/fixed_generic.h:101:19: note: in expansion of macro 'GCONST2'
  101 | #define GCONST(x) GCONST2((x),DB_SHIFT)
      |                   ^~~~~~~
F:/circuit/firmware/a04/third_party/opus-1.6.1/celt/celt_encoder.c:2801:56: note: in expansion of macro 'GCONST'
 2801 |          oldLogE[c*nbEBands+i]=oldLogE2[c*nbEBands+i]=-GCONST(28.f);
      |                                                        ^~~~~~
F:/circuit/firmware/a04/third_party/opus-1.6.1/celt/celt_encoder.c: In function 'opus_custom_encoder_ctl':
F:/circuit/firmware/a04/third_party/opus-1.6.1/celt/fixed_generic.h:98:40: warning: implicit conversion from 'float' to 'double' to match other operand of binary expression [-Wdouble-promotion]
   98 | #define GCONST2(x,bits) ((celt_glog)(.5+(x)*(((celt_glog)1)<<(bits))))
      |                                        ^
F:/circuit/firmware/a04/third_party/opus-1.6.1/celt/fixed_generic.h:101:19: note: in expansion of macro 'GCONST2'
  101 | #define GCONST(x) GCONST2((x),DB_SHIFT)
      |                   ^~~~~~~
F:/circuit/firmware/a04/third_party/opus-1.6.1/celt/celt_encoder.c:3085:37: note: in expansion of macro 'GCONST'
 3085 |             oldLogE[i]=oldLogE2[i]=-GCONST(28.f);
      |                                     ^~~~~~
[460/503] Building C object opus/CMakeFiles/opus.dir/celt/entcode.c.obj
[461/503] Building C object opus/CMakeFiles/opus.dir/celt/entdec.c.obj
[462/503] Building C object opus/CMakeFiles/opus.dir/celt/entenc.c.obj
[463/503] Building C object opus/CMakeFiles/opus.dir/celt/laplace.c.obj
[464/503] Building C object opus/CMakeFiles/opus.dir/celt/kiss_fft.c.obj
In file included from F:/circuit/firmware/a04/third_party/opus-1.6.1/celt/arch.h:238,
                 from F:/circuit/firmware/a04/third_party/opus-1.6.1/celt/kiss_fft.h:34,
                 from F:/circuit/firmware/a04/third_party/opus-1.6.1/celt/_kiss_fft_guts.h:36,
                 from F:/circuit/firmware/a04/third_party/opus-1.6.1/celt/kiss_fft.c:38:
F:/circuit/firmware/a04/third_party/opus-1.6.1/celt/kiss_fft.c: In function 'kf_bfly2':
F:/circuit/firmware/a04/third_party/opus-1.6.1/celt/fixed_generic.h:95:42: warning: implicit conversion from 'float' to 'double' to match other operand of binary expression [-Wdouble-promotion]
   95 | #define QCONST32(x,bits) ((opus_val32)(.5+(x)*(((opus_int64)1)<<(bits))))
      |                                          ^
F:/circuit/firmware/a04/third_party/opus-1.6.1/celt/kiss_fft.c:78:12: note: in expansion of macro 'QCONST32'
   78 |       tw = QCONST32(0.7071067812f, COEF_SHIFT-1);
      |            ^~~~~~~~
F:/circuit/firmware/a04/third_party/opus-1.6.1/celt/kiss_fft.c: In function 'kf_bfly3':
F:/circuit/firmware/a04/third_party/opus-1.6.1/celt/fixed_generic.h:95:42: warning: implicit conversion from 'float' to 'double' to match other operand of binary expression [-Wdouble-promotion]
   95 | #define QCONST32(x,bits) ((opus_val32)(.5+(x)*(((opus_int64)1)<<(bits))))
      |                                          ^
F:/circuit/firmware/a04/third_party/opus-1.6.1/celt/kiss_fft.c:199:14: note: in expansion of macro 'QCONST32'
  199 |    epi3.i = -QCONST32(0.86602540f, COEF_SHIFT-1);
      |              ^~~~~~~~
F:/circuit/firmware/a04/third_party/opus-1.6.1/celt/kiss_fft.c: In function 'kf_bfly5':
F:/circuit/firmware/a04/third_party/opus-1.6.1/celt/fixed_generic.h:95:42: warning: implicit conversion from 'float' to 'double' to match other operand of binary expression [-Wdouble-promotion]
   95 | #define QCONST32(x,bits) ((opus_val32)(.5+(x)*(((opus_int64)1)<<(bits))))
      |                                          ^
F:/circuit/firmware/a04/third_party/opus-1.6.1/celt/kiss_fft.c:256:11: note: in expansion of macro 'QCONST32'
  256 |    ya.r = QCONST32(0.30901699f, COEF_SHIFT-1);
      |           ^~~~~~~~
F:/circuit/firmware/a04/third_party/opus-1.6.1/celt/fixed_generic.h:95:42: warning: implicit conversion from 'float' to 'double' to match other operand of binary expression [-Wdouble-promotion]
   95 | #define QCONST32(x,bits) ((opus_val32)(.5+(x)*(((opus_int64)1)<<(bits))))
      |                                          ^
F:/circuit/firmware/a04/third_party/opus-1.6.1/celt/kiss_fft.c:257:12: note: in expansion of macro 'QCONST32'
  257 |    ya.i = -QCONST32(0.95105652f, COEF_SHIFT-1);
      |            ^~~~~~~~
F:/circuit/firmware/a04/third_party/opus-1.6.1/celt/fixed_generic.h:95:42: warning: implicit conversion from 'float' to 'double' to match other operand of binary expression [-Wdouble-promotion]
   95 | #define QCONST32(x,bits) ((opus_val32)(.5+(x)*(((opus_int64)1)<<(bits))))
      |                                          ^
F:/circuit/firmware/a04/third_party/opus-1.6.1/celt/kiss_fft.c:258:12: note: in expansion of macro 'QCONST32'
  258 |    yb.r = -QCONST32(0.80901699f, COEF_SHIFT-1);
      |            ^~~~~~~~
F:/circuit/firmware/a04/third_party/opus-1.6.1/celt/fixed_generic.h:95:42: warning: implicit conversion from 'float' to 'double' to match other operand of binary expression [-Wdouble-promotion]
   95 | #define QCONST32(x,bits) ((opus_val32)(.5+(x)*(((opus_int64)1)<<(bits))))
      |                                          ^
F:/circuit/firmware/a04/third_party/opus-1.6.1/celt/kiss_fft.c:259:12: note: in expansion of macro 'QCONST32'
  259 |    yb.i = -QCONST32(0.58778525f, COEF_SHIFT-1);
      |            ^~~~~~~~
[465/503] Building C object opus/CMakeFiles/opus.dir/celt/mathops.c.obj
In file included from F:/circuit/firmware/a04/third_party/opus-1.6.1/celt/mathops.c:39:
F:/circuit/firmware/a04/third_party/opus-1.6.1/celt/float_cast.h:142:10: warning: #warning "Don't have the functions lrint() and lrintf ()." [-Wcpp]
  142 |         #warning "Don't have the functions lrint() and lrintf ()."
      |          ^~~~~~~
F:/circuit/firmware/a04/third_party/opus-1.6.1/celt/float_cast.h:143:10: warning: #warning "Replacing these functions with a standard C cast." [-Wcpp]
  143 |         #warning "Replacing these functions with a standard C cast."
      |          ^~~~~~~
[466/503] Building C object opus/CMakeFiles/opus.dir/celt/modes.c.obj
[467/503] Building C object opus/CMakeFiles/opus.dir/celt/mdct.c.obj
[468/503] Building C object opus/CMakeFiles/opus.dir/celt/pitch.c.obj
In file included from F:/circuit/firmware/a04/third_party/opus-1.6.1/celt/arch.h:238,
                 from F:/circuit/firmware/a04/third_party/opus-1.6.1/celt/ecintrin.h:32,
                 from F:/circuit/firmware/a04/third_party/opus-1.6.1/celt/entcode.h:35,
                 from F:/circuit/firmware/a04/third_party/opus-1.6.1/celt/entenc.h:31,
                 from F:/circuit/firmware/a04/third_party/opus-1.6.1/celt/celt.h:41,
                 from F:/circuit/firmware/a04/third_party/opus-1.6.1/celt/modes.h:34,
                 from F:/circuit/firmware/a04/third_party/opus-1.6.1/celt/pitch.h:37,
                 from F:/circuit/firmware/a04/third_party/opus-1.6.1/celt/pitch.c:38:
F:/circuit/firmware/a04/third_party/opus-1.6.1/celt/pitch.c: In function 'pitch_downsample':
F:/circuit/firmware/a04/third_party/opus-1.6.1/celt/fixed_generic.h:92:42: warning: implicit conversion from 'float' to 'double' to match other operand of binary expression [-Wdouble-promotion]
   92 | #define QCONST16(x,bits) ((opus_val16)(.5+(x)*(((opus_val32)1)<<(bits))))
      |                                          ^
F:/circuit/firmware/a04/third_party/opus-1.6.1/celt/pitch.c:148:20: note: in expansion of macro 'QCONST16'
  148 |    opus_val16 c1 = QCONST16(.8f,15);
      |                    ^~~~~~~~
F:/circuit/firmware/a04/third_party/opus-1.6.1/celt/fixed_generic.h:92:42: warning: implicit conversion from 'float' to 'double' to match other operand of binary expression [-Wdouble-promotion]
   92 | #define QCONST16(x,bits) ((opus_val16)(.5+(x)*(((opus_val32)1)<<(bits))))
      |                                          ^
F:/circuit/firmware/a04/third_party/opus-1.6.1/celt/fixed_generic.h:131:24: note: in definition of macro 'SHR'
  131 | #define SHR(a,shift) ((a) >> (shift))
      |                        ^
F:/circuit/firmware/a04/third_party/opus-1.6.1/celt/fixed_generic.h:193:33: note: in expansion of macro 'MULT16_16'
  193 | #define MULT16_16_Q15(a,b) (SHR(MULT16_16((a),(b)),15))
      |                                 ^~~~~~~~~
F:/circuit/firmware/a04/third_party/opus-1.6.1/celt/pitch.c:212:13: note: in expansion of macro 'MULT16_16_Q15'
  212 |       tmp = MULT16_16_Q15(QCONST16(.9f,15), tmp);
      |             ^~~~~~~~~~~~~
F:/circuit/firmware/a04/third_party/opus-1.6.1/celt/pitch.c:212:27: note: in expansion of macro 'QCONST16'
  212 |       tmp = MULT16_16_Q15(QCONST16(.9f,15), tmp);
      |                           ^~~~~~~~
F:/circuit/firmware/a04/third_party/opus-1.6.1/celt/fixed_generic.h:92:42: warning: implicit conversion from 'float' to 'double' to match other operand of binary expression [-Wdouble-promotion]
   92 | #define QCONST16(x,bits) ((opus_val16)(.5+(x)*(((opus_val32)1)<<(bits))))
      |                                          ^
F:/circuit/firmware/a04/third_party/opus-1.6.1/celt/pitch.c:216:23: note: in expansion of macro 'QCONST16'
  216 |    lpc2[0] = lpc[0] + QCONST16(.8f,SIG_SHIFT);
      |                       ^~~~~~~~
F:/circuit/firmware/a04/third_party/opus-1.6.1/celt/pitch.c: In function 'pitch_search':
F:/circuit/firmware/a04/third_party/opus-1.6.1/celt/fixed_generic.h:92:42: warning: implicit conversion from 'float' to 'double' to match other operand of binary expression [-Wdouble-promotion]
   92 | #define QCONST16(x,bits) ((opus_val16)(.5+(x)*(((opus_val32)1)<<(bits))))
      |                                          ^
F:/circuit/firmware/a04/third_party/opus-1.6.1/celt/fixed_generic.h:152:34: note: in definition of macro 'ADD32'
  152 | #define ADD32(a,b) ((opus_val32)(a)+(opus_val32)(b))
      |                                  ^
F:/circuit/firmware/a04/third_party/opus-1.6.1/celt/fixed_generic.h:132:22: note: in expansion of macro 'SHL32'
  132 | #define SHL(a,shift) SHL32(a,shift)
      |                      ^~~~~
F:/circuit/firmware/a04/third_party/opus-1.6.1/celt/fixed_generic.h:57:34: note: in expansion of macro 'SHL'
   57 | #define MULT16_32_Q15(a,b) ADD32(SHL(MULT16_16((a),SHR((b),16)),1), SHR(MULT16_16SU((a),((b)&0x0000ffff)),15))
      |                                  ^~~
F:/circuit/firmware/a04/third_party/opus-1.6.1/celt/fixed_generic.h:57:38: note: in expansion of macro 'MULT16_16'
   57 | #define MULT16_32_Q15(a,b) ADD32(SHL(MULT16_16((a),SHR((b),16)),1), SHR(MULT16_16SU((a),((b)&0x0000ffff)),15))
      |                                      ^~~~~~~~~
F:/circuit/firmware/a04/third_party/opus-1.6.1/celt/pitch.c:404:19: note: in expansion of macro 'MULT16_32_Q15'
  404 |       if ((c-a) > MULT16_32_Q15(QCONST16(.7f,15),b-a))
      |                   ^~~~~~~~~~~~~
F:/circuit/firmware/a04/third_party/opus-1.6.1/celt/pitch.c:404:33: note: in expansion of macro 'QCONST16'
  404 |       if ((c-a) > MULT16_32_Q15(QCONST16(.7f,15),b-a))
      |                                 ^~~~~~~~
F:/circuit/firmware/a04/third_party/opus-1.6.1/celt/fixed_generic.h:92:42: warning: implicit conversion from 'float' to 'double' to match other operand of binary expression [-Wdouble-promotion]
   92 | #define QCONST16(x,bits) ((opus_val16)(.5+(x)*(((opus_val32)1)<<(bits))))
      |                                          ^
F:/circuit/firmware/a04/third_party/opus-1.6.1/celt/fixed_generic.h:152:50: note: in definition of macro 'ADD32'
  152 | #define ADD32(a,b) ((opus_val32)(a)+(opus_val32)(b))
      |                                                  ^
F:/circuit/firmware/a04/third_party/opus-1.6.1/celt/fixed_generic.h:57:69: note: in expansion of macro 'SHR'
   57 | #define MULT16_32_Q15(a,b) ADD32(SHL(MULT16_16((a),SHR((b),16)),1), SHR(MULT16_16SU((a),((b)&0x0000ffff)),15))
      |                                                                     ^~~
F:/circuit/firmware/a04/third_party/opus-1.6.1/celt/fixed_generic.h:57:73: note: in expansion of macro 'MULT16_16SU'
   57 | #define MULT16_32_Q15(a,b) ADD32(SHL(MULT16_16((a),SHR((b),16)),1), SHR(MULT16_16SU((a),((b)&0x0000ffff)),15))
      |                                                                         ^~~~~~~~~~~
F:/circuit/firmware/a04/third_party/opus-1.6.1/celt/pitch.c:404:19: note: in expansion of macro 'MULT16_32_Q15'
  404 |       if ((c-a) > MULT16_32_Q15(QCONST16(.7f,15),b-a))
      |                   ^~~~~~~~~~~~~
F:/circuit/firmware/a04/third_party/opus-1.6.1/celt/pitch.c:404:33: note: in expansion of macro 'QCONST16'
  404 |       if ((c-a) > MULT16_32_Q15(QCONST16(.7f,15),b-a))
      |                                 ^~~~~~~~
F:/circuit/firmware/a04/third_party/opus-1.6.1/celt/fixed_generic.h:92:42: warning: implicit conversion from 'float' to 'double' to match other operand of binary expression [-Wdouble-promotion]
   92 | #define QCONST16(x,bits) ((opus_val16)(.5+(x)*(((opus_val32)1)<<(bits))))
      |                                          ^
F:/circuit/firmware/a04/third_party/opus-1.6.1/celt/fixed_generic.h:152:34: note: in definition of macro 'ADD32'
  152 | #define ADD32(a,b) ((opus_val32)(a)+(opus_val32)(b))
      |                                  ^
F:/circuit/firmware/a04/third_party/opus-1.6.1/celt/fixed_generic.h:132:22: note: in expansion of macro 'SHL32'
  132 | #define SHL(a,shift) SHL32(a,shift)
      |                      ^~~~~
F:/circuit/firmware/a04/third_party/opus-1.6.1/celt/fixed_generic.h:57:34: note: in expansion of macro 'SHL'
   57 | #define MULT16_32_Q15(a,b) ADD32(SHL(MULT16_16((a),SHR((b),16)),1), SHR(MULT16_16SU((a),((b)&0x0000ffff)),15))
      |                                  ^~~
F:/circuit/firmware/a04/third_party/opus-1.6.1/celt/fixed_generic.h:57:38: note: in expansion of macro 'MULT16_16'
   57 | #define MULT16_32_Q15(a,b) ADD32(SHL(MULT16_16((a),SHR((b),16)),1), SHR(MULT16_16SU((a),((b)&0x0000ffff)),15))
      |                                      ^~~~~~~~~
F:/circuit/firmware/a04/third_party/opus-1.6.1/celt/pitch.c:406:24: note: in expansion of macro 'MULT16_32_Q15'
  406 |       else if ((a-c) > MULT16_32_Q15(QCONST16(.7f,15),b-c))
      |                        ^~~~~~~~~~~~~
F:/circuit/firmware/a04/third_party/opus-1.6.1/celt/pitch.c:406:38: note: in expansion of macro 'QCONST16'
  406 |       else if ((a-c) > MULT16_32_Q15(QCONST16(.7f,15),b-c))
      |                                      ^~~~~~~~
F:/circuit/firmware/a04/third_party/opus-1.6.1/celt/fixed_generic.h:92:42: warning: implicit conversion from 'float' to 'double' to match other operand of binary expression [-Wdouble-promotion]
   92 | #define QCONST16(x,bits) ((opus_val16)(.5+(x)*(((opus_val32)1)<<(bits))))
      |                                          ^
F:/circuit/firmware/a04/third_party/opus-1.6.1/celt/fixed_generic.h:152:50: note: in definition of macro 'ADD32'
  152 | #define ADD32(a,b) ((opus_val32)(a)+(opus_val32)(b))
      |                                                  ^
F:/circuit/firmware/a04/third_party/opus-1.6.1/celt/fixed_generic.h:57:69: note: in expansion of macro 'SHR'
   57 | #define MULT16_32_Q15(a,b) ADD32(SHL(MULT16_16((a),SHR((b),16)),1), SHR(MULT16_16SU((a),((b)&0x0000ffff)),15))
      |                                                                     ^~~
F:/circuit/firmware/a04/third_party/opus-1.6.1/celt/fixed_generic.h:57:73: note: in expansion of macro 'MULT16_16SU'
   57 | #define MULT16_32_Q15(a,b) ADD32(SHL(MULT16_16((a),SHR((b),16)),1), SHR(MULT16_16SU((a),((b)&0x0000ffff)),15))
      |                                                                         ^~~~~~~~~~~
F:/circuit/firmware/a04/third_party/opus-1.6.1/celt/pitch.c:406:24: note: in expansion of macro 'MULT16_32_Q15'
  406 |       else if ((a-c) > MULT16_32_Q15(QCONST16(.7f,15),b-c))
      |                        ^~~~~~~~~~~~~
F:/circuit/firmware/a04/third_party/opus-1.6.1/celt/pitch.c:406:38: note: in expansion of macro 'QCONST16'
  406 |       else if ((a-c) > MULT16_32_Q15(QCONST16(.7f,15),b-c))
      |                                      ^~~~~~~~
F:/circuit/firmware/a04/third_party/opus-1.6.1/celt/pitch.c: In function 'remove_doubling':
F:/circuit/firmware/a04/third_party/opus-1.6.1/celt/fixed_generic.h:92:42: warning: implicit conversion from 'float' to 'double' to match other operand of binary expression [-Wdouble-promotion]
   92 | #define QCONST16(x,bits) ((opus_val16)(.5+(x)*(((opus_val32)1)<<(bits))))
      |                                          ^
F:/circuit/firmware/a04/third_party/opus-1.6.1/celt/arch.h:101:22: note: in definition of macro 'MAX16'
  101 | #define MAX16(a,b) ((a) > (b) ? (a) : (b))   /**< Maximum 16-bit value.   */
      |                      ^
F:/circuit/firmware/a04/third_party/opus-1.6.1/celt/pitch.c:523:22: note: in expansion of macro 'QCONST16'
  523 |       thresh = MAX16(QCONST16(.3f,15), MULT16_16_Q15(QCONST16(.7f,15),g0)-cont);
      |                      ^~~~~~~~
F:/circuit/firmware/a04/third_party/opus-1.6.1/celt/fixed_generic.h:92:42: warning: implicit conversion from 'float' to 'double' to match other operand of binary expression [-Wdouble-promotion]
   92 | #define QCONST16(x,bits) ((opus_val16)(.5+(x)*(((opus_val32)1)<<(bits))))
      |                                          ^
F:/circuit/firmware/a04/third_party/opus-1.6.1/celt/arch.h:101:28: note: in definition of macro 'MAX16'
  101 | #define MAX16(a,b) ((a) > (b) ? (a) : (b))   /**< Maximum 16-bit value.   */
      |                            ^
F:/circuit/firmware/a04/third_party/opus-1.6.1/celt/fixed_generic.h:193:29: note: in expansion of macro 'SHR'
  193 | #define MULT16_16_Q15(a,b) (SHR(MULT16_16((a),(b)),15))
      |                             ^~~
F:/circuit/firmware/a04/third_party/opus-1.6.1/celt/fixed_generic.h:193:33: note: in expansion of macro 'MULT16_16'
  193 | #define MULT16_16_Q15(a,b) (SHR(MULT16_16((a),(b)),15))
      |                                 ^~~~~~~~~
F:/circuit/firmware/a04/third_party/opus-1.6.1/celt/pitch.c:523:40: note: in expansion of macro 'MULT16_16_Q15'
  523 |       thresh = MAX16(QCONST16(.3f,15), MULT16_16_Q15(QCONST16(.7f,15),g0)-cont);
      |                                        ^~~~~~~~~~~~~
F:/circuit/firmware/a04/third_party/opus-1.6.1/celt/pitch.c:523:54: note: in expansion of macro 'QCONST16'
  523 |       thresh = MAX16(QCONST16(.3f,15), MULT16_16_Q15(QCONST16(.7f,15),g0)-cont);
      |                                                      ^~~~~~~~
F:/circuit/firmware/a04/third_party/opus-1.6.1/celt/fixed_generic.h:92:42: warning: implicit conversion from 'float' to 'double' to match other operand of binary expression [-Wdouble-promotion]
   92 | #define QCONST16(x,bits) ((opus_val16)(.5+(x)*(((opus_val32)1)<<(bits))))
      |                                          ^
F:/circuit/firmware/a04/third_party/opus-1.6.1/celt/arch.h:101:34: note: in definition of macro 'MAX16'
  101 | #define MAX16(a,b) ((a) > (b) ? (a) : (b))   /**< Maximum 16-bit value.   */
      |                                  ^
F:/circuit/firmware/a04/third_party/opus-1.6.1/celt/pitch.c:523:22: note: in expansion of macro 'QCONST16'
  523 |       thresh = MAX16(QCONST16(.3f,15), MULT16_16_Q15(QCONST16(.7f,15),g0)-cont);
      |                      ^~~~~~~~
F:/circuit/firmware/a04/third_party/opus-1.6.1/celt/fixed_generic.h:92:42: warning: implicit conversion from 'float' to 'double' to match other operand of binary expression [-Wdouble-promotion]
   92 | #define QCONST16(x,bits) ((opus_val16)(.5+(x)*(((opus_val32)1)<<(bits))))
      |                                          ^
F:/circuit/firmware/a04/third_party/opus-1.6.1/celt/arch.h:101:40: note: in definition of macro 'MAX16'
  101 | #define MAX16(a,b) ((a) > (b) ? (a) : (b))   /**< Maximum 16-bit value.   */
      |                                        ^
F:/circuit/firmware/a04/third_party/opus-1.6.1/celt/fixed_generic.h:193:29: note: in expansion of macro 'SHR'
  193 | #define MULT16_16_Q15(a,b) (SHR(MULT16_16((a),(b)),15))
      |                             ^~~
F:/circuit/firmware/a04/third_party/opus-1.6.1/celt/fixed_generic.h:193:33: note: in expansion of macro 'MULT16_16'
  193 | #define MULT16_16_Q15(a,b) (SHR(MULT16_16((a),(b)),15))
      |                                 ^~~~~~~~~
F:/circuit/firmware/a04/third_party/opus-1.6.1/celt/pitch.c:523:40: note: in expansion of macro 'MULT16_16_Q15'
  523 |       thresh = MAX16(QCONST16(.3f,15), MULT16_16_Q15(QCONST16(.7f,15),g0)-cont);
      |                                        ^~~~~~~~~~~~~
F:/circuit/firmware/a04/third_party/opus-1.6.1/celt/pitch.c:523:54: note: in expansion of macro 'QCONST16'
  523 |       thresh = MAX16(QCONST16(.3f,15), MULT16_16_Q15(QCONST16(.7f,15),g0)-cont);
      |                                                      ^~~~~~~~
F:/circuit/firmware/a04/third_party/opus-1.6.1/celt/fixed_generic.h:92:42: warning: implicit conversion from 'float' to 'double' to match other operand of binary expression [-Wdouble-promotion]
   92 | #define QCONST16(x,bits) ((opus_val16)(.5+(x)*(((opus_val32)1)<<(bits))))
      |                                          ^
F:/circuit/firmware/a04/third_party/opus-1.6.1/celt/arch.h:101:22: note: in definition of macro 'MAX16'
  101 | #define MAX16(a,b) ((a) > (b) ? (a) : (b))   /**< Maximum 16-bit value.   */
      |                      ^
F:/circuit/firmware/a04/third_party/opus-1.6.1/celt/pitch.c:527:25: note: in expansion of macro 'QCONST16'
  527 |          thresh = MAX16(QCONST16(.4f,15), MULT16_16_Q15(QCONST16(.85f,15),g0)-cont);
      |                         ^~~~~~~~
F:/circuit/firmware/a04/third_party/opus-1.6.1/celt/fixed_generic.h:92:42: warning: implicit conversion from 'float' to 'double' to match other operand of binary expression [-Wdouble-promotion]
   92 | #define QCONST16(x,bits) ((opus_val16)(.5+(x)*(((opus_val32)1)<<(bits))))
      |                                          ^
F:/circuit/firmware/a04/third_party/opus-1.6.1/celt/arch.h:101:28: note: in definition of macro 'MAX16'
  101 | #define MAX16(a,b) ((a) > (b) ? (a) : (b))   /**< Maximum 16-bit value.   */
      |                            ^
F:/circuit/firmware/a04/third_party/opus-1.6.1/celt/fixed_generic.h:193:29: note: in expansion of macro 'SHR'
  193 | #define MULT16_16_Q15(a,b) (SHR(MULT16_16((a),(b)),15))
      |                             ^~~
F:/circuit/firmware/a04/third_party/opus-1.6.1/celt/fixed_generic.h:193:33: note: in expansion of macro 'MULT16_16'
  193 | #define MULT16_16_Q15(a,b) (SHR(MULT16_16((a),(b)),15))
      |                                 ^~~~~~~~~
F:/circuit/firmware/a04/third_party/opus-1.6.1/celt/pitch.c:527:43: note: in expansion of macro 'MULT16_16_Q15'
  527 |          thresh = MAX16(QCONST16(.4f,15), MULT16_16_Q15(QCONST16(.85f,15),g0)-cont);
      |                                           ^~~~~~~~~~~~~
F:/circuit/firmware/a04/third_party/opus-1.6.1/celt/pitch.c:527:57: note: in expansion of macro 'QCONST16'
  527 |          thresh = MAX16(QCONST16(.4f,15), MULT16_16_Q15(QCONST16(.85f,15),g0)-cont);
      |                                                         ^~~~~~~~
F:/circuit/firmware/a04/third_party/opus-1.6.1/celt/fixed_generic.h:92:42: warning: implicit conversion from 'float' to 'double' to match other operand of binary expression [-Wdouble-promotion]
   92 | #define QCONST16(x,bits) ((opus_val16)(.5+(x)*(((opus_val32)1)<<(bits))))
      |                                          ^
F:/circuit/firmware/a04/third_party/opus-1.6.1/celt/arch.h:101:34: note: in definition of macro 'MAX16'
  101 | #define MAX16(a,b) ((a) > (b) ? (a) : (b))   /**< Maximum 16-bit value.   */
      |                                  ^
F:/circuit/firmware/a04/third_party/opus-1.6.1/celt/pitch.c:527:25: note: in expansion of macro 'QCONST16'
  527 |          thresh = MAX16(QCONST16(.4f,15), MULT16_16_Q15(QCONST16(.85f,15),g0)-cont);
      |                         ^~~~~~~~
F:/circuit/firmware/a04/third_party/opus-1.6.1/celt/fixed_generic.h:92:42: warning: implicit conversion from 'float' to 'double' to match other operand of binary expression [-Wdouble-promotion]
   92 | #define QCONST16(x,bits) ((opus_val16)(.5+(x)*(((opus_val32)1)<<(bits))))
      |                                          ^
F:/circuit/firmware/a04/third_party/opus-1.6.1/celt/arch.h:101:40: note: in definition of macro 'MAX16'
  101 | #define MAX16(a,b) ((a) > (b) ? (a) : (b))   /**< Maximum 16-bit value.   */
      |                                        ^
F:/circuit/firmware/a04/third_party/opus-1.6.1/celt/fixed_generic.h:193:29: note: in expansion of macro 'SHR'
  193 | #define MULT16_16_Q15(a,b) (SHR(MULT16_16((a),(b)),15))
      |                             ^~~
F:/circuit/firmware/a04/third_party/opus-1.6.1/celt/fixed_generic.h:193:33: note: in expansion of macro 'MULT16_16'
  193 | #define MULT16_16_Q15(a,b) (SHR(MULT16_16((a),(b)),15))
      |                                 ^~~~~~~~~
F:/circuit/firmware/a04/third_party/opus-1.6.1/celt/pitch.c:527:43: note: in expansion of macro 'MULT16_16_Q15'
  527 |          thresh = MAX16(QCONST16(.4f,15), MULT16_16_Q15(QCONST16(.85f,15),g0)-cont);
      |                                           ^~~~~~~~~~~~~
F:/circuit/firmware/a04/third_party/opus-1.6.1/celt/pitch.c:527:57: note: in expansion of macro 'QCONST16'
  527 |          thresh = MAX16(QCONST16(.4f,15), MULT16_16_Q15(QCONST16(.85f,15),g0)-cont);
      |                                                         ^~~~~~~~
F:/circuit/firmware/a04/third_party/opus-1.6.1/celt/fixed_generic.h:92:42: warning: implicit conversion from 'float' to 'double' to match other operand of binary expression [-Wdouble-promotion]
   92 | #define QCONST16(x,bits) ((opus_val16)(.5+(x)*(((opus_val32)1)<<(bits))))
      |                                          ^
F:/circuit/firmware/a04/third_party/opus-1.6.1/celt/arch.h:101:22: note: in definition of macro 'MAX16'
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
