Avinash1286/pendent/enclosure/a04/mechanism-m2-manufacturing/previews/sheet-1.png

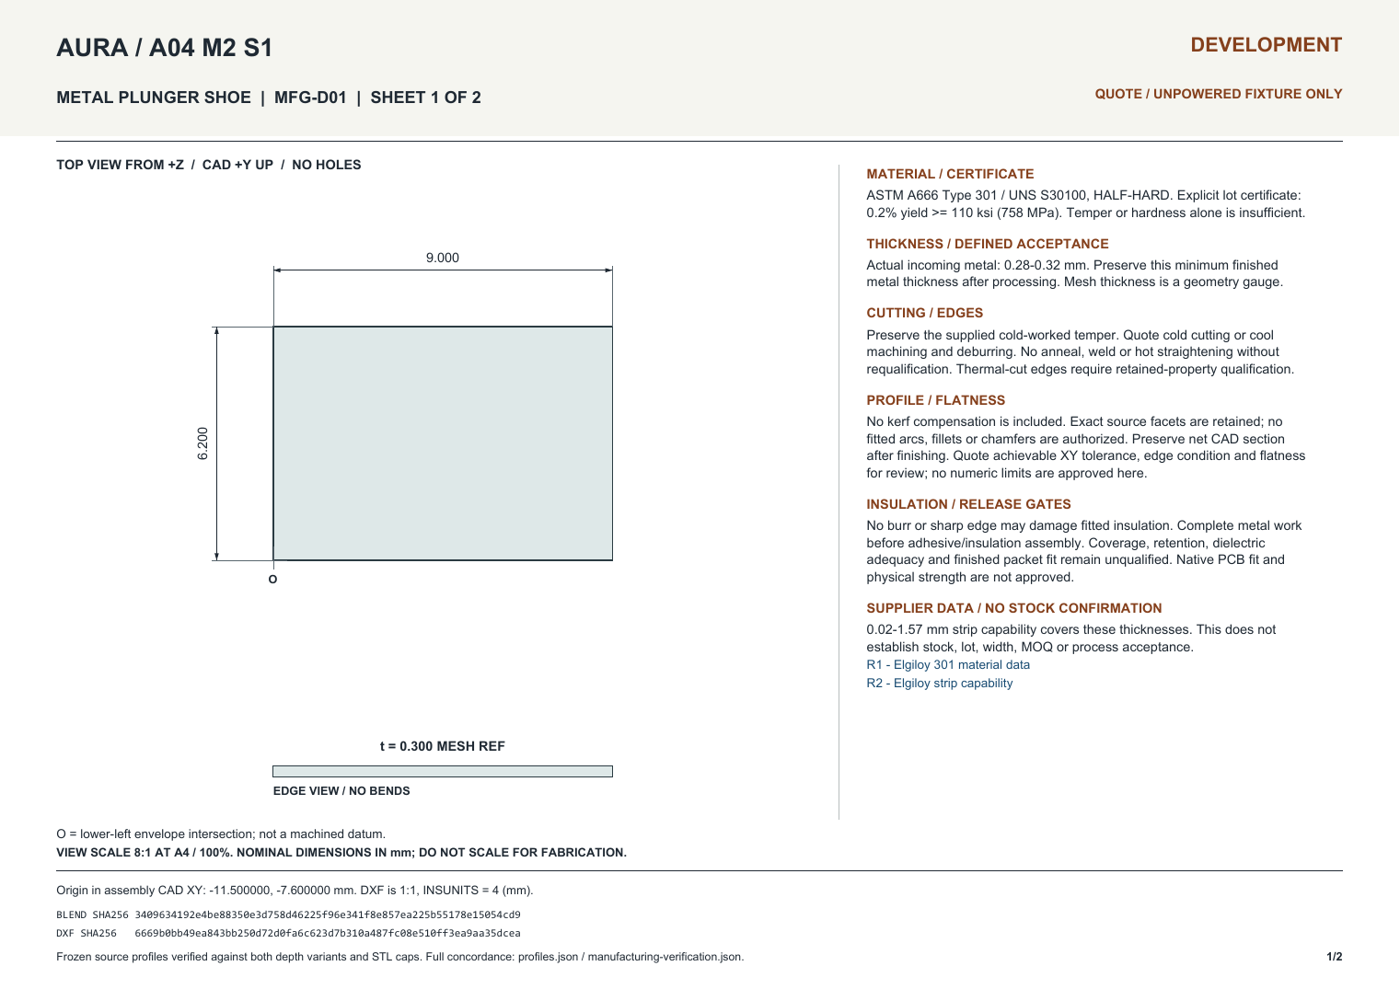
enclosure/a04/mechanism-m2-manufacturing/previews/sheet-1.png
