Avinash1286/pendent/film/aura-launch/qa/assembly-encoded.jpg

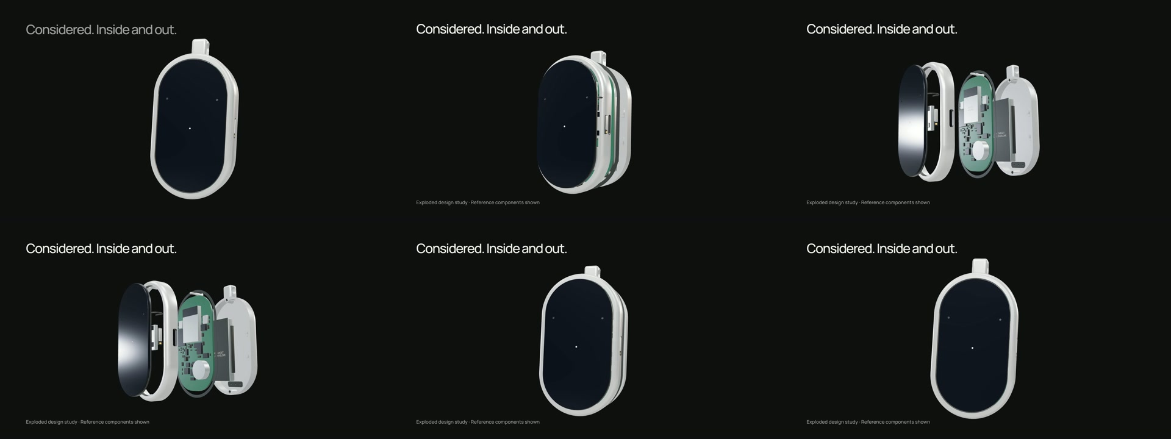
film/aura-launch/qa/assembly-encoded.jpg
