Avinash1286/pendent/film/aura-launch/qa/assembly-keyframes.jpg

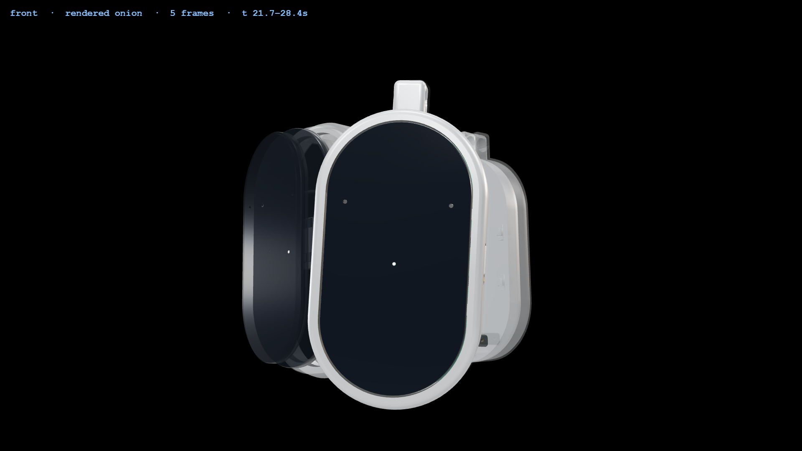
film/aura-launch/qa/assembly-keyframes.jpg
