Avinash1286/pendent/film/aura-launch/qa/assembly-snapshots-final/frame-00-at-21.7s.png

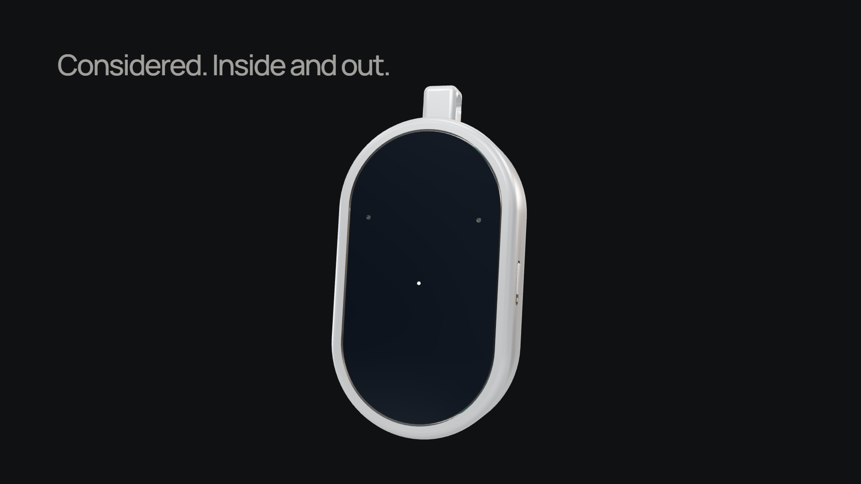
film/aura-launch/qa/assembly-snapshots-final/frame-00-at-21.7s.png
