Avinash1286/pendent/film/aura-launch/qa/assembly-snapshots-final/frame-01-at-24.2s.png

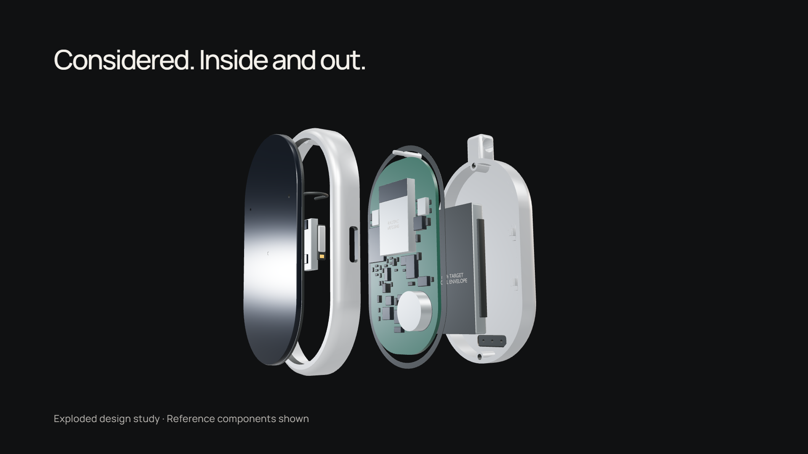
film/aura-launch/qa/assembly-snapshots-final/frame-01-at-24.2s.png
