Avinash1286/pendent/film/aura-launch/qa/assembly-snapshots/contact-sheet.jpg

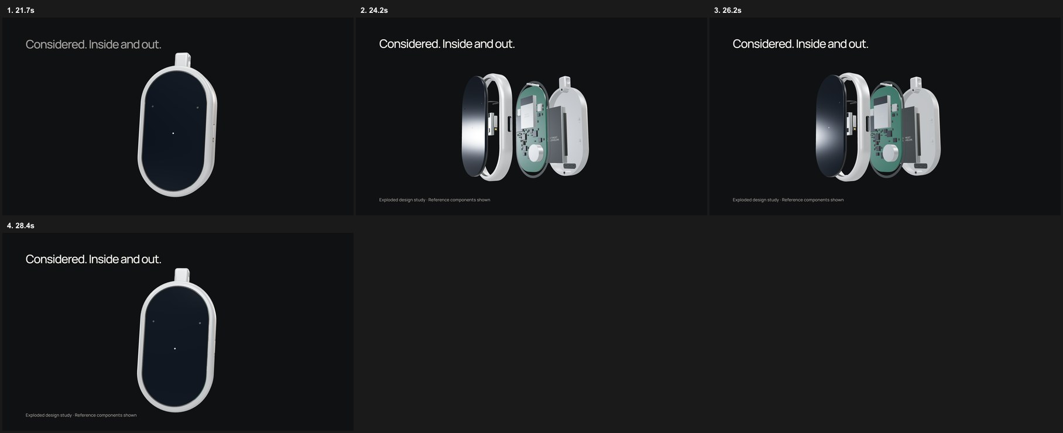
film/aura-launch/qa/assembly-snapshots/contact-sheet.jpg
