Avinash1286/pendent/hardware/output/assembly-plan.png

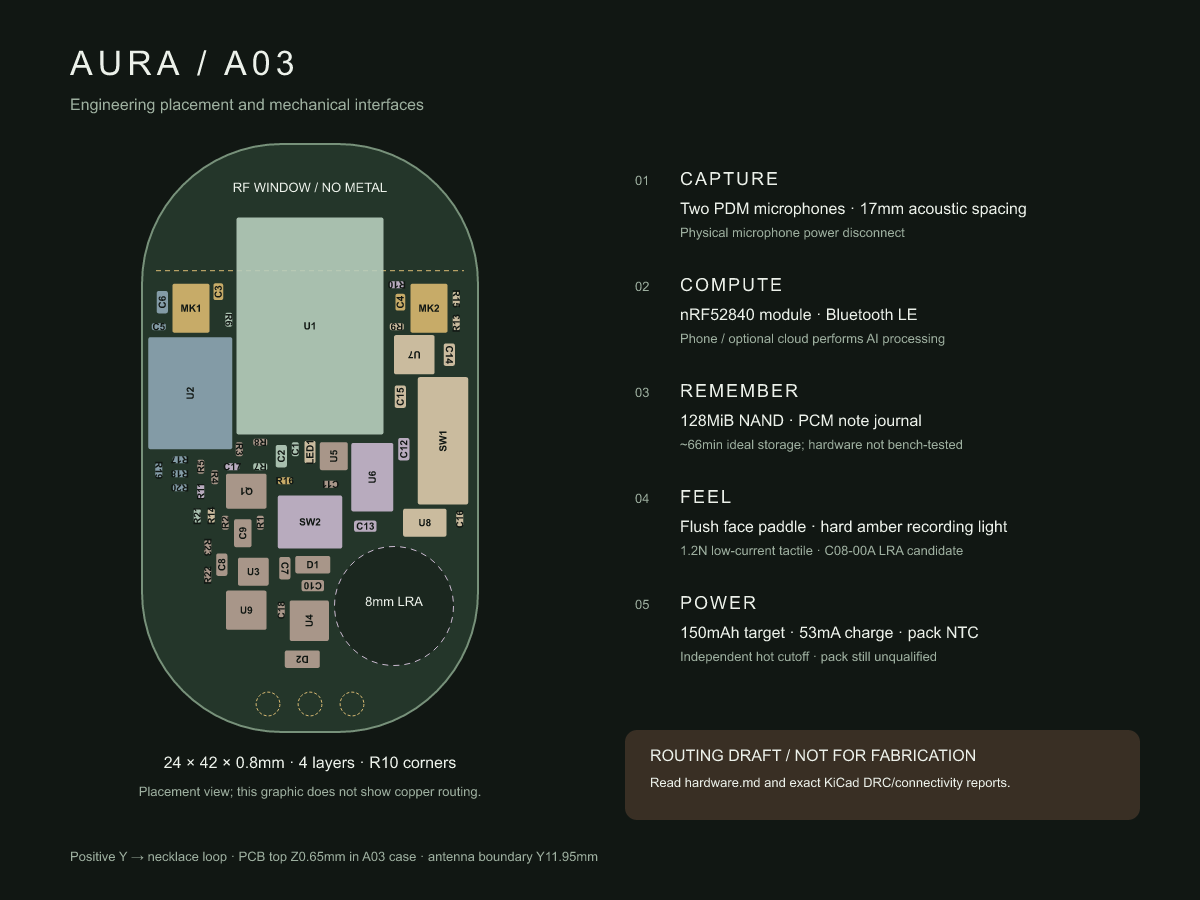
hardware/output/assembly-plan.png
