Avinash1286/pendent/film/aura-launch/qa/CONTEXT-REVISION.md

# Context positioning revision

Primary line, exactly: **Capture the context of your life.**

The 44-second emotional arc is “Life moves.” → “Keep what matters.” → “The thought. The moment.” → “On your terms.” → “Considered. Inside and out.” → “More context. New possibilities.” → the primary line. “Press to capture,” the physical mic disconnect, and “Capture starts with you” preserve deliberate user control. The notes surface and development qualifiers remain explicit.

The product images, visual language, and existing chapter motion are retained. The user's subsequent request adds an eight-second inside/assembly shot using the actual A03 GLB. The original score is extended by one harmonic passage, with its closing resolution moved to the longer end card. Copy, captions, storyboard, brief, design direction, and title metadata are updated. The preceding A03 film and source are preserved in Git commit `1569645a292b8bd147bb208ccc96d9fe8081adc5`; no new media archive is created.

The mandatory latest-CLI probe ran before composition checks: `npx hyperframes@latest upgrade --project . --check --json`. It reports Hyperframes **0.8.31** is current, with no update available. Evidence: `upgrade-context-check.json`.

Completed: the final 44-second MP4 includes the requested inside/assembly animation, revised positioning, extended original score, 15 caption cues, closing poster, and nine-frame contact sheet. Strict checks passed with zero findings; the entire MP4 decoded successfully and the encoded assembly poses and final frame were visually inspected. Full evidence: `VERIFICATION.md` and `media-final.json`.
