Avinash1286/pendent/docs/a04/protocol-v2-verification.txt

A04 protocol-v2 reference verification, 2026-09-09
Command: companion/.venv/Scripts/python.exe -m unittest discover -s tests -v
Physical BLE/Opus/mobile/cloud tests: NOT RUN
test_failed_replace_preserves_previous_note (test_download_recovery.AtomicPublicationTests.test_failed_replace_preserves_previous_note) ... ok
test_corrupted_cached_audio_is_preserved_and_rejected (test_download_recovery.RecoveryTests.test_corrupted_cached_audio_is_preserved_and_rejected) ... ok
test_crash_between_wav_and_receipt_recovers_without_radio (test_download_recovery.RecoveryTests.test_crash_between_wav_and_receipt_recovers_without_radio) ... ok
test_invalid_json_is_preserved_and_rejected (test_download_recovery.RecoveryTests.test_invalid_json_is_preserved_and_rejected) ... ok
test_metadata_cannot_claim_a_different_capture (test_download_recovery.RecoveryTests.test_metadata_cannot_claim_a_different_capture) ... ok
test_missing_wav_is_redownloaded_even_with_verified_receipt (test_download_recovery.RecoveryTests.test_missing_wav_is_redownloaded_even_with_verified_receipt) ... ok
test_second_sync_checks_local_audio_without_ble_read (test_download_recovery.RecoveryTests.test_second_sync_checks_local_audio_without_ble_read) ... ok
test_truncated_wav_is_not_trusted_from_header_or_receipt (test_download_recovery.RecoveryTests.test_truncated_wav_is_not_trusted_from_header_or_receipt) ... ok
test_corrupt_transfer_never_publishes_wav (test_protocol.DownloadTests.test_corrupt_transfer_never_publishes_wav) ... ok
test_resume_verifies_full_audio_and_writes_standard_wav (test_protocol.DownloadTests.test_resume_verifies_full_audio_and_writes_standard_wav) ... ok
test_chunk_corruption_is_rejected (test_protocol.ProtocolTests.test_chunk_corruption_is_rejected) ... ok
test_extractive_summary_does_not_invent_an_action (test_protocol.ProtocolTests.test_extractive_summary_does_not_invent_an_action) ... ok
test_invalid_metadata_is_rejected (test_protocol.ProtocolTests.test_invalid_metadata_is_rejected) ... ok
test_malformed_packets_rejected (test_protocol_v2.FramingTests.test_malformed_packets_rejected) ... ok
test_manifest_round_trip_and_unknown_time (test_protocol_v2.FramingTests.test_manifest_round_trip_and_unknown_time) ... ok
test_manifest_unknown_version_flags_or_truncation_rejected (test_protocol_v2.FramingTests.test_manifest_unknown_version_flags_or_truncation_rejected) ... ok
test_packet_checksum_covers_header_and_payload (test_protocol_v2.FramingTests.test_packet_checksum_covers_header_and_payload) ... ok
test_receipt_wire_round_trip_and_unsupported_flags (test_protocol_v2.FramingTests.test_receipt_wire_round_trip_and_unsupported_flags) ... ok
test_audio_and_bookmarks_share_contiguous_archive (test_protocol_v2.ReceiverTests.test_audio_and_bookmarks_share_contiguous_archive) ... ok
test_committed_audio_survives_restart_and_lost_ack (test_protocol_v2.ReceiverTests.test_committed_audio_survives_restart_and_lost_ack) ... ok
test_conflicting_replay_does_not_replace_original (test_protocol_v2.ReceiverTests.test_conflicting_replay_does_not_replace_original) ... ok
test_failed_sql_write_cannot_return_receipt (test_protocol_v2.ReceiverTests.test_failed_sql_write_cannot_return_receipt) ... ok
test_final_seal_verifies_complete_identity_counts_and_digest (test_protocol_v2.ReceiverTests.test_final_seal_verifies_complete_identity_counts_and_digest) ... ok
test_gap_offset_future_bookmark_and_pcm_length_fail_closed (test_protocol_v2.ReceiverTests.test_gap_offset_future_bookmark_and_pcm_length_fail_closed) ... ok
test_identity_separates_devices_and_refuses_metadata_rebinding (test_protocol_v2.ReceiverTests.test_identity_separates_devices_and_refuses_metadata_rebinding) ... ok
test_live_corruption_prevents_fresh_and_replayed_ack (test_protocol_v2.ReceiverTests.test_live_corruption_prevents_fresh_and_replayed_ack) ... ok
test_live_missing_prefix_prevents_new_ack (test_protocol_v2.ReceiverTests.test_live_missing_prefix_prevents_new_ack) ... ok
test_missing_saved_packet_cannot_be_covered_by_metadata_receipt (test_protocol_v2.ReceiverTests.test_missing_saved_packet_cannot_be_covered_by_metadata_receipt) ... ok
test_process_exit_before_commit_does_not_ack_or_publish_packet (test_protocol_v2.ReceiverTests.test_process_exit_before_commit_does_not_ack_or_publish_packet) ... ok
test_quota_failure_keeps_committed_prefix (test_protocol_v2.ReceiverTests.test_quota_failure_keeps_committed_prefix) ... ok
test_reconnect_rechecks_saved_bytes_before_acknowledging (test_protocol_v2.ReceiverTests.test_reconnect_rechecks_saved_bytes_before_acknowledging) ... ok
test_replay_returns_current_prefix_without_duplicate_data (test_protocol_v2.ReceiverTests.test_replay_returns_current_prefix_without_duplicate_data) ... ok
test_active_capture_does_not_download_or_process (test_sync.SyncTests.test_active_capture_does_not_download_or_process) ... ok
test_all_downloads_and_disconnect_precede_any_processing (test_sync.SyncTests.test_all_downloads_and_disconnect_precede_any_processing) ... ok
test_disconnect_failure_preserves_wavs_without_starting_processing (test_sync.SyncTests.test_disconnect_failure_preserves_wavs_without_starting_processing) ... ok
test_failed_download_does_not_block_later_verified_recording (test_sync.SyncTests.test_failed_download_does_not_block_later_verified_recording) ... ok
test_later_notes_continue_after_each_processing_stage_failure (test_sync.SyncTests.test_later_notes_continue_after_each_processing_stage_failure) ... ok
test_plain_sync_never_transcribes_refines_uploads_or_deletes (test_sync.SyncTests.test_plain_sync_never_transcribes_refines_uploads_or_deletes) ... ok
test_upload_requires_explicit_transcription_before_connecting (test_sync.SyncTests.test_upload_requires_explicit_transcription_before_connecting) ... ok
test_verified_downloads_are_processed_after_later_transfer_interruption (test_sync.SyncTests.test_verified_downloads_are_processed_after_later_transfer_interruption) ... ok
test_requires_confirmation_and_empty_idle_device (test_upload.MaintenanceTests.test_requires_confirmation_and_empty_idle_device) ... ok
test_sends_exact_magic_with_extended_timeout (test_upload.MaintenanceTests.test_sends_exact_magic_with_extended_timeout) ... ok
test_explicit_local_http_upload_and_redirect_refusal (test_upload.UploadTests.test_explicit_local_http_upload_and_redirect_refusal) ... ok
test_missing_audio_uses_canonical_note_hash (test_upload.UploadTests.test_missing_audio_uses_canonical_note_hash) ... ok
test_no_network_without_explicit_configuration (test_upload.UploadTests.test_no_network_without_explicit_configuration) ... ok
test_rejects_unsafe_urls_and_note_structure (test_upload.UploadTests.test_rejects_unsafe_urls_and_note_structure) ... ok
test_stable_source_audio_hash_and_schema (test_upload.UploadTests.test_stable_source_audio_hash_and_schema) ... ok

----------------------------------------------------------------------
Ran 47 tests in 4.925s

OK
Exit code: 0
