Avinash1286/pendent/companion/tests/assets/sample.md

# Remember to send the design files to Maya on

- Remember to send the design files to Maya on Friday.
- The new pendant should feel comfortable and simple to use.

## Suggested actions

- [ ] Remember to send the design files to Maya on Friday.

## Transcript

[0.0s] Remember to send the design files to Maya on Friday. The new pendant should feel comfortable and simple to use.

---
extractive — original sentences, not an LLM summary
