Avinash1286/pendent/firmware/a04/verification/transfer-wire-golden.tsv

# name | kind | hex
device_id | context | 11111111111111111111111111111111
incarnation | context | a402030405060708090a0b0c0d0e0f10
final.hello | command | 01010100
final.hello | response | 0001010011111111111111111111111111111111a402030405060708090a0b0c0d0e0f1001000000010000020001
final.list | command | 01020200010000000000
final.list | response | 00020200010000000000415552330302010011111111111111111111111111111111ff88b7f46b5c9f419b3f35d0515d8fa5803e000040012800007d00000103000000000000000000001f4ee31e0200
final.select | command | 01030300ff88b7f46b5c9f419b3f35d0515d8fa5
final.select | response | 0003030001000000415552330302010011111111111111111111111111111111ff88b7f46b5c9f419b3f35d0515d8fa5803e000040012800007d00000103000000000000000000001f4ee31e41434b33030111111111111111111111111111111111ff88b7f46b5c9f419b3f35d0515d8fa57b010000766900000000000080d80100000000005c35876055bbd28894a2294cf704da293442c88385f94ee70fae891ca434e54afc37c3f7b090000000000000b090000000000000002a00000000000000
final.select | fragment23 | 010003000000c300000303000100000041555233
final.select | fragment23 | 010003000c00c300030201001111111111111111
final.select | fragment23 | 010003001800c3001111111111111111ff88b7f4
final.select | fragment23 | 010003002400c3006b5c9f419b3f35d0515d8fa5
final.select | fragment23 | 010003003000c300803e000040012800007d0000
final.select | fragment23 | 010003003c00c300010300000000000000000000
final.select | fragment23 | 010003004800c3001f4ee31e41434b3303011111
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
open.read | command | 010404000100000000000000000000008000
open.read | response | 00040400010000000000000000000000610041555233030201001111111111111111111111111111111124d4008368e06638e90b89d68d221fbd803e000040012800007d0000010300000000000000000000a096855f41465233030100000000000000000000000040010300b8fffea27c5444b7206c50
open.finish | command | 01052c01010000001a8f000000000000
open.finish | response | 00052c010100000041434b3303001111111111111111111111111111111124d4008368e06638e90b89d68d221fbd6d0100004c6900000000000000c7010000000000001cb88da352f158b76facb54b37721b99c248a9dc1d22538332a026668bf1355ca2e4141a8f000000000000012b00000000000000
open.read-eof | command | 01042d01010000001a8f0000000000000001
open.read-eof | response | 00042d01010000001a8f000000000000000000000000
open.cancel | command | 01062e0101000000
open.cancel | response | 00062e0101000000
