Avinash1286/pendent/film/aura-launch/qa/a03-hero-motion.png

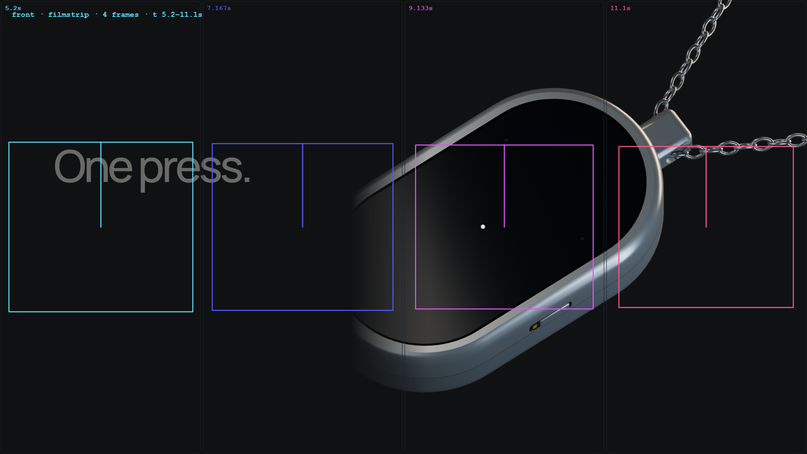
film/aura-launch/qa/a03-hero-motion.png
