Avinash1286/pendent/film/aura-launch/qa/a03-preflight/contact-sheet.jpg

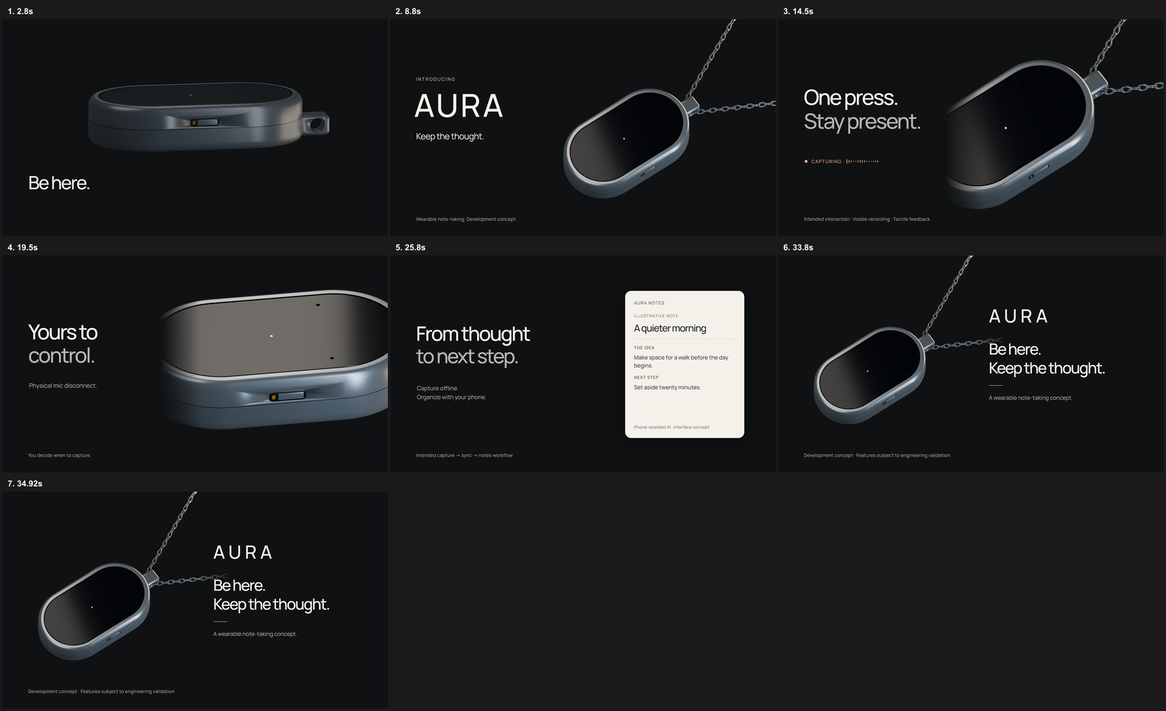
film/aura-launch/qa/a03-preflight/contact-sheet.jpg
