Avinash1286/pendent/film/aura-launch/qa/a03-preflight/frame-00-at-2.8s.png

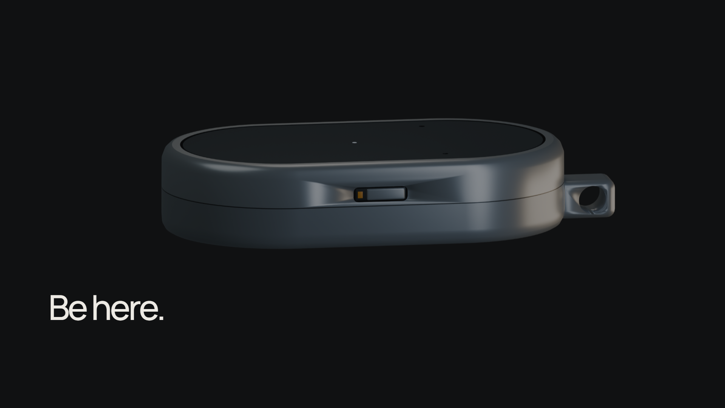
film/aura-launch/qa/a03-preflight/frame-00-at-2.8s.png
