Avinash1286/pendent/film/aura-launch/qa/a03-preflight/frame-02-at-14.5s.png

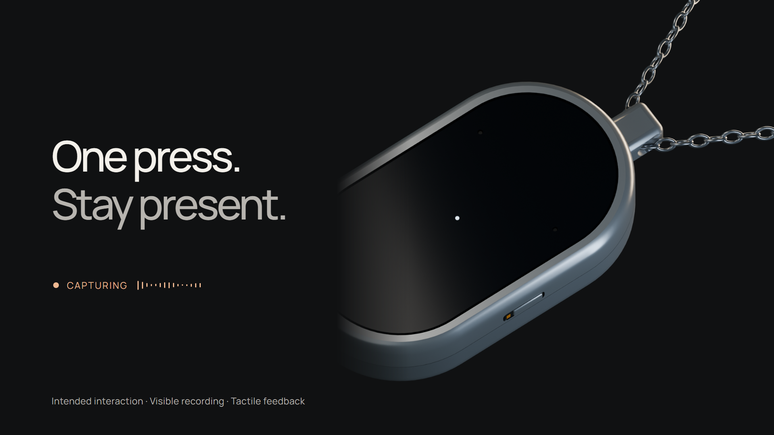
film/aura-launch/qa/a03-preflight/frame-02-at-14.5s.png
