Avinash1286/pendent/film/aura-launch/qa/a03-preflight/frame-04-at-25.8s.png

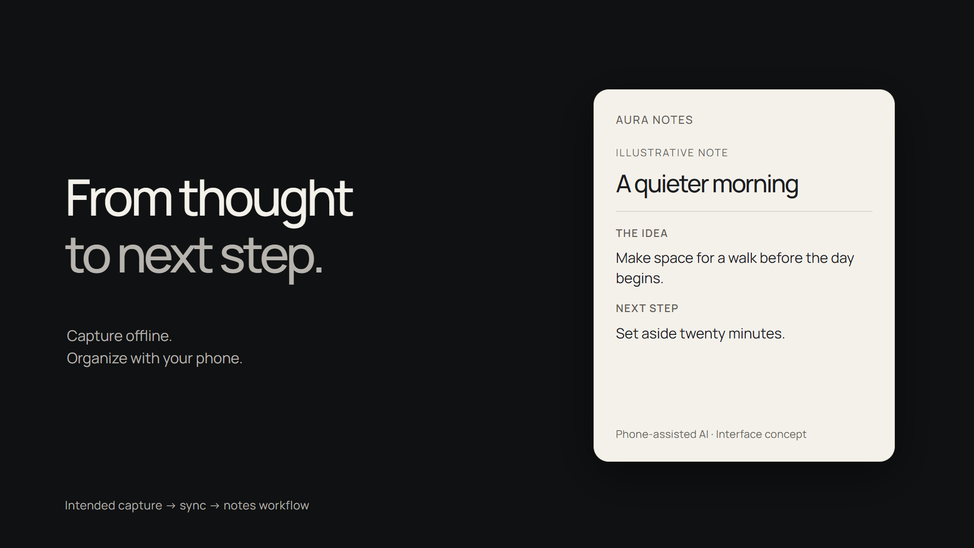
film/aura-launch/qa/a03-preflight/frame-04-at-25.8s.png
