Avinash1286/pendent/film/aura-launch/qa/hero-motion.png

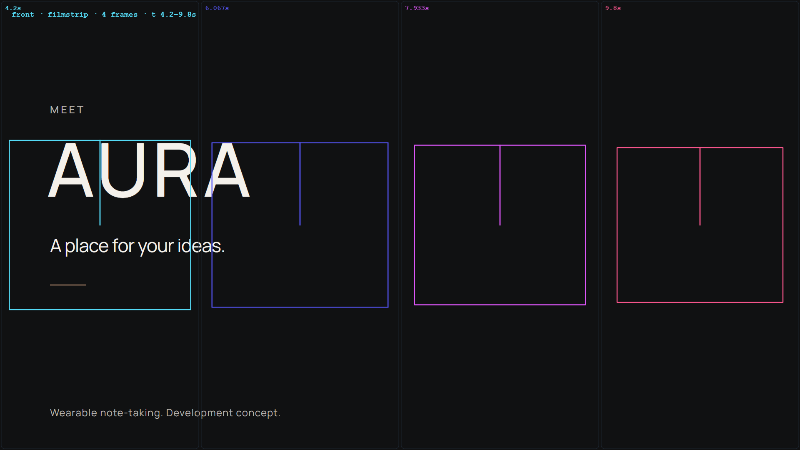
film/aura-launch/qa/hero-motion.png
