Avinash1286/pendent/film/aura-launch/qa/preflight-frames/contact-sheet.jpg

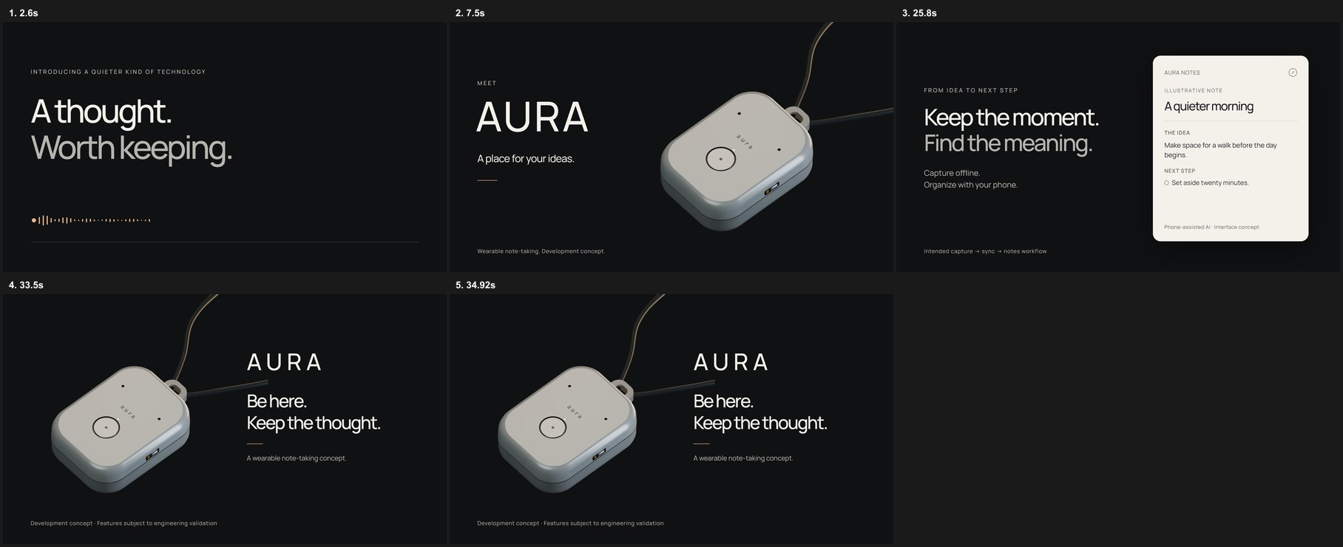
film/aura-launch/qa/preflight-frames/contact-sheet.jpg
