Avinash1286/pendent/film/aura-launch/qa/preflight-frames/frame-01-at-7.5s.png

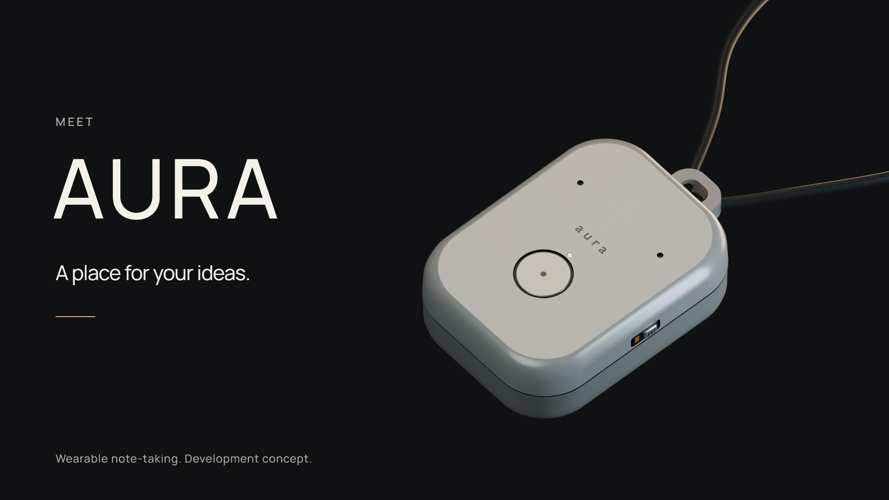
film/aura-launch/qa/preflight-frames/frame-01-at-7.5s.png
