Avinash1286/pendent/film/aura-launch/qa/preflight-frames/frame-03-at-33.5s.png

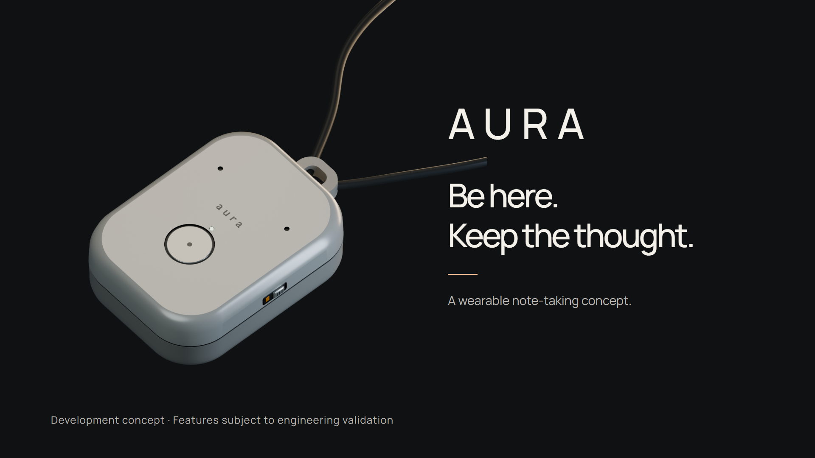
film/aura-launch/qa/preflight-frames/frame-03-at-33.5s.png
