Avinash1286/pendent/film/aura-launch/qa/transitions-final.jpg

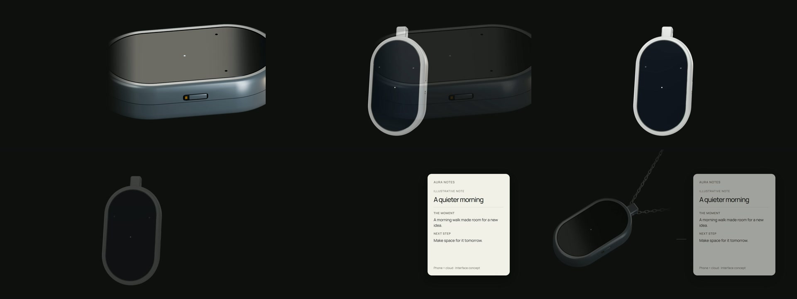
film/aura-launch/qa/transitions-final.jpg
