Avinash1286/pendent/mobile/android/verification/android-context-editor.png

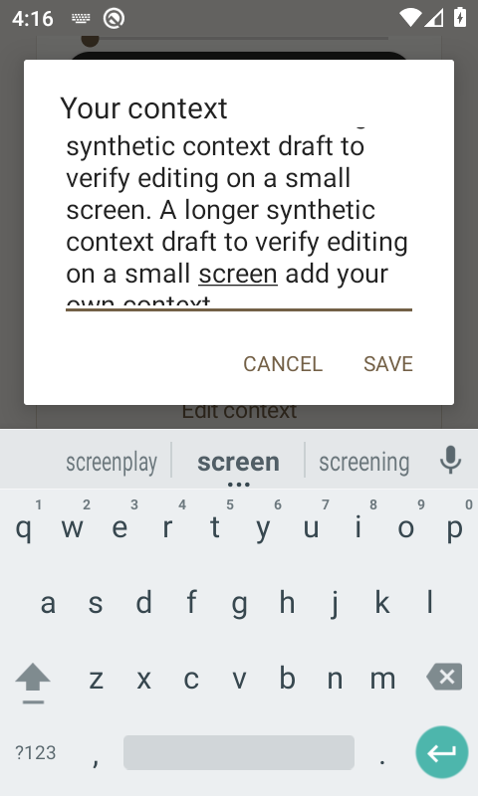
mobile/android/verification/android-context-editor.png
