Avinash1286/pendent/mobile/android/verification/android-library-empty.png

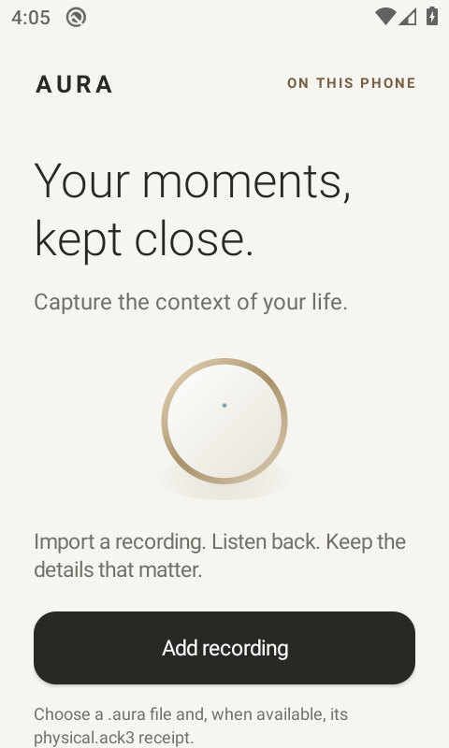
mobile/android/verification/android-library-empty.png
