Avinash1286/pendent/hardware/output/route-debug.png

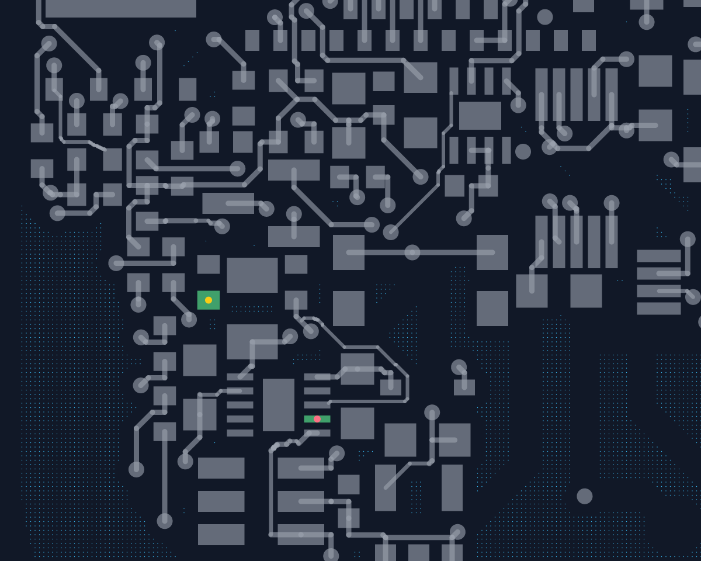
hardware/output/route-debug.png
